rh1tech/frank-archive/minifrank_rm1p2/3D/raspberry pi pico with contacts.step

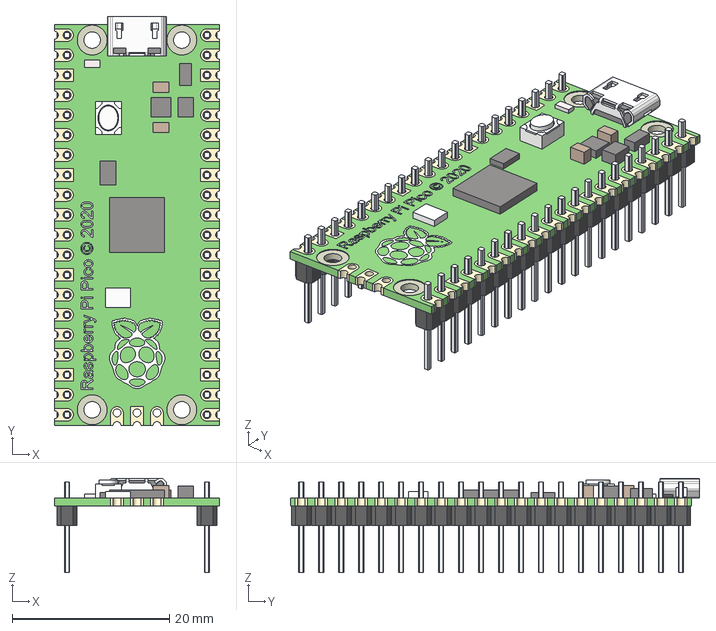
[picture p18: CAD file, 2026-05-06]
minifrank_rm1p2/3D/raspberry pi pico with contacts.step
21.0 x 52.0 x 12.0 mm
ножка x 20
ножка v3(Mirror) x 20
