rh1tech/frank-archive/turbofrank_m1p1/3d/MAX232CSE+.stp

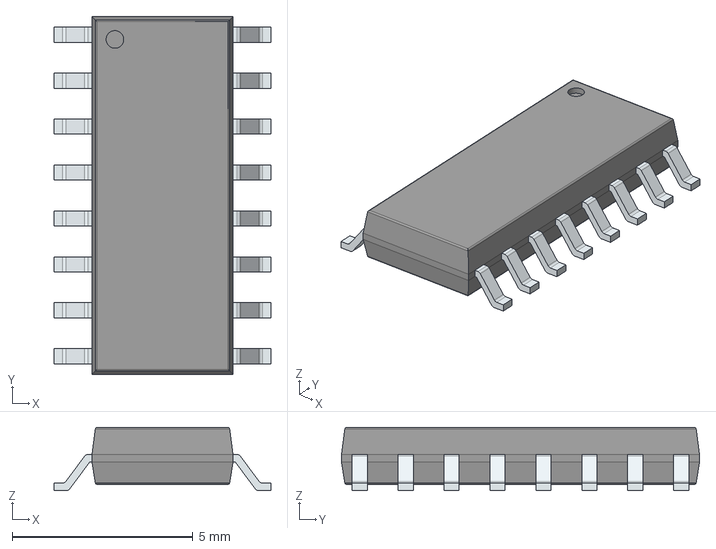
[picture p20: CAD file, 2026-05-06]
turbofrank_m1p1/3d/MAX232CSE+.stp
6.00 x 9.90 x 1.75 mm
PinsArrayLR
