rh1tech/frank-archive/turbofrank_m1p1/case/1_06/bottom.stl

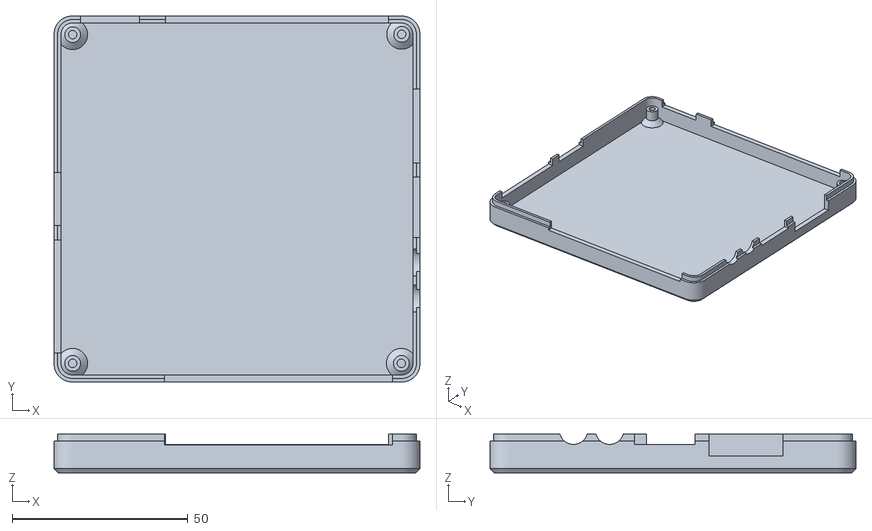
[picture p21: CAD file, 2026-05-07]
turbofrank_m1p1/case/1_06/bottom.stl
104.0 x 104.0 x 11.0
