rh1tech/frank-archive/turbofrank_m1p2/3d/USB1035-GF-P-0-B-B.stp

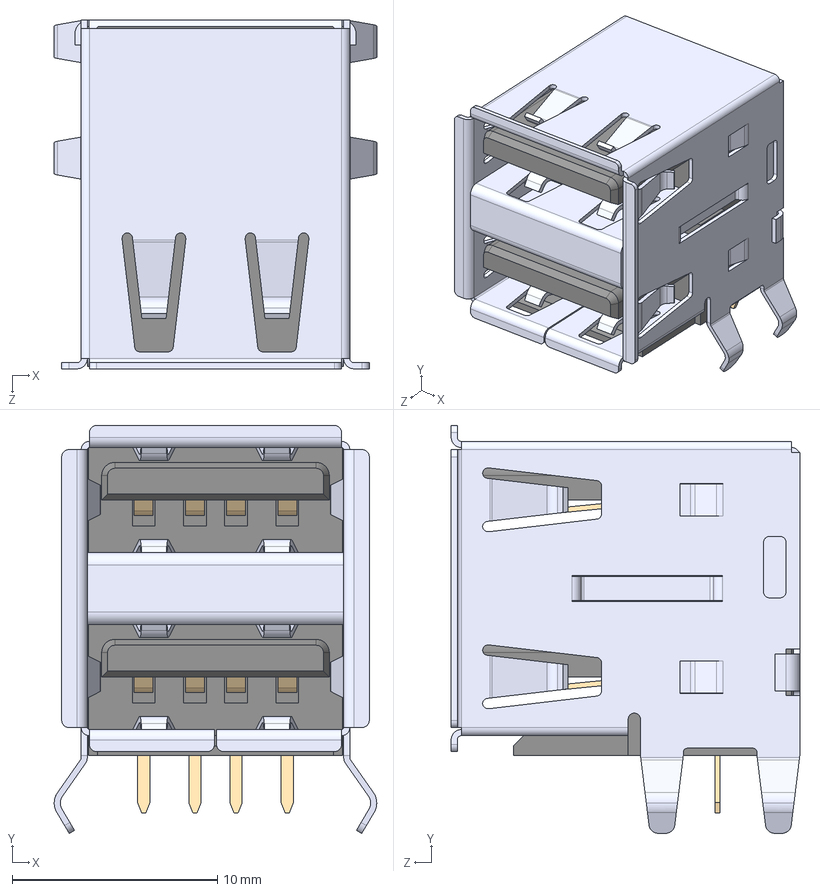
[picture p22: CAD file, 2026-05-06]
turbofrank_m1p2/3d/USB1035-GF-P-0-B-B.stp
15.7 x 19.9 x 17.0 mm
