rh1tech/frank-archive/turbofrank_m1p2/case/1_01/button.stl

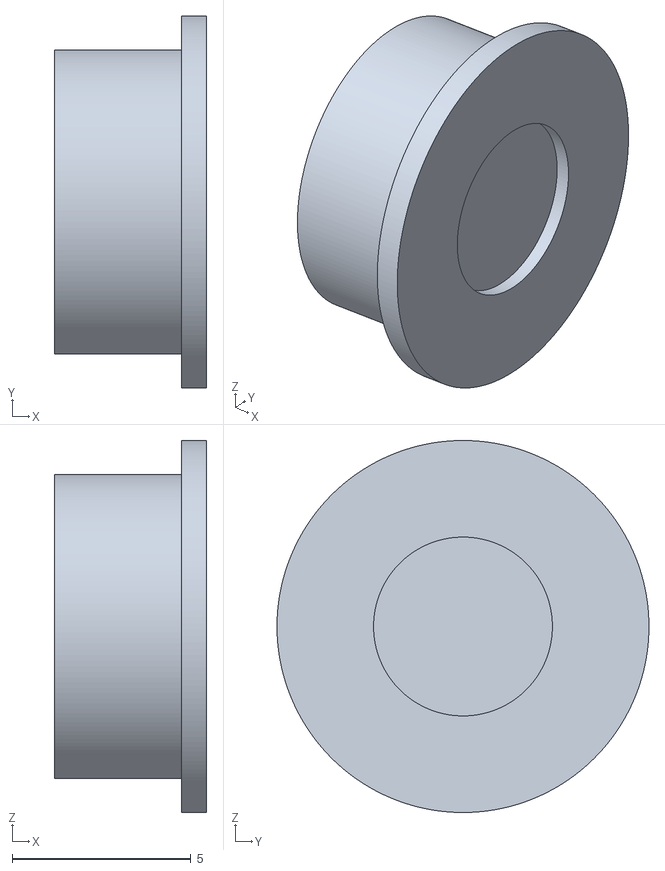
[picture p23: CAD file, 2026-05-07]
turbofrank_m1p2/case/1_01/button.stl
4.25 x 10.4 x 10.4
