rh1tech/frank-archive/usb2ps2/case/REV_1_0/top.stl

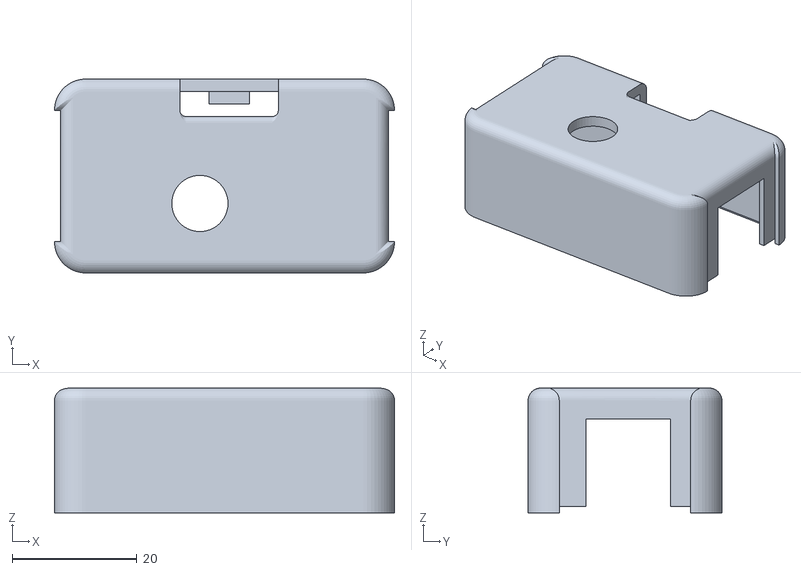
[picture p24: CAD file, 2026-05-07]
usb2ps2/case/REV_1_0/top.stl
54.4 x 31.1 x 20.0
