rh1tech/frank-archive/frank_fastbeta_m1/case/1_04/bottom_vga.stl

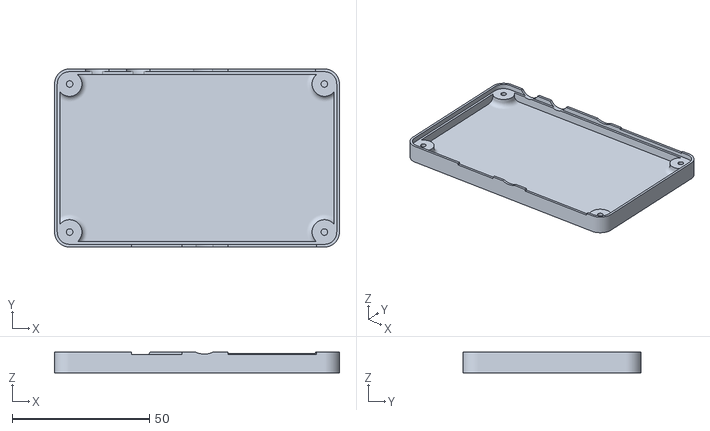
[picture p26: CAD file, 2026-05-07]
frank_fastbeta_m1/case/1_04/bottom_vga.stl
104.0 x 65.0 x 7.50
