rh1tech/frank-archive/frank_m1/3d/DS05-127-2-06BK-SMT-TR.stp

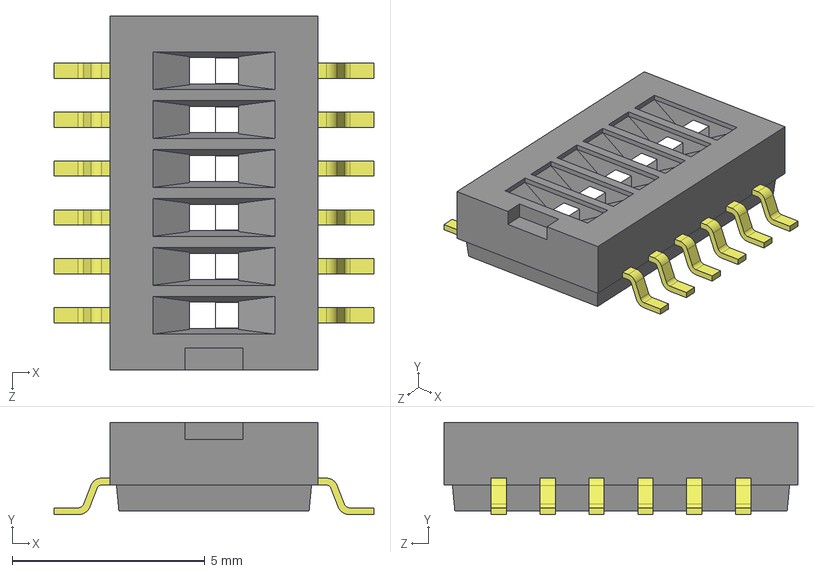
[picture p27: CAD file, 2026-05-06]
frank_m1/3d/DS05-127-2-06BK-SMT-TR.stp
8.30 x 2.40 x 9.19 mm
