rh1tech/frank-archive/hdmi2vga/3d/CUI_DEVICES_RCJ-013.step

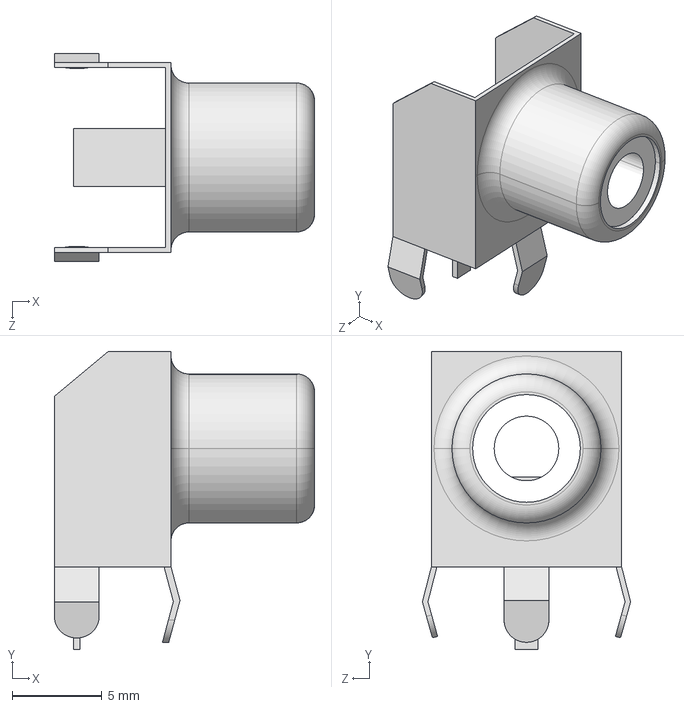
[picture p28: CAD file, 2026-05-06]
hdmi2vga/3d/CUI_DEVICES_RCJ-013.step
14.5 x 16.6 x 11.6 mm
