rh1tech/frank-archive/hdmi2vga/case/2_02/top.stl

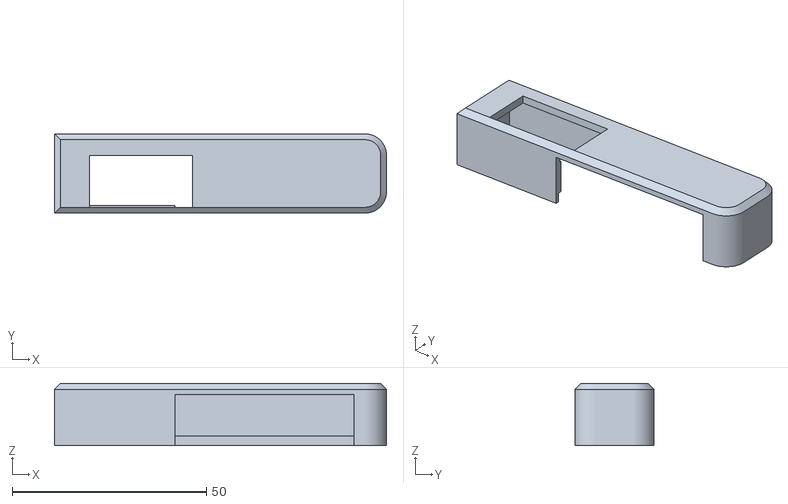
[picture p29: CAD file, 2026-05-07]
hdmi2vga/case/2_02/top.stl
85.5 x 20.4 x 16.0
