rh1tech/frank-archive/hdmi2vga/case/2_03/top.stl

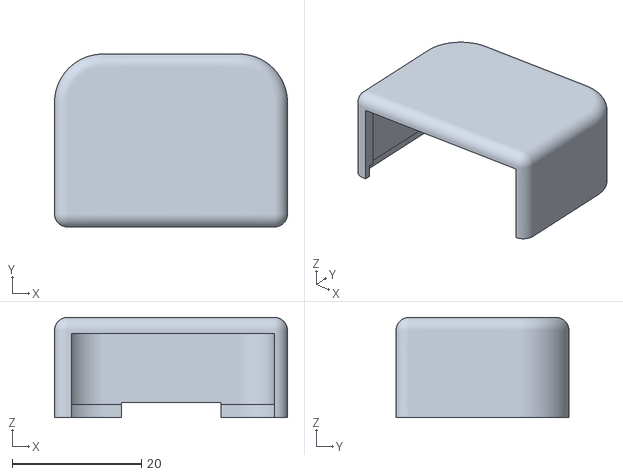
[picture p30: CAD file, 2026-05-07]
hdmi2vga/case/2_03/top.stl
36.0 x 26.8 x 15.5
