rh1tech/frank-archive/microfrank_rm1p2/3D/PICO Clone-Black .step

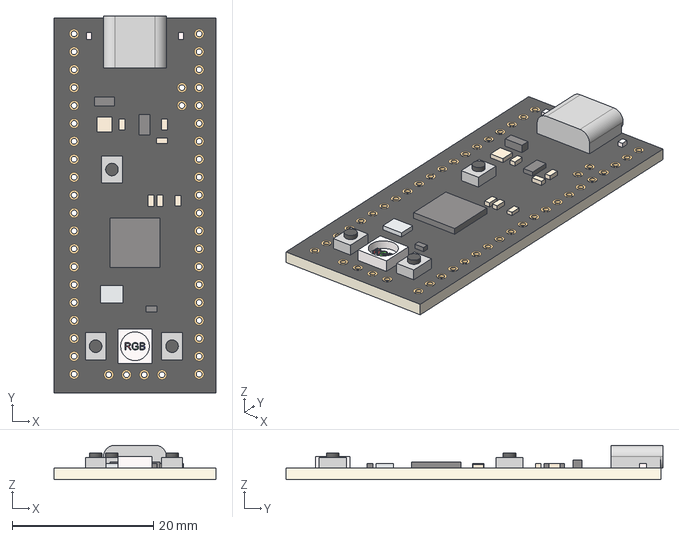
[picture p31: CAD file, 2026-05-06]
microfrank_rm1p2/3D/PICO Clone-Black .step
22.9 x 53.3 x 4.88 mm
