rh1tech/frank-archive/microfrank_rm1p2/CASE/1_01/logo.stl

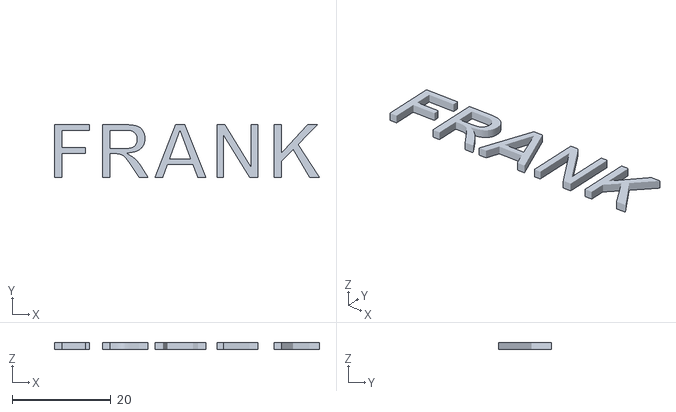
[picture p32: CAD file, 2026-05-06]
microfrank_rm1p2/CASE/1_01/logo.stl
53.6 x 10.7 x 1.50
