rh1tech/frank-archive/microfrank_rm1p2u/3D/DS04-254-2-01BK-SMT.step

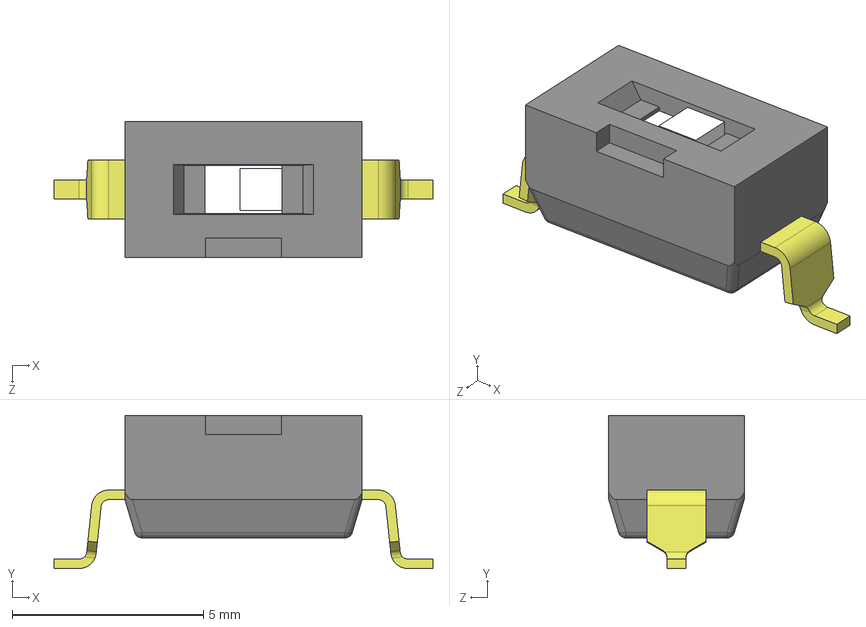
[picture p33: CAD file, 2026-05-06]
microfrank_rm1p2u/3D/DS04-254-2-01BK-SMT.step
9.90 x 4.00 x 3.54 mm
