rh1tech/frank-archive/minifrank_m1/CASE/1_01/cover.stl

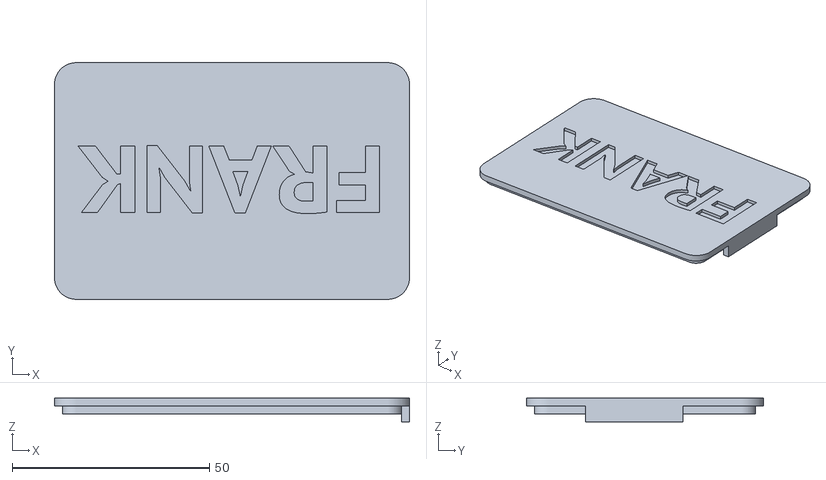
[picture p34: CAD file, 2026-05-06]
minifrank_m1/CASE/1_01/cover.stl
90.0 x 60.0 x 6.00
