rh1tech/frank-archive/minifrank_rm1p2/CASE/1_01/middle.stl

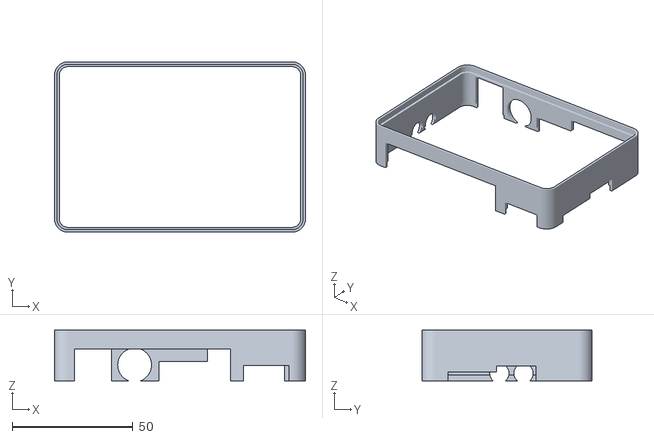
[picture p35: CAD file, 2026-05-06]
minifrank_rm1p2/CASE/1_01/middle.stl
104.0 x 70.5 x 21.0
