rh1tech/frank-archive/minifrank_rm1p2h/3D/Ts-1233_1.5.stp

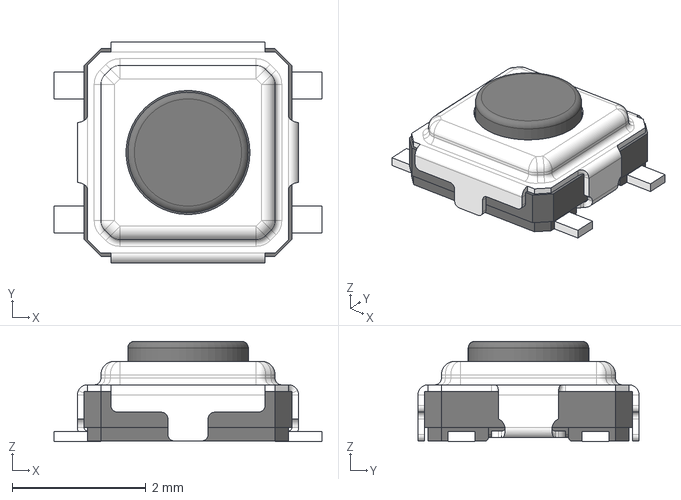
[picture p36: CAD file, 2026-05-06]
minifrank_rm1p2h/3D/Ts-1233_1.5.stp
4.00 x 3.30 x 1.50 mm
