rh1tech/frank-archive/turbofrank_m1p1/3d/FHU-1x9.step

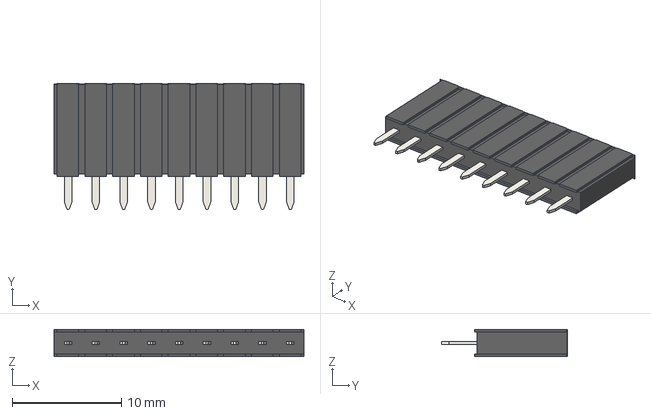
[picture p37: CAD file, 2026-05-06]
turbofrank_m1p1/3d/FHU-1x9.step
22.9 x 11.5 x 2.50 mm
