rh1tech/frank-archive/turbofrank_m1p2/case/1_01/middle.stl

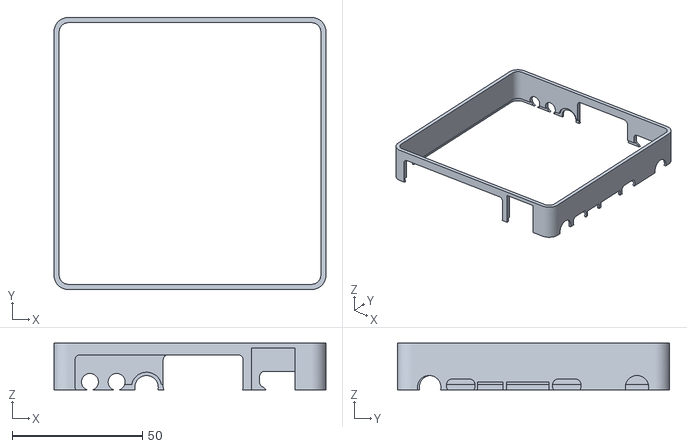
[picture p39: CAD file, 2026-05-07]
turbofrank_m1p2/case/1_01/middle.stl
104.5 x 104.5 x 18.0
