rh1tech/frank-archive/usb2ps2/3d/Mini-DIN-6P.step

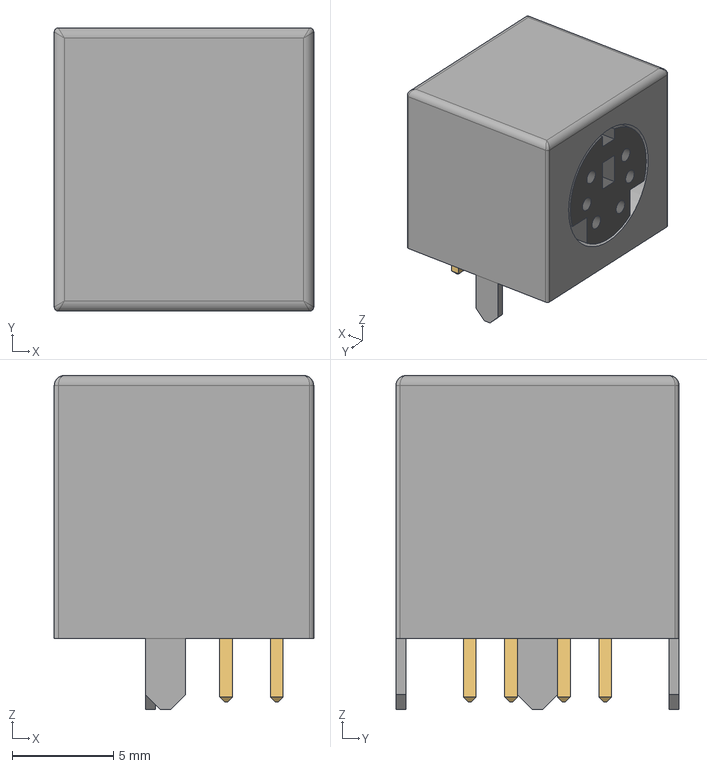
[picture p40: CAD file, 2026-05-06]
usb2ps2/3d/Mini-DIN-6P.step
12.8 x 14.0 x 16.5 mm
