rh1tech/frank-archive/usb2ps2/case/REV_1_0/bottom.stl

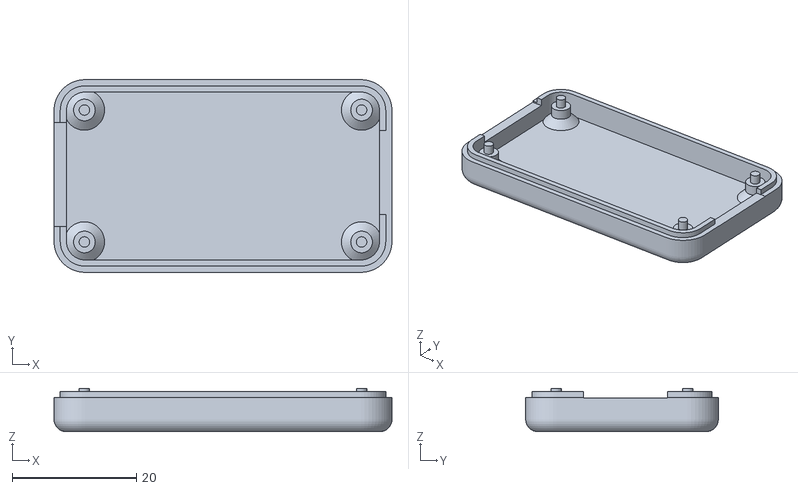
[picture p41: CAD file, 2026-05-07]
usb2ps2/case/REV_1_0/bottom.stl
54.4 x 31.1 x 7.00
