rh1tech/frank-archive/frank_m1/3d/CD4069UBM.stp

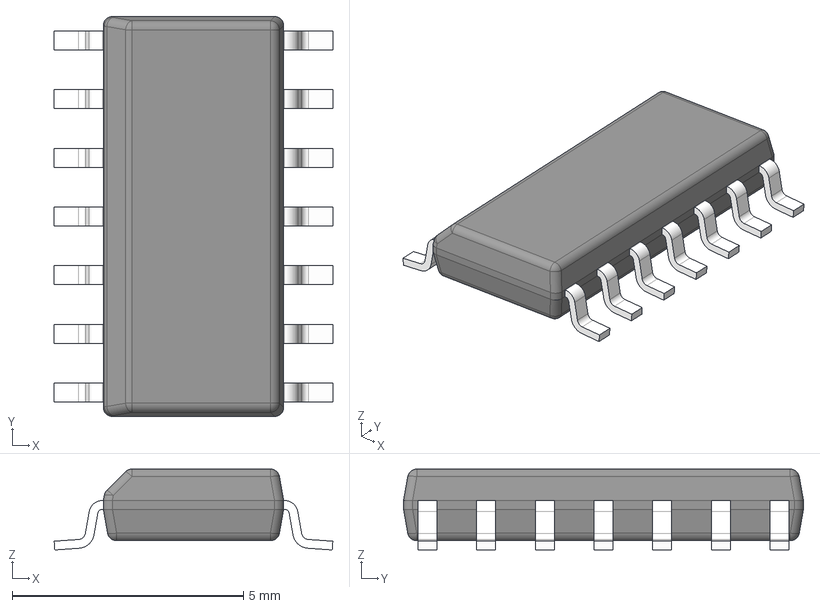
[picture p42: CAD file, 2026-05-06]
frank_m1/3d/CD4069UBM.stp
6.03 x 8.65 x 1.75 mm
BODY-SO
LEAD-SO x 14
PIN1-ID
