rh1tech/frank-archive/frank_rm1p2/3D/W25Q128JVSIQ.stp

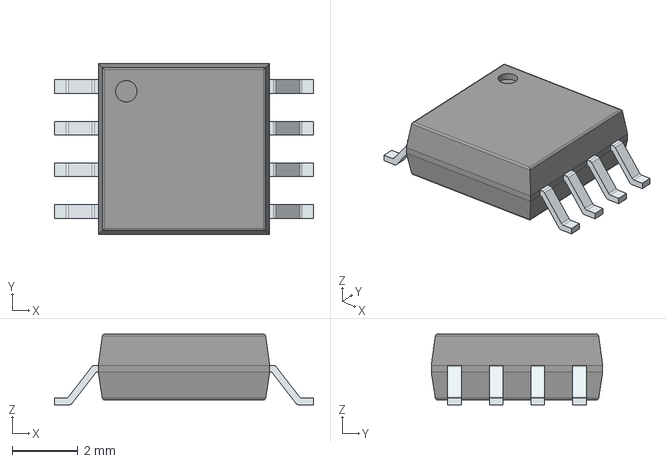
[picture p43: CAD file, 2026-05-06]
frank_rm1p2/3D/W25Q128JVSIQ.stp
7.90 x 5.23 x 2.16 mm
PinsArrayLR
