rh1tech/frank-archive/frank_rm1p2/CASE/1_01/top.stl

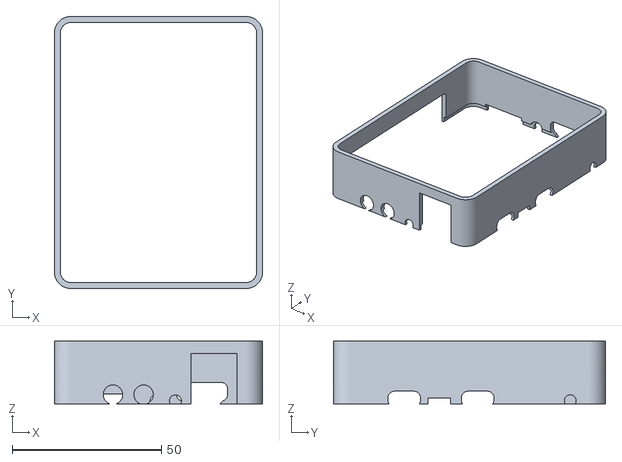
[picture p44: CAD file, 2026-05-06]
frank_rm1p2/CASE/1_01/top.stl
69.7 x 91.0 x 21.0
