rh1tech/frank-archive/microfrank_rm1p2/CASE/1_01/bottom.stl

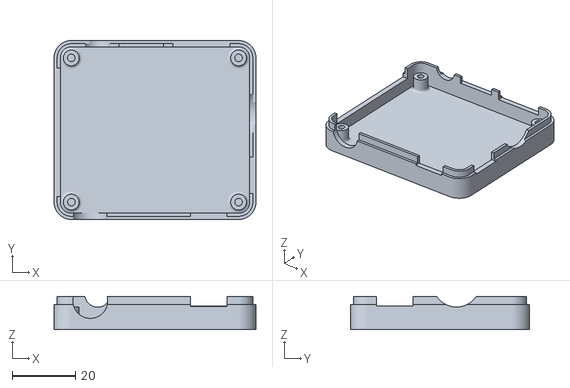
[picture p45: CAD file, 2026-05-06]
microfrank_rm1p2/CASE/1_01/bottom.stl
63.8 x 56.5 x 10.5
