rh1tech/frank-archive/minifrank_m1/CASE/1_01/text.stl

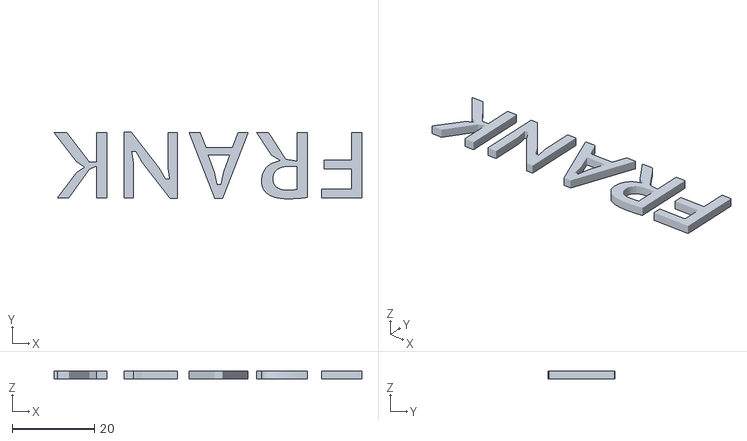
[picture p46: CAD file, 2026-05-06]
minifrank_m1/CASE/1_01/text.stl
74.9 x 16.2 x 2.00
