rh1tech/frank-archive/minifrank_rm1p2h/3D/QFN-48_7x7.step

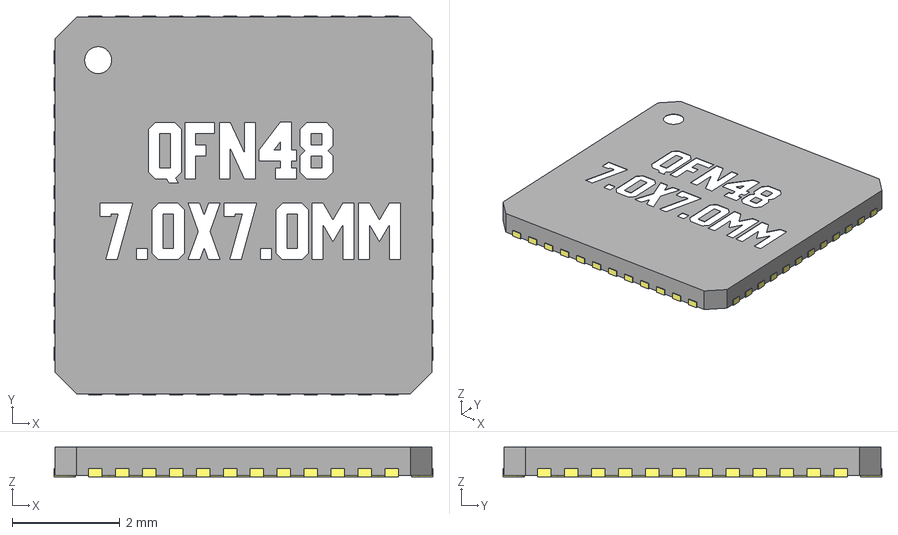
[picture p48: CAD file, 2026-05-06]
minifrank_rm1p2h/3D/QFN-48_7x7.step
7.04 x 7.04 x 0.55 mm
TxT
