rh1tech/frank-archive/tinyfrank_rm1p1/3D/SJ1-3535NG.stp

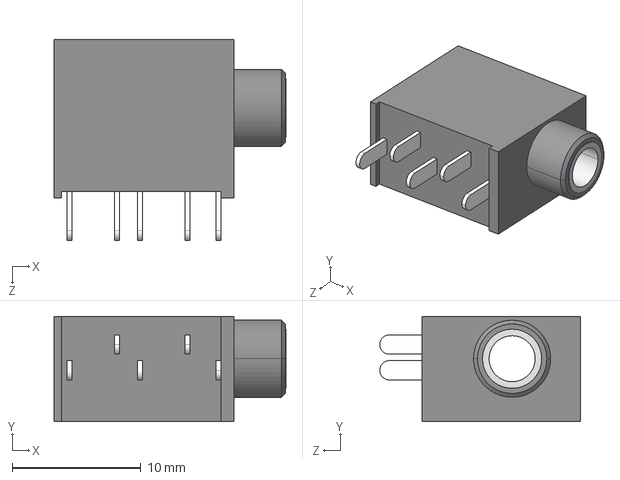
[picture p49: CAD file, 2026-05-06]
tinyfrank_rm1p1/3D/SJ1-3535NG.stp
18.1 x 8.20 x 15.6 mm
