rh1tech/frank-archive/turbofrank_m1p1/3d/PJ320D.STEP

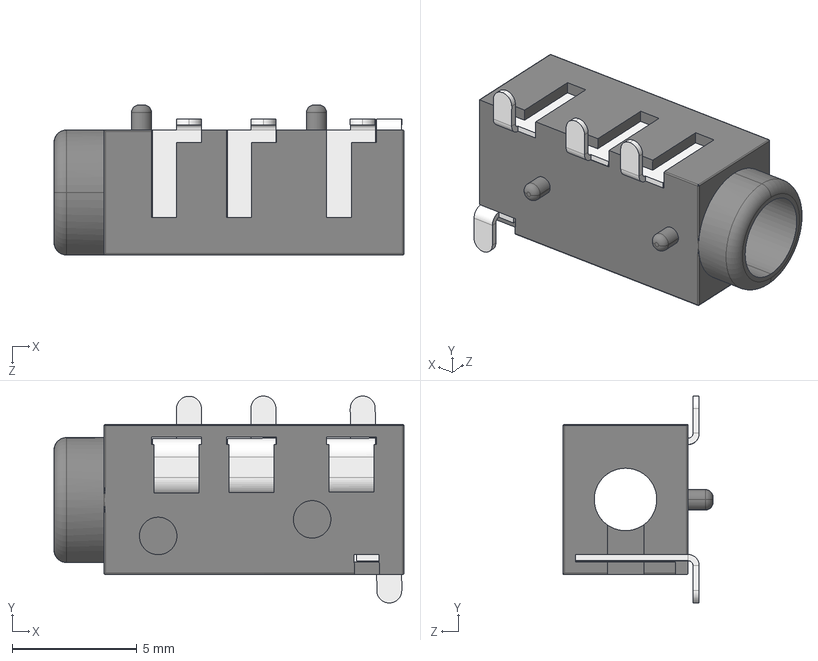
[picture p50: CAD file, 2026-05-06]
turbofrank_m1p1/3d/PJ320D.STEP
14.0 x 8.28 x 6.00 mm
PJ320A
PJ320D-Pin x 3
PJ320D-Pin-B
