rh1tech/frank-archive/turbofrank_m1p2/3d/LQH2MCN100K02L.step

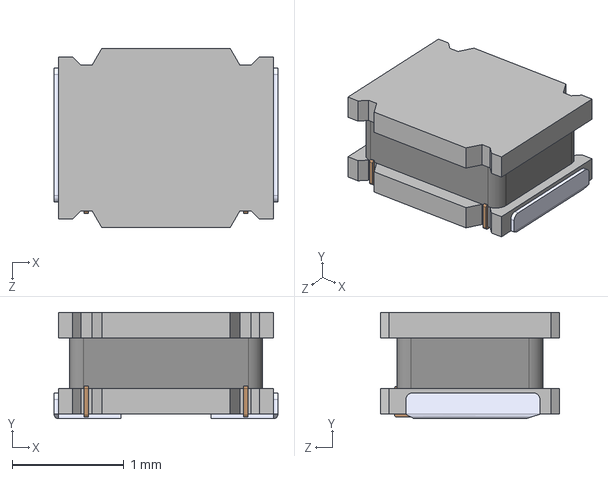
[picture p51: CAD file, 2026-05-06]
turbofrank_m1p2/3d/LQH2MCN100K02L.step
2.00 x 0.95 x 1.60 mm
