rh1tech/frank-archive/turbofrank_m1p2/case/1_01/bottom.stl

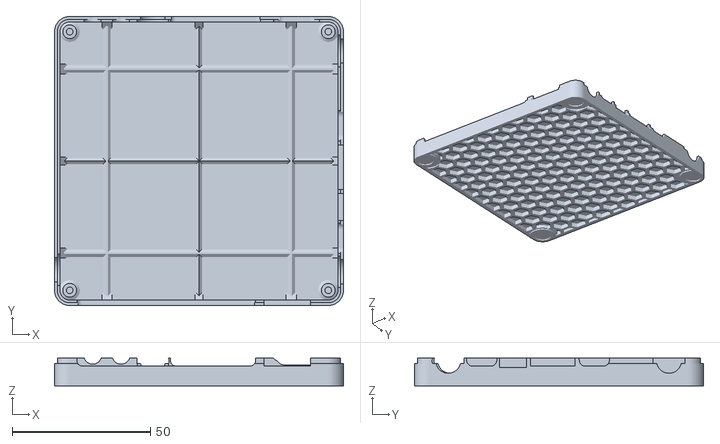
[picture p52: CAD file, 2026-05-07]
turbofrank_m1p2/case/1_01/bottom.stl
104.5 x 104.5 x 10.0
