rh1tech/frank-archive/frank_fastbeta_m1/case/1_04/body_hdmi.stl

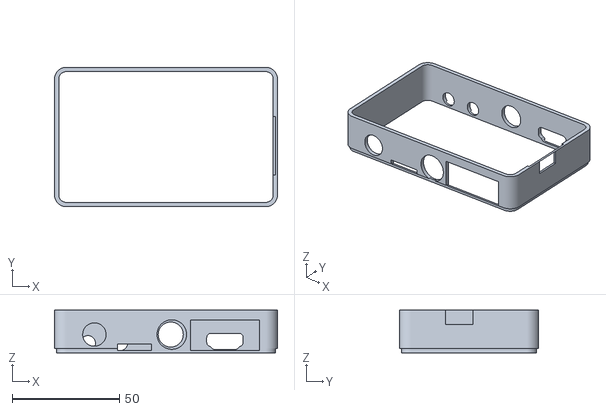
[picture p53: CAD file, 2026-05-07]
frank_fastbeta_m1/case/1_04/body_hdmi.stl
104.0 x 65.0 x 20.0
