rh1tech/frank-archive/frank_m1/3d/CDRH104RNP-150NC.stp

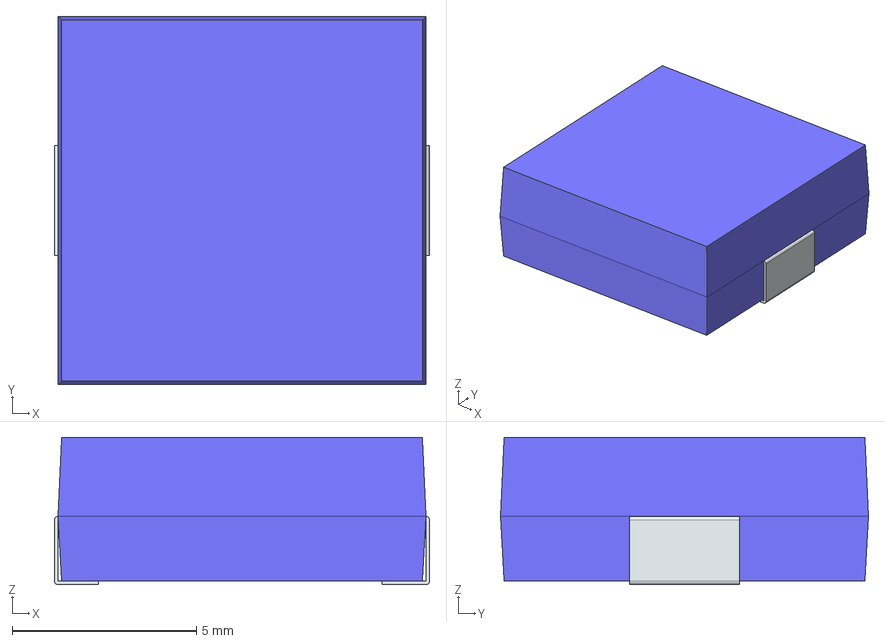
[picture p54: CAD file, 2026-05-06]
frank_m1/3d/CDRH104RNP-150NC.stp
10.2 x 10.0 x 4.00 mm
FilletPin1
FilletPin2
