rh1tech/frank-archive/microfrank_rm1p2/CASE/1_01/top.stl

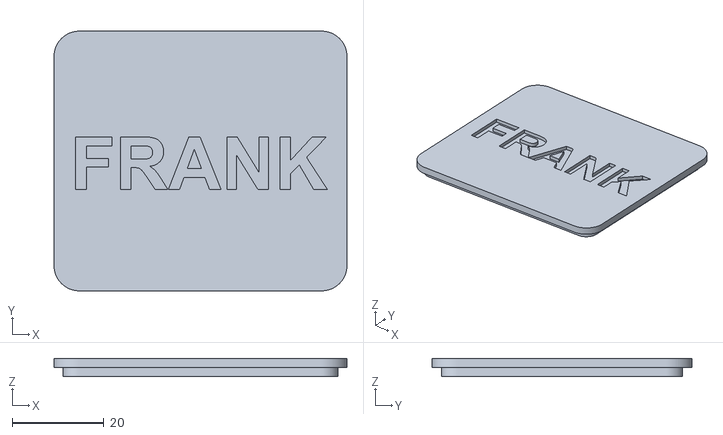
[picture p55: CAD file, 2026-05-06]
microfrank_rm1p2/CASE/1_01/top.stl
63.8 x 56.5 x 4.00
