rh1tech/frank-archive/minifrank_m1/3D/DSUB-15-HD_Male_Horizontal_P2.29x1.98mm_EdgePinOffset3.03mm_Housed_MountingHolesOffset4.94mm.step

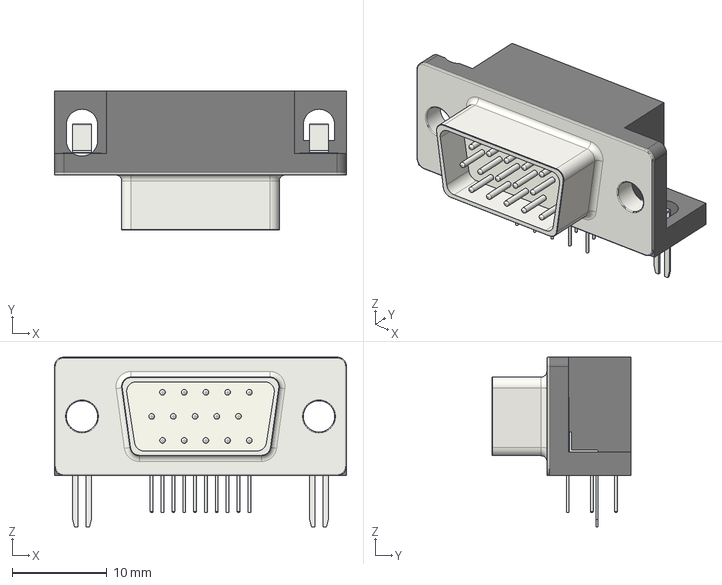
[picture p56: CAD file, 2026-05-06]
minifrank_m1/3D/DSUB-15-HD_Male_Horizontal_P2.29x1.98mm_EdgePinOffset3.03mm_Housed_MountingHolesOffset4.94mm.step
30.8 x 14.7 x 17.9 mm
