rh1tech/frank-archive/minifrank_m1/CASE/1_01/bottom.stl

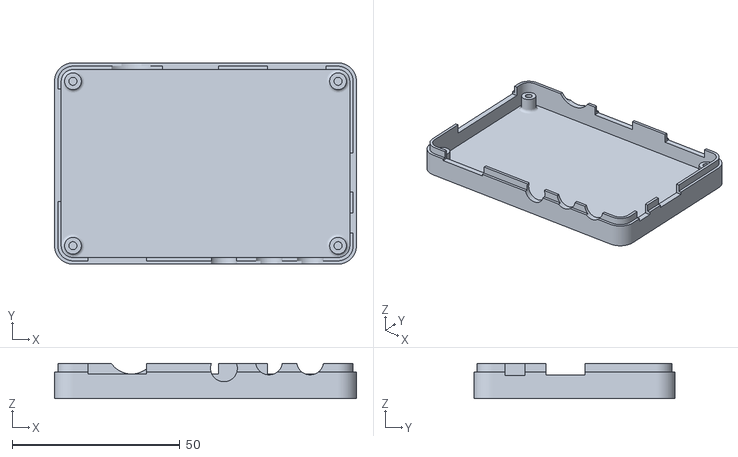
[picture p57: CAD file, 2026-05-06]
minifrank_m1/CASE/1_01/bottom.stl
90.0 x 60.0 x 10.5
