rh1tech/frank-archive/frank_fastbeta_m1/3d/MP1584EN-LF-Z.stp

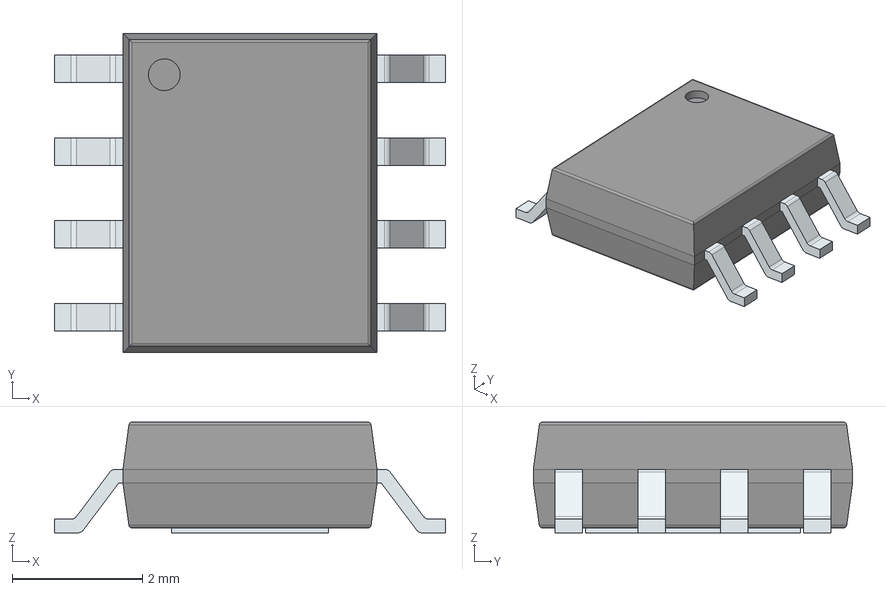
[picture p60: CAD file, 2026-05-06]
frank_fastbeta_m1/3d/MP1584EN-LF-Z.stp
6.00 x 4.90 x 1.70 mm
PinsArrayLR
ThermalPad
