rh1tech/frank-archive/frank_fastbeta_m1/case/1_04/cover.stl

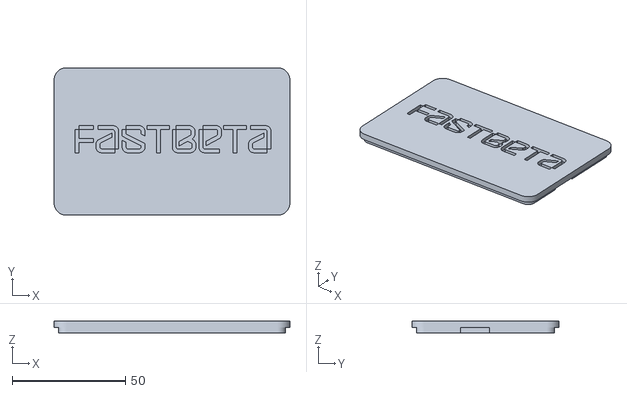
[picture p61: CAD file, 2026-05-07]
frank_fastbeta_m1/case/1_04/cover.stl
104.0 x 65.0 x 5.50
