rh1tech/frank-archive/turbofrank_m1p2/3d/TS3USB221RSER.stp

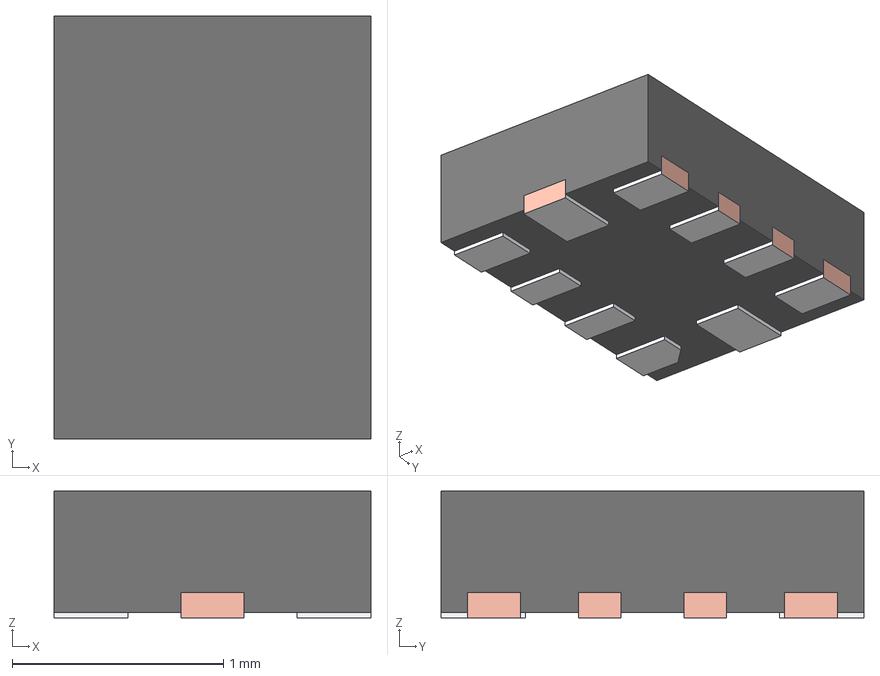
[picture p62: CAD file, 2026-05-06]
turbofrank_m1p2/3d/TS3USB221RSER.stp
1.50 x 2.00 x 0.6 mm
FRAME-RSE0010A
BODY-QFN
PIN1-ID
