rh1tech/frank-archive/frank_fastbeta_m1/3d/DC-005-5A-2.0.step

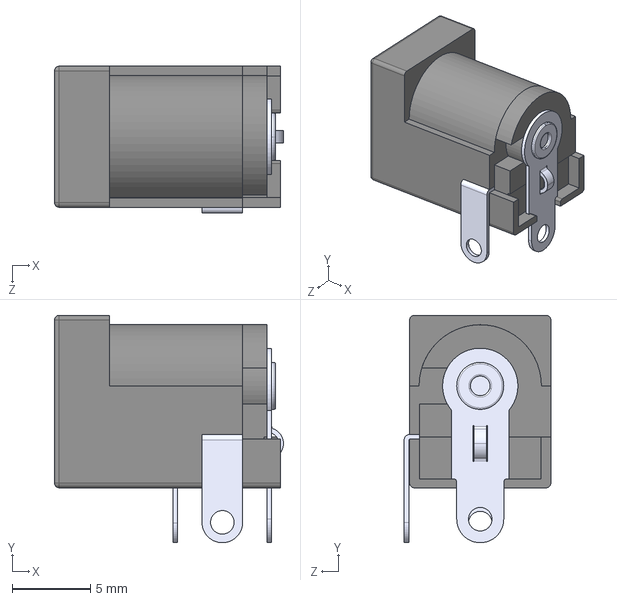
[picture p63: CAD file, 2026-05-06]
frank_fastbeta_m1/3d/DC-005-5A-2.0.step
14.6 x 14.5 x 9.35 mm
