rh1tech/frank-archive/minifrank_rm1p2h/3D/SN74CBT3257CDR.step

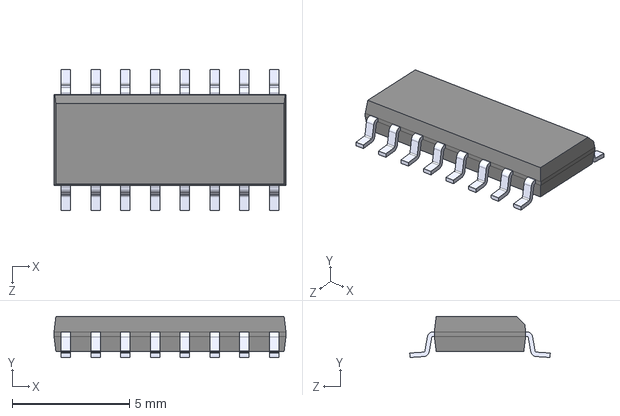
[picture p64: CAD file, 2026-05-06]
minifrank_rm1p2h/3D/SN74CBT3257CDR.step
9.90 x 1.75 x 6.00 mm
