rh1tech/frank-archive/tinyfrank_rm1p1/3D/W25Q32RVZPJQ.stp

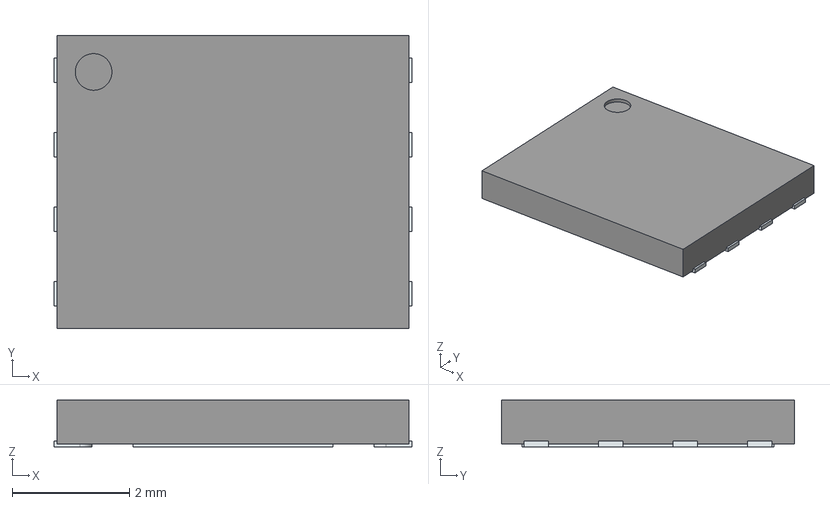
[picture p65: CAD file, 2026-05-06]
tinyfrank_rm1p1/3D/W25Q32RVZPJQ.stp
6.10 x 5.00 x 0.8 mm
ThermalPin
PinsArrayLR
