rh1tech/frank-archive/frank_fastbeta_m1/3d/FHU-1x20.step

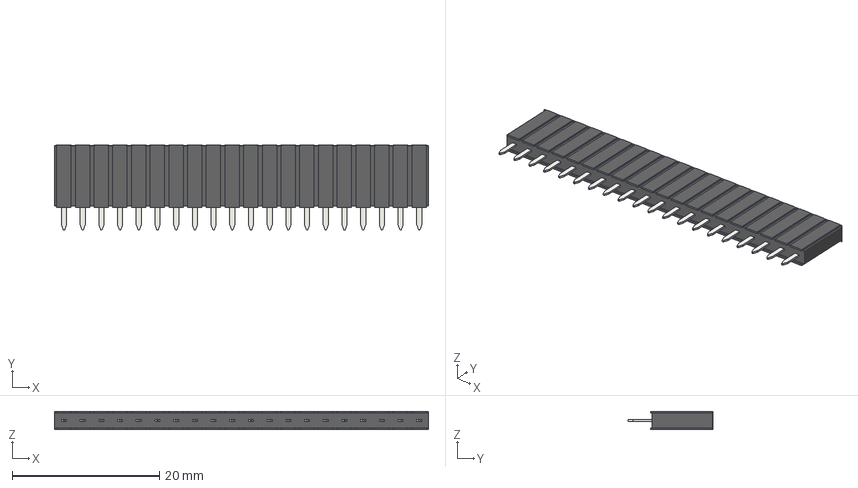
[picture p66: CAD file, 2026-05-06]
frank_fastbeta_m1/3d/FHU-1x20.step
50.8 x 11.5 x 2.50 mm
