rh1tech/frank-archive/turbofrank_m1p1/3d/1x5 Male Pin Header.STEP

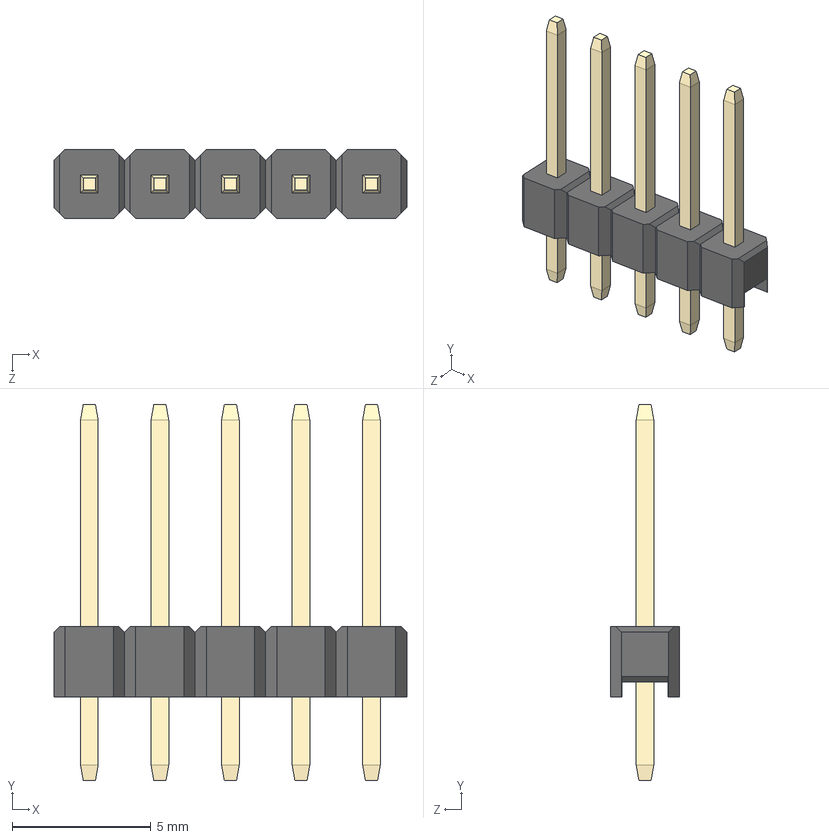
[picture p67: CAD file, 2026-05-06]
turbofrank_m1p1/3d/1x5 Male Pin Header.STEP
12.7 x 13.5 x 2.50 mm
