rh1tech/frank-archive/turbofrank_m1p2/3d/soic-14.stp

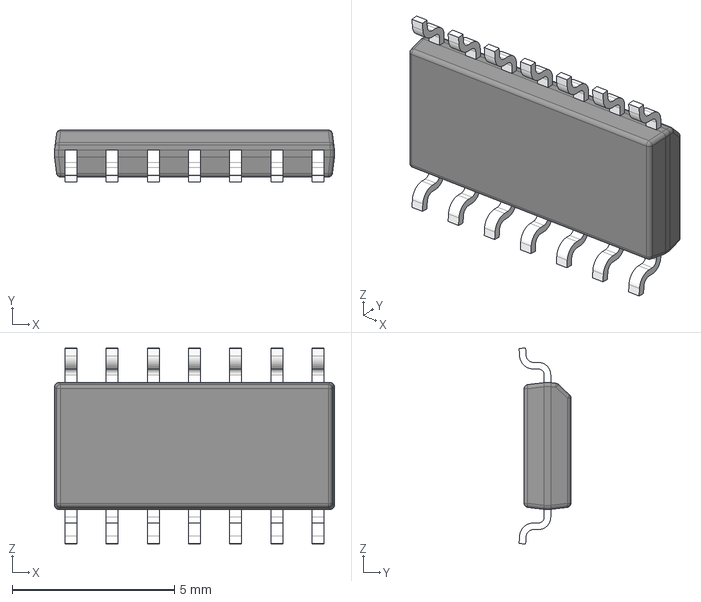
[picture p68: CAD file, 2026-05-06]
turbofrank_m1p2/3d/soic-14.stp
8.64 x 1.60 x 6.05 mm
BODY_M14A_20
LEAD_M14A_46 x 14
