rh1tech/frank-archive/frank_fastbeta_m1/3d/1x20 Male Pin Header.STEP

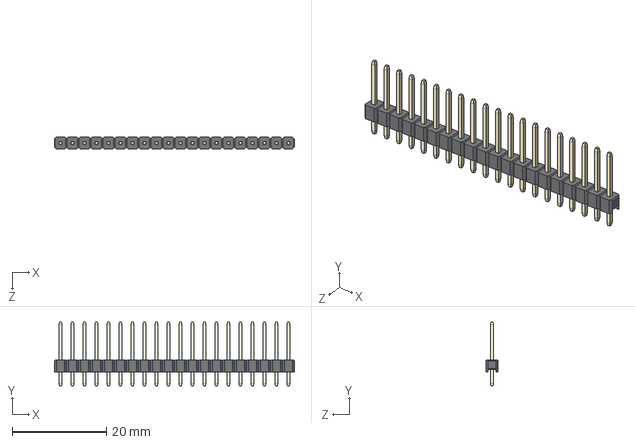
[picture p69: CAD file, 2026-05-06]
frank_fastbeta_m1/3d/1x20 Male Pin Header.STEP
50.8 x 13.5 x 2.50 mm
