rh1tech/frank-archive/frank_fastbeta_m1/3d/CD4069UBE.stp

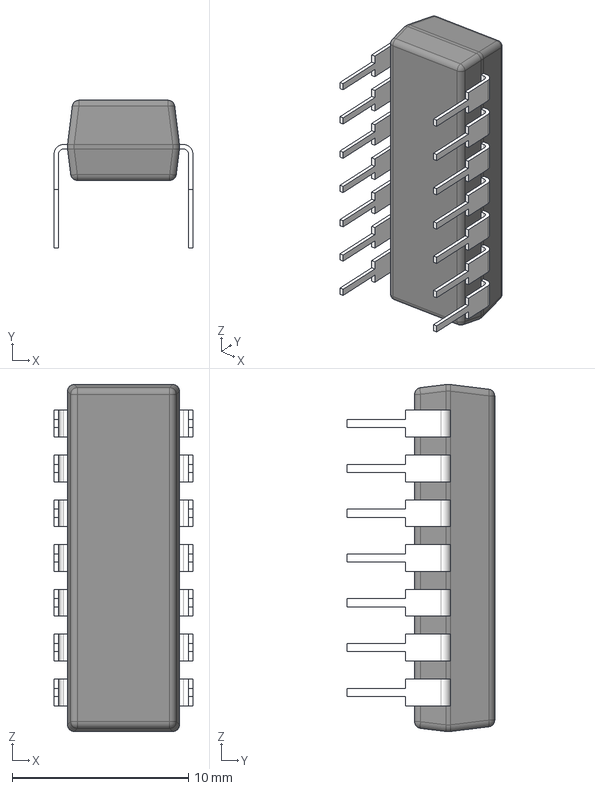
[picture p70: CAD file, 2026-05-06]
frank_fastbeta_m1/3d/CD4069UBE.stp
7.87 x 8.37 x 19.7 mm
BODY_N0014A_AF0
LEAD_N0014A_AF1
LEAD_N0014A x 10
LEAD_N0014A_AF3
LEAD_N0014A_AF0
LEAD_N0014A_AF2
