rh1tech/frank-archive/minifrank_rm1p2h/3D/User Library-QFN48_0_4.STEP

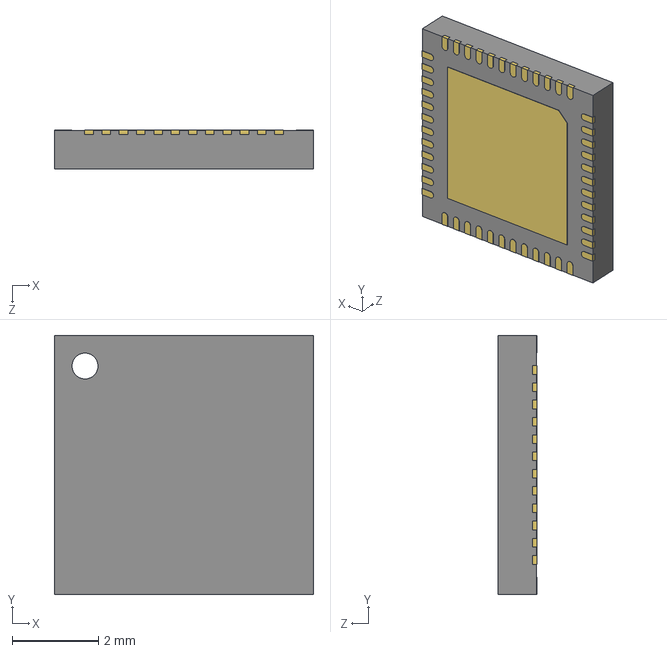
[picture p71: CAD file, 2026-05-06]
minifrank_rm1p2h/3D/User Library-QFN48_0_4.STEP
6.00 x 6.00 x 0.91 mm
