rh1tech/frank-archive/frank_m1/docs/2_05/assembly.pdf

LEFT 5V | TFT
RESET | IO⁰

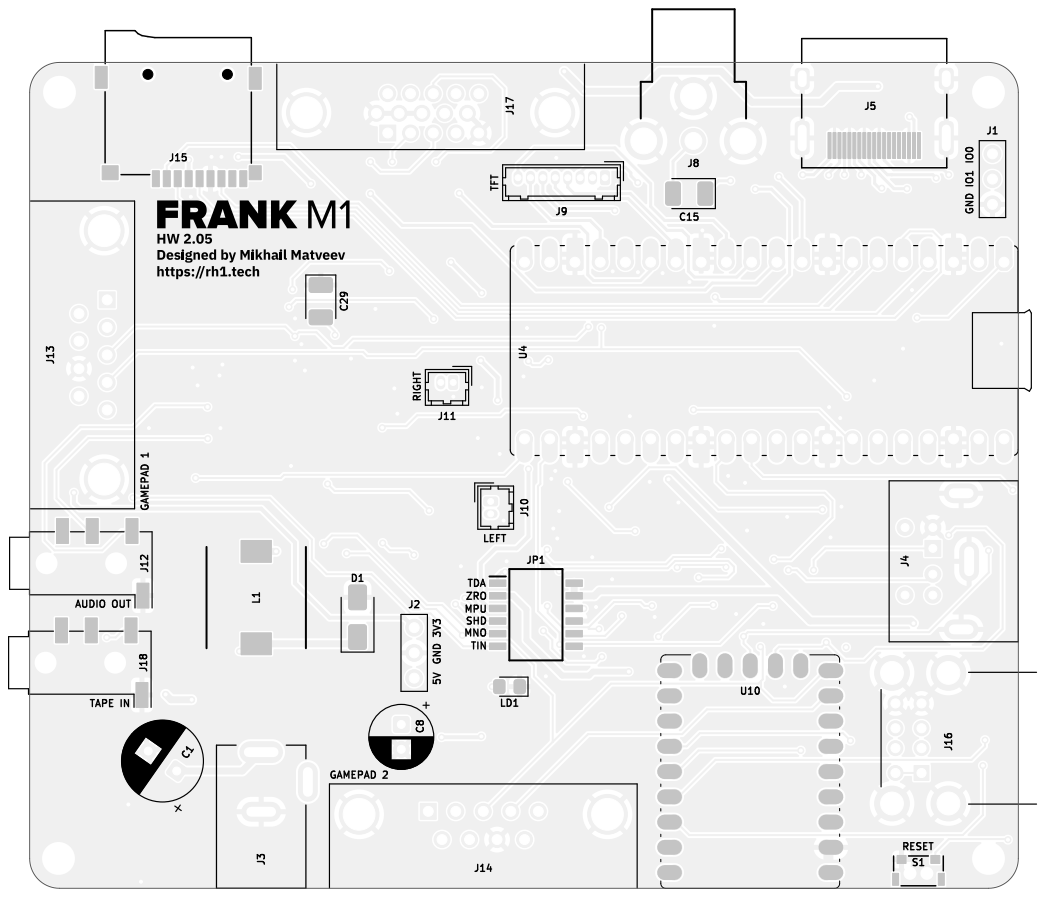
[picture p108: page 1]

1 | 2 | 3 | 4 | 5 | 6

A

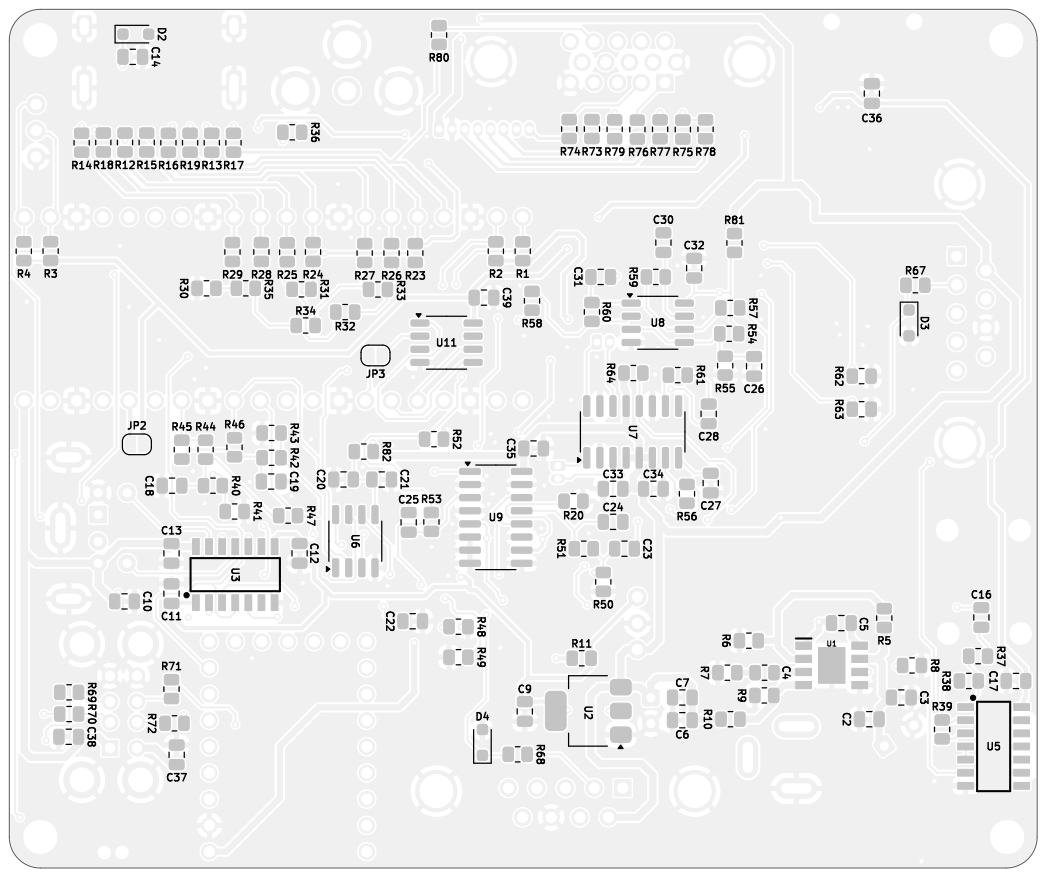
[picture p109: page 2]

https://github.com/xtremespb/frank Black And White BOT - Page 2/4

File: frank_m1.kicad_pcb Sheet: Black And White BOT Mikhail Matveev

1 | 2 | 3 | 4 | 5 | 6 1 | 2 | 3 | 4 | 5 | 6 ABCD | ABCD Date: 2026-01-03 KiCad | E.D.A. 9.0.6 Size: A4 | Rev: 2.05
LEFT 5V | TFT

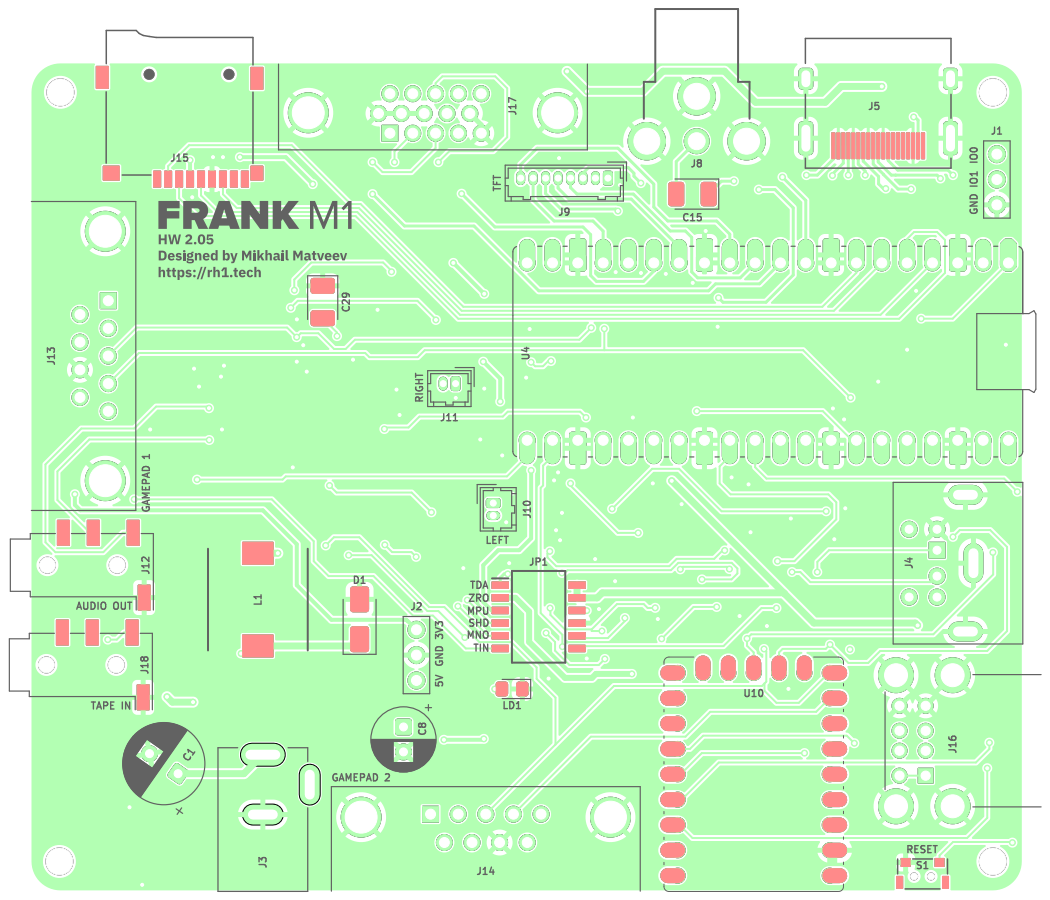
[picture p110: page 3]

1 | 2 | 3 | 4 | 5 | 6

A

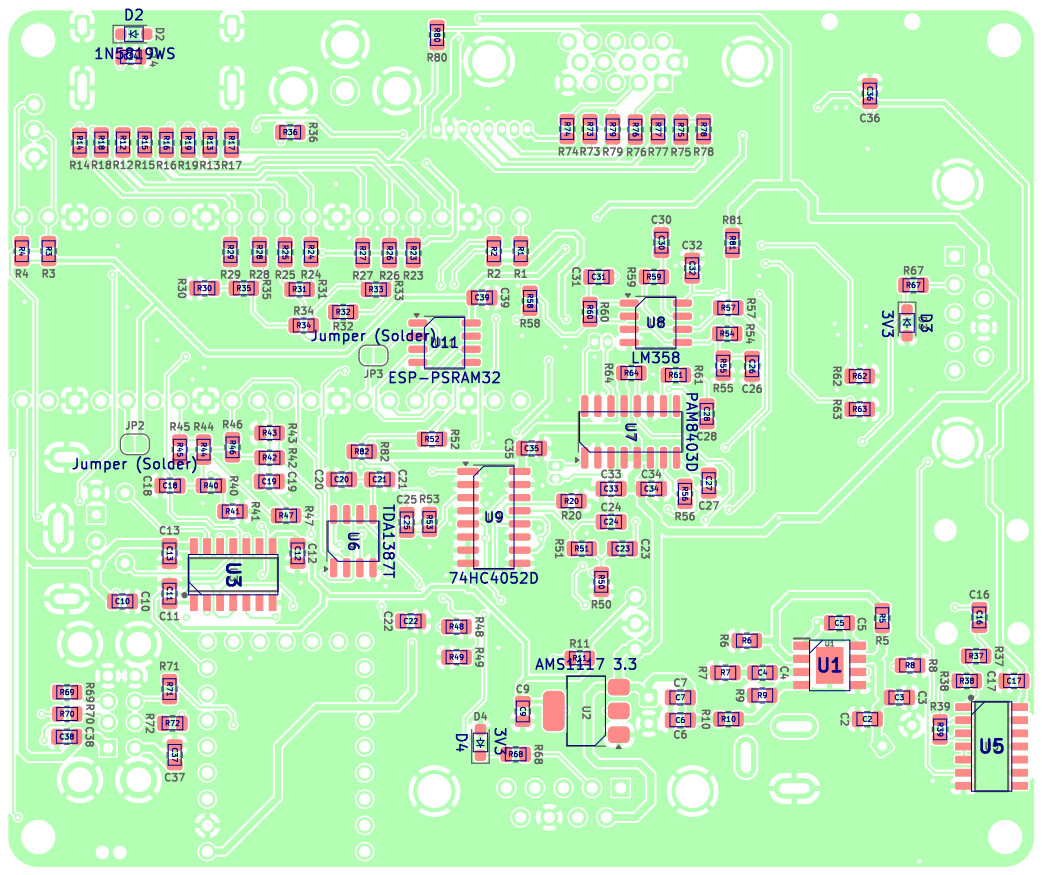
[picture p111: page 4]

https://github.com/xtremespb/frank Colored BOT - Page 4/4

File: frank_m1.kicad_pcb Sheet: Colored BOT Mikhail Matveev
