rh1tech/frank-archive/frank_m1/docs/2_06/assembly.pdf

LEFT 5V | TFT
RESET | IO⁰

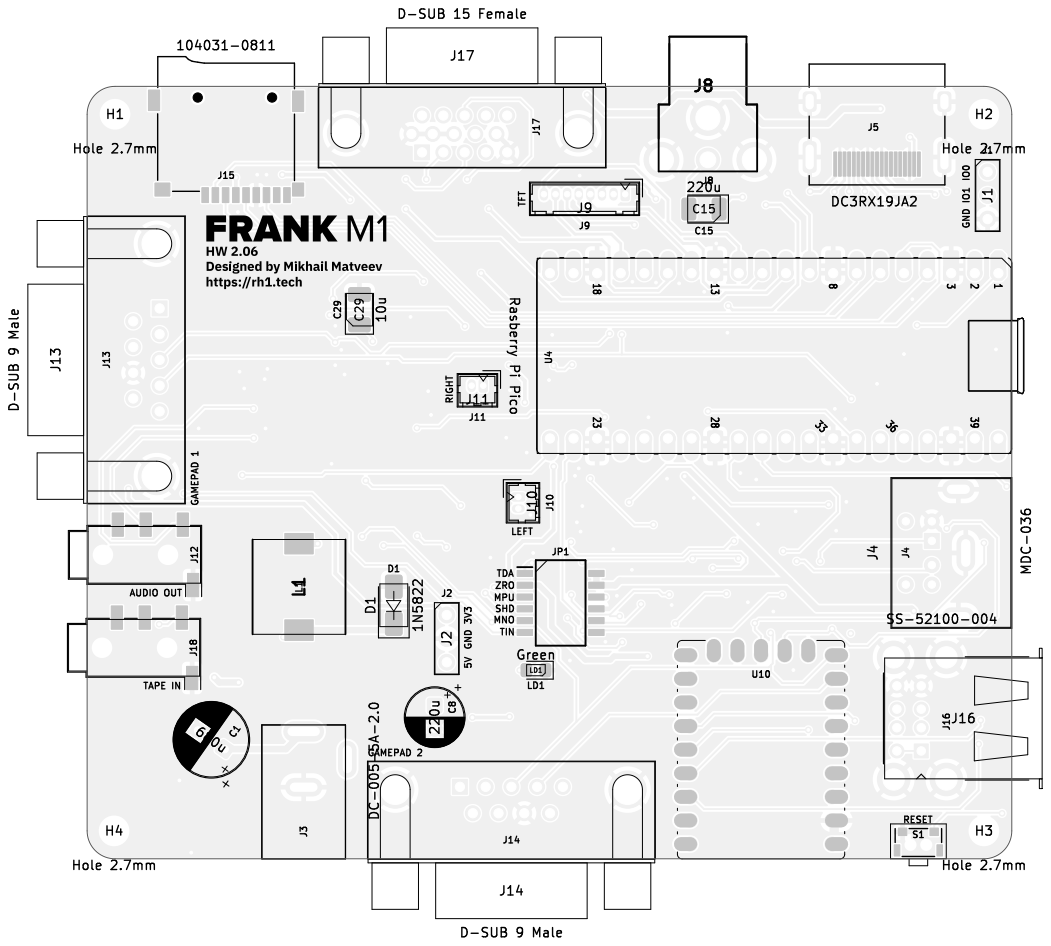
[picture p112: page 1]

1 | 2 | 3 | 4 | 5 | 6

A

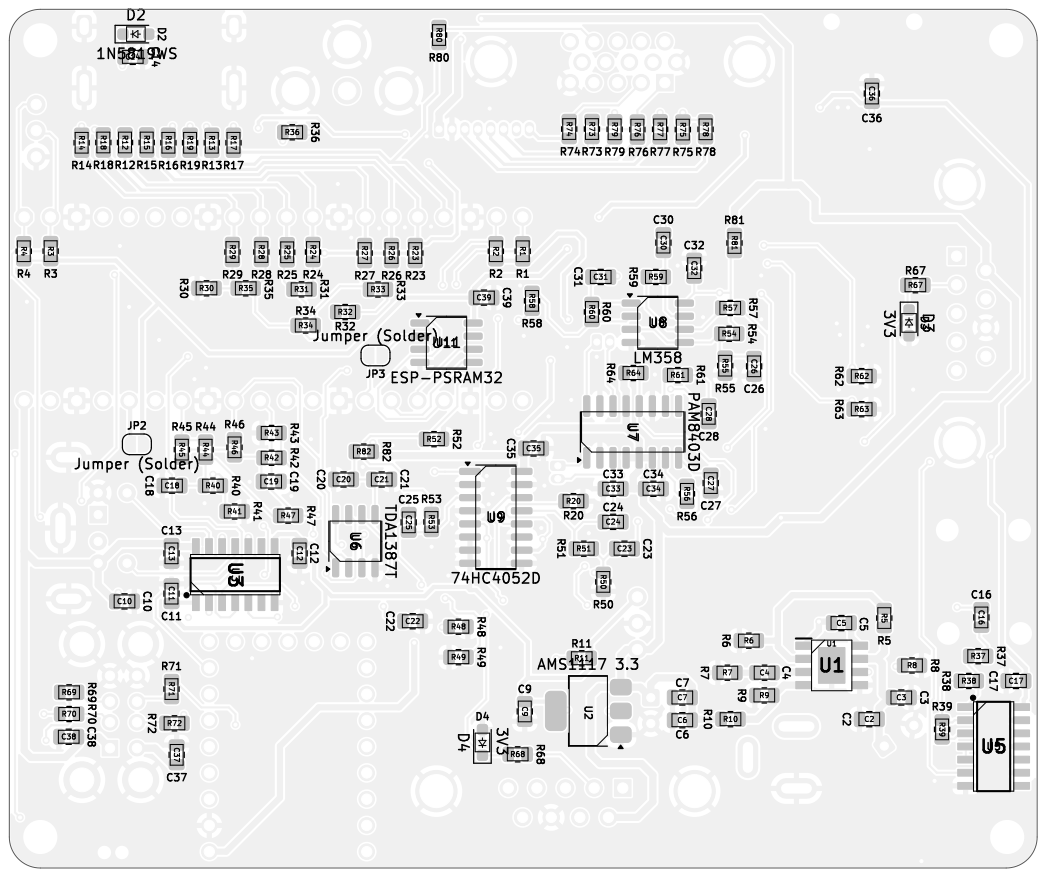
[picture p113: page 2]

https://github.com/xtremespb/frank Black And White BOT - Page 2/2

File: frank_m1.kicad_pcb Sheet: Black And White BOT Mikhail Matveev
