rh1tech/frank-archive/frank_rm1p2/DOCS/1_00/assembly.pdf

J8 | R¹⁸ RN² | C¹ R37 R9 J14 C⁵⁸ | R11 JP¹ 1 | 2 | 3 | 4 | 5 | 6 1 | 2 | 3 | 4 | 5 | 6 ABCD | ABCD Date: 2025-08-12 KiCad E.D.A. 9.0.0 Size: A4 | Rev: 1.00

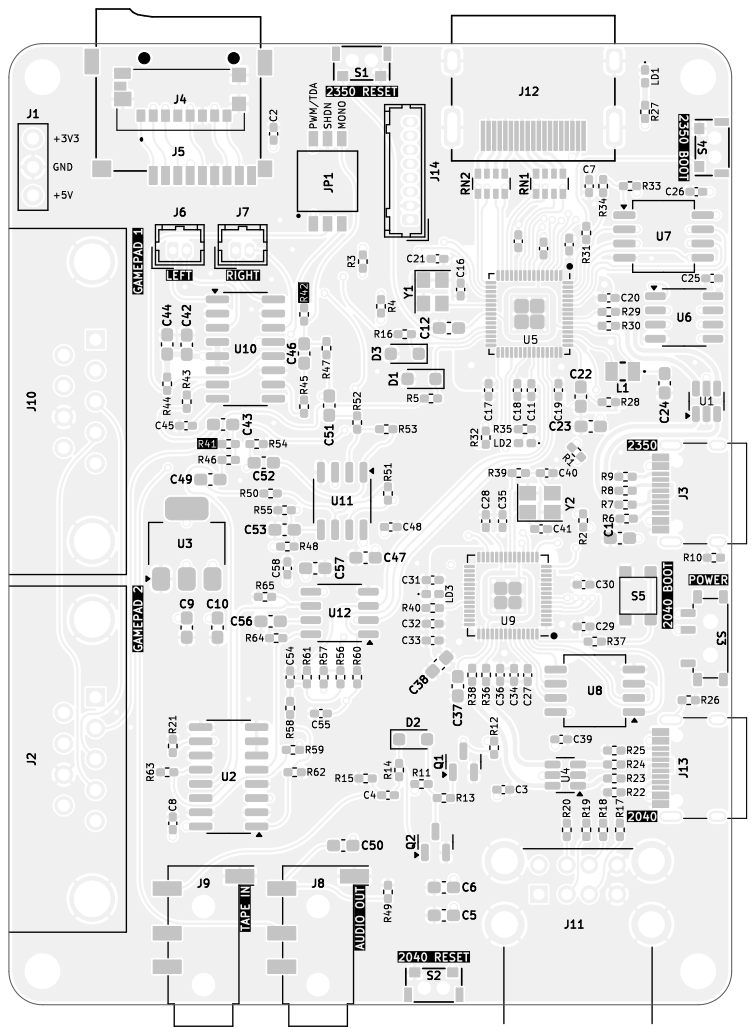
[picture p114: page 1]

PWM/TDA SHDN MONO

https://github.com/xtremespb/frank Black And White TOP - Page 1/4

File: frank_rm1p2.kicad_pcb Sheet: Black And White TOP Mikhail Matveev

JP3 1 | 2 | 3 | 4 | 5 | 6

A

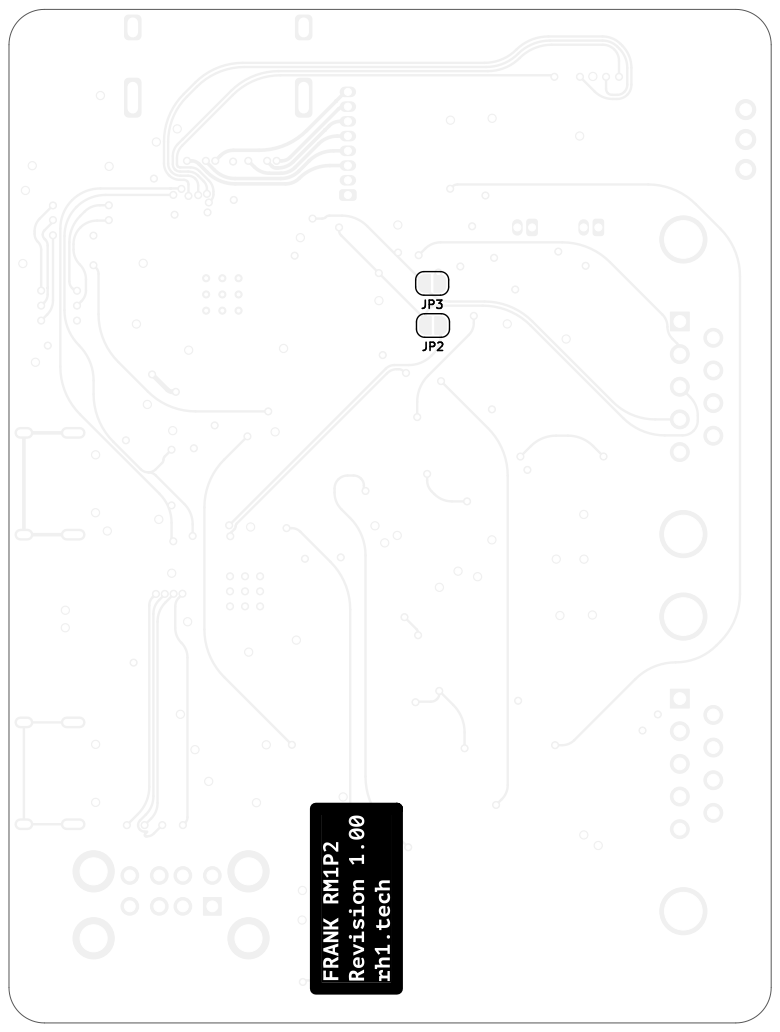
[picture p115: page 2]
D Date: 2025-08-12 KiCad; E.D.A. 9.0.0 Size: A4; Rev: 1.00; File: frank_rm1p2.kicad_pcb Sheet: Black; And; White; BOT Mikhail; Matveev; https://github.com/xtremespb/frank Black; BOT -; Page 2/4

Id: /1 Title: FRANK RM1P2

1 | 2 | 3 | 4 | 5 | 6 1 | 2 | 3 | 4 | 5 | 6 ABCD | ABCD Date: 2025-08-12 KiCad | E.D.A. 9.0.0 Size: A4 | Rev: 1.00
https://github.com/xtremespb/frank Colored | TOP - | Page 3/4 PWM/TDA SHDN MONO

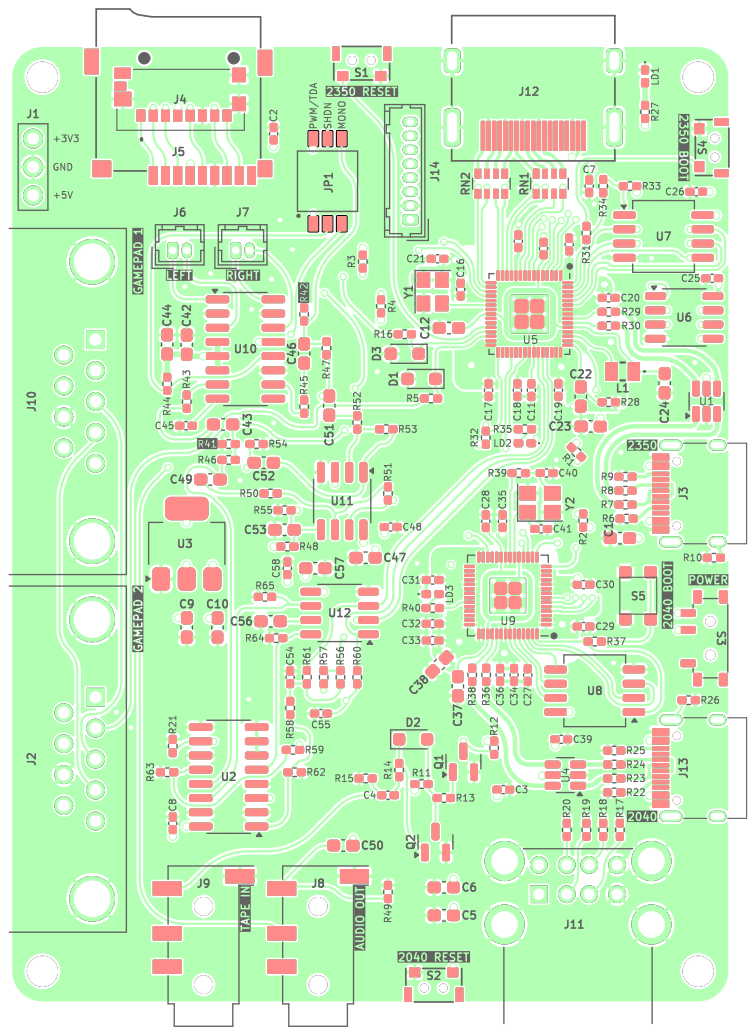
[picture p116: page 3]

JP3 1 | 2 | 3 | 4 | 5 | 6

A

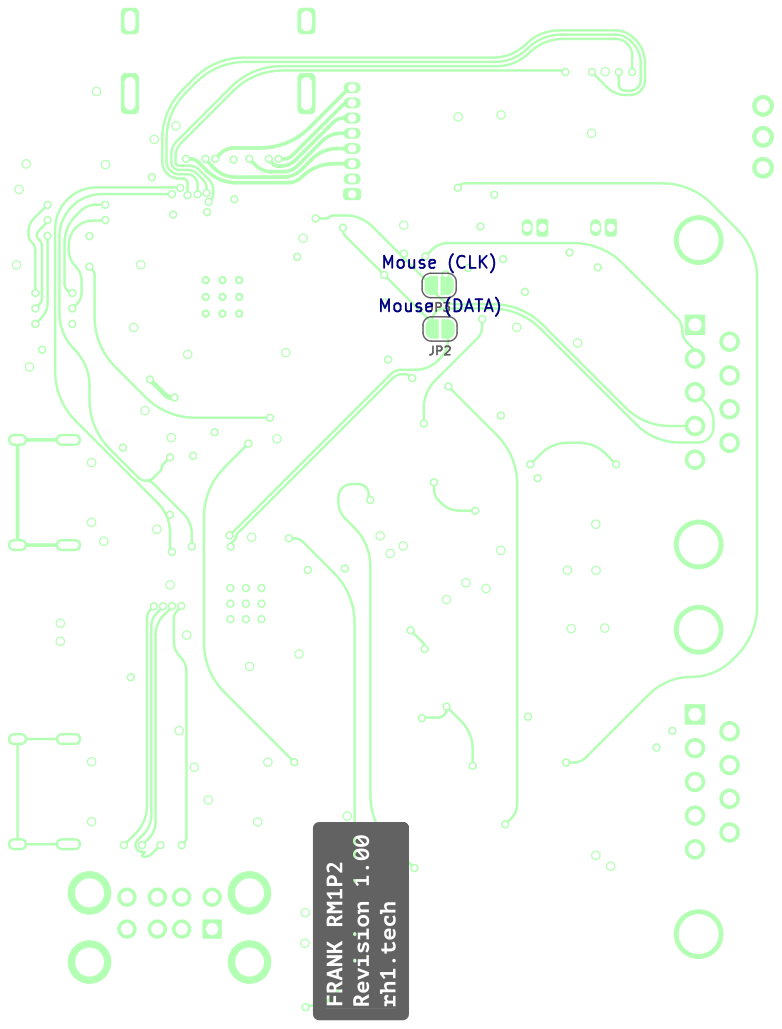
[picture p117: page 4]
D Date: 2025-08-12 KiCad; E.D.A. 9.0.0 Size: A4; Rev: 1.00; File: frank_rm1p2.kicad_pcb Sheet: Colored; BOT Mikhail; Matveev; https://github.com/xtremespb/frank Colored; BOT -; Page 4/4

Mouse (DATA) Mouse (CLK)

Id: /1 Title: FRANK RM1P2
