rh1tech/frank-archive/frank_rm1p2/DOCS/1_01/assembly.pdf

J8 | R¹⁸ RN² | C¹ R37 R9 J14 C⁵⁸ | R11 1 | 2 | 3 | 4 | 5 | 6 1 | 2 | 3 | 4 | 5 | 6 ABCD | ABCD Date: 2025-09-02 KiCad E.D.A. 9.0.4 Size: A4 | Rev: 1.01

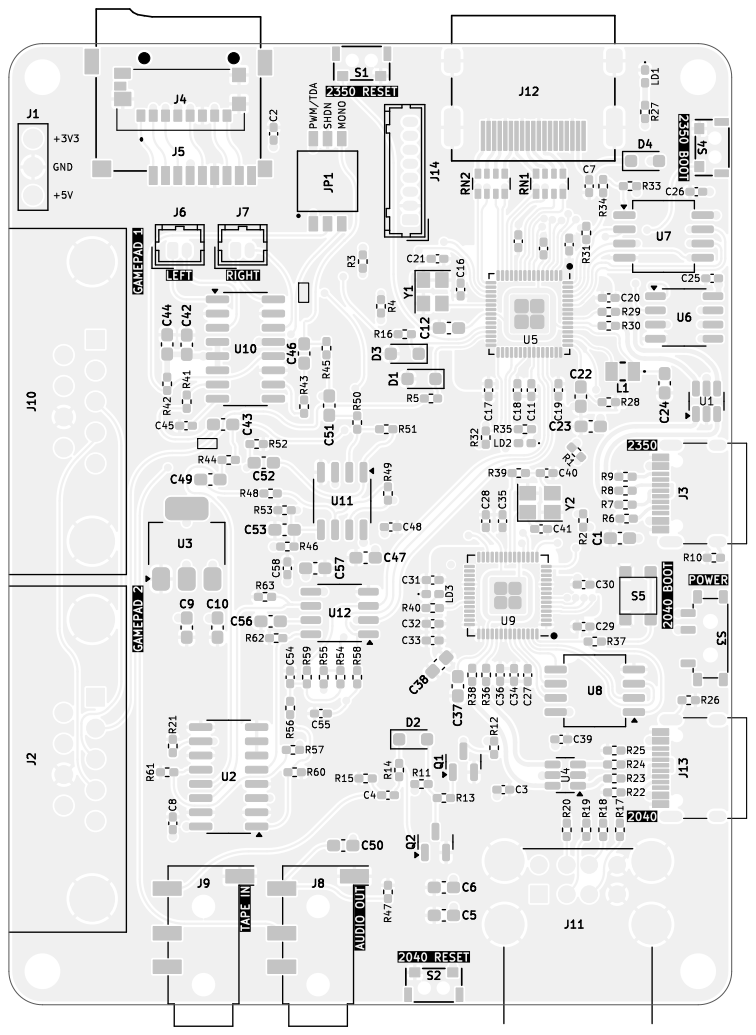
[picture p118: page 1]

https://github.com/xtremespb/frank Black And White TOP - Page 1/4

File: frank_rm1p2.kicad_pcb Sheet: Black And White TOP Mikhail Matveev

JP3 1 | 2 | 3 | 4 | 5 | 6

A

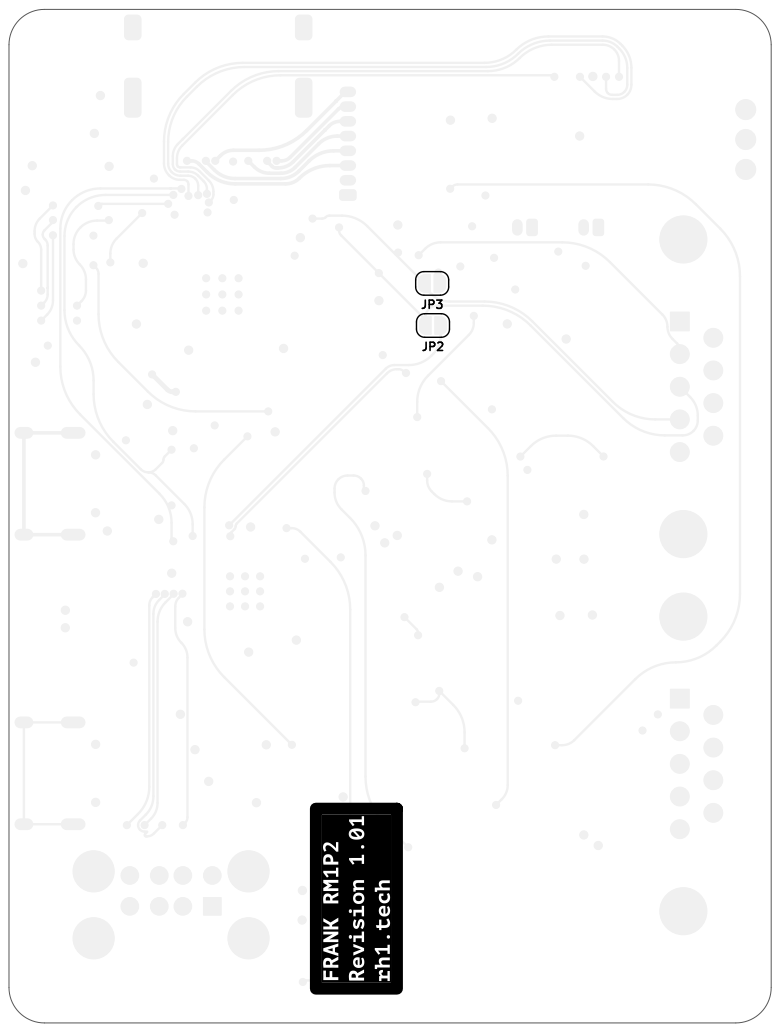
[picture p119: page 2]
D Date: 2025-09-02 KiCad; E.D.A. 9.0.4 Size: A4; Rev: 1.01; File: frank_rm1p2.kicad_pcb Sheet: Black; And; White; BOT Mikhail; Matveev; https://github.com/xtremespb/frank Black; BOT -; Page 2/4

Id: /1 Title: FRANK RM1P2

1 | 2 | 3 | 4 | 5 | 6 1 | 2 | 3 | 4 | 5 | 6 ABCD | ABCD Date: 2025-09-02 KiCad | E.D.A. 9.0.4 Size: A4 | Rev: 1.01
https://github.com/xtremespb/frank Colored | TOP - | Page 3/4 SHDN GND

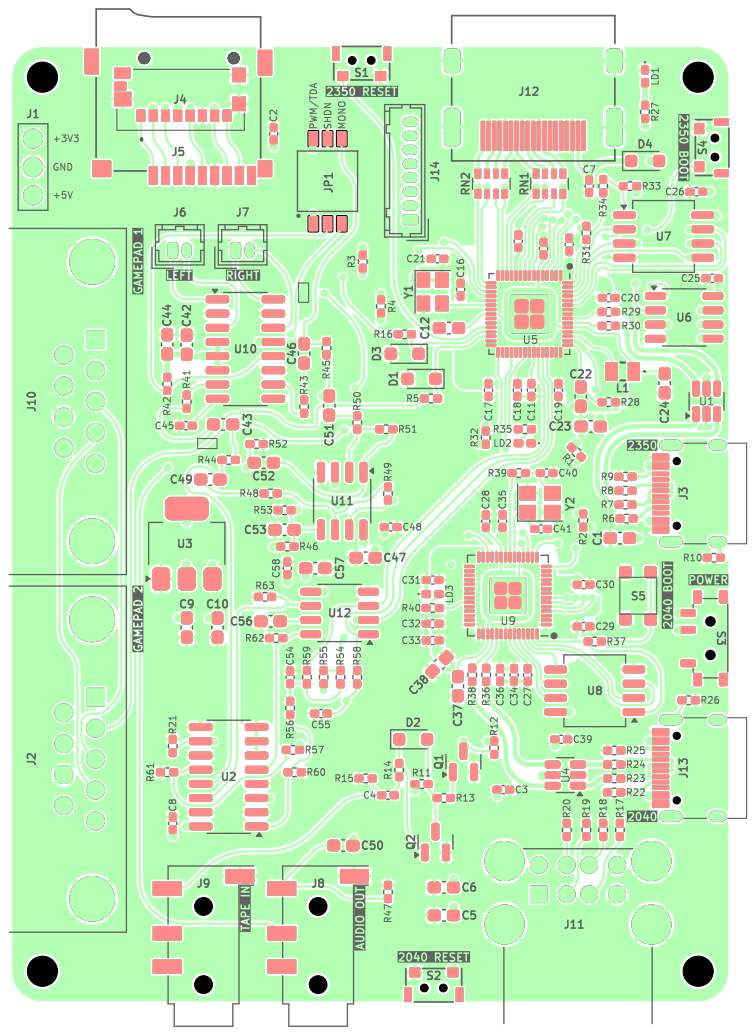
[picture p120: page 3]

JP3 1 | 2 | 3 | 4 | 5 | 6

A

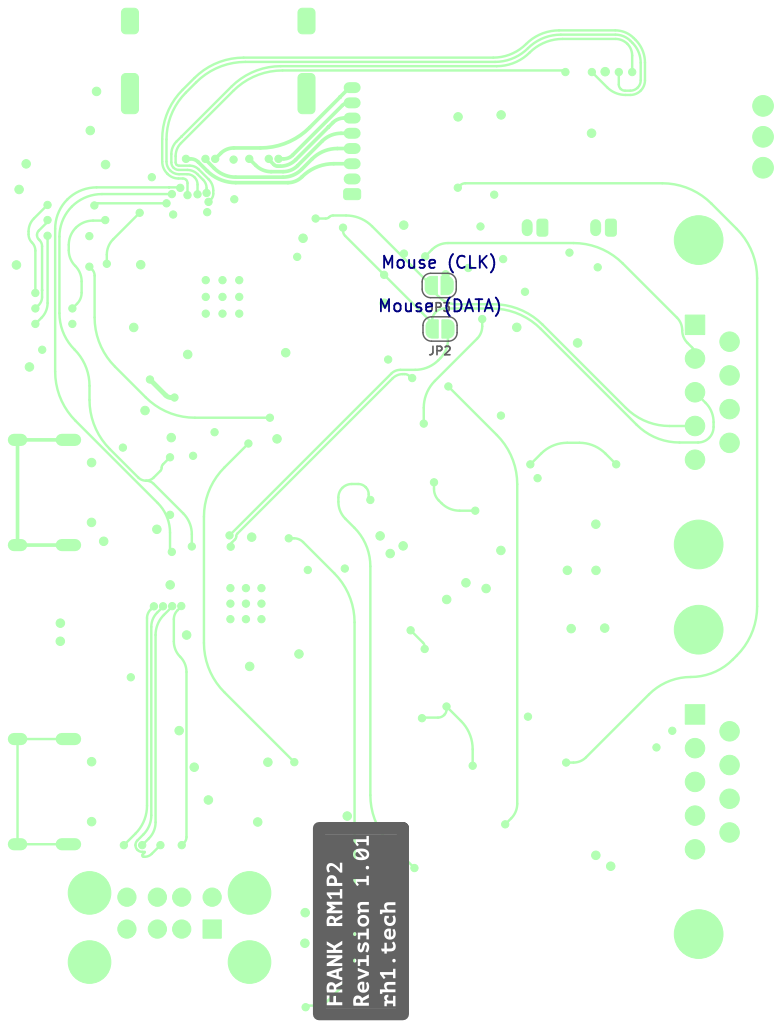
[picture p121: page 4]
D Date: 2025-09-02 KiCad; E.D.A. 9.0.4 Size: A4; Rev: 1.01; File: frank_rm1p2.kicad_pcb Sheet: Colored; BOT Mikhail; Matveev; https://github.com/xtremespb/frank Colored; BOT -; Page 4/4

Mouse (DATA) Mouse (CLK)

Id: /1 Title: FRANK RM1P2
