rh1tech/frank-archive/microfrank_rm1p2/DOCS/1_00/assembly.pdf

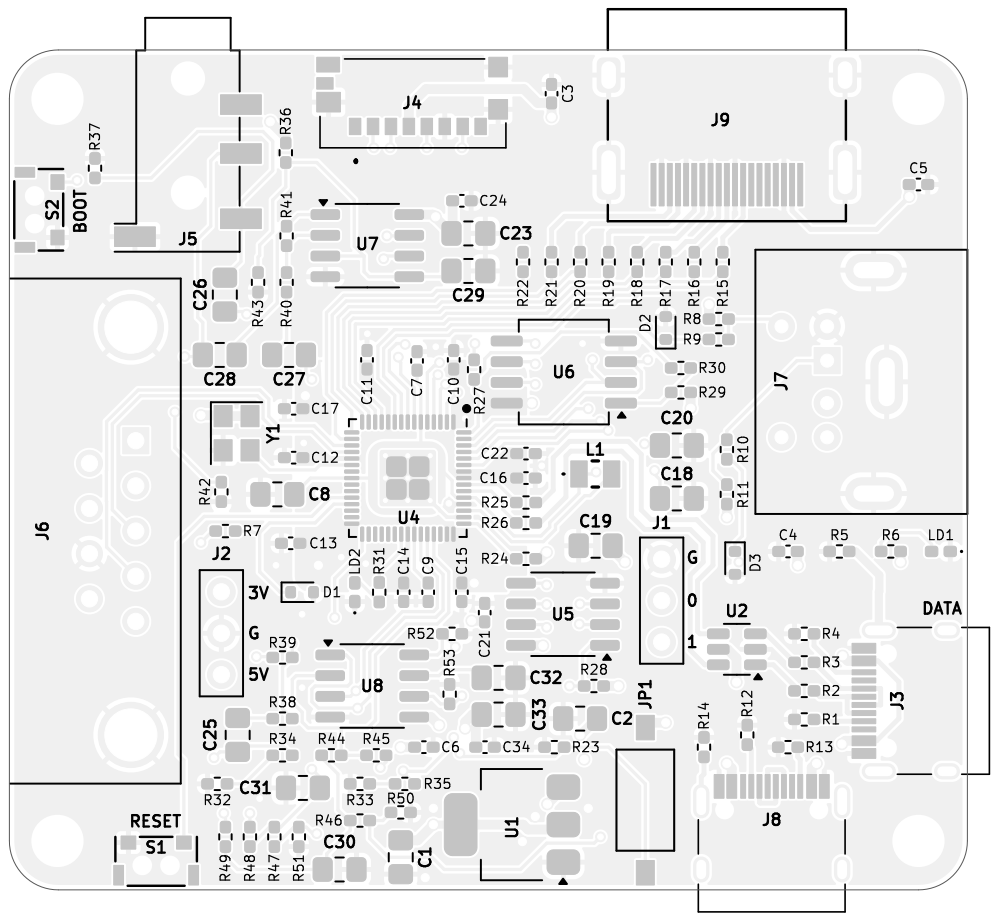
[picture p122: page 1]

https://github.com/xtremespb/frank Black And White TOP - Page 1/4

File: microfrank_rm1p2.kicad_pcb Sheet: Black And White TOP Mikhail Matveev

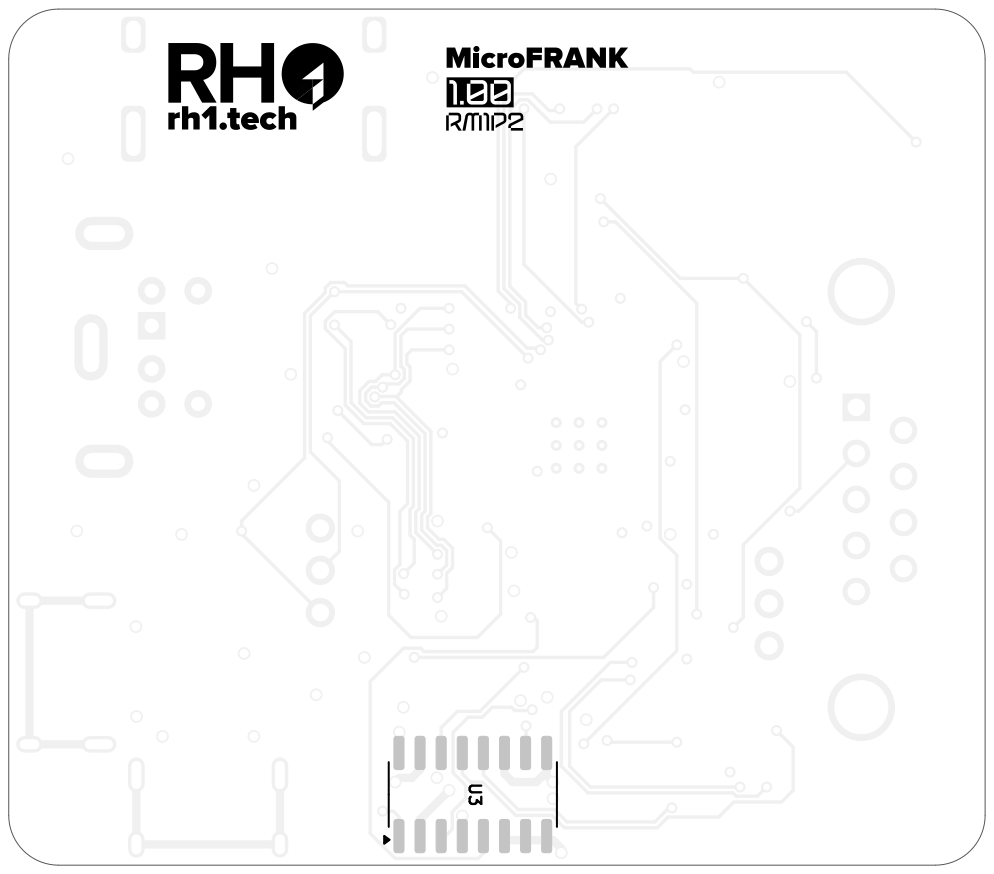
[picture p123: page 2]
D Date: 2025-06-25 KiCad; E.D.A. 9.0.0 Size: A4; Rev: 1.00; File: microfrank_rm1p2.kicad_pcb Sheet: Black; And; White; BOT Mikhail; Matveev; https://github.com/xtremespb/frank Black; BOT -; Page 2/4

Id: /1 Title: MicroFRANK RM1P2

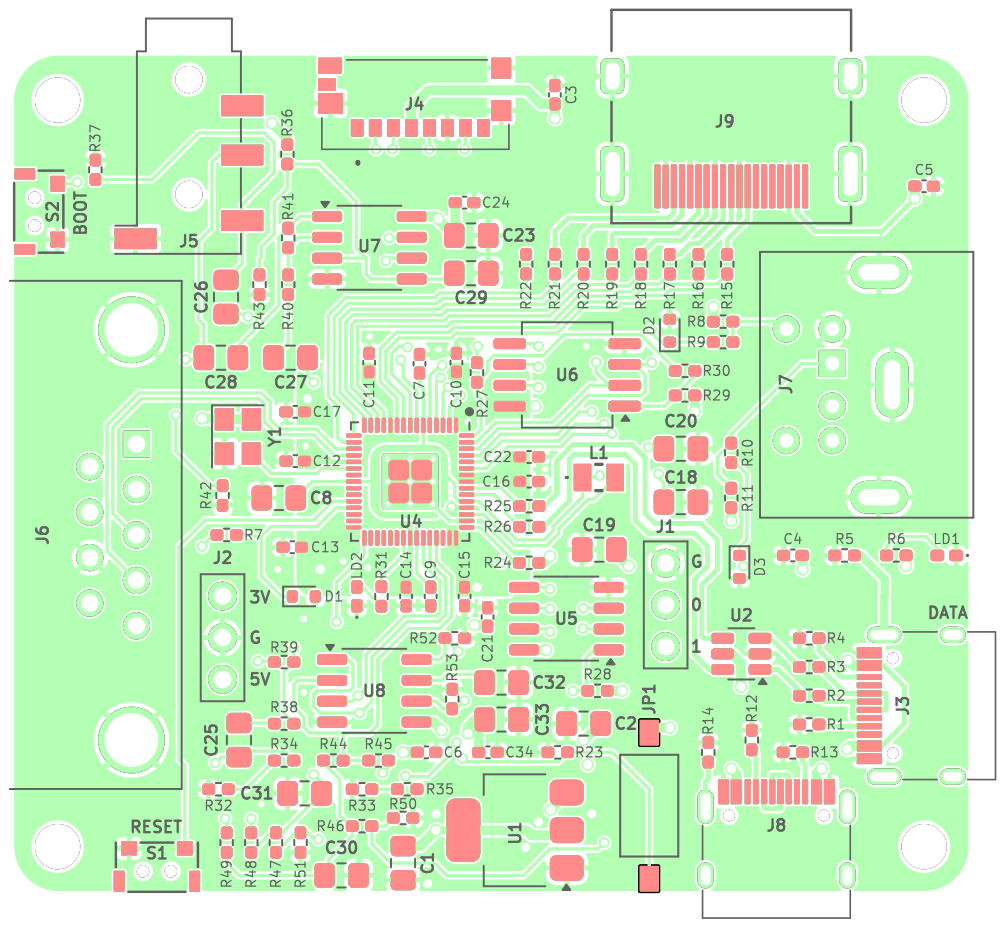
[picture p124: page 3]

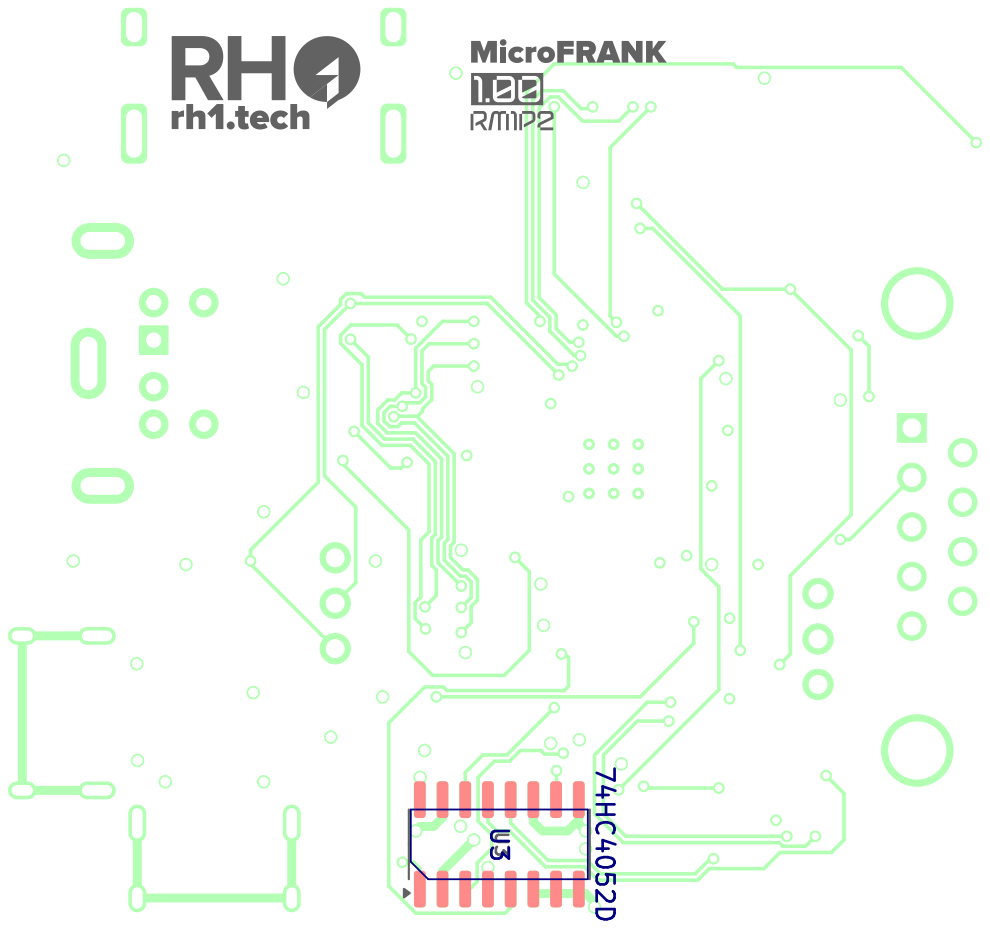
[picture p125: page 4]
D Date: 2025-06-25 KiCad; E.D.A. 9.0.0 Size: A4; Rev: 1.00; File: microfrank_rm1p2.kicad_pcb Sheet: Colored; BOT Mikhail; Matveev; https://github.com/xtremespb/frank Colored; BOT -; Page 4/4 ⁷⁴HC4052D U3

Id: /1 Title: MicroFRANK RM1P2
