rh1tech/frank-archive/microfrank_rm1p2u/DOCS/1_00/assembly.pdf

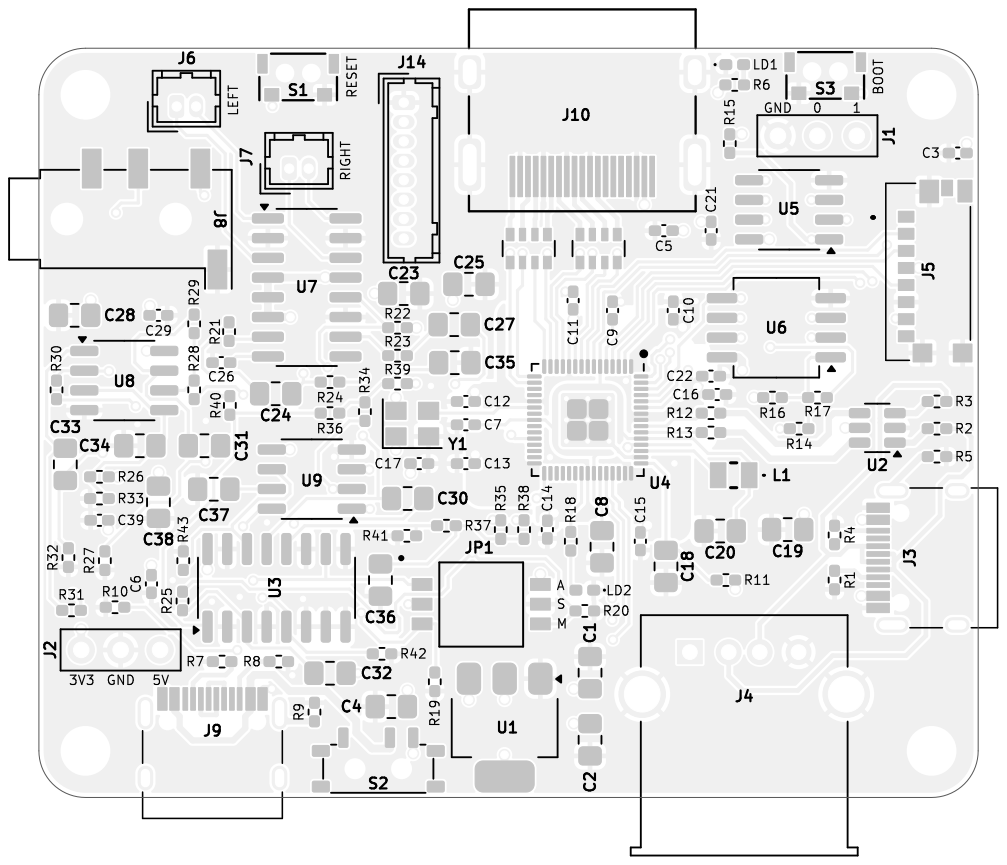
[picture p126: page 1]

https://github.com/xtremespb/frank Black And White TOP - Page 1/4

File: microfrank_rm1p2u.kicad_pcb Sheet: Black And White TOP Mikhail Matveev

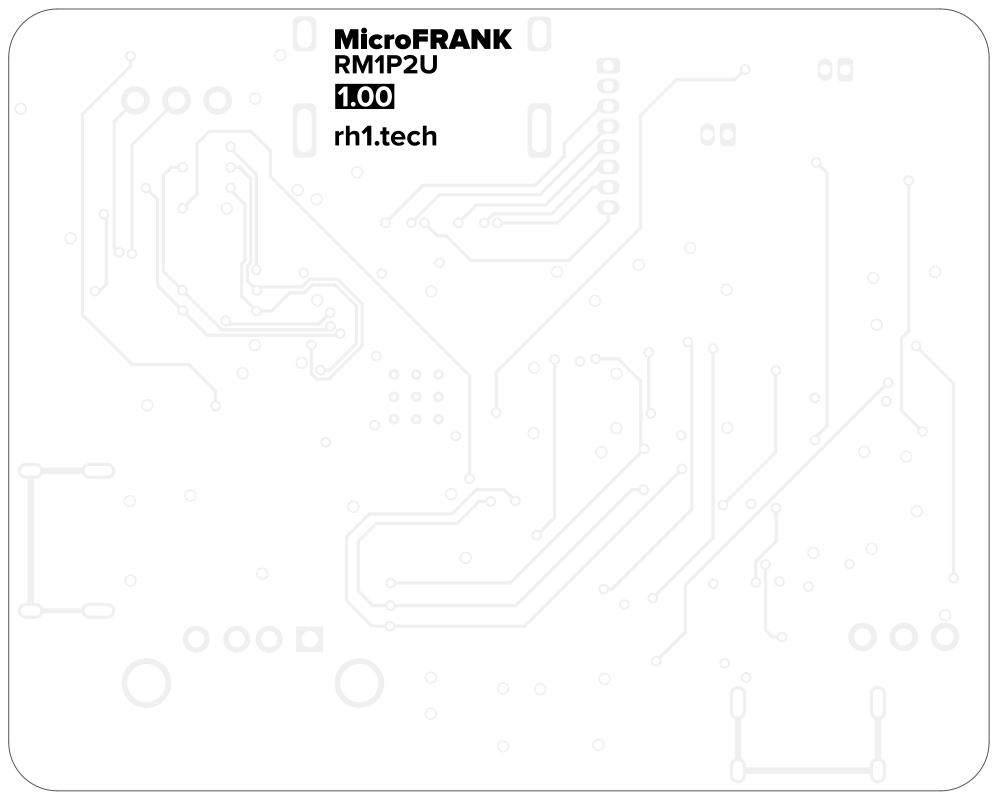
[picture p127: page 2]
D Date: 2025-07-21 KiCad; E.D.A. 9.0.0 Size: A4; Rev: 1.00; File: microfrank_rm1p2u.kicad_pcb Sheet: Black; And; White; BOT Mikhail; Matveev; https://github.com/xtremespb/frank Black; BOT -; Page 2/4

Id: /1 Title: MicroFRANK RM1P2U

https://github.com/xtremespb/frank Colored | TOP - | Page 3/4 BOOT

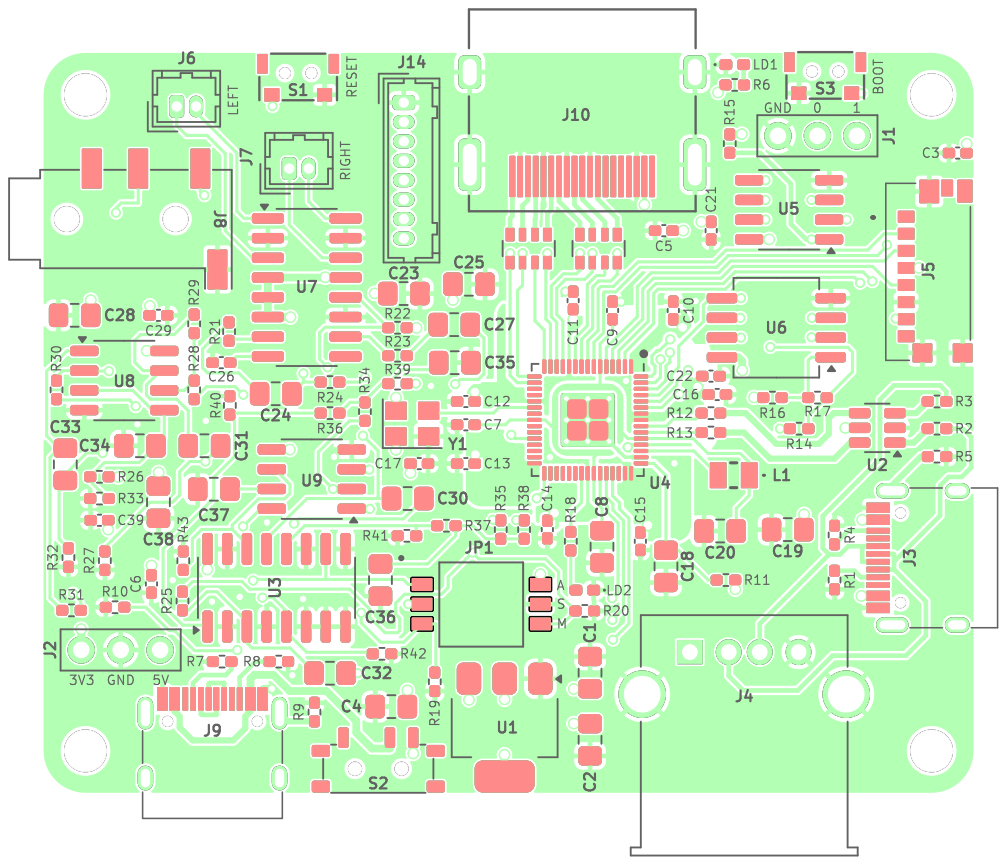
[picture p128: page 3]

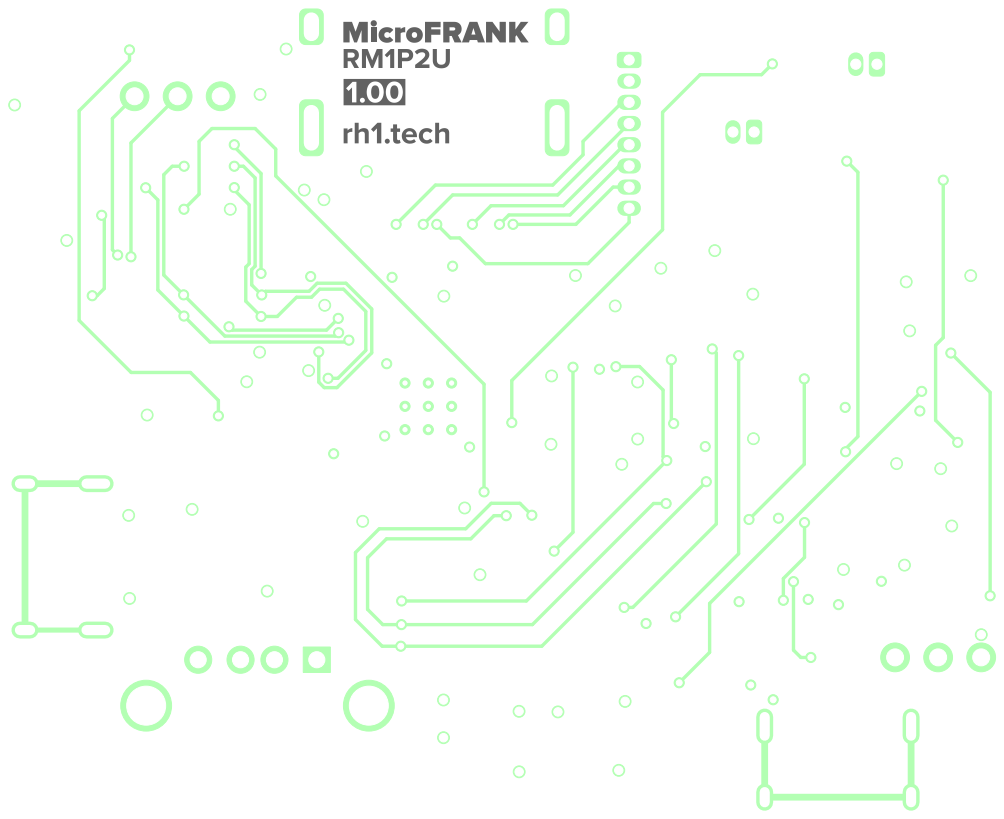
[picture p129: page 4]
D Date: 2025-07-21 KiCad; E.D.A. 9.0.0 Size: A4; Rev: 1.00; File: microfrank_rm1p2u.kicad_pcb Sheet: Colored; BOT Mikhail; Matveev; https://github.com/xtremespb/frank Colored; BOT -; Page 4/4

Id: /1 Title: MicroFRANK RM1P2U
