rh1tech/frank-archive/minifrank_rm1/DOCS/2_07/assembly.pdf

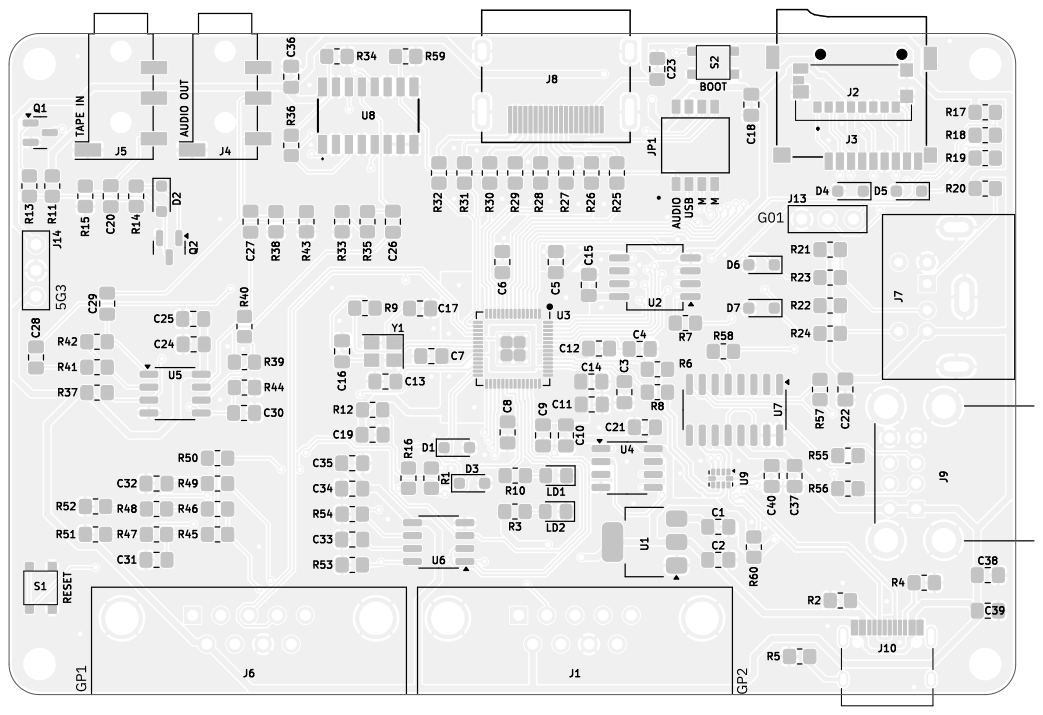
[picture p134: page 1]

MM USB AUDIO RESET BOOT AUDIO OUT TAPE IN R1 U1 C8 R49 R46 R8 R11 R57 U2 C33 C11 C39 C34 D3 R50 R27D4 C20 C31

https://github.com/xtremespb/frank Black And White TOP - Page 1/4

File: minifrank_rm1.kicad_pcb Sheet: Black And White TOP Mikhail Matveev

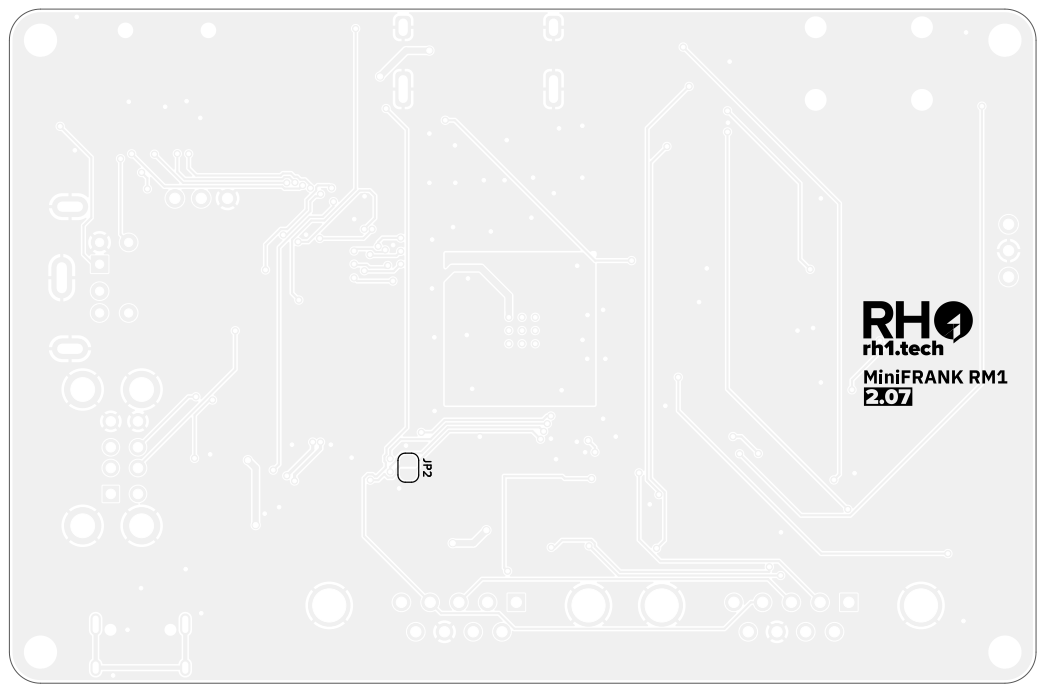
[picture p135: page 2]
D Date: 2025-04-24 KiCad; E.D.A. 9.0.0 Size: A4; Rev: 2.07; File: minifrank_rm1.kicad_pcb Sheet: Black; And; White; BOT Mikhail; Matveev; https://github.com/xtremespb/frank Black; BOT -; Page 2/4

Id: /1 Title: MiniFRANK RM1

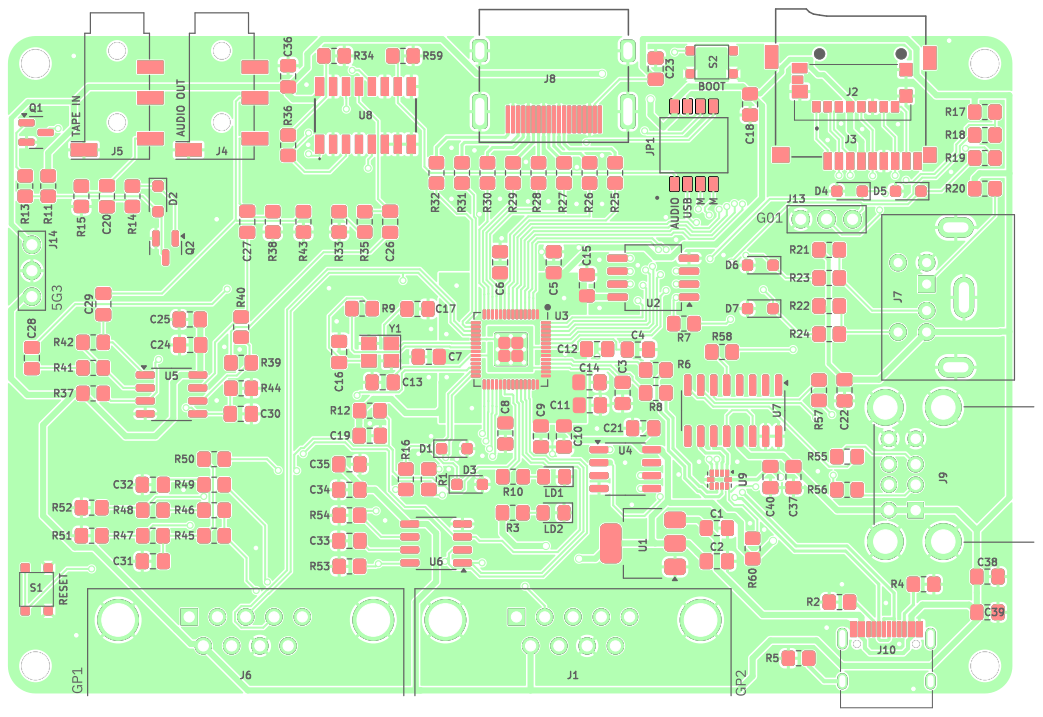
[picture p136: page 3]

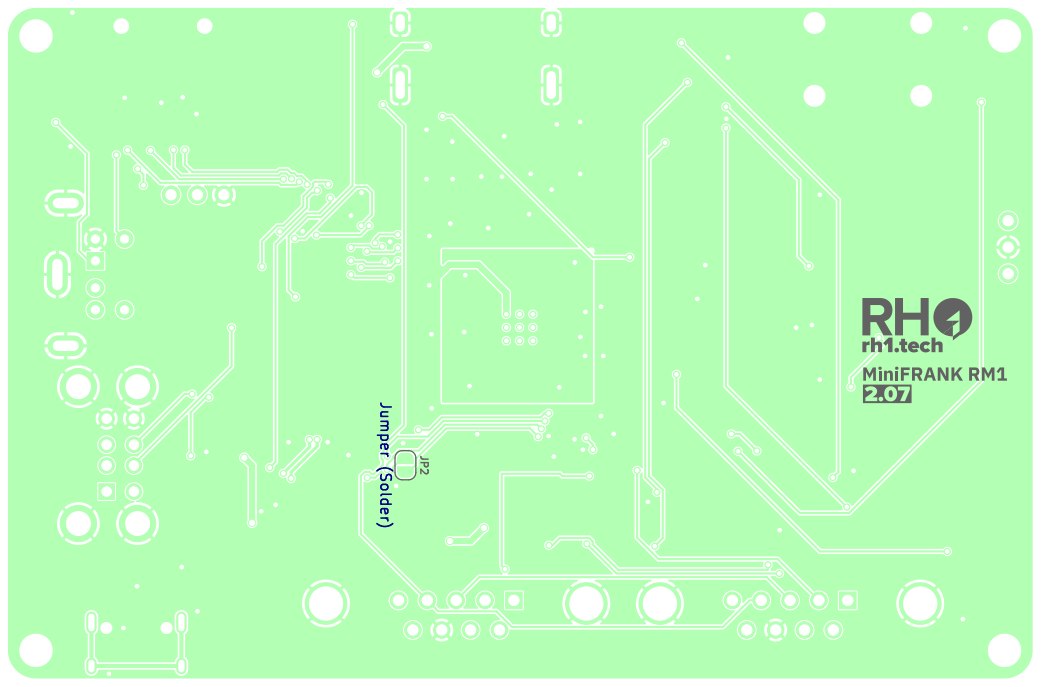
[picture p137: page 4]
D Date: 2025-04-24 KiCad; E.D.A. 9.0.0 Size: A4; Rev: 2.07; File: minifrank_rm1.kicad_pcb Sheet: Colored; BOT Mikhail; Matveev; https://github.com/xtremespb/frank Colored; BOT -; Page 4/4 Jumper (Solder)

Id: /1 Title: MiniFRANK RM1
