rh1tech/frank-archive/minifrank_rm1p2/DOCS/1_00/assembly.pdf

1 | 2 | 3 | 4 | 5 | 6

A

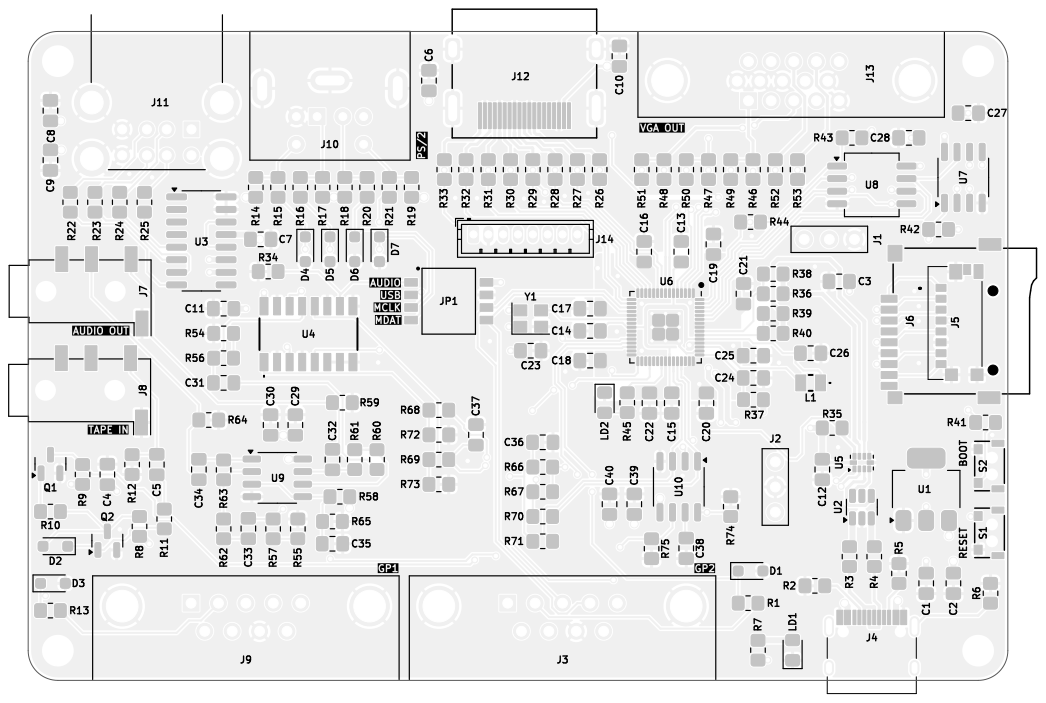
[picture p138: page 1]

https://github.com/xtremespb/frank Black And White TOP - Page 1/4

File: minifrank_rm1p2.kicad_pcb Sheet: Black And White TOP Mikhail Matveev

A

A

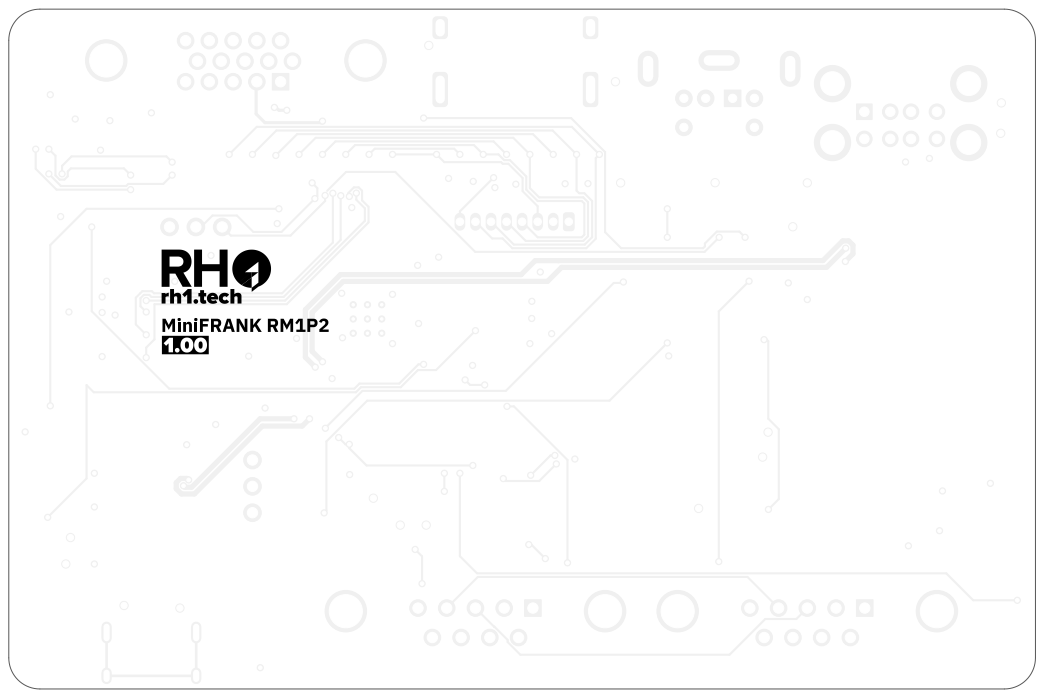
[picture p139: page 2]
D Date: 2025-05-19 KiCad; E.D.A. 9.0.0 Size: A4; Rev: 1.00; File: minifrank_rm1p2.kicad_pcb Sheet: Black; And; White; BOT Mikhail; Matveev; https://github.com/xtremespb/frank Black; BOT -; Page 2/4

Id: /1 Title: MiniFRANK RM1P2

A

A

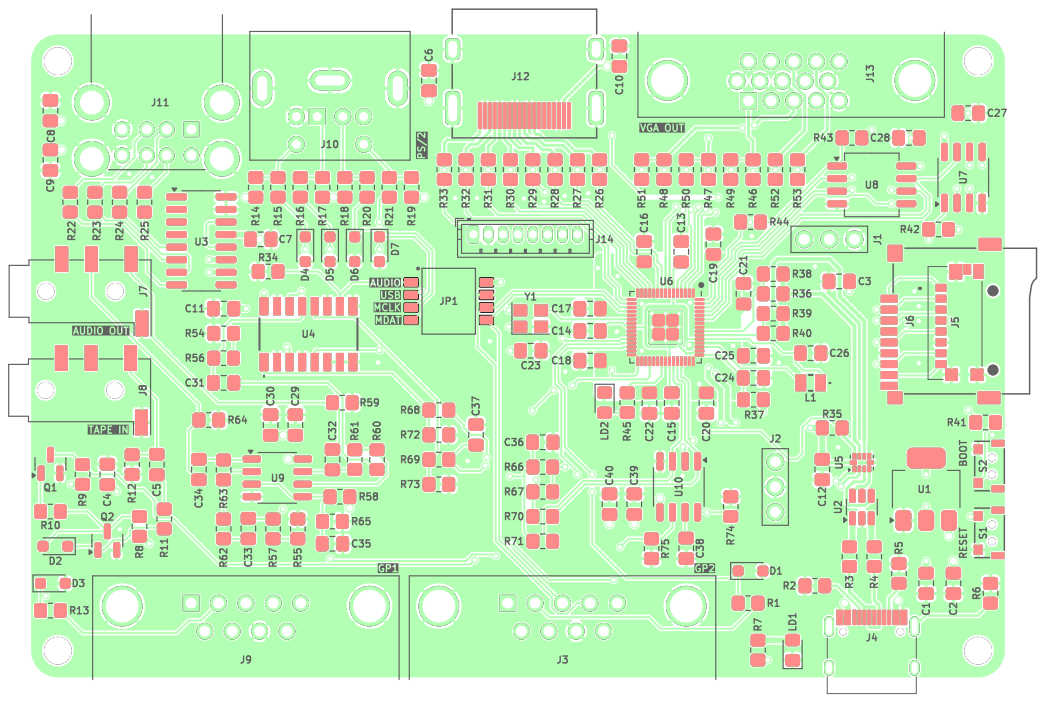
[picture p140: page 3]

A

A

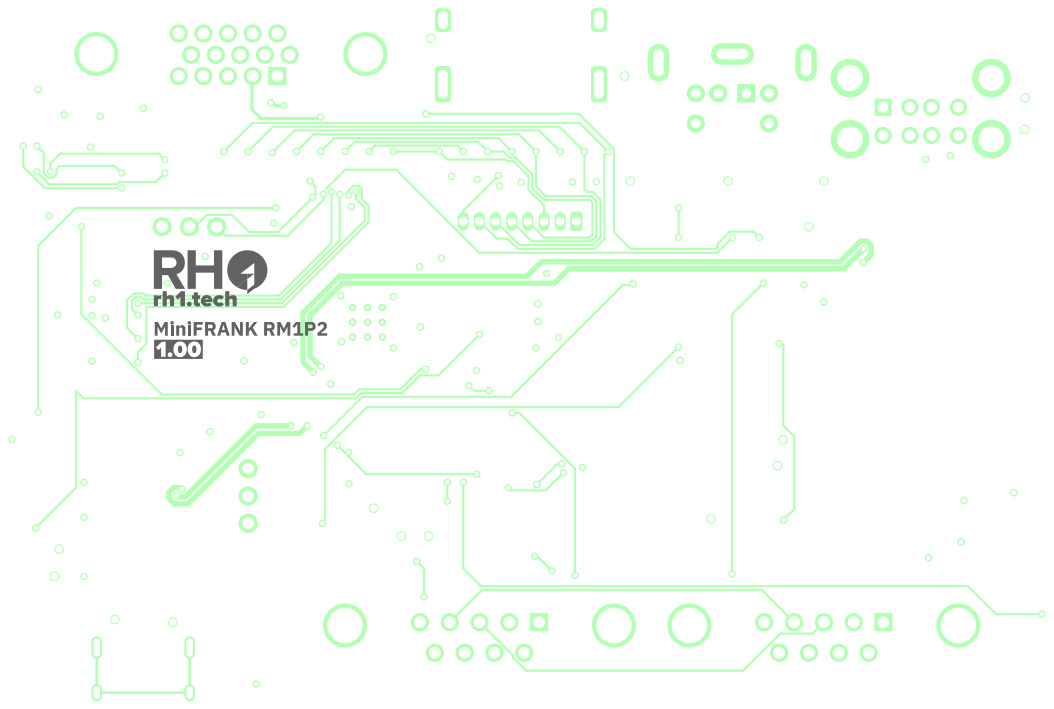
[picture p141: page 4]
D Date: 2025-05-19 KiCad; E.D.A. 9.0.0 Size: A4; Rev: 1.00; File: minifrank_rm1p2.kicad_pcb Sheet: Colored; BOT Mikhail; Matveev; https://github.com/xtremespb/frank Colored; BOT -; Page 4/4

Id: /1 Title: MiniFRANK RM1P2
