rh1tech/frank-archive/minifrank_rm1p2h/DOCS/1_00/assembly.pdf

J10 | R56 | C⁴ U¹ R19 R59 | U¹⁴ | C⁴⁷ C9
U13 | C³⁶ C17 L1 R¹⁰ | C15 | R³⁷ R⁶⁷ | R⁴⁵ | C⁴⁴ R18 | R21 R¹ | S2 1 | 2 | 3 | 4 | 5 | 6 1 | 2 | 3 | 4 | 5 | 6 ABCD | ABCD Date: 2025-08-01 KiCad E.D.A. 9.0.0 Size: A4 | Rev: 1.00

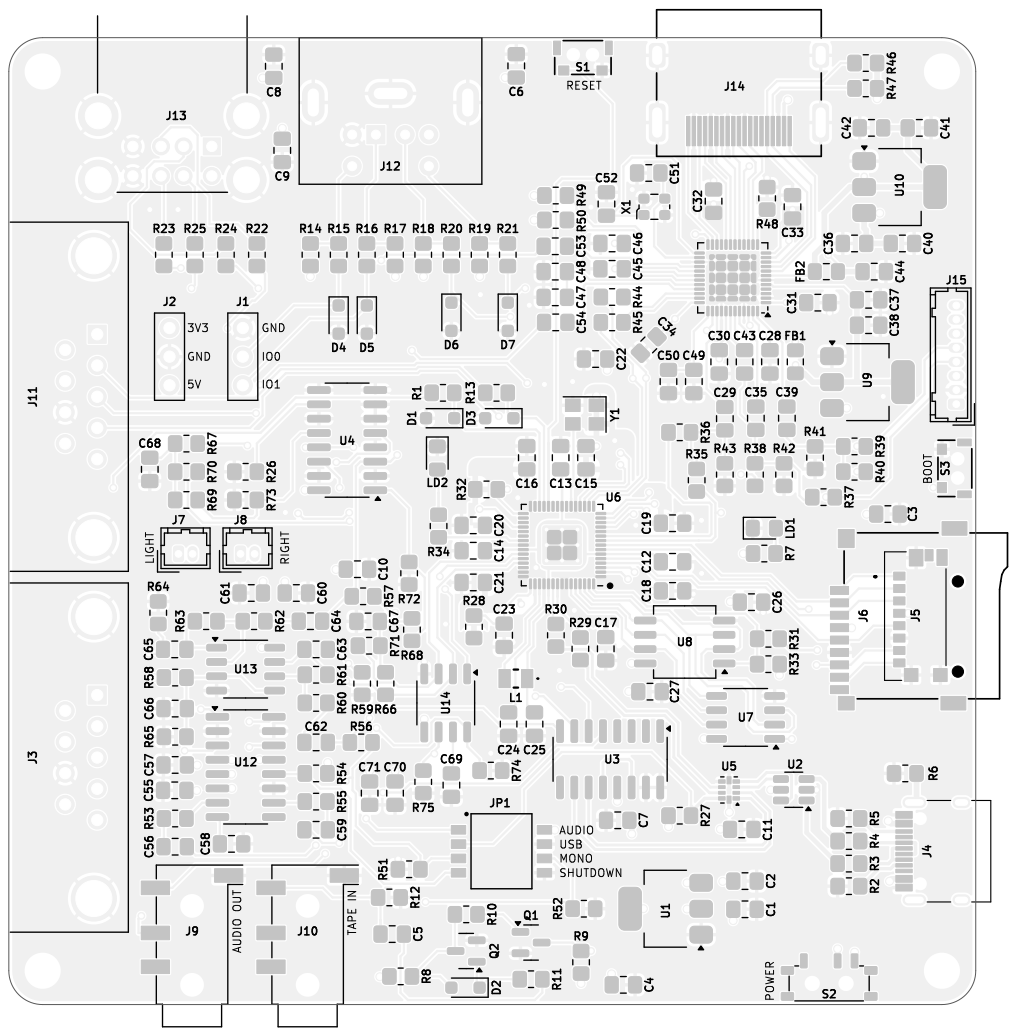
[picture p146: page 1]

https://github.com/xtremespb/frank Black And White TOP - Page 1/4

File: minifrank_rm1p2h.kicad_pcb Sheet: Black And White TOP Mikhail Matveev

A

A

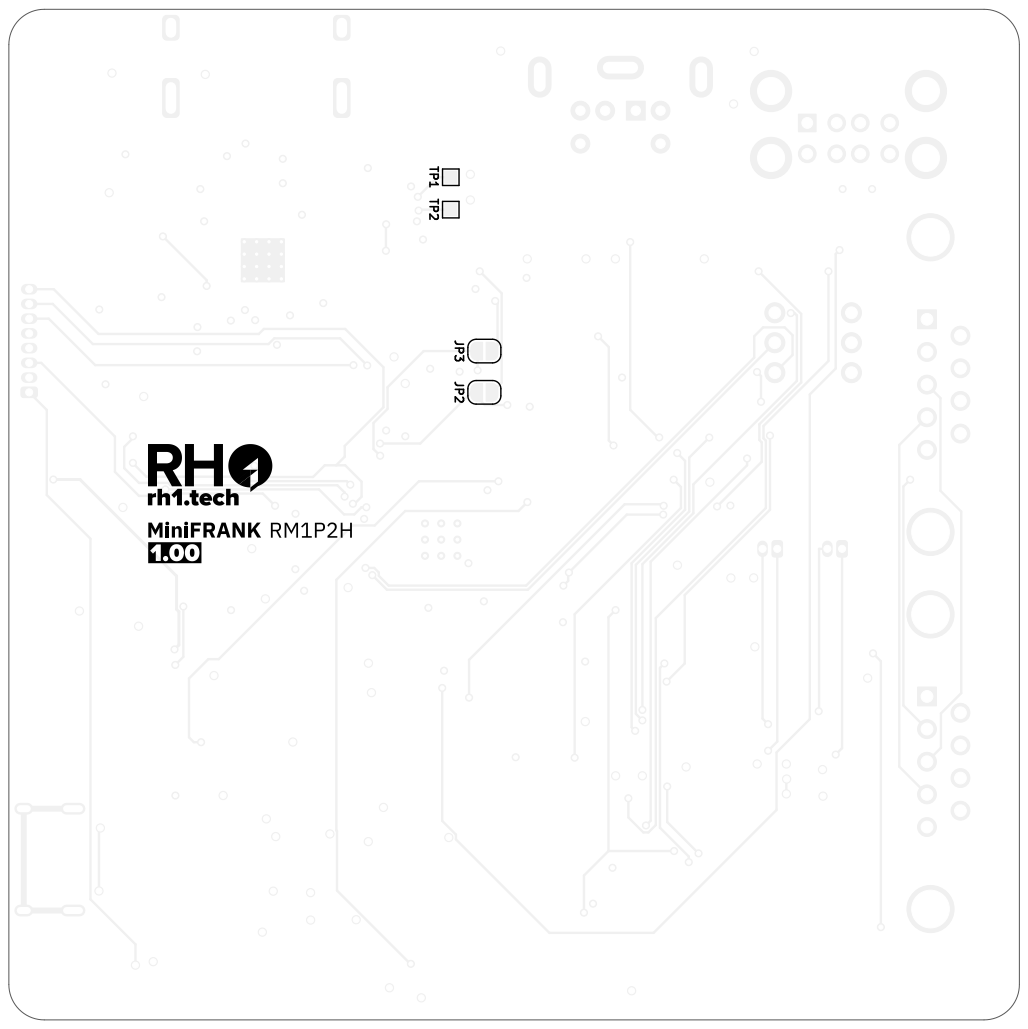
[picture p147: page 2]
D Date: 2025-08-01 KiCad; E.D.A. 9.0.0 Size: A4; Rev: 1.00; File: minifrank_rm1p2h.kicad_pcb Sheet: Black; And; White; BOT Mikhail; Matveev; https://github.com/xtremespb/frank Black; BOT -; Page 2/4

Id: /1 Title: MiniFRANK RM1P2H

1 | 2 | 3 | 4 | 5 | 6 1 | 2 | 3 | 4 | 5 | 6 ABCD | ABCD Date: 2025-08-01 KiCad | E.D.A. 9.0.0 Size: A4 | Rev: 1.00
J10 | R56 | C⁴ U¹ R19 R59 | U¹⁴ | C⁴⁷ C9

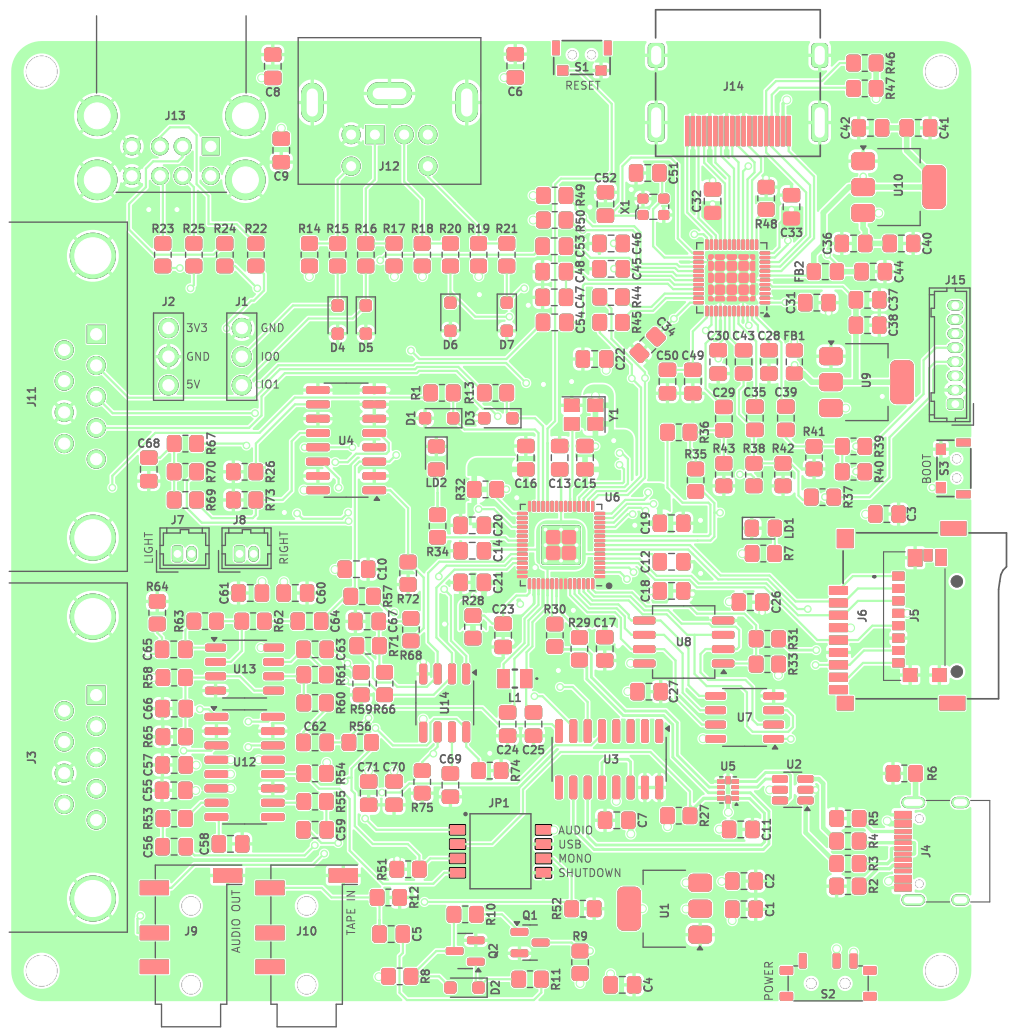
[picture p148: page 3]

A

A

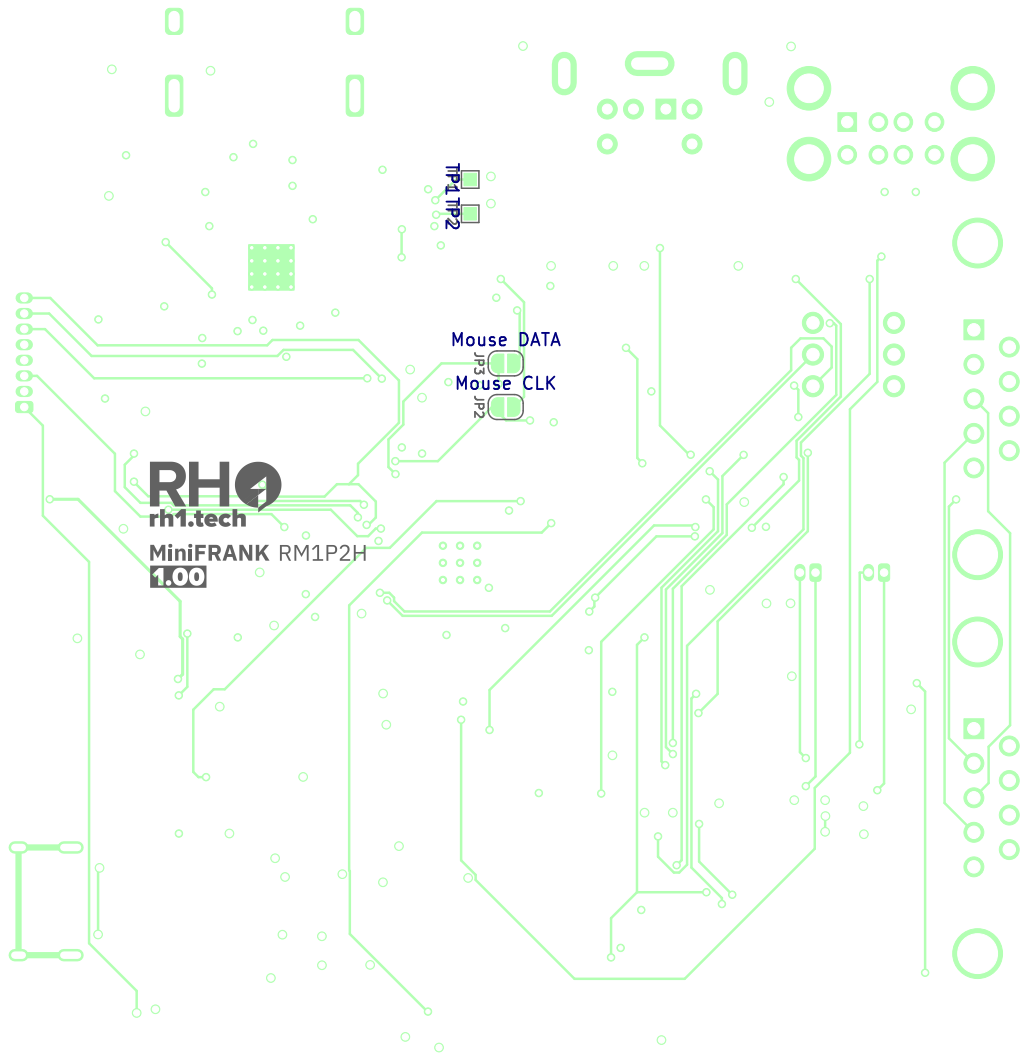
[picture p149: page 4]
D Date: 2025-08-01 KiCad; E.D.A. 9.0.0 Size: A4; Rev: 1.00; File: minifrank_rm1p2h.kicad_pcb Sheet: Colored; BOT Mikhail; Matveev; https://github.com/xtremespb/frank Colored; BOT -; Page 4/4; Mouse; CLK TP1 Mouse; DATA TP2

Id: /1 Title: MiniFRANK RM1P2H
