rh1tech/frank-archive/tinyfrank_rm1p1/DOCS/1_00/assembly.pdf

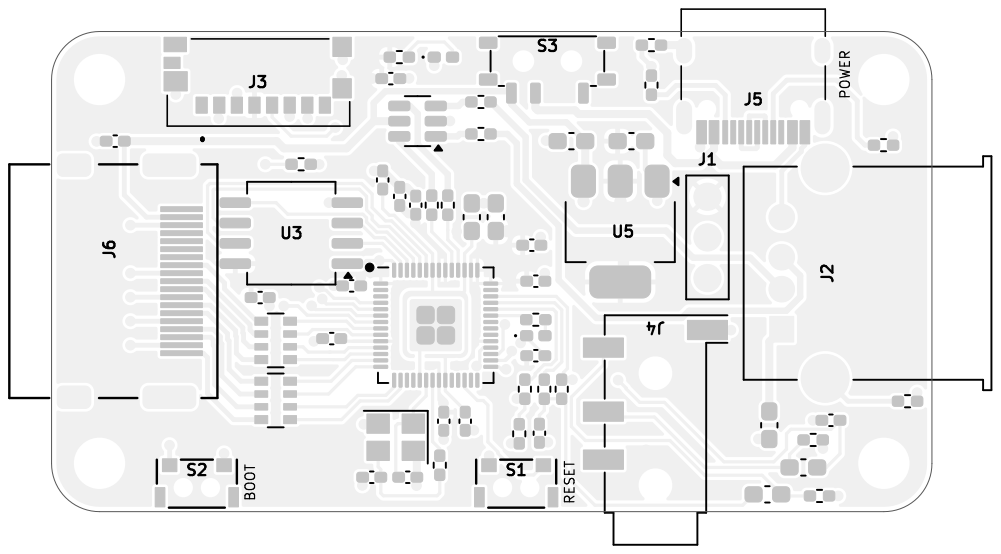
[picture p154: page 1]
POWER BOOT RESETS2 U3; D Date: 2025-09-02 KiCad; E.D.A. 9.0.4 Size: A4; Rev: 1.00; File: tinyfrank_rm1p1.kicad_pcb Sheet: Black; And; White; TOP Mikhail; Matveev; https://github.com/xtremespb/frank Black; TOP -; Page

Id: /1 Title: TinyFRANK RM1P1

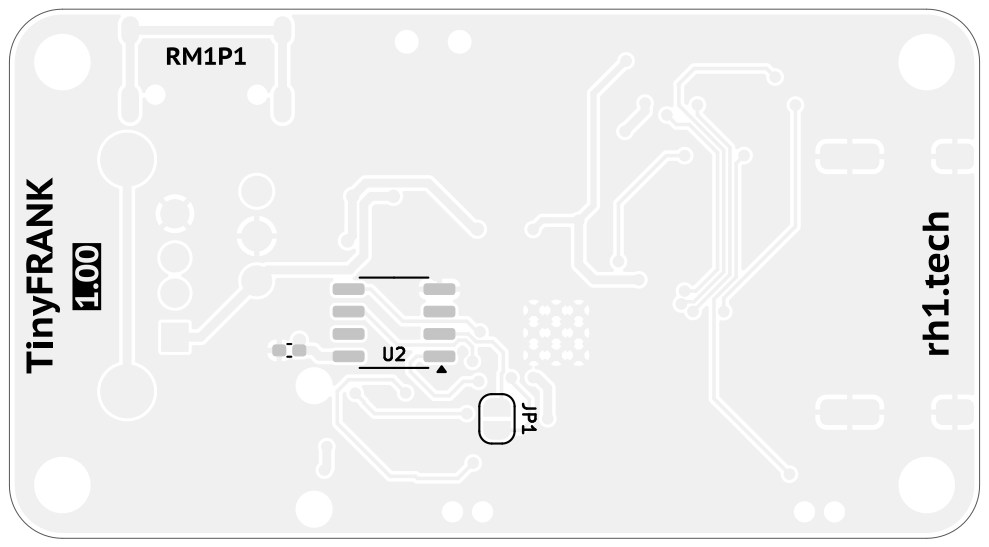
[picture p155: page 2]
D Date: 2025-09-02 KiCad; E.D.A. 9.0.4 Size: A4; Rev: 1.00; File: tinyfrank_rm1p1.kicad_pcb Sheet: Black; And; White; BOT Mikhail; Matveev; https://github.com/xtremespb/frank Black; BOT -; Page 2/4

Id: /1 Title: TinyFRANK RM1P1

https://github.com/xtremespb/frank Colored | TOP - | Page 3/4 | POWER BOOT | RESETS2 | U3

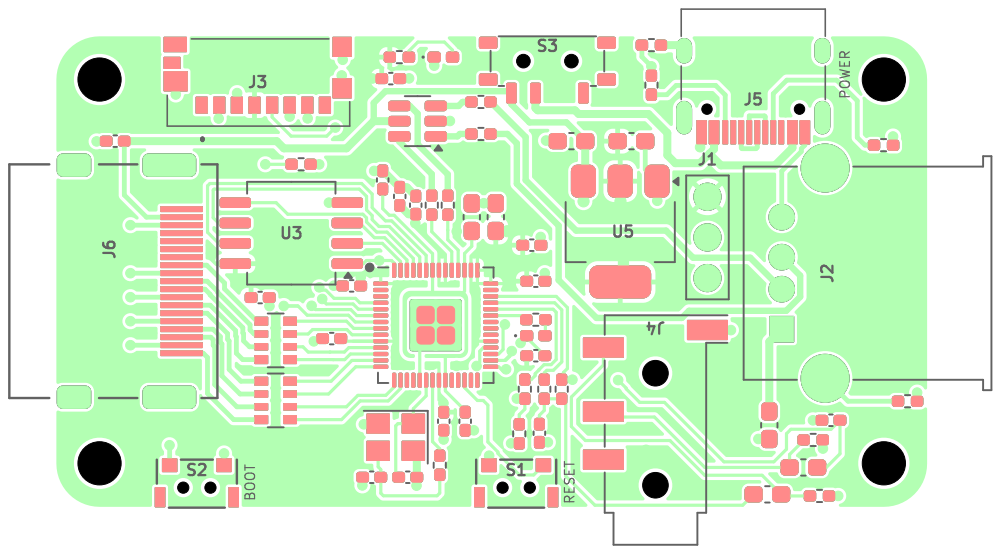
[picture p156: page 3]
D Date: 2025-09-02 KiCad; E.D.A. 9.0.4 Size: A4; Rev: 1.00; File: tinyfrank_rm1p1.kicad_pcb Sheet: Colored; TOP Mikhail; Matveev

Id: /1 Title: TinyFRANK RM1P1

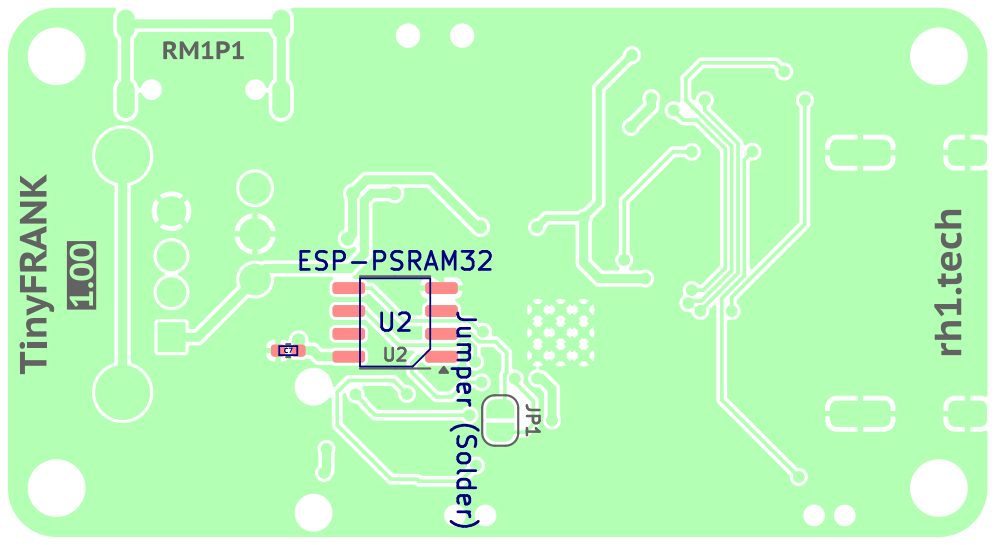
[picture p157: page 4]
D Date: 2025-09-02 KiCad; E.D.A. 9.0.4 Size: A4; Rev: 1.00; File: tinyfrank_rm1p1.kicad_pcb Sheet: Colored; BOT Mikhail; Matveev; https://github.com/xtremespb/frank Colored; BOT -; Page 4/4 Jumper (Solder); C7ESP-PSRAM32 U2

Id: /1 Title: TinyFRANK RM1P1
