rh1tech/frank-archive/frank_m2/docs/1/03/assembly.pdf

# D3 R46 J15

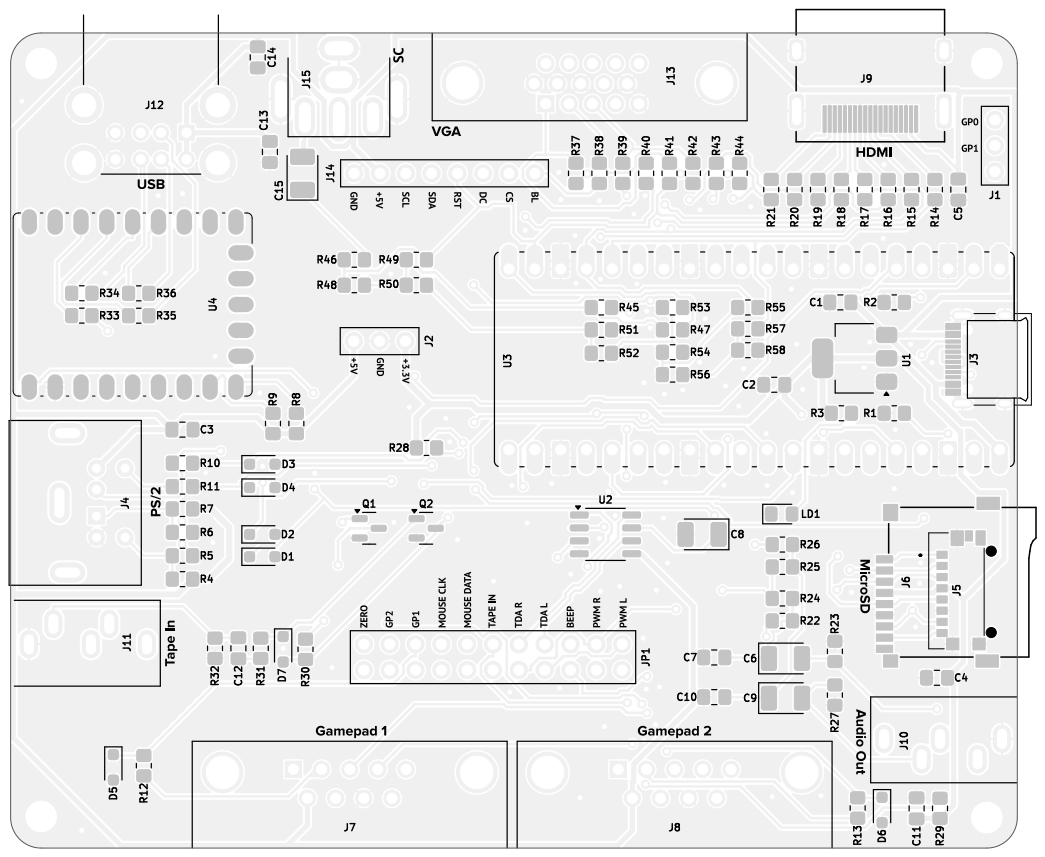
[picture p158: page 1]

https://github.com/xtremespb/frank Black And White TOP - Page 1/4

File: HR3FQ.kicad_pcb Sheet: Black And White TOP Mikhail Matveev

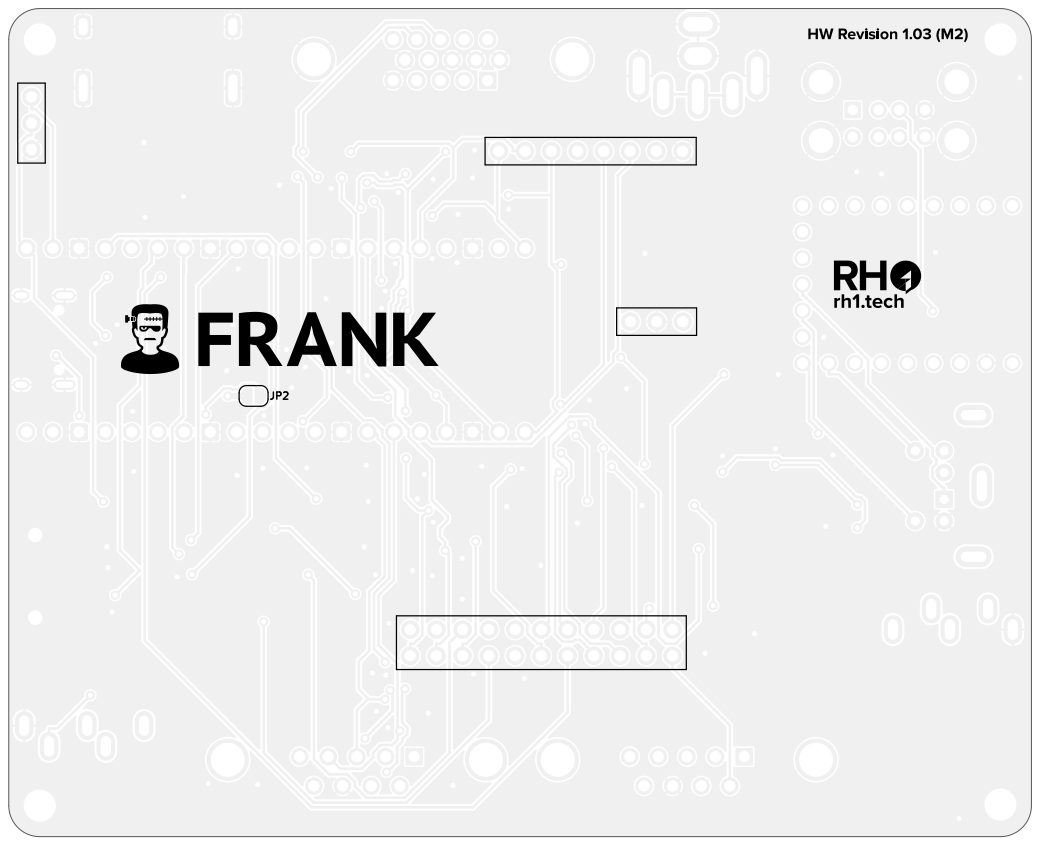
[picture p159: page 2]
D Date: 2025-03-16 KiCad; E.D.A. 9.0.0 Size: A4; Rev: 1.03; File: HR3FQ.kicad_pcb Sheet: Black; And; White; BOT Mikhail; Matveev; https://github.com/xtremespb/frank Black; BOT -; Page 2/4

Id: /1 Title: FRANK M2

# D3 R46 J15

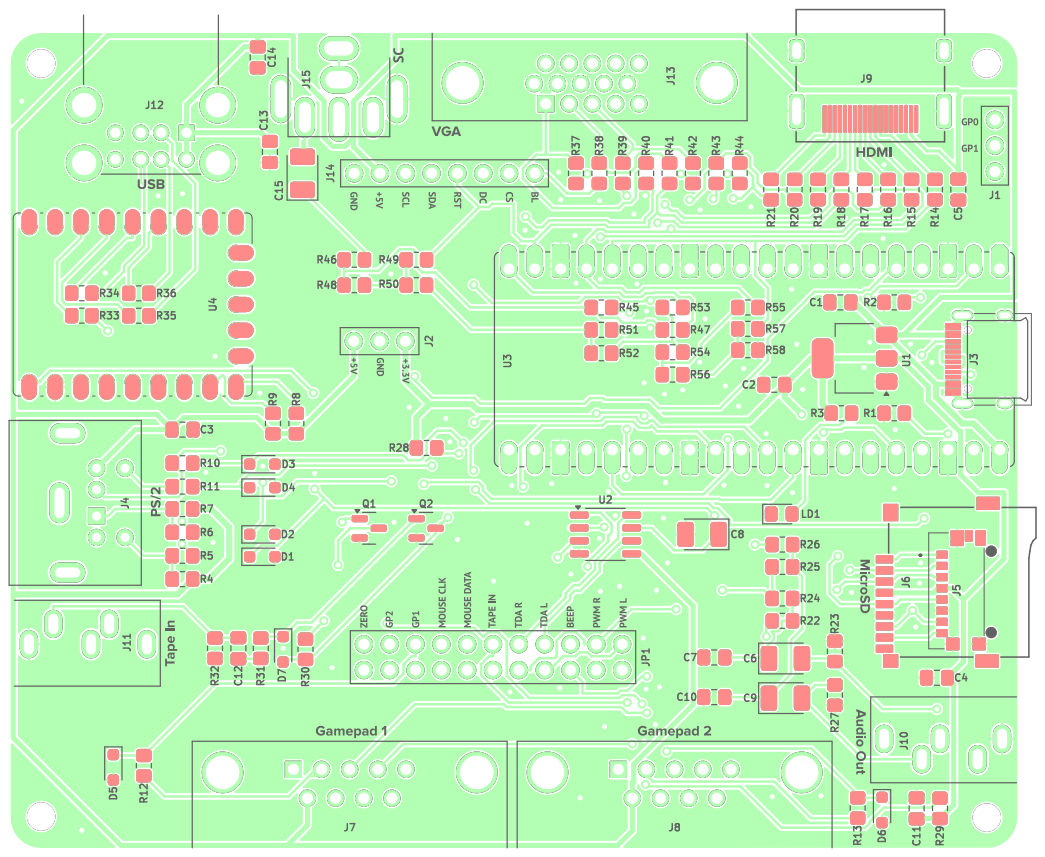
[picture p160: page 3]

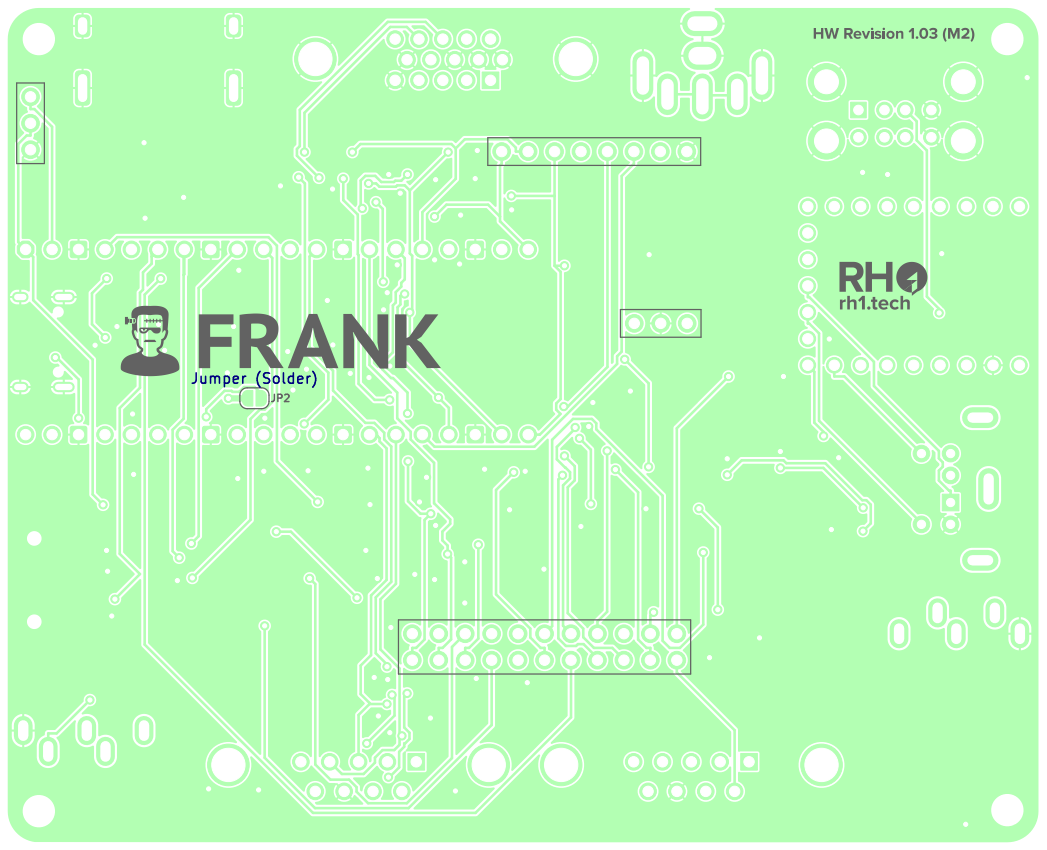
[picture p161: page 4]
D Date: 2025-03-16 KiCad; E.D.A. 9.0.0 Size: A4; Rev: 1.03; File: HR3FQ.kicad_pcb Sheet: Colored; BOT Mikhail; Matveev; https://github.com/xtremespb/frank Colored; BOT -; Page 4/4; Jumper (Solder)

Id: /1 Title: FRANK M2
