rh1tech/frank-archive/frank_fastbeta_m1/docs/1_00/fastbeta_m1.pdf

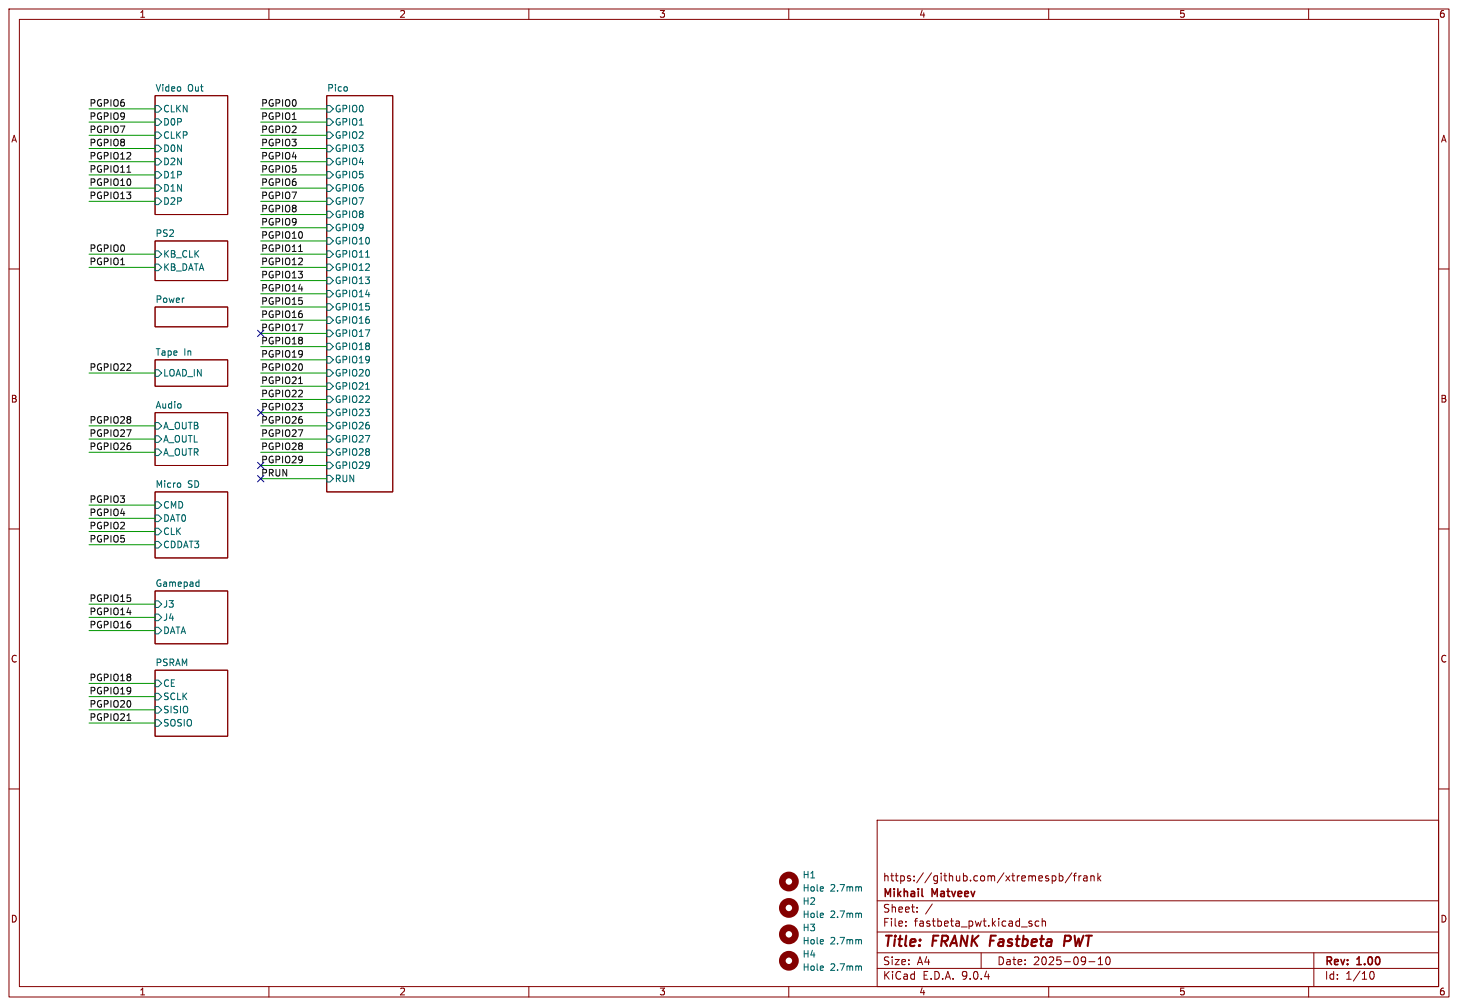
[picture p166: page 1]

https://github.com/xtremespb/frank CMD

Id: 1/10 Title: FRANK Fastbeta PWT

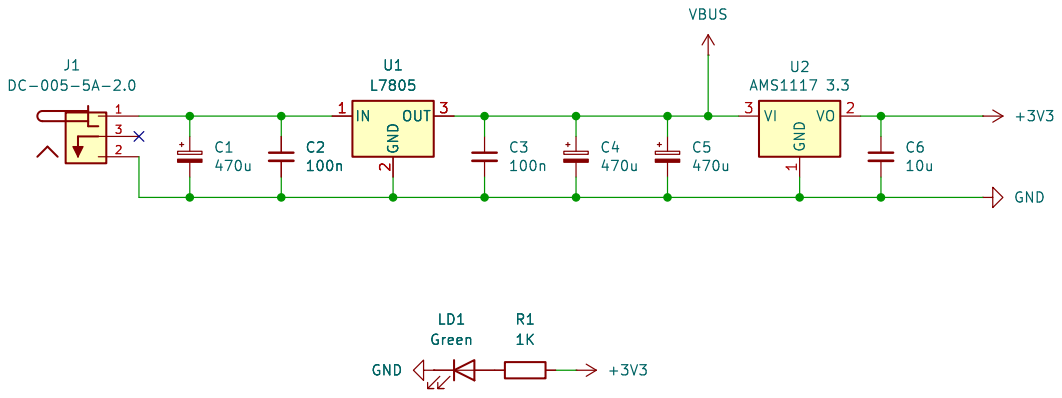
[picture p167: page 2]

https://github.com/xtremespb/frank

Id: 3/10 Title: FRANK Fastbeta

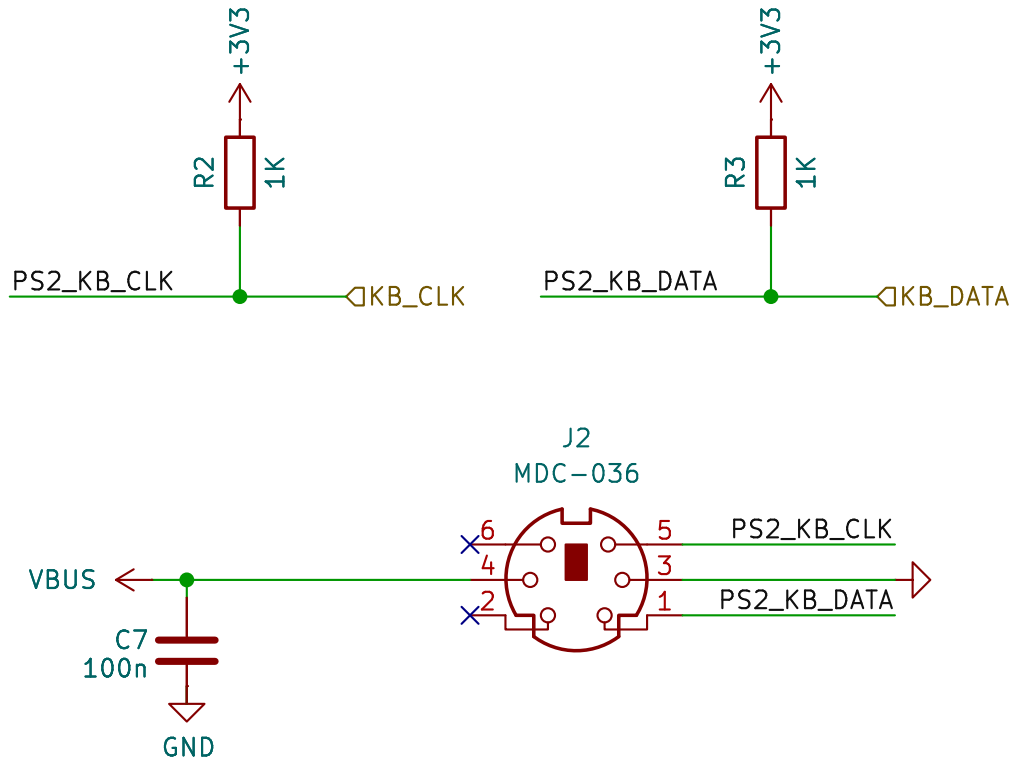
[picture p168: page 3]

https://github.com/xtremespb/frank GND

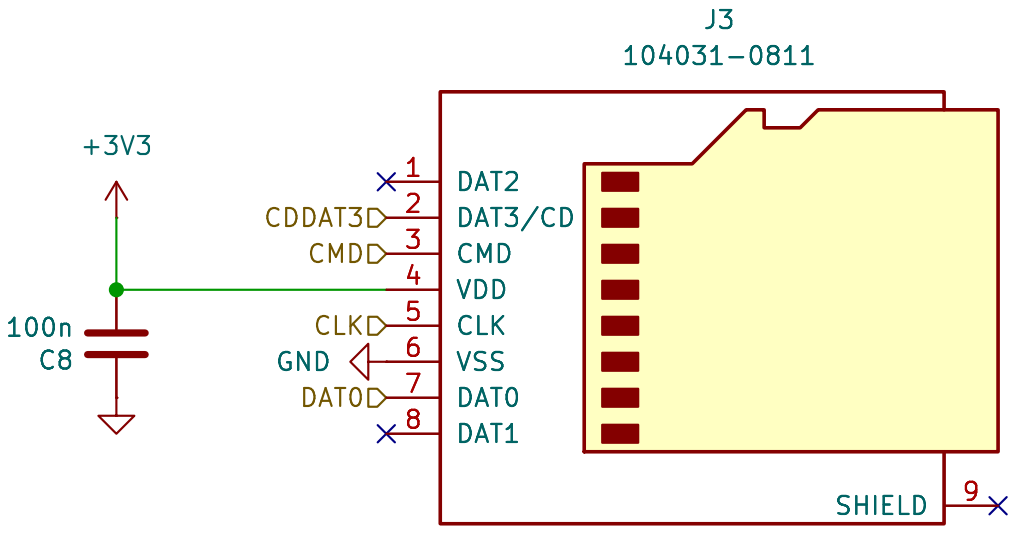
[picture p169: page 4]

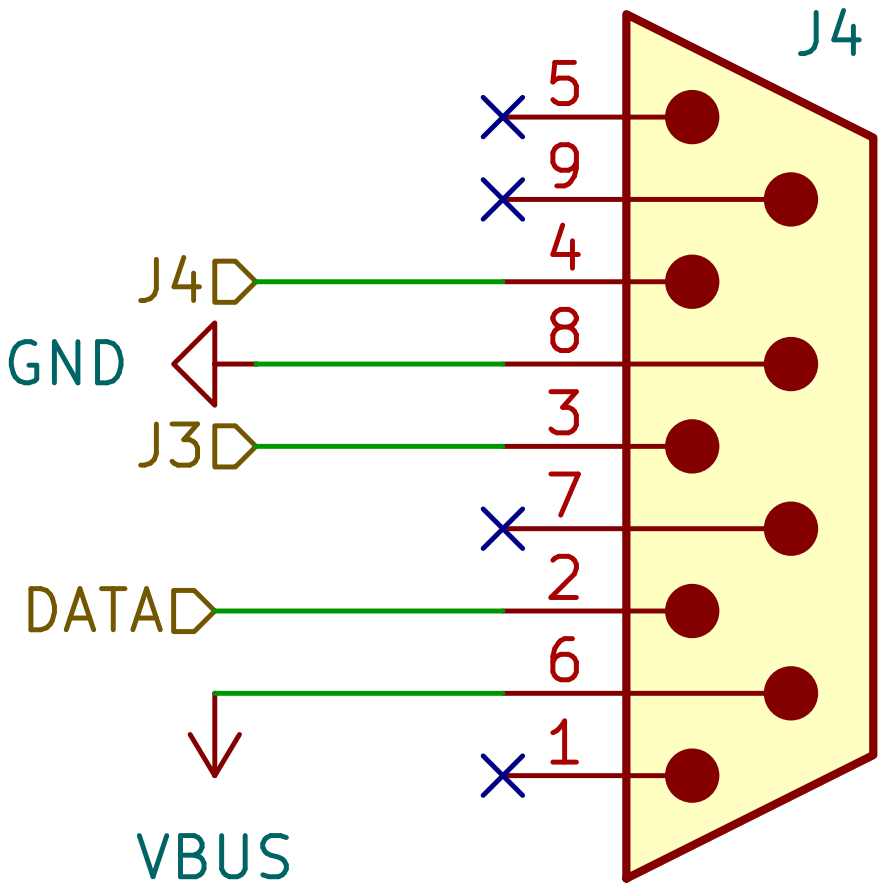
[picture p170: page 5]

https://github.com/xtremespb/frank GND
J3 DATA

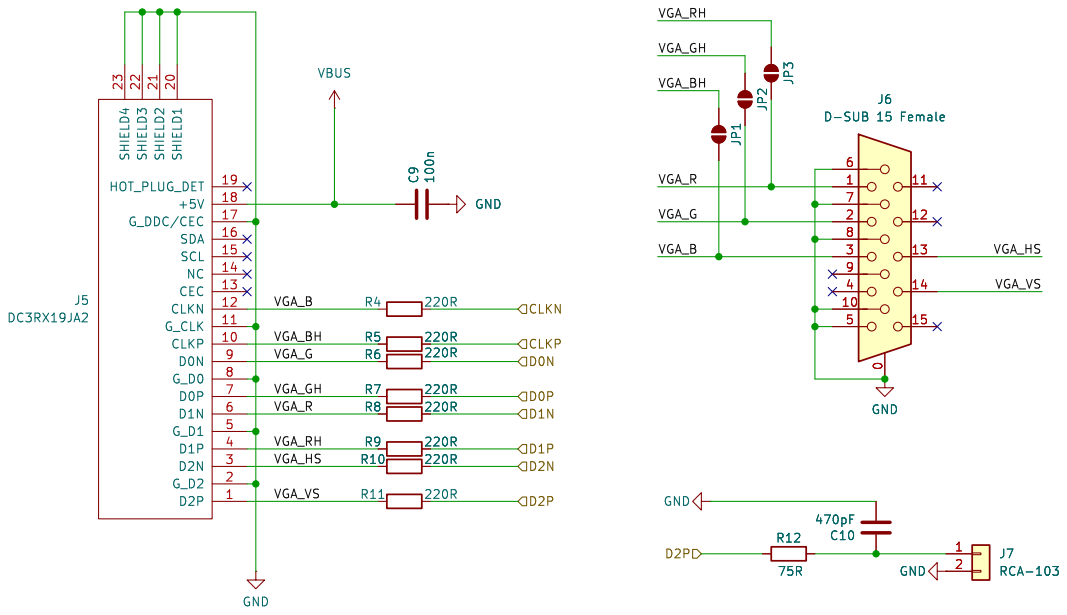
[picture p171: page 6]

https://github.com/xtremespb/frank

Id: 10/10 Title: FRANK Fastbeta

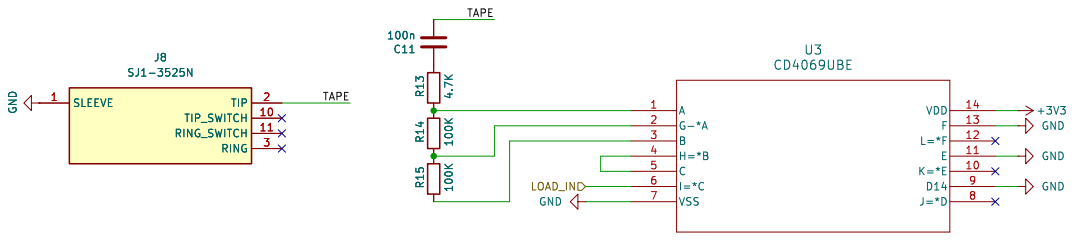
[picture p172: page 7]

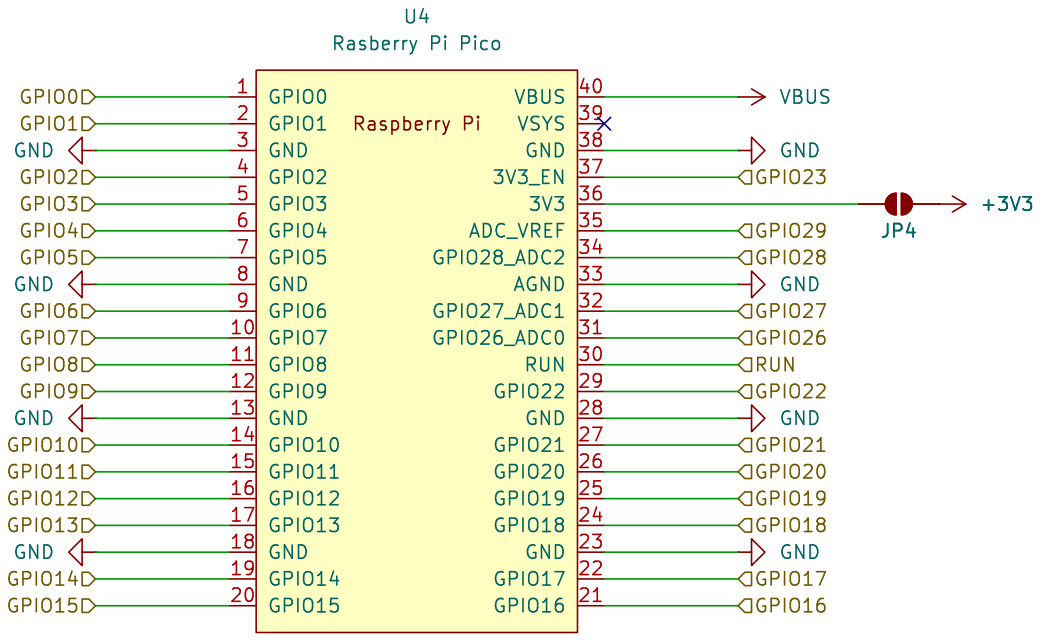
[picture p173: page 8]

https://github.com/xtremespb/frank

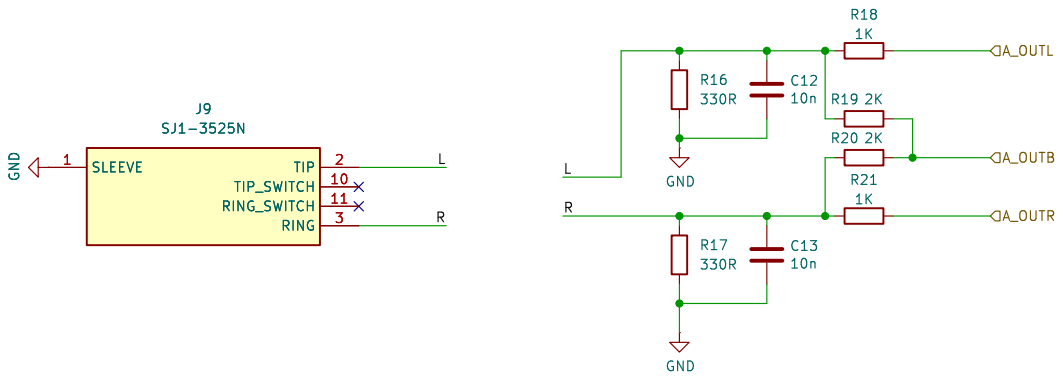
[picture p174: page 9]

https://github.com/xtremespb/frank R21

Id: 15/10 Title: FRANK Fastbeta

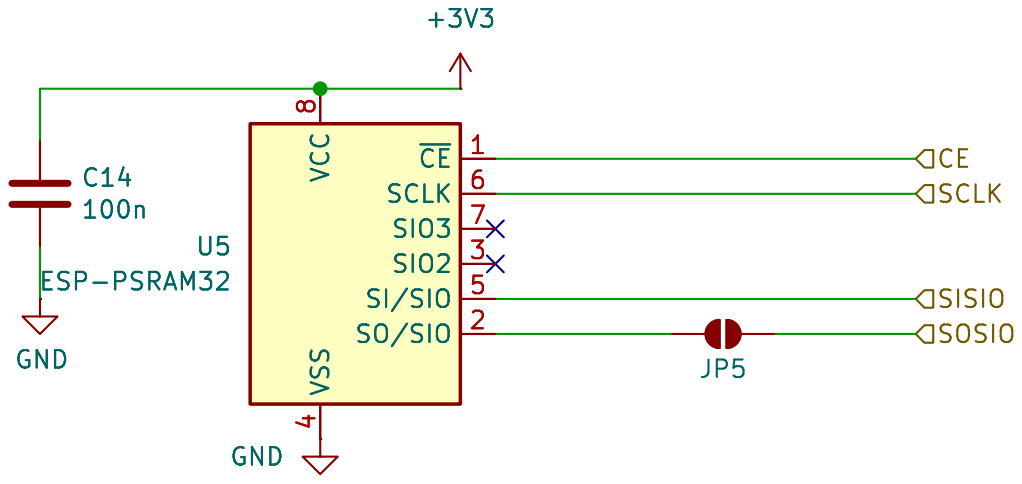
[picture p175: page 10]

4 ~{CE}1 SCLK 6 SIO3 7 SIO2 3 SI/SIO 5 SO/SIO 2 U5 ESP-PSRAM32 SISIO
100n GND

4 ~{CE}1 SCLK 6 SIO3 7 SIO2 3 SI/SIO 5 SO/SIO 2

https://github.com/xtremespb/frank
