rh1tech/frank-archive/frank_fastbeta_m1/docs/1_04/fastbeta_m1.pdf

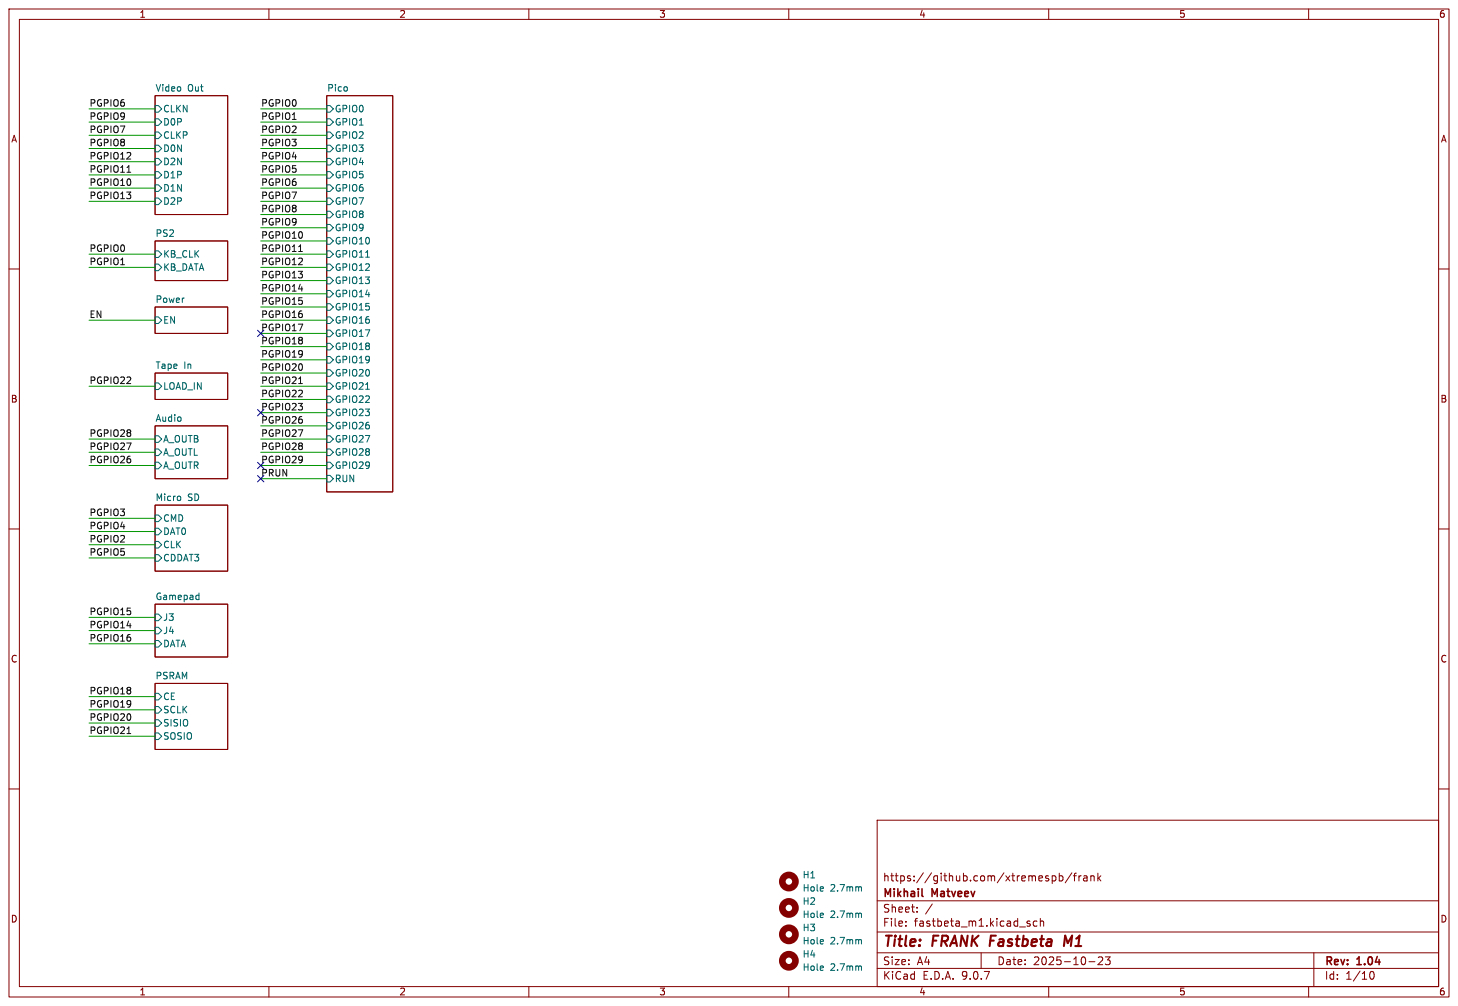
[picture p176: page 1]

https://github.com/xtremespb/frank

Id: 1/10 Title: FRANK Fastbeta M1

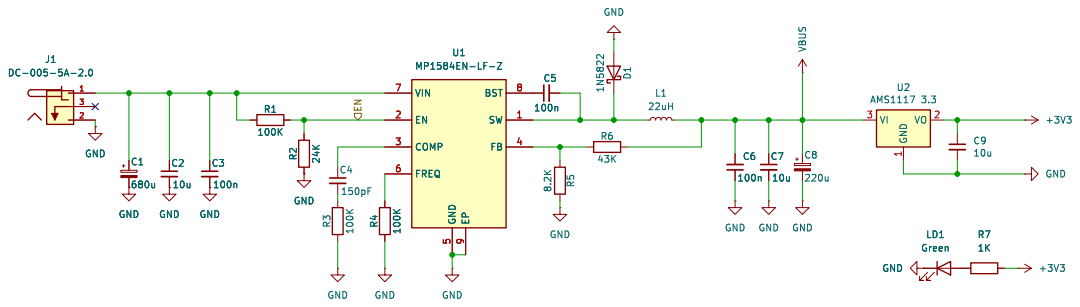
[picture p177: page 2]

9 BST 8 SW 1 FB 4 U1 MP1584EN-LF-Z R5 8.2K GND R3 100K GND

https://github.com/xtremespb/frank

Id: 3/10 Title: FRANK Fastbeta

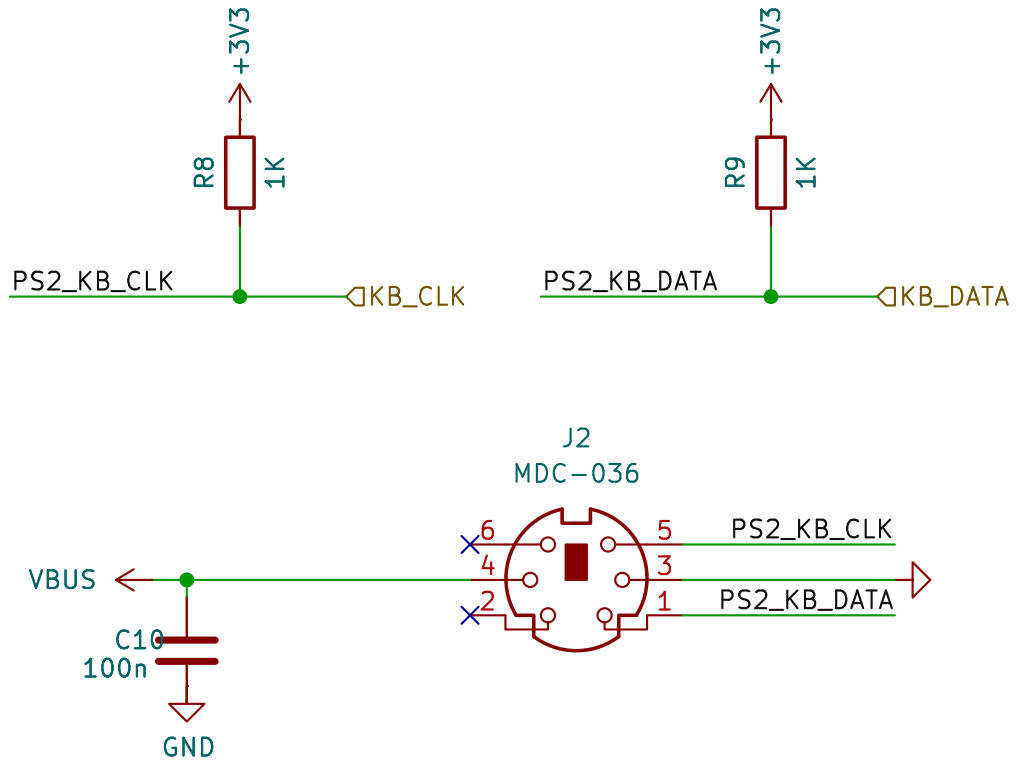
[picture p178: page 3]

https://github.com/xtremespb/frank GND

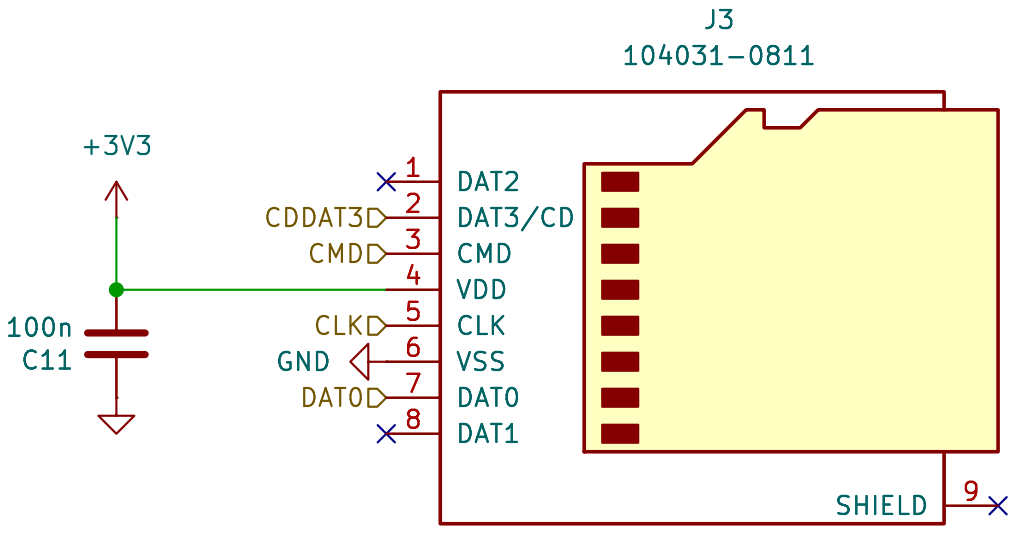
[picture p179: page 4]


https://github.com/xtremespb/frank GND
J3 DATA

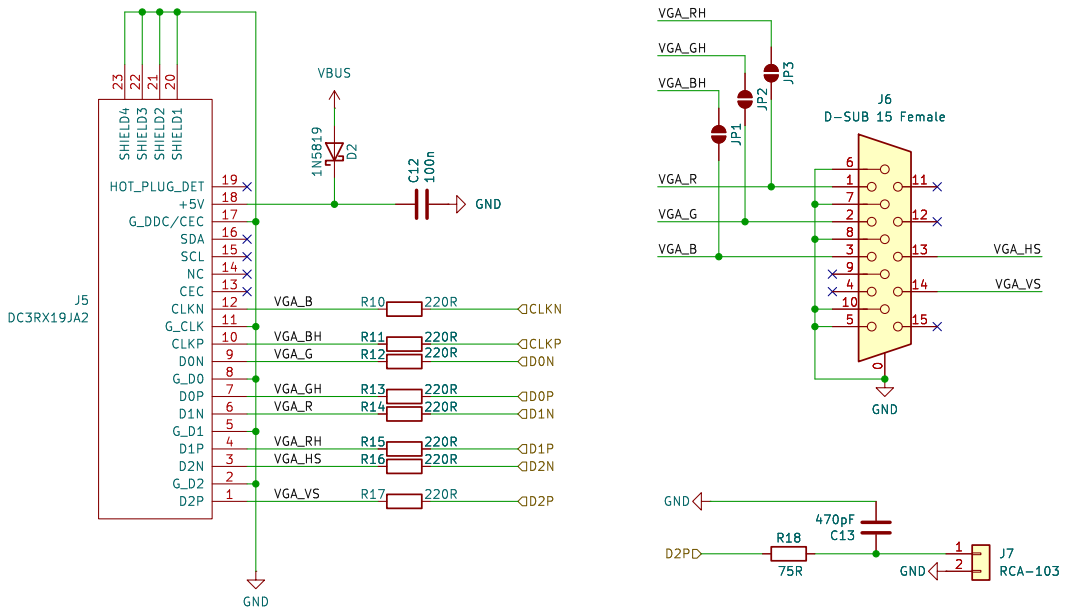
[picture p180: page 6]

Id: 10/10 Title: FRANK Fastbeta

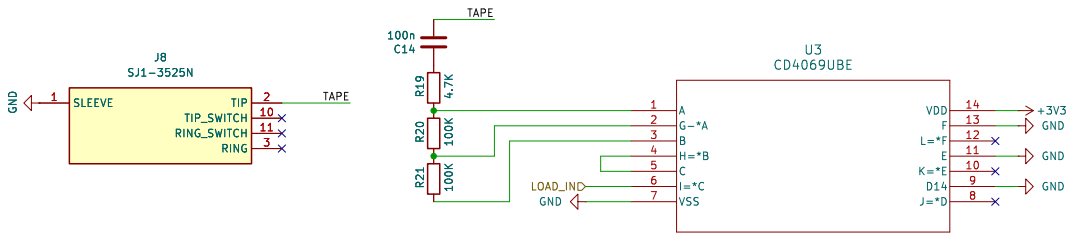
[picture p181: page 7]


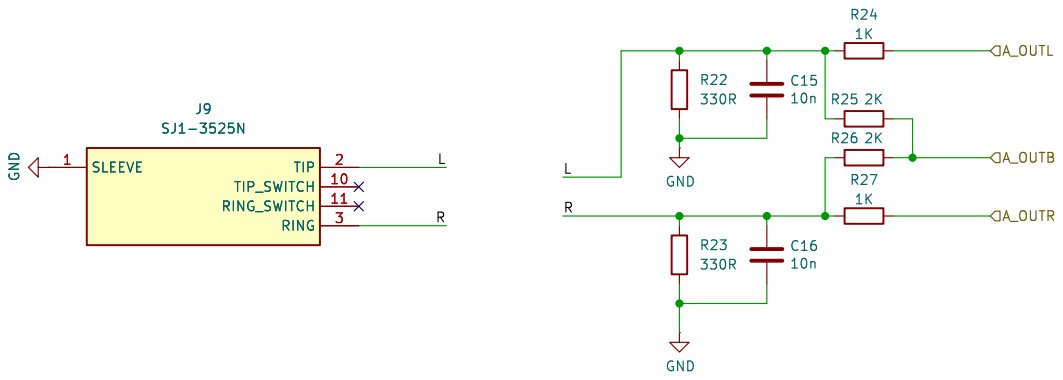
[picture p182: page 9]

https://github.com/xtremespb/frank R27

Id: 15/10 Title: FRANK Fastbeta

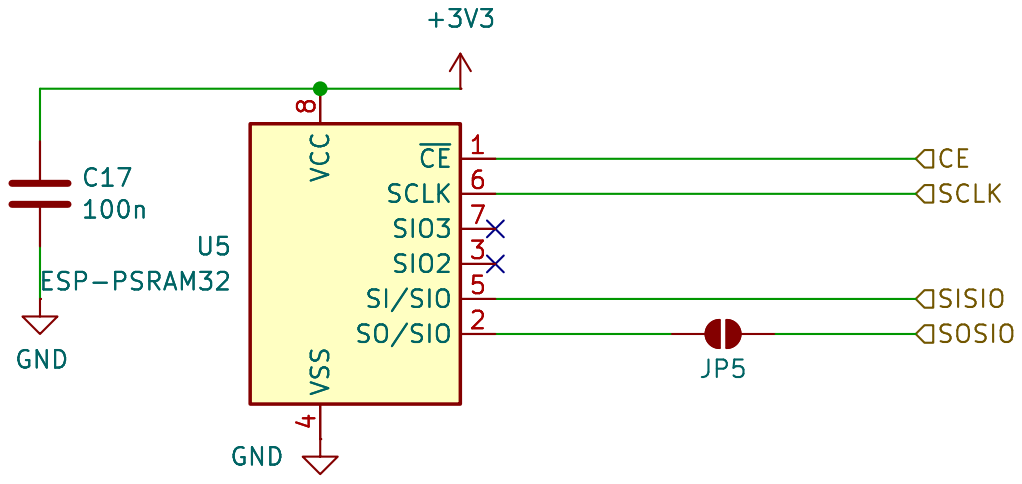
[picture p183: page 10]

4 ~{CE}1 SCLK 6 SIO3 7 SIO2 3 SI/SIO 5 SO/SIO 2 U5 ESP-PSRAM32 SISIO
100n GND

4 ~{CE}1 SCLK 6 SIO3 7 SIO2 3 SI/SIO 5 SO/SIO 2

https://github.com/xtremespb/frank
