rh1tech/frank-archive/hdmi2vga/docs/2_03/hdmi2vga.pdf

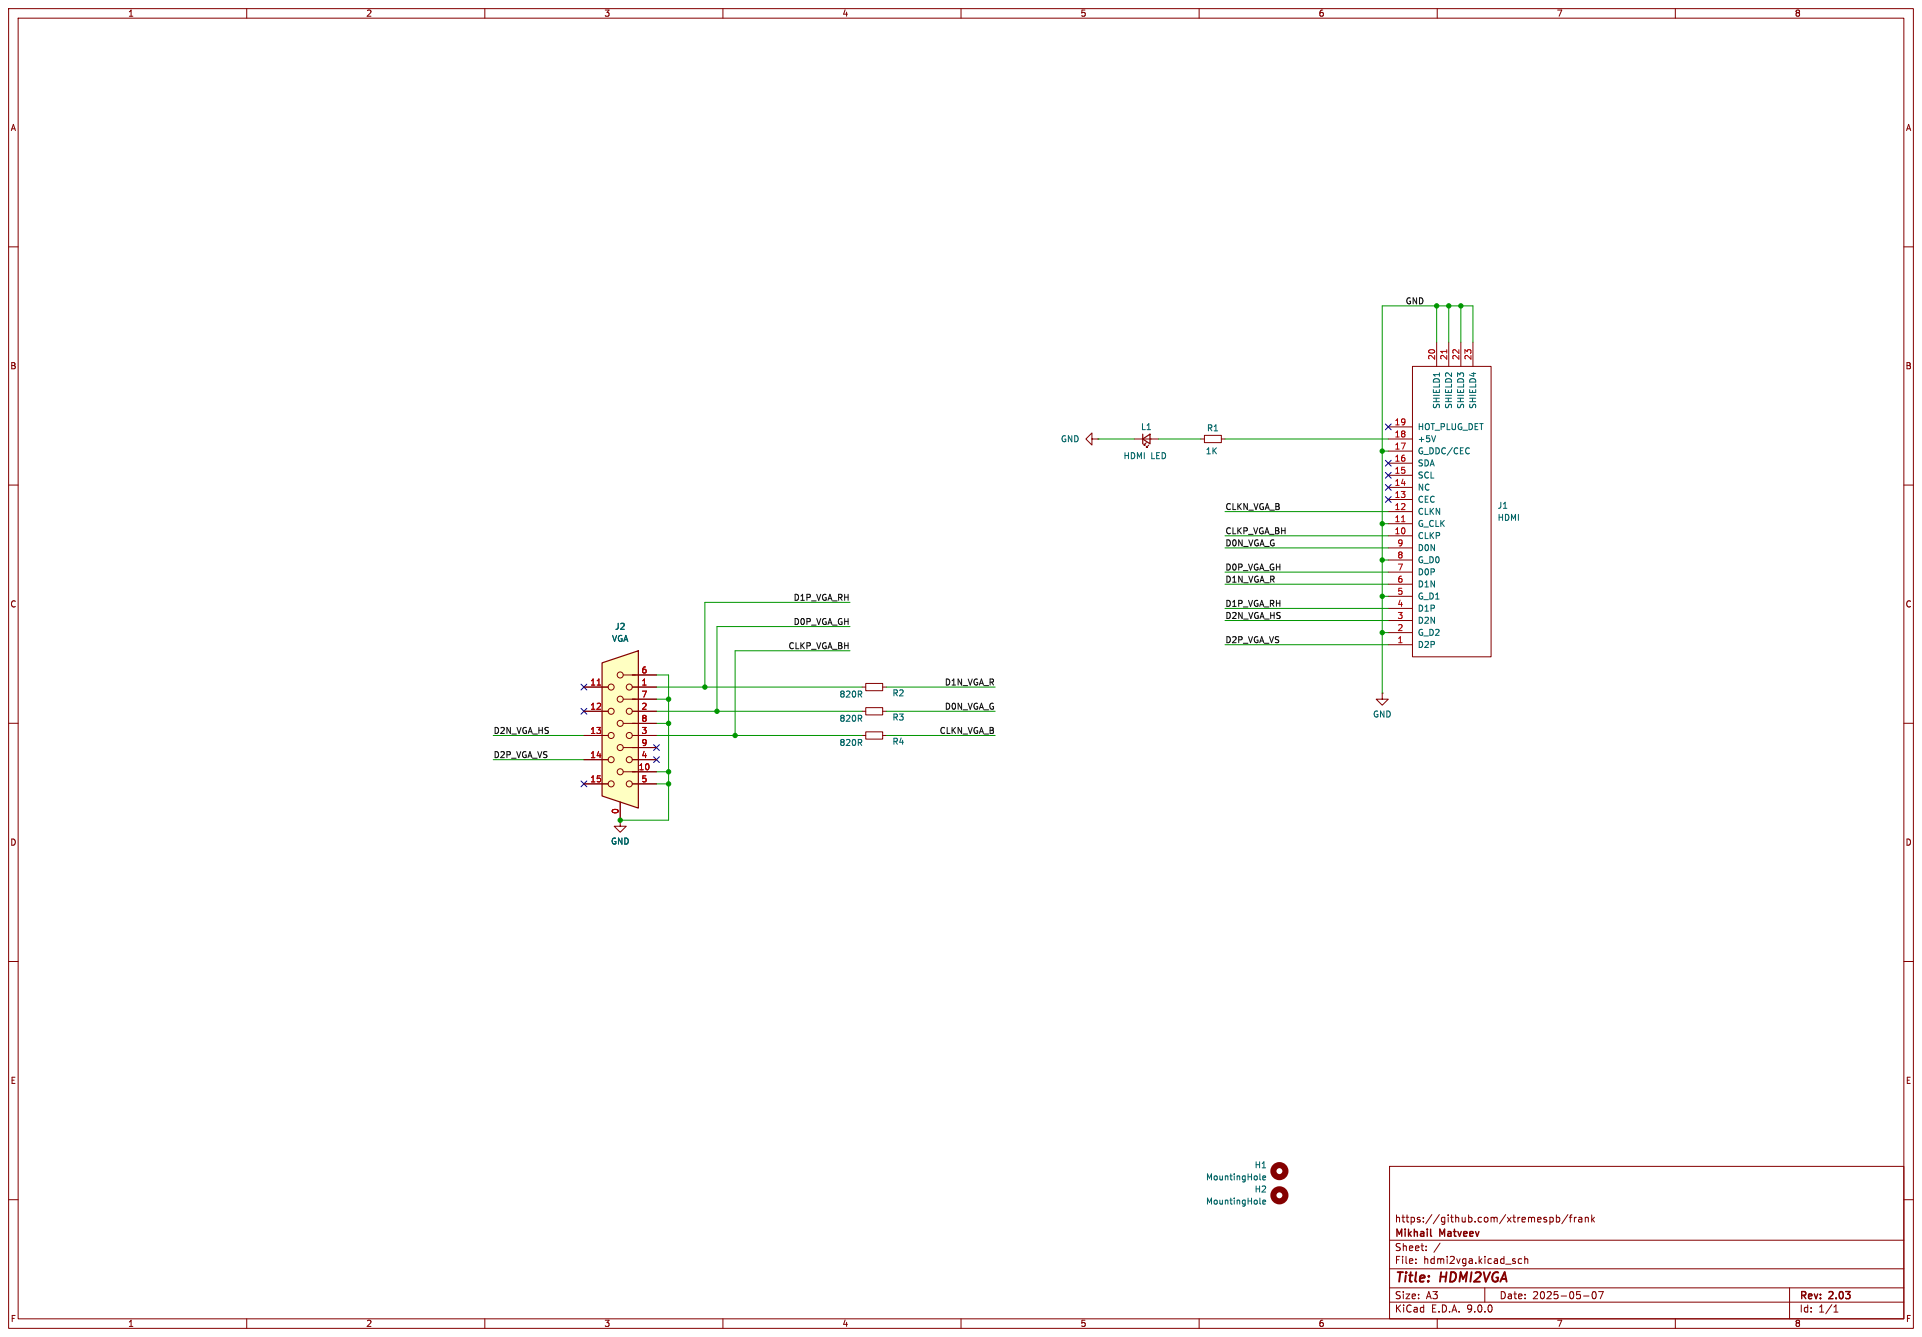
[picture p184: page 1]

https://github.com/xtremespb/frank GND
