rh1tech/frank-archive/turbofrank_m1p1/docs/1_03/turbofrank.pdf

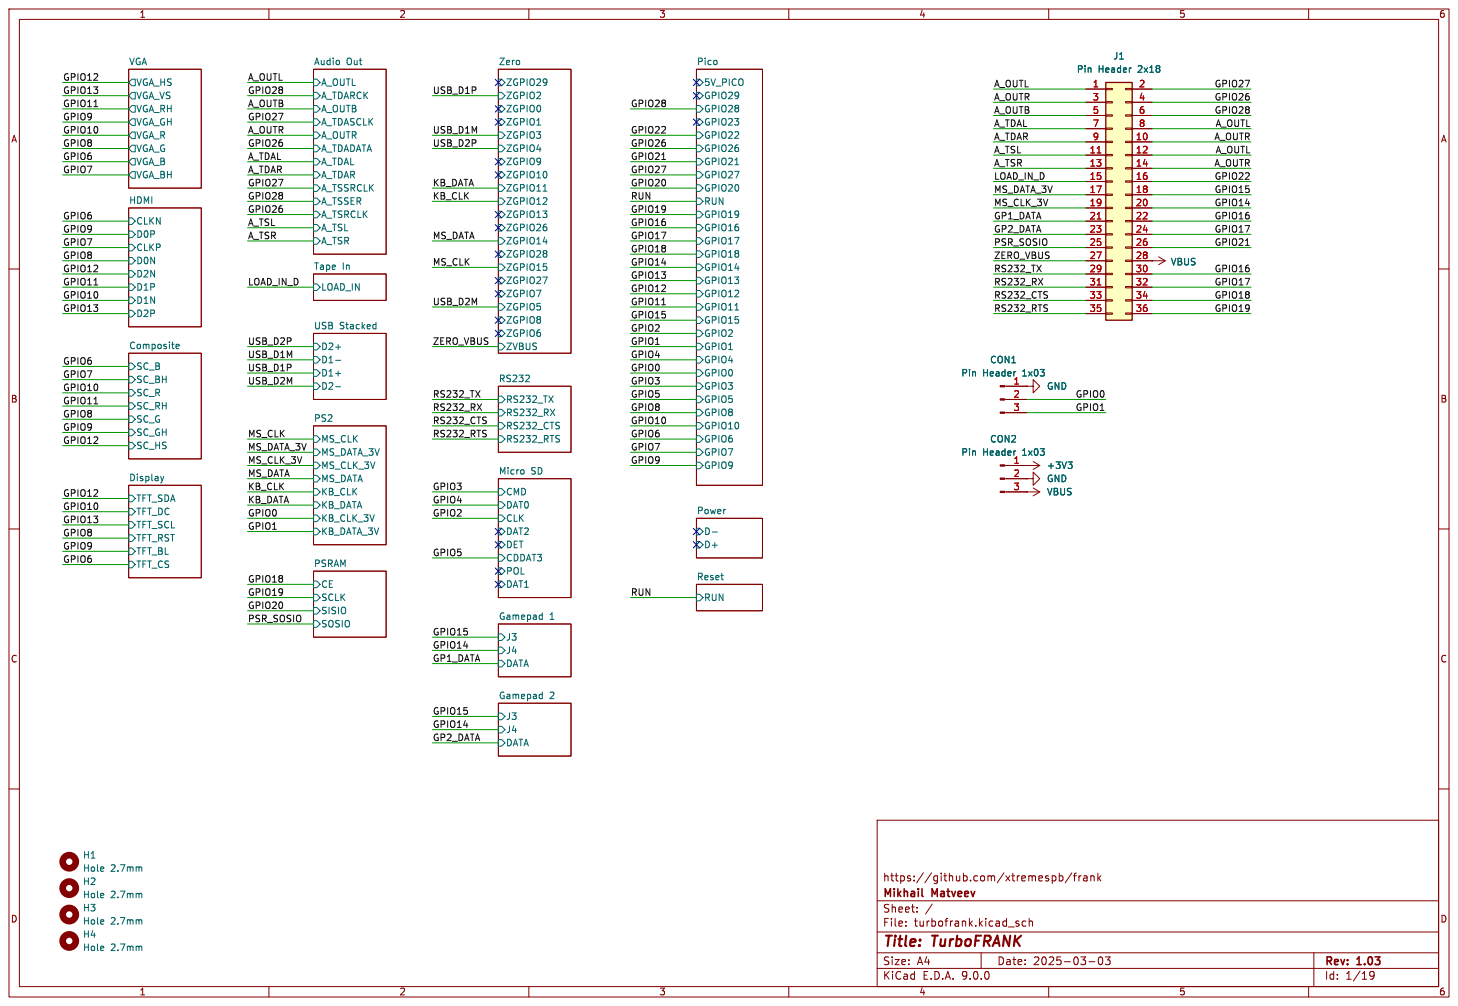
[picture p185: page 1]

J1 Pin Header 2x18 VBUS H4 Hole 2.7mm

DAT0 CLK DAT2 DET CDDAT3 POL DAT1 Micro SD

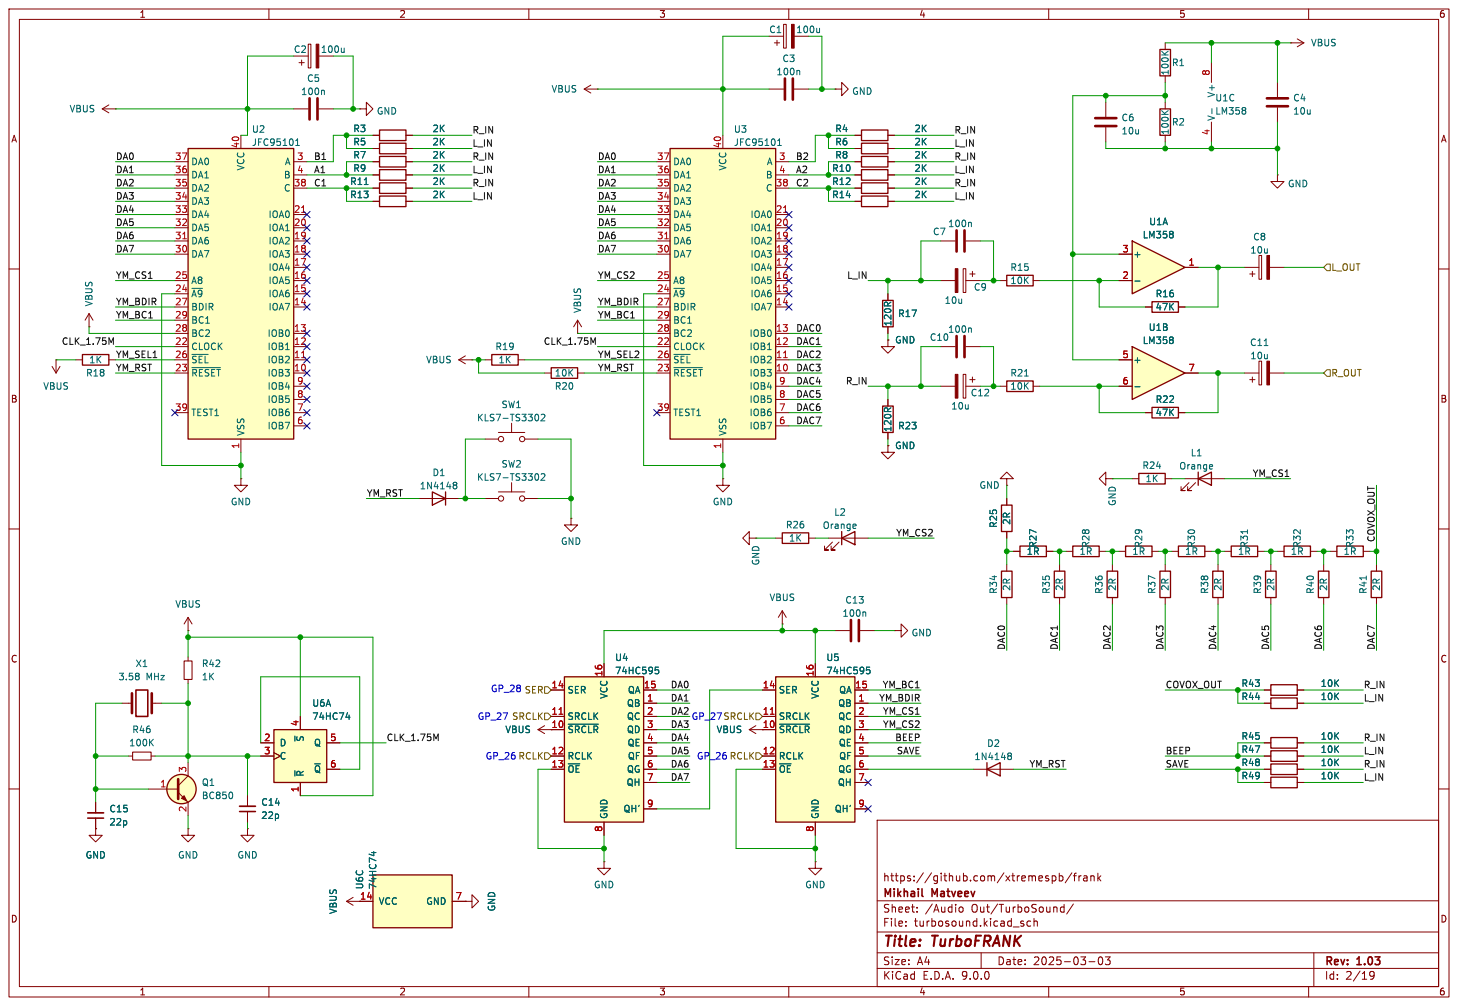
[picture p186: page 2]

SER

8 QA 15 QB 1 QC 2 QD 3 QE 4 QF 5 QG 6 QH 7 QH' 9 VBUS R48 10K R44 10K R45 10K R49 10K R47 10K R43 10K

https://github.com/xtremespb/frank

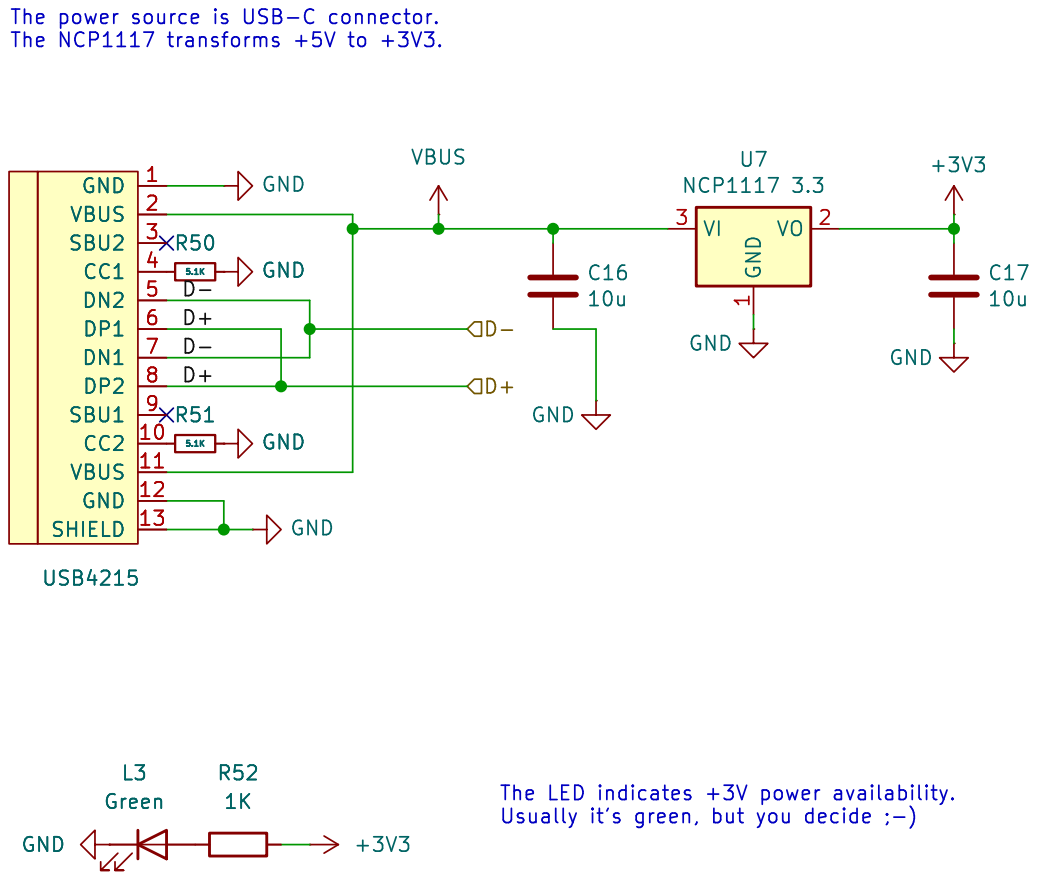
[picture p187: page 3]

1 VO 2 U7 GND NCP1117 3.3 1 VBUS 2 SBU2 3 CC1 4 DN2 5 DP1 6 DN1 7 DP2 8 SBU1 9 CC2 10 VBUS 11 GND 12 SHIELD 13 USB4215 R51

Usually it's green, but you decide ;-) GND GND

https://github.com/xtremespb/frank

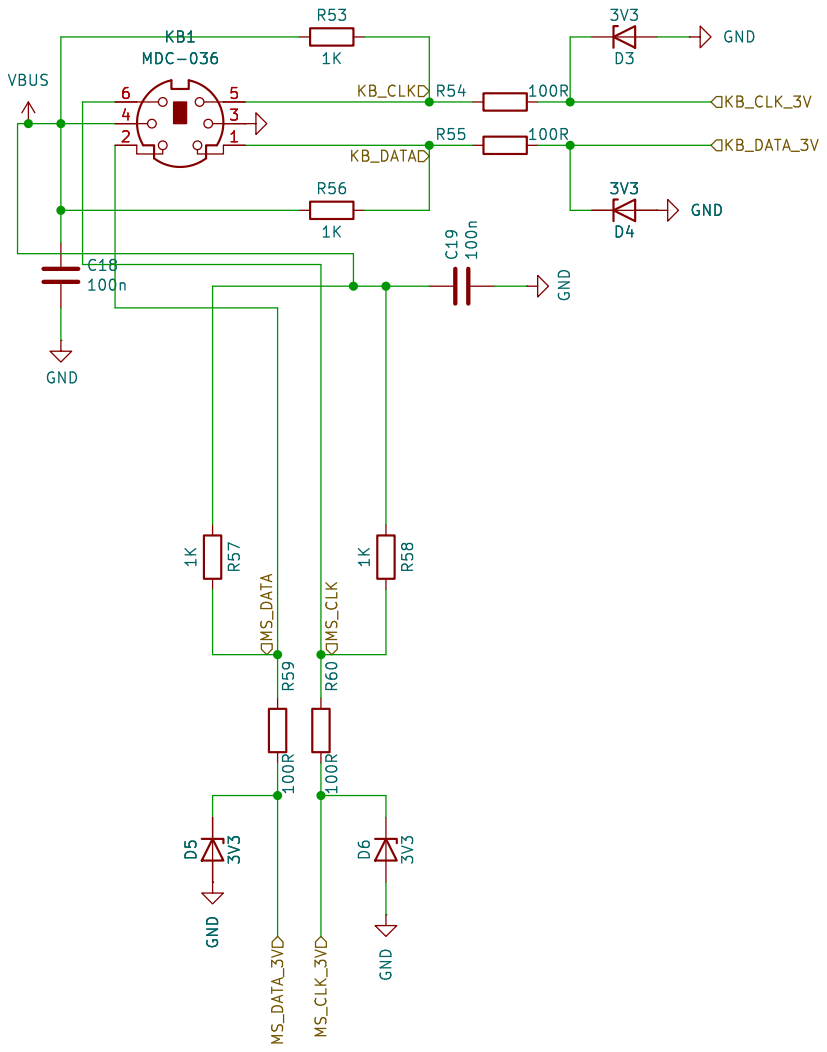
[picture p188: page 4]

https://github.com/xtremespb/frank

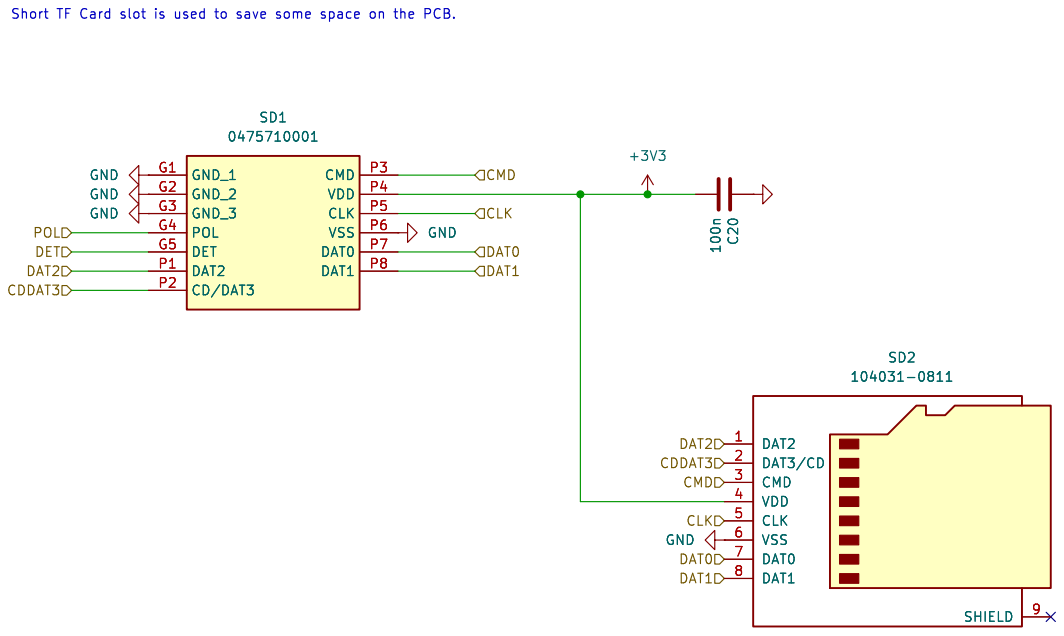
[picture p189: page 5]

https://github.com/xtremespb/frank

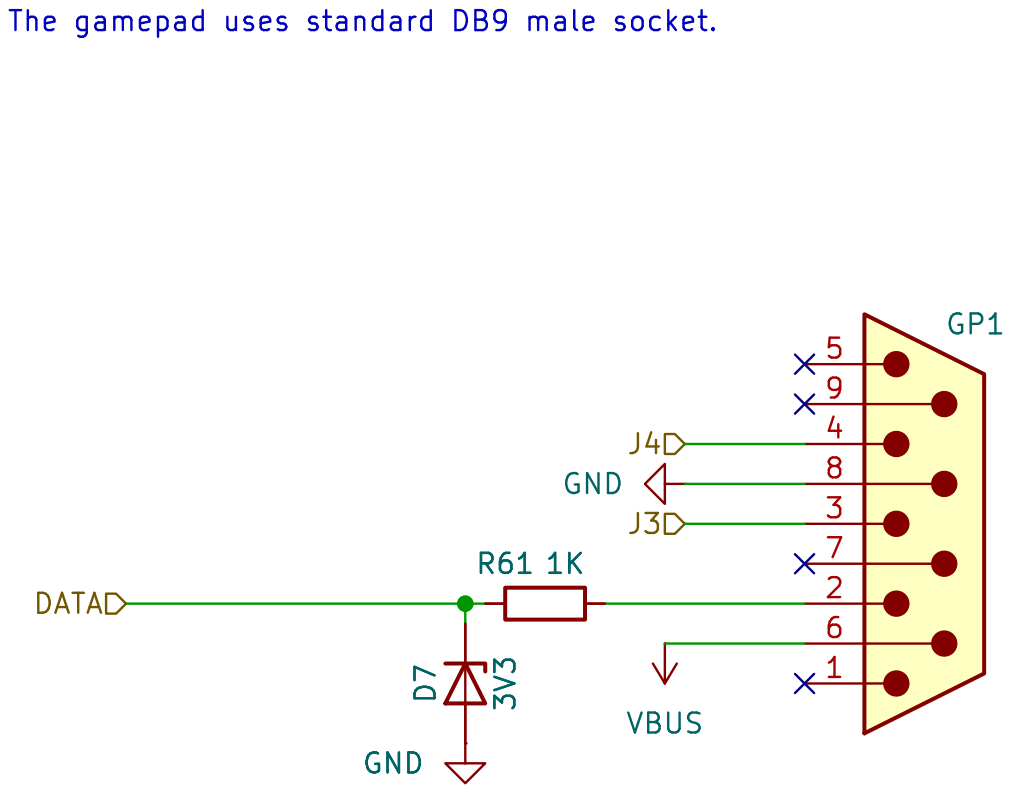
[picture p190: page 6]

https://github.com/xtremespb/frank

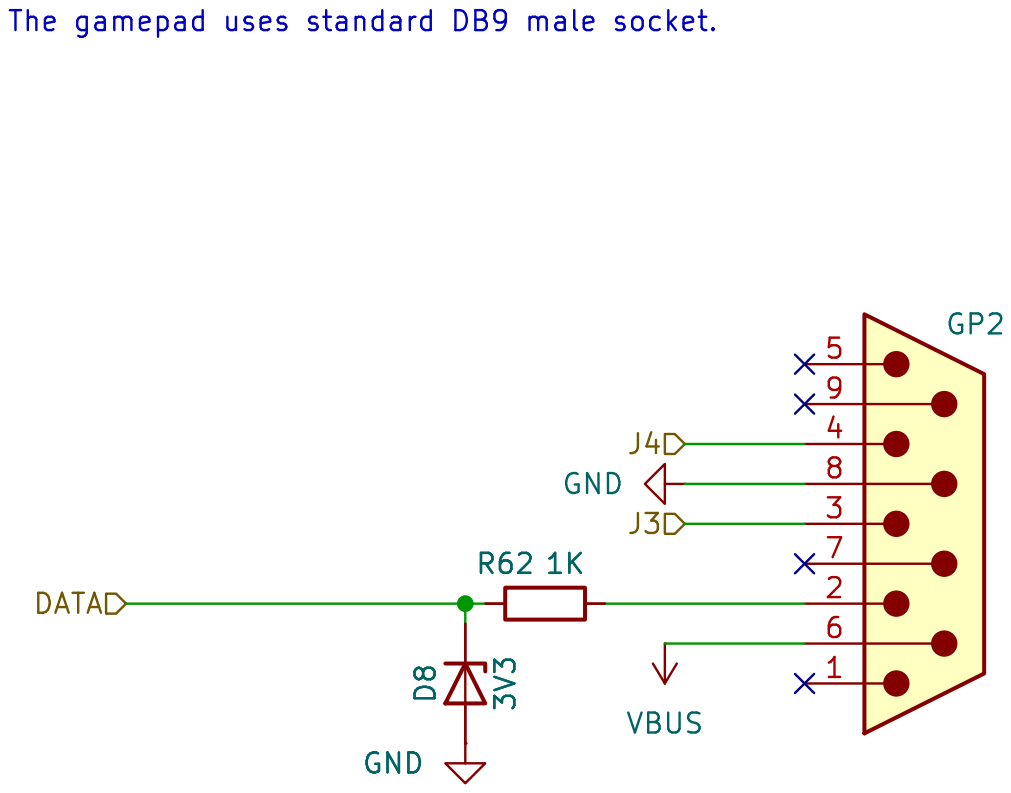
[picture p191: page 7]

https://github.com/xtremespb/frank

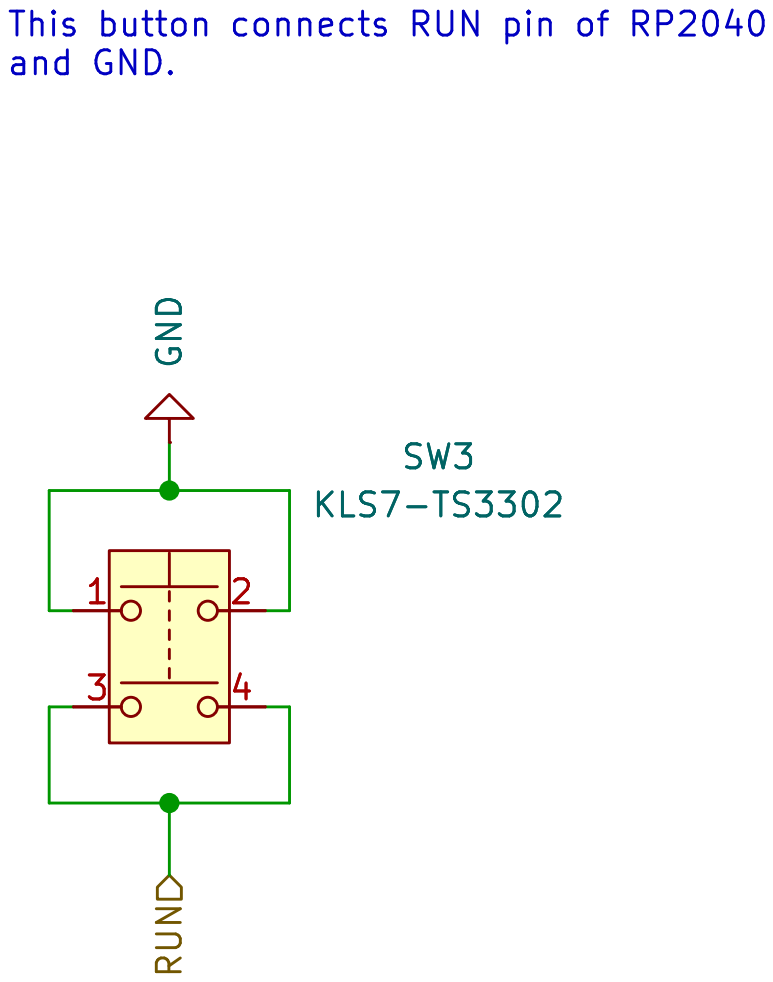
[picture p192: page 8]

https://github.com/xtremespb/frank GND

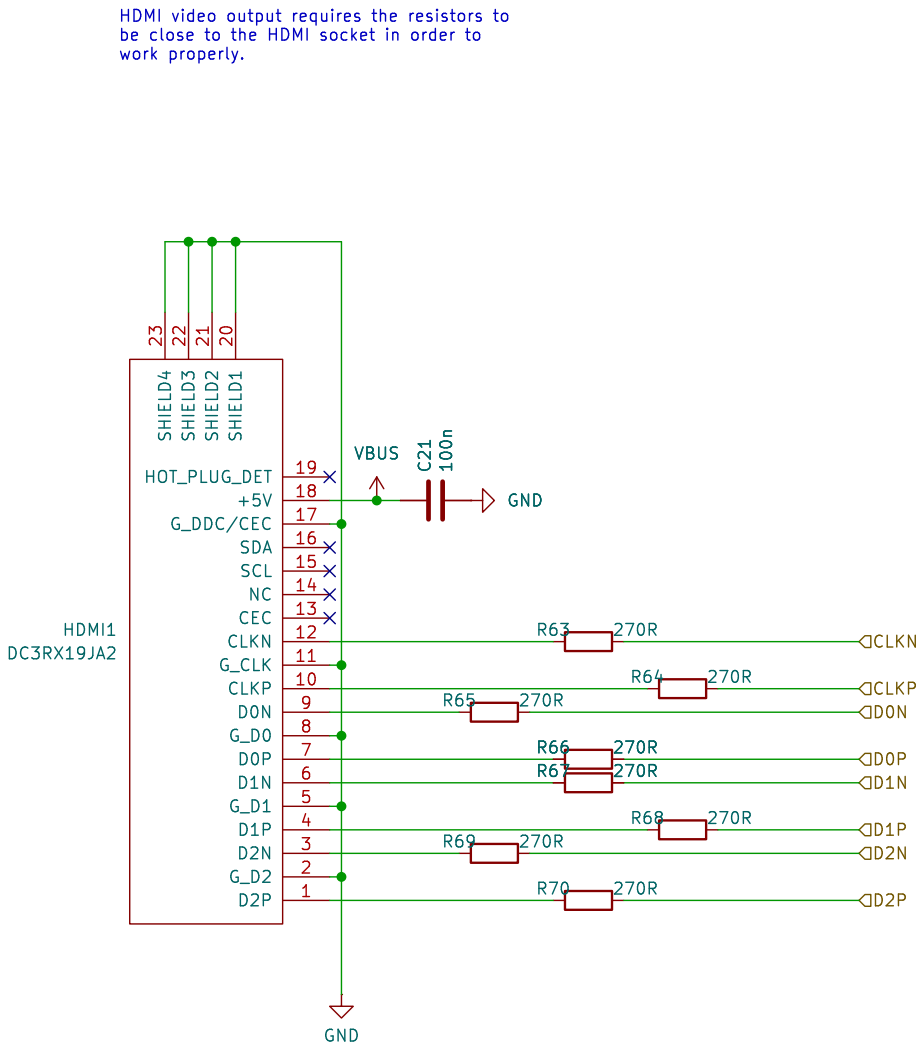
[picture p193: page 9]

https://github.com/xtremespb/frank

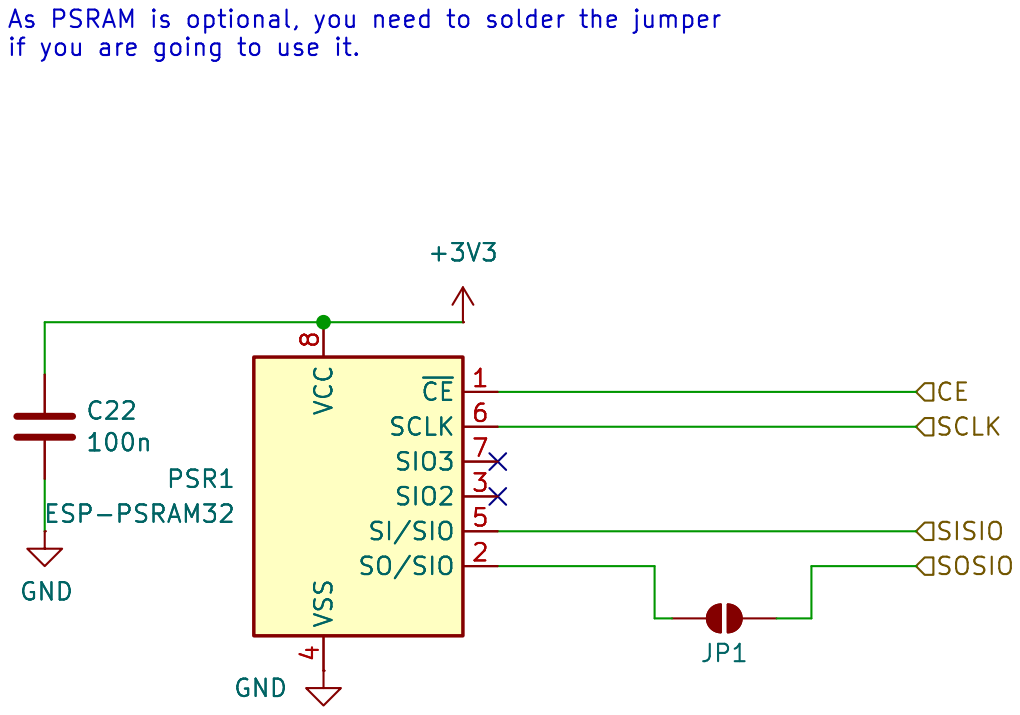
[picture p194: page 10]

if you are going to use it. C22

4 ~{CE}1 SCLK 6 SIO3 7 SIO2 3 SI/SIO 5 SO/SIO 2 +3V3

4 ~{CE}1 SCLK 6 SIO3 7 SIO2 3 SI/SIO 5 SO/SIO 2 PSR1 ESP-PSRAM32

https://github.com/xtremespb/frank

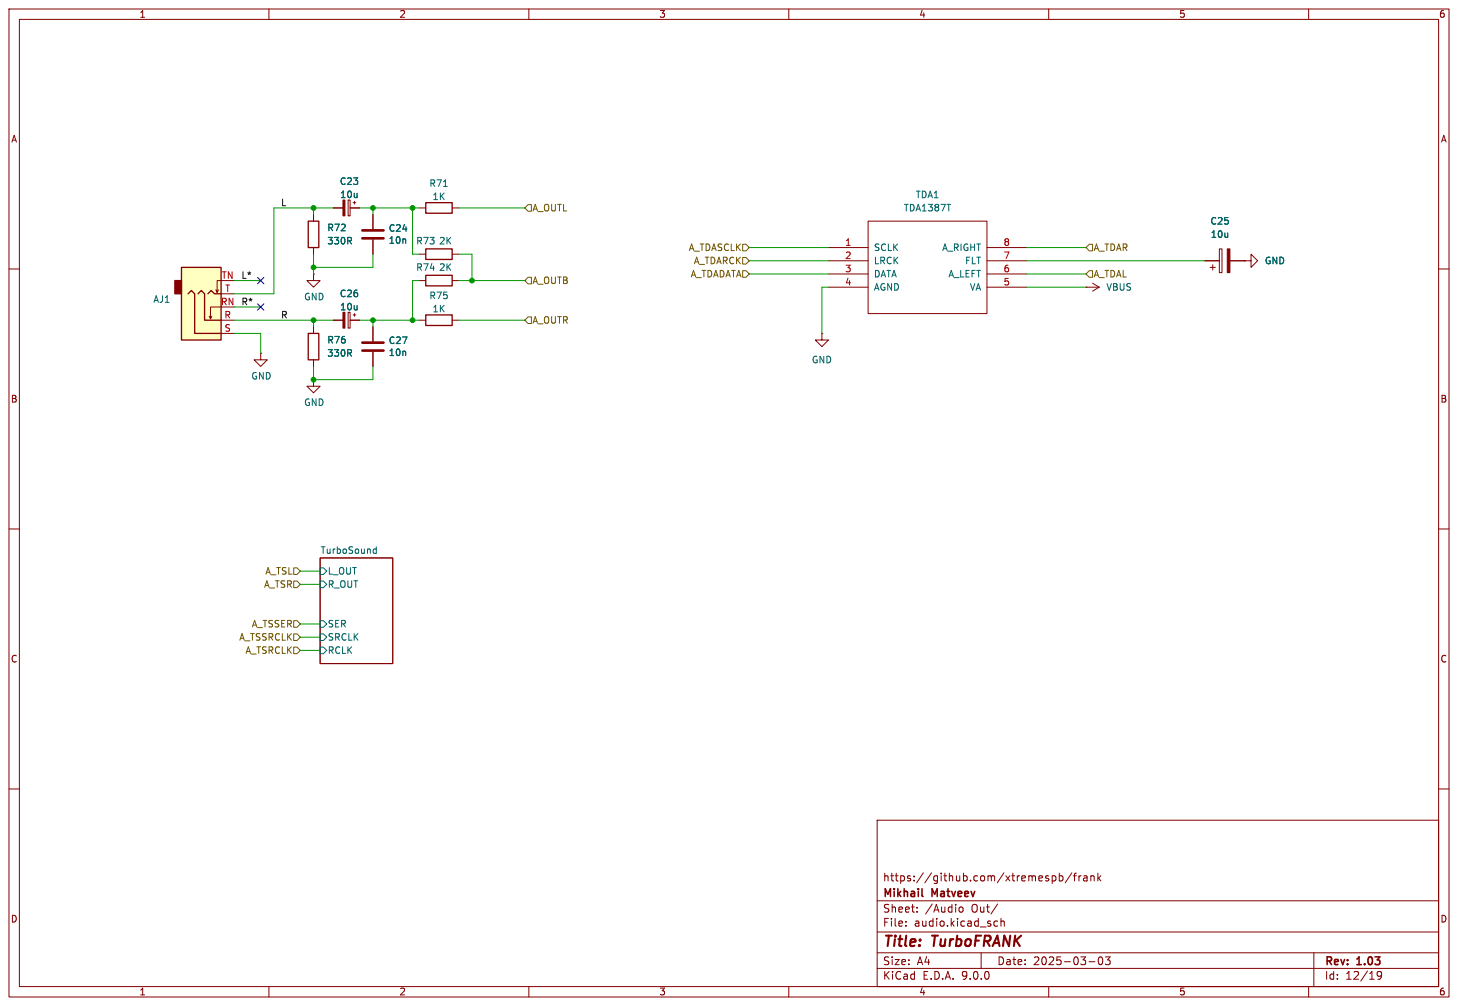
[picture p195: page 11]

https://github.com/xtremespb/frank

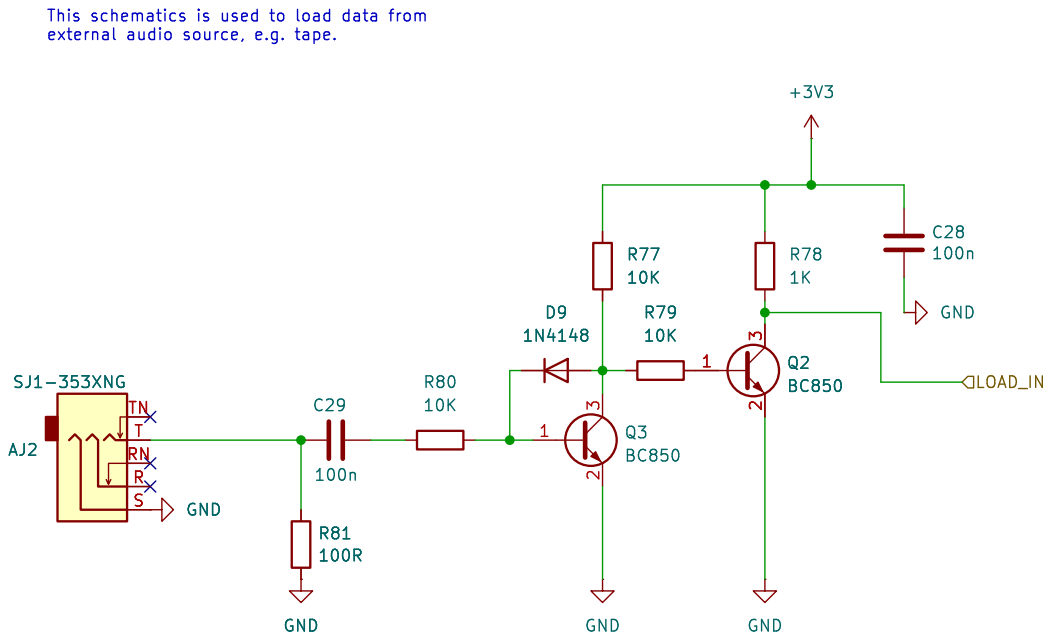
[picture p196: page 12]

https://github.com/xtremespb/frank

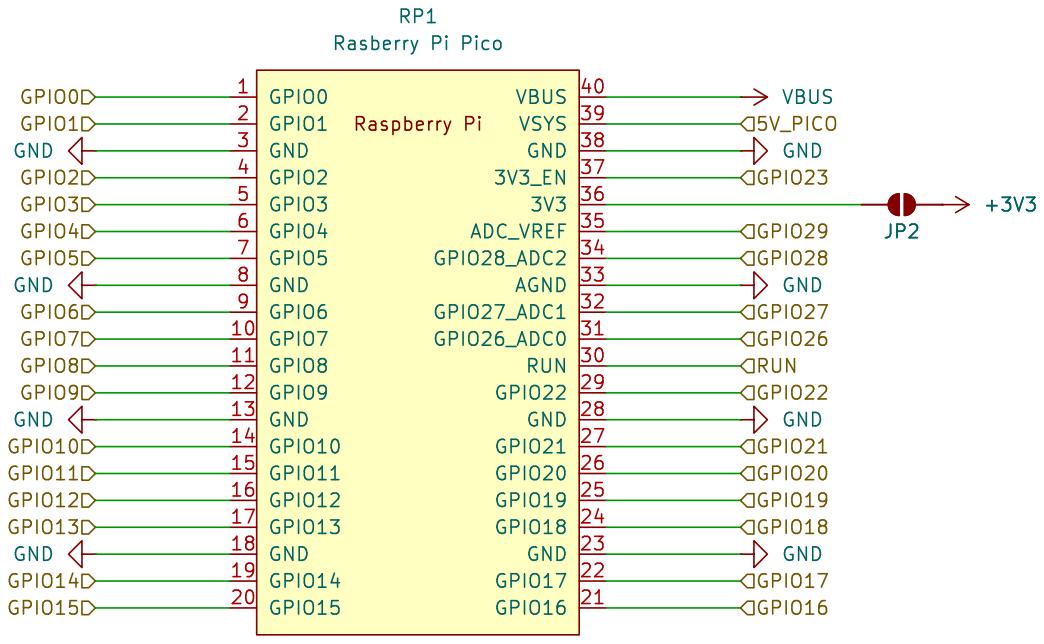
[picture p197: page 13]

https://github.com/xtremespb/frank

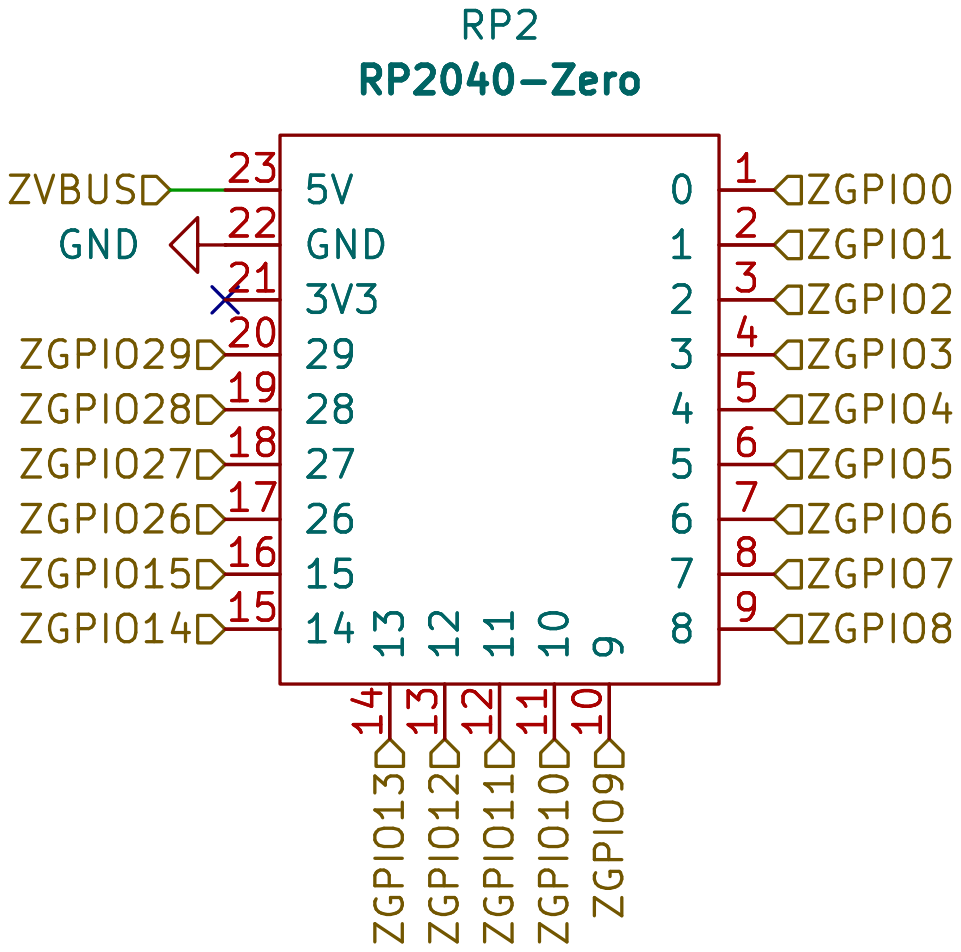
[picture p198: page 14]

https://github.com/xtremespb/frank

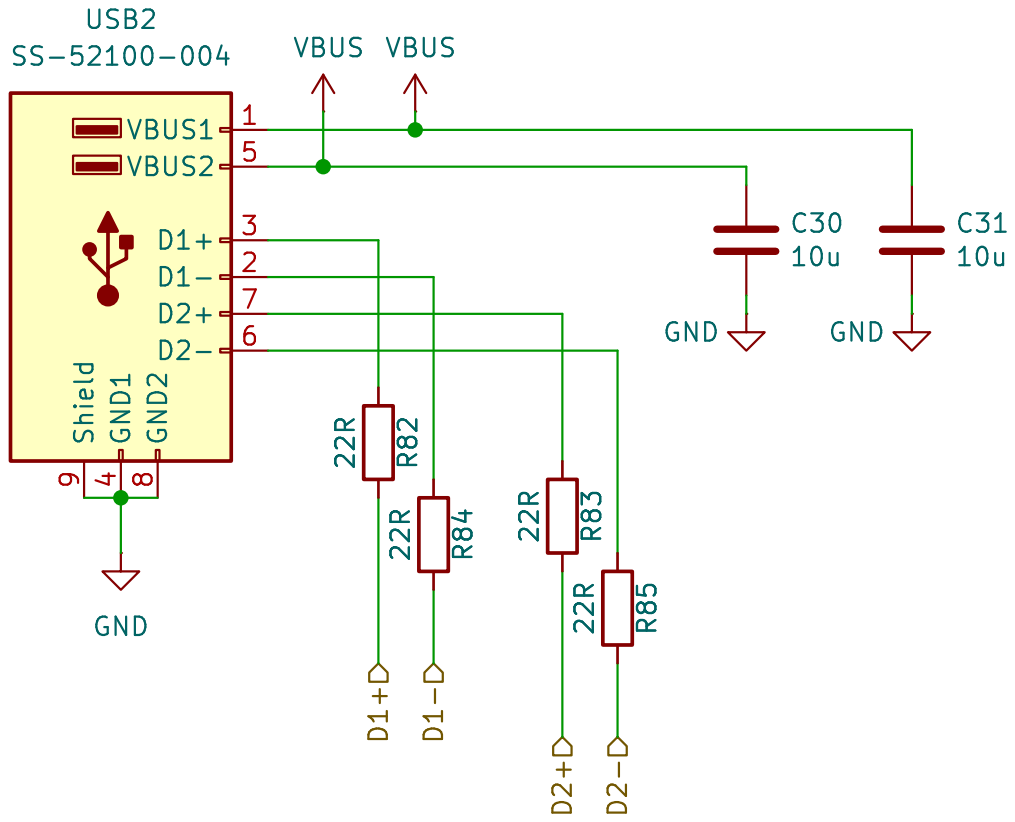
[picture p199: page 15]

https://github.com/xtremespb/frank

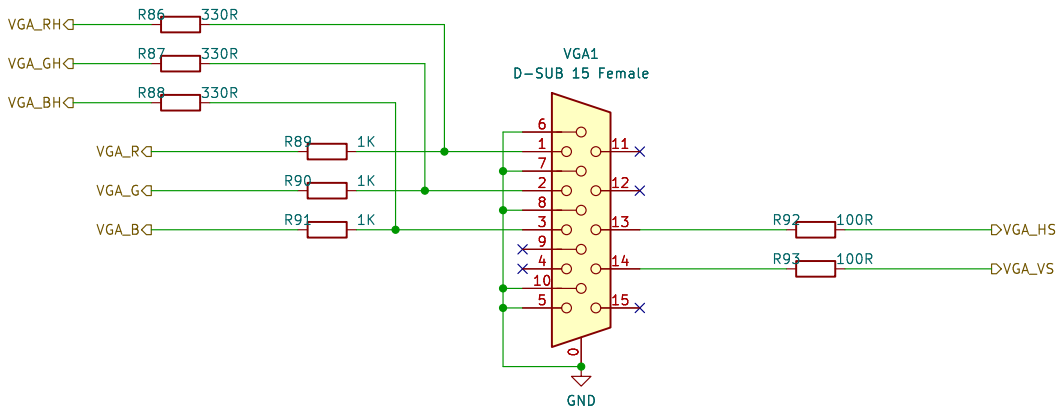
[picture p200: page 16]

https://github.com/xtremespb/frank

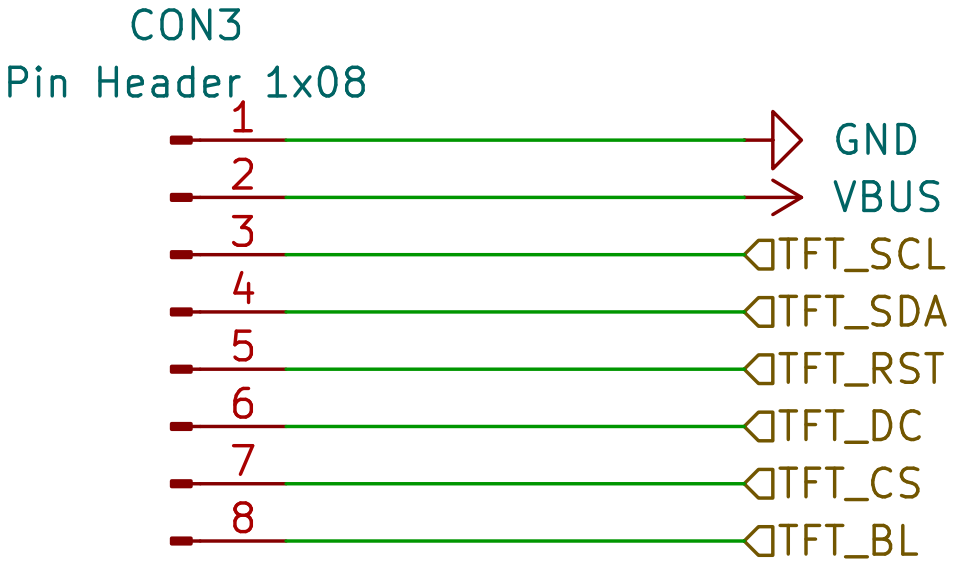
[picture p201: page 17]

https://github.com/xtremespb/frank

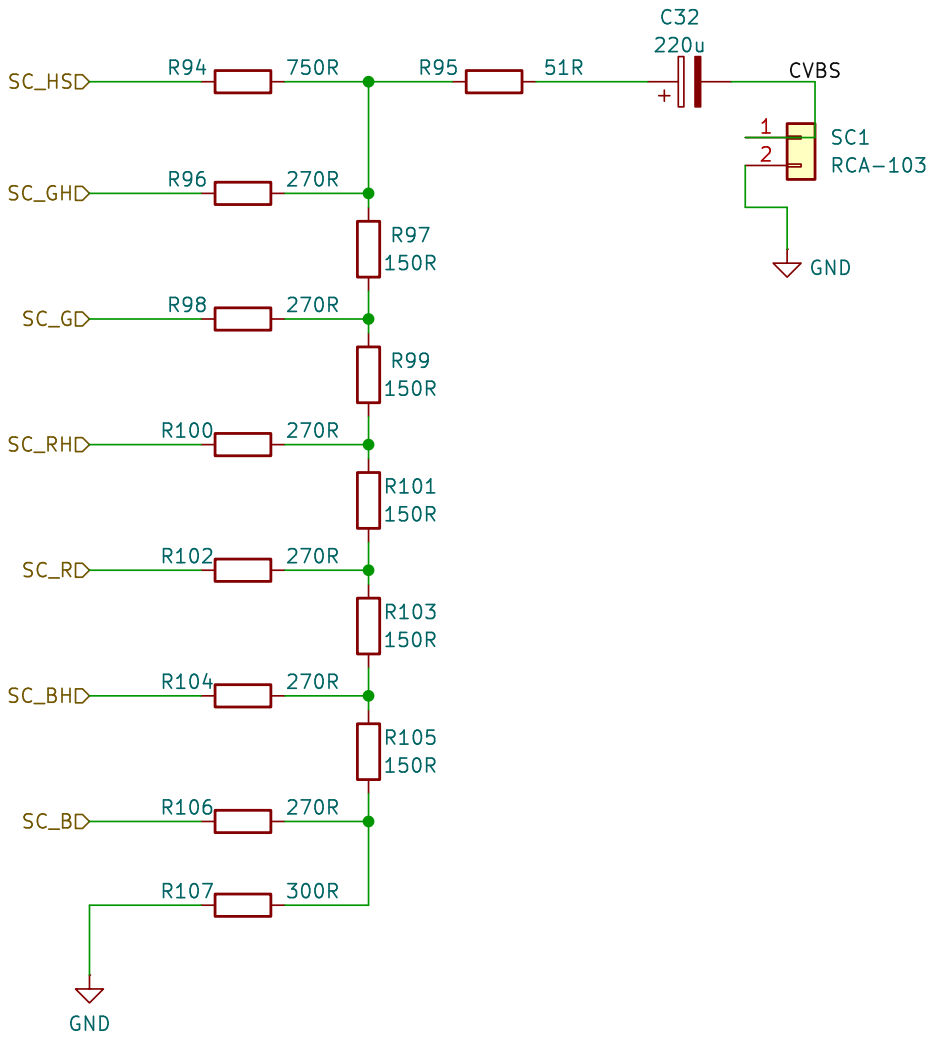
[picture p202: page 18]

https://github.com/xtremespb/frank

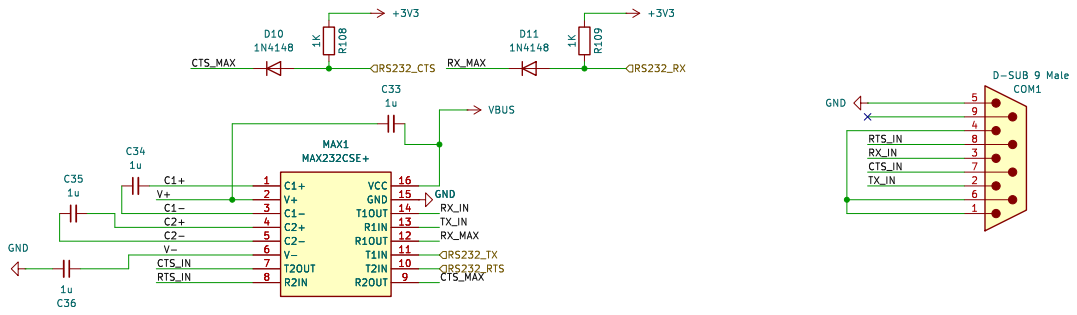
[picture p203: page 19]

https://github.com/xtremespb/frank
