rh1tech/frank-archive/turbofrank_m1p1/docs/1_05/turbofrank.pdf

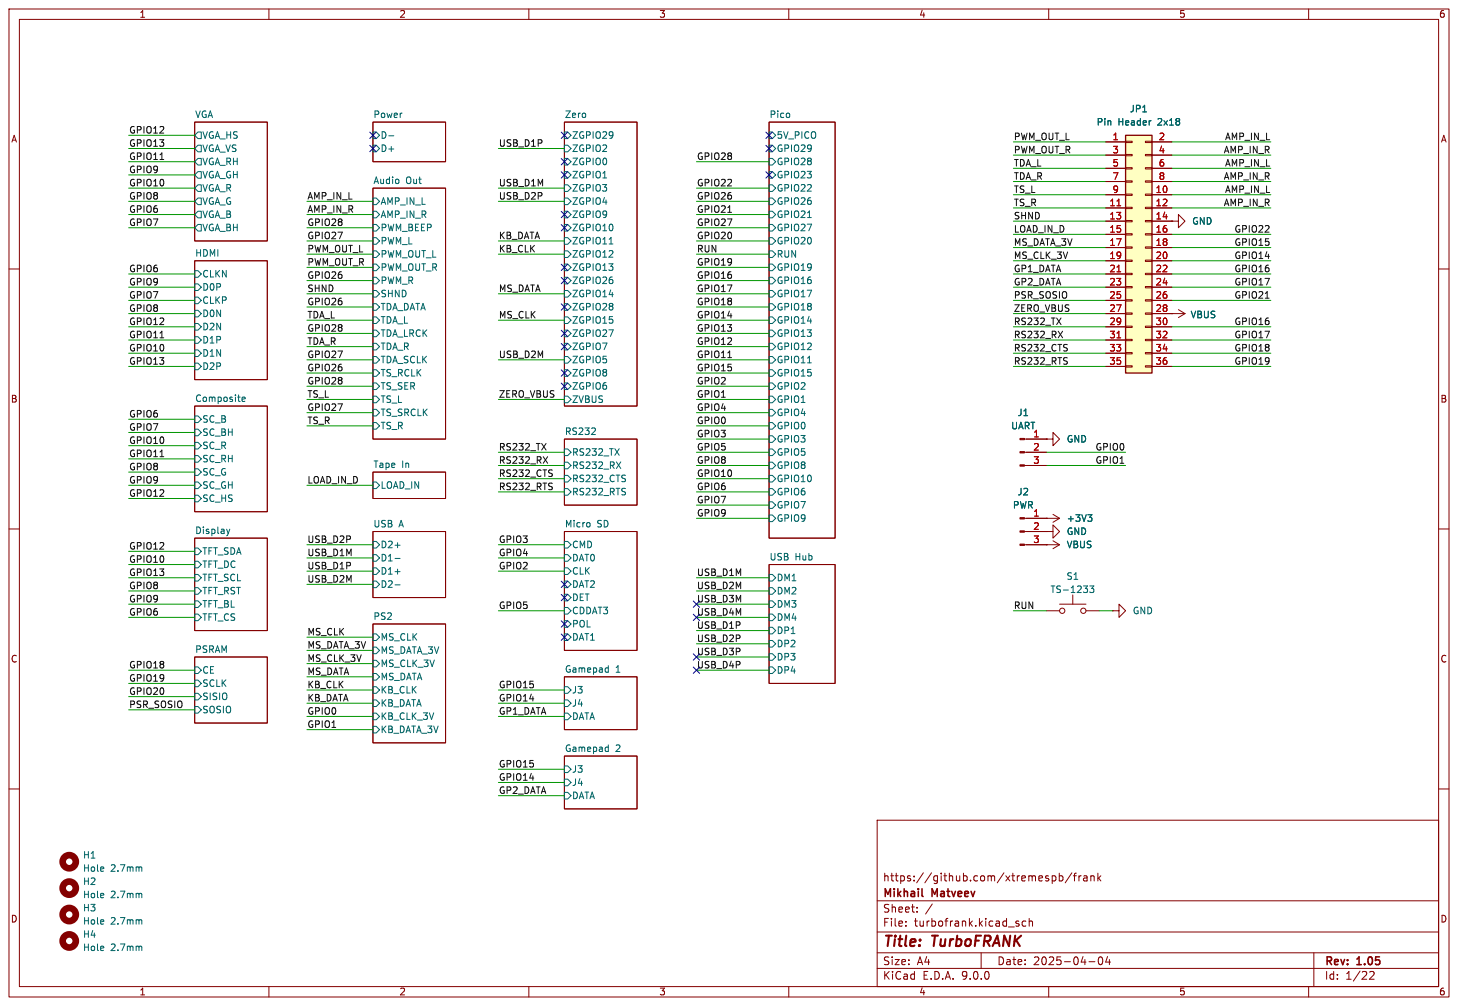
[picture p204: page 1]

Tape In D2+ D1- D1+ D2- USB A D- D+ Power
USB_D2P GP2_DATA GP1_DATA USB_D2M

DAT0 CLK DAT2 DET CDDAT3 POL DAT1 Micro SD

https://github.com/xtremespb/frank

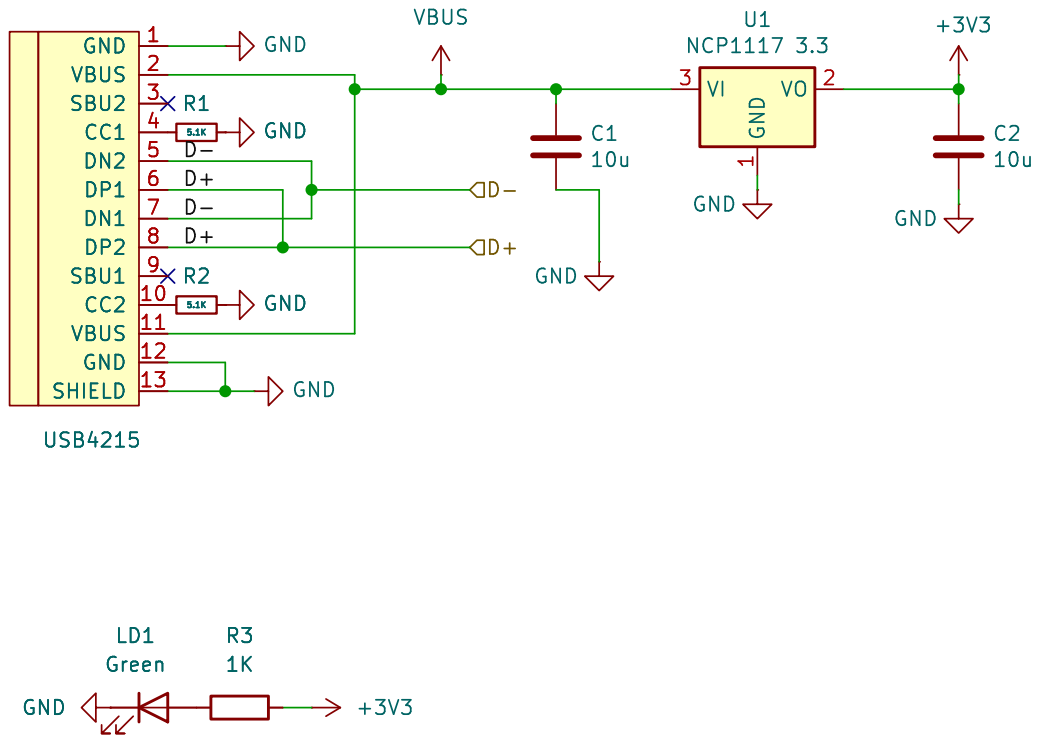
[picture p205: page 2]

https://github.com/xtremespb/frank

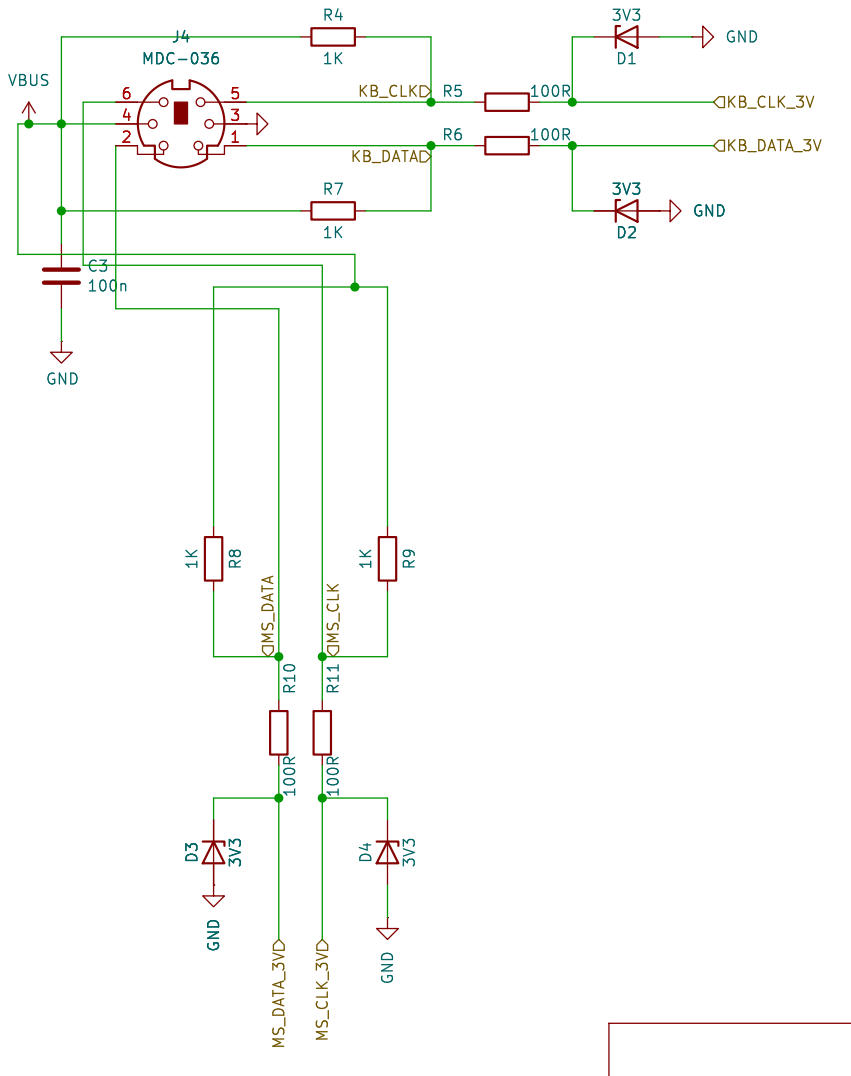
[picture p206: page 3]

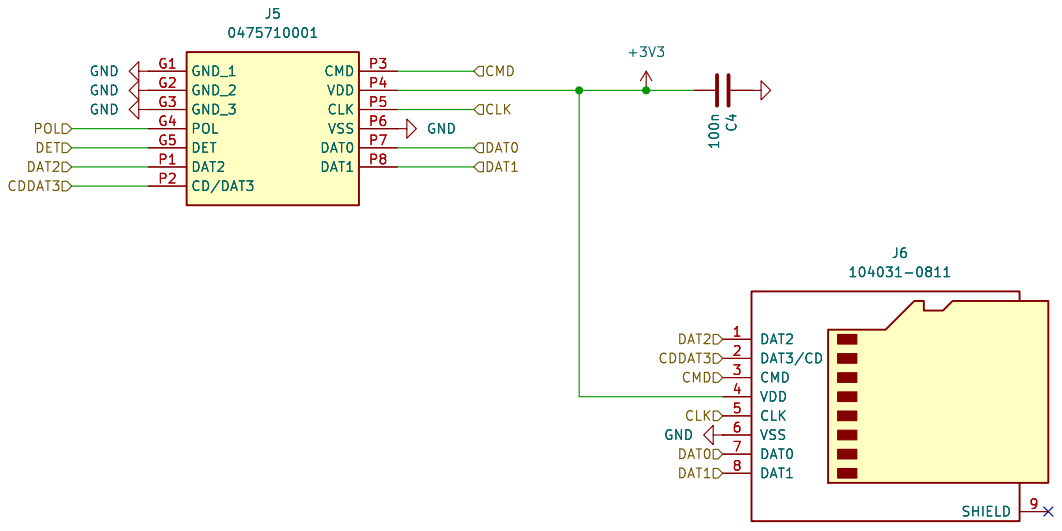
[picture p207: page 4]

https://github.com/xtremespb/frank

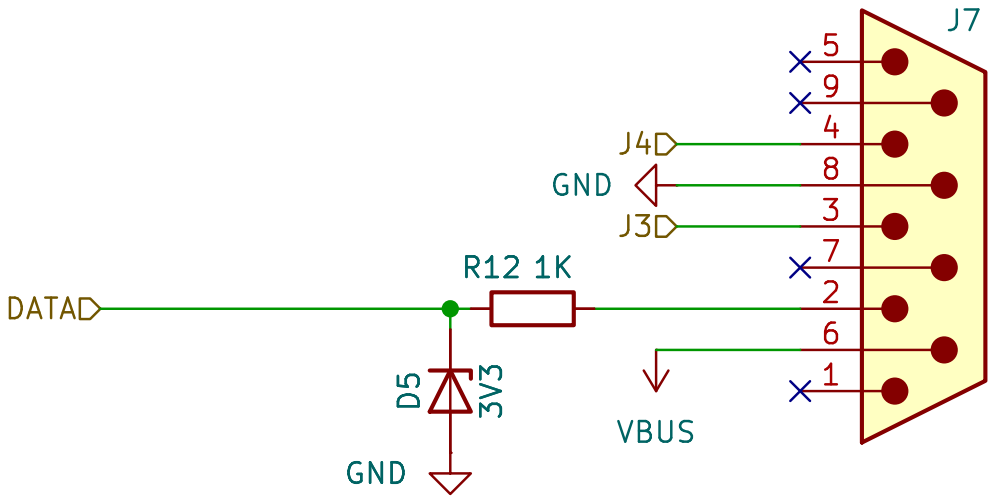
[picture p208: page 5]

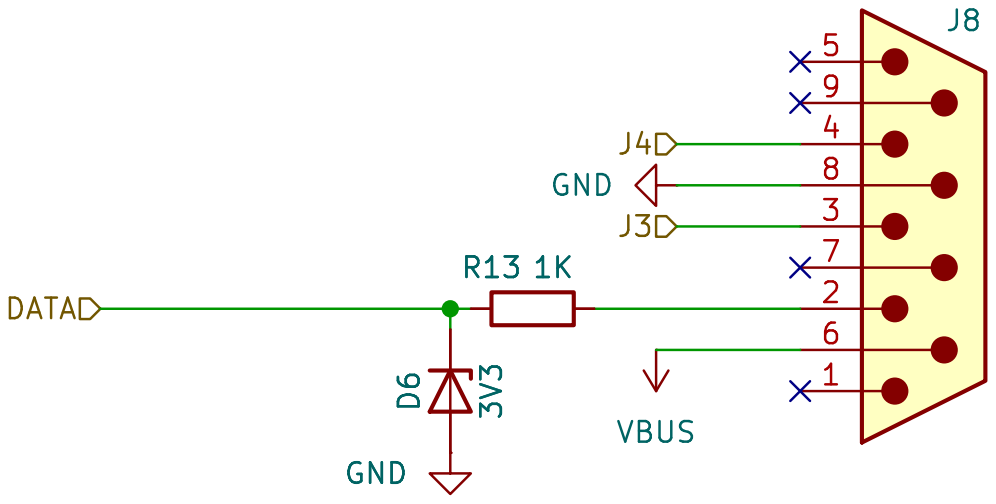
[picture p209: page 6]

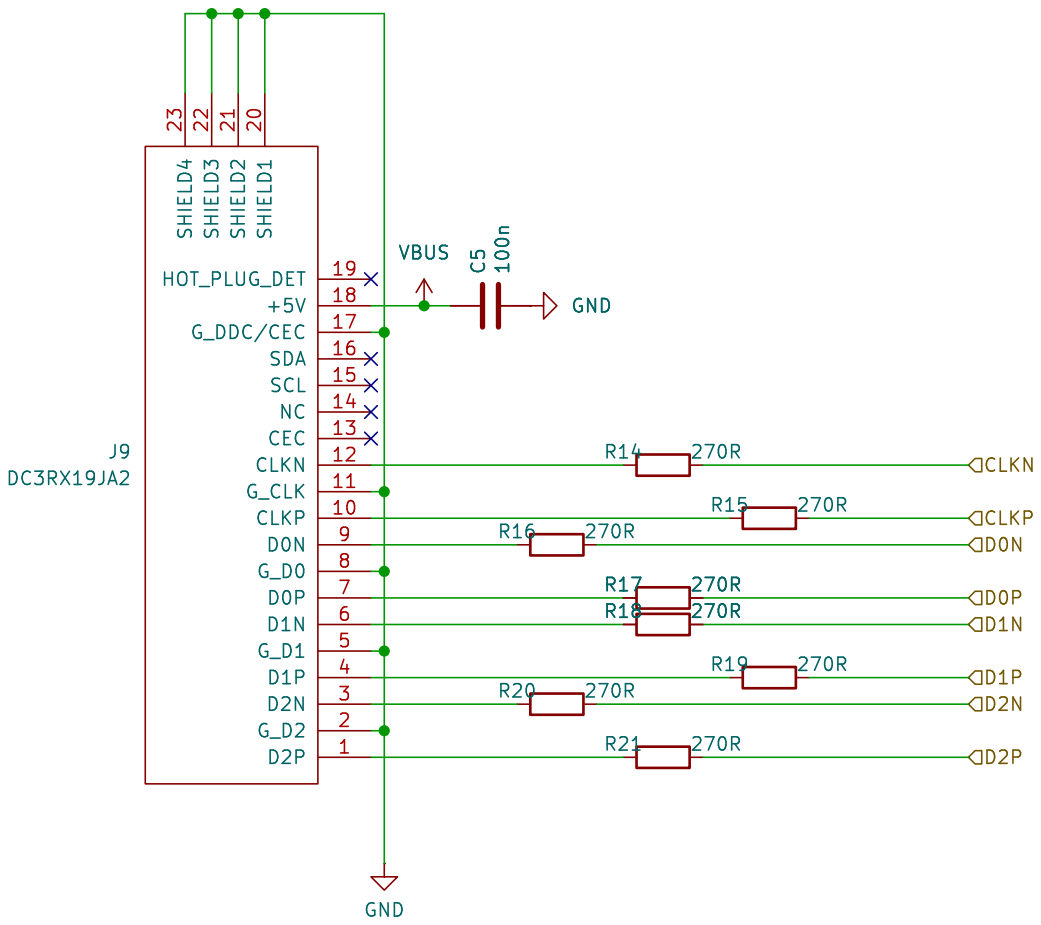
[picture p210: page 7]

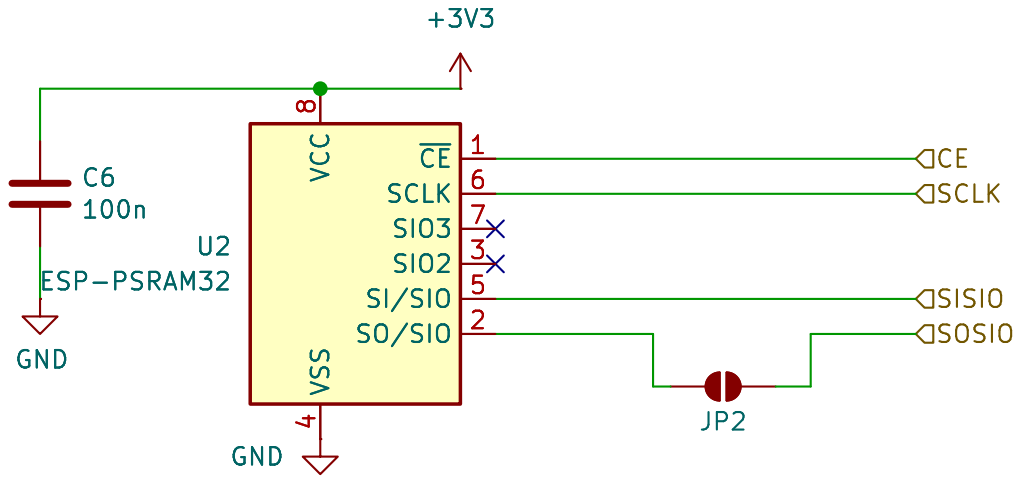
[picture p211: page 8]

4 ~{CE}1 SCLK 6 SIO3 7 SIO2 3 SI/SIO 5 SO/SIO 2 U2 ESP-PSRAM32 C6

4 ~{CE}1 SCLK 6 SIO3 7 SIO2 3 SI/SIO 5 SO/SIO 2 GND

https://github.com/xtremespb/frank

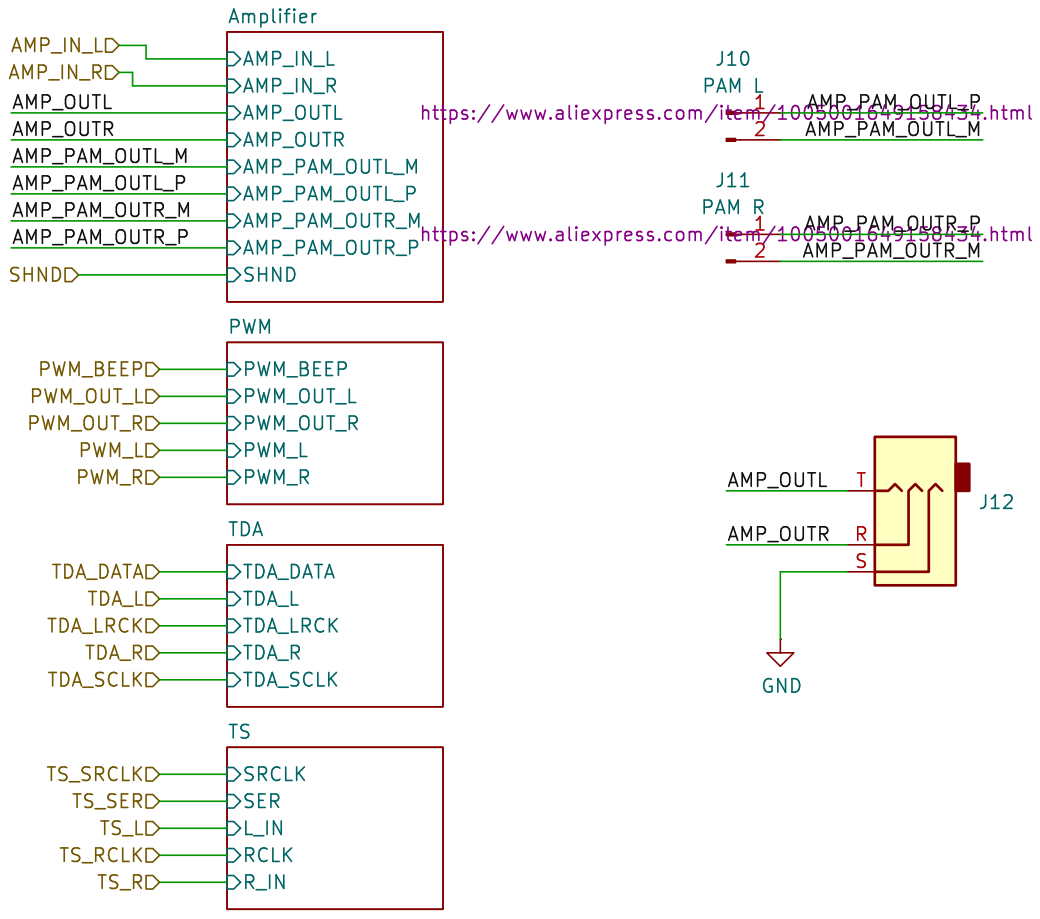
[picture p212: page 9]

https://www.aliexpress.com/item/1005001649158434.html 1

https://github.com/xtremespb/frank

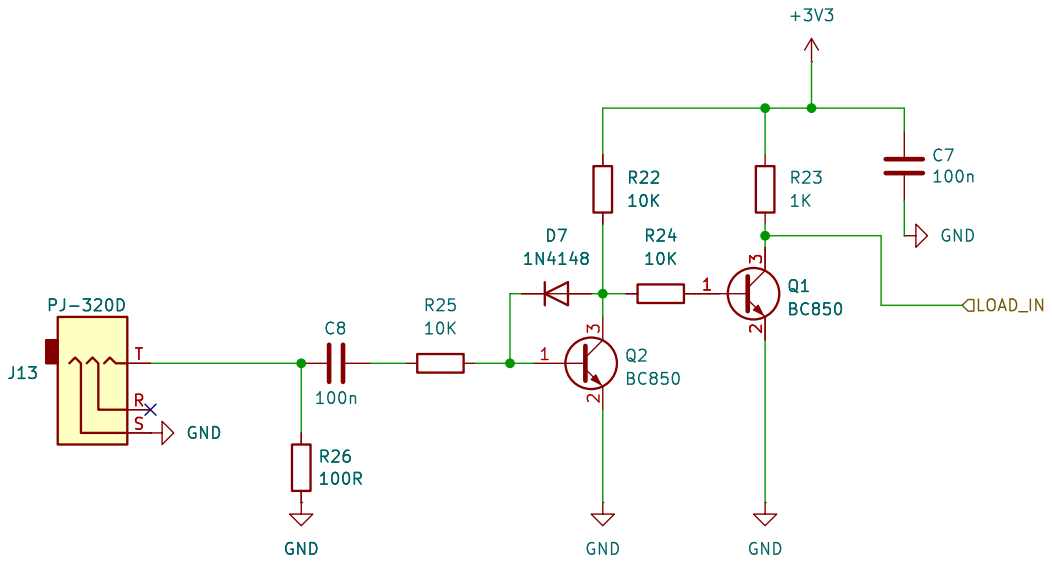
[picture p213: page 10]

https://github.com/xtremespb/frank GND

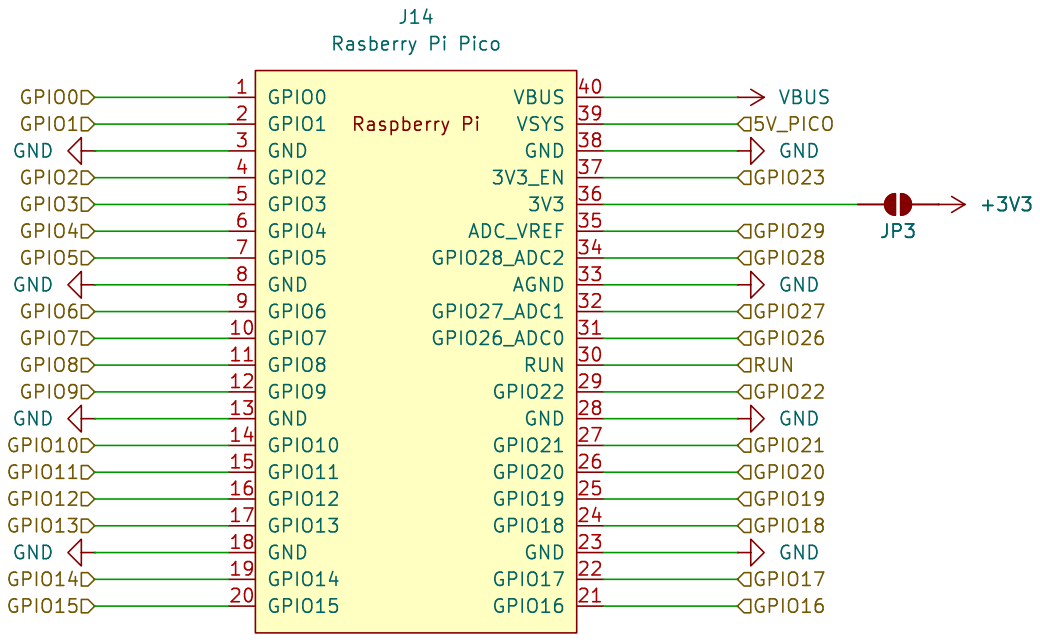
[picture p214: page 11]

VBUS GND GND GND GND

https://github.com/xtremespb/frank

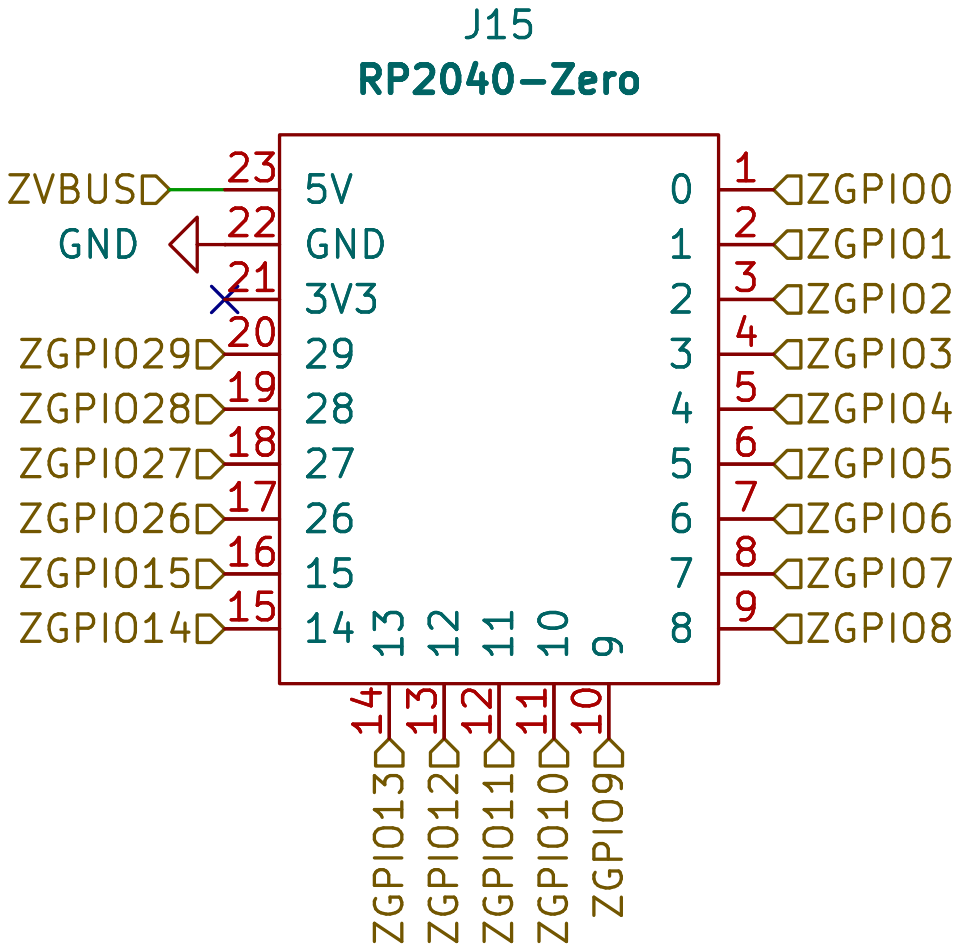
[picture p215: page 12]

https://github.com/xtremespb/frank

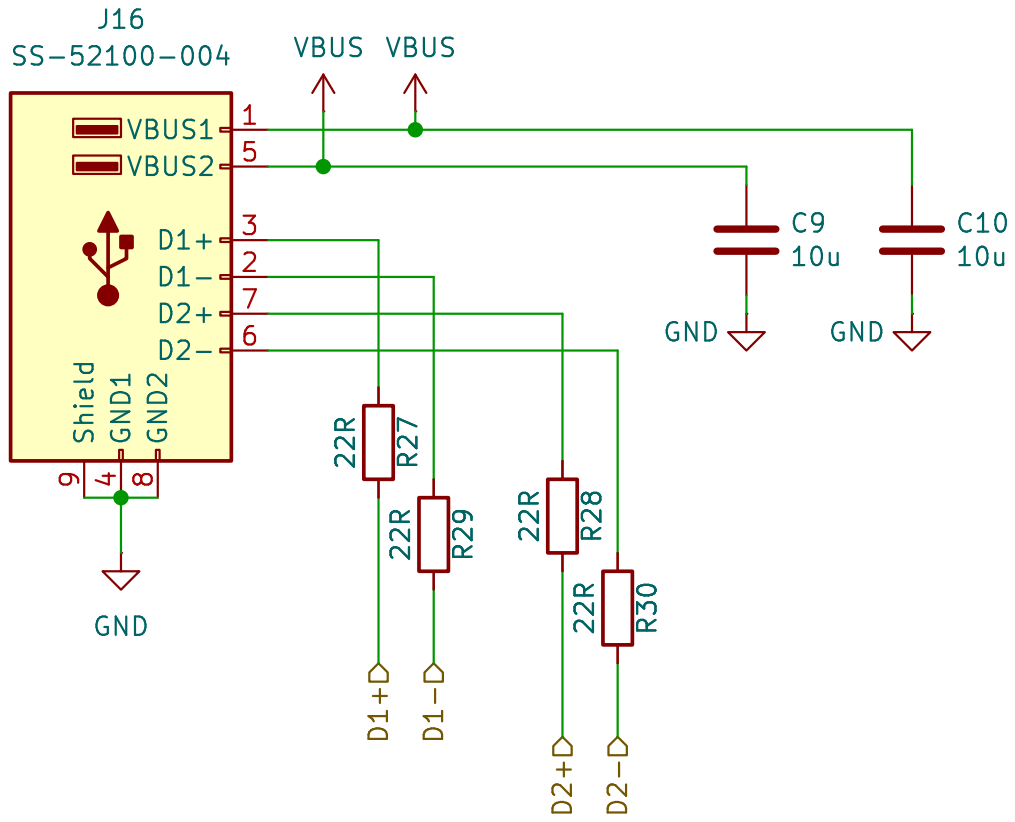
[picture p216: page 13]

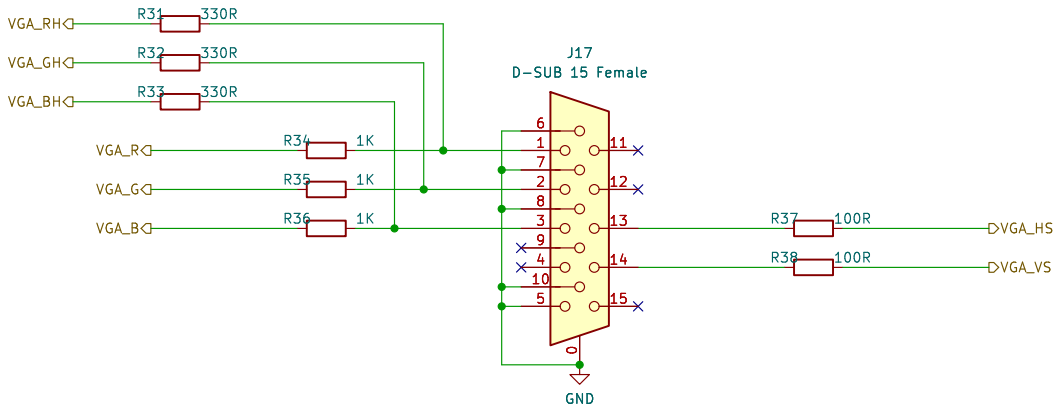
[picture p217: page 14]

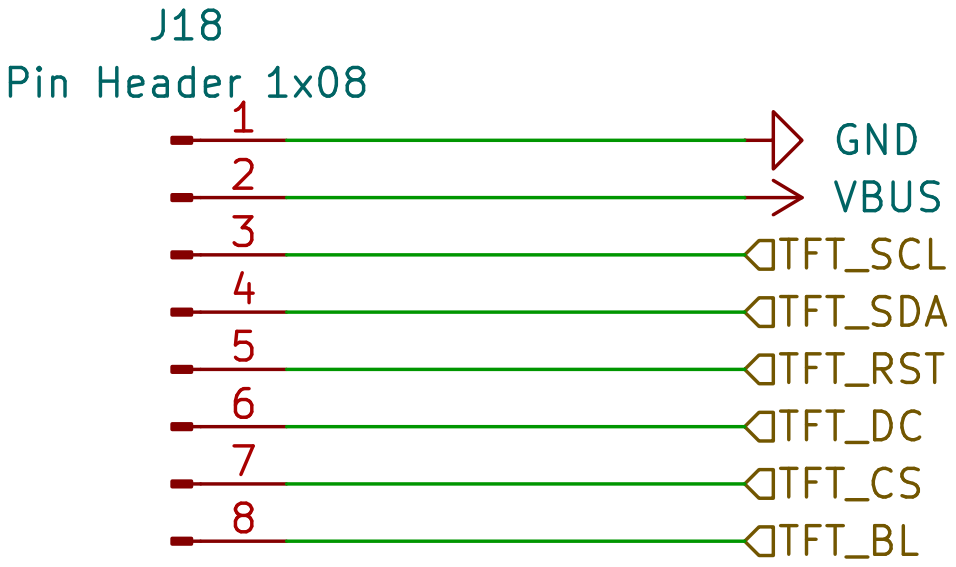
[picture p218: page 15]

https://github.com/xtremespb/frank GND
VBUS

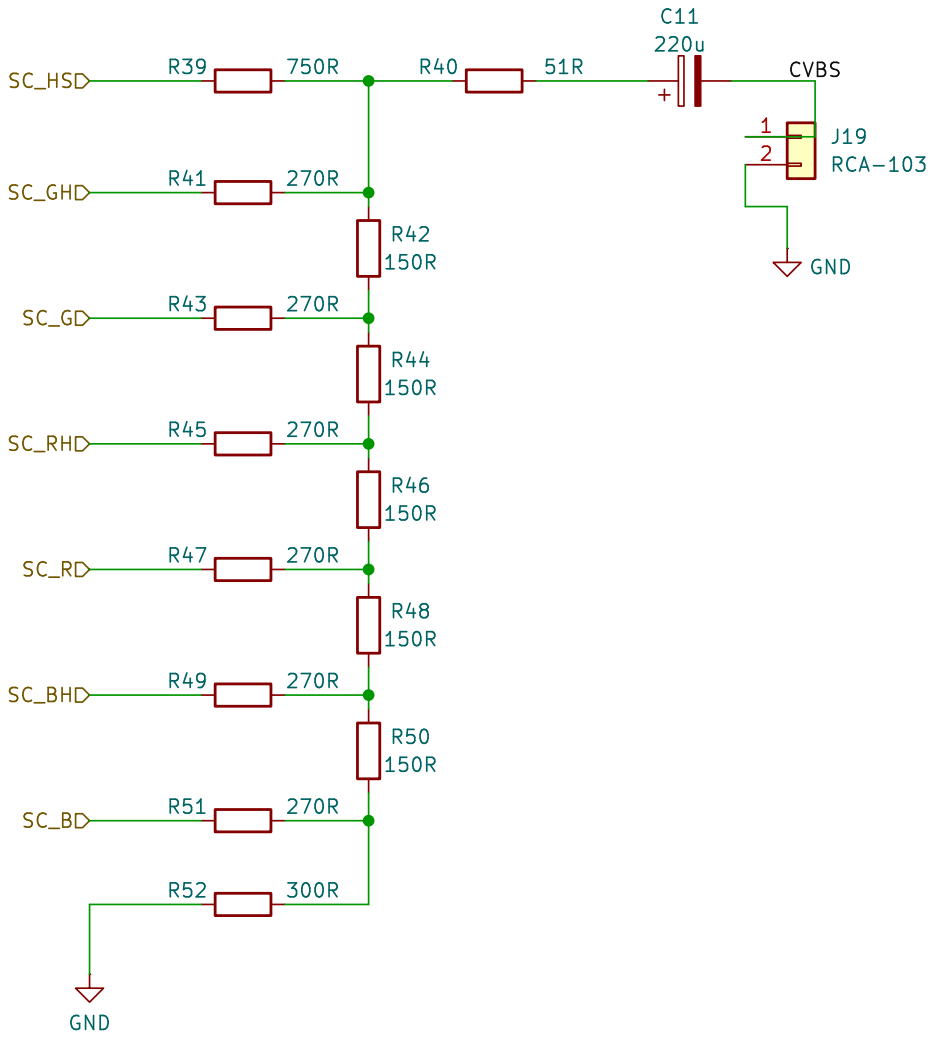
[picture p219: page 16]

https://github.com/xtremespb/frank

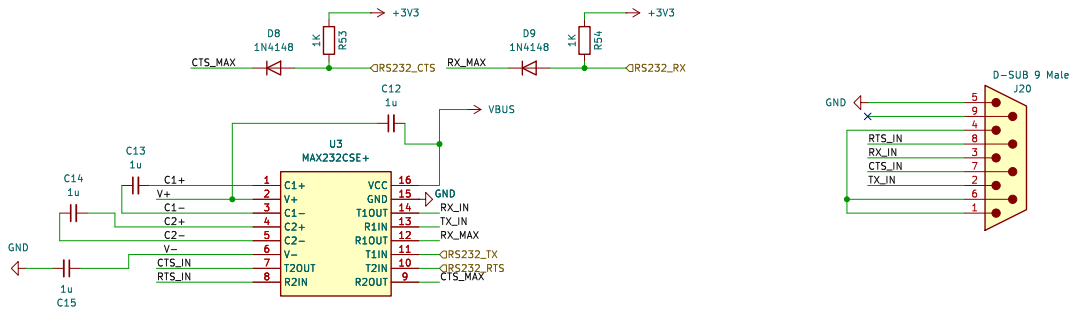
[picture p220: page 17]

https://github.com/xtremespb/frank R53 1K

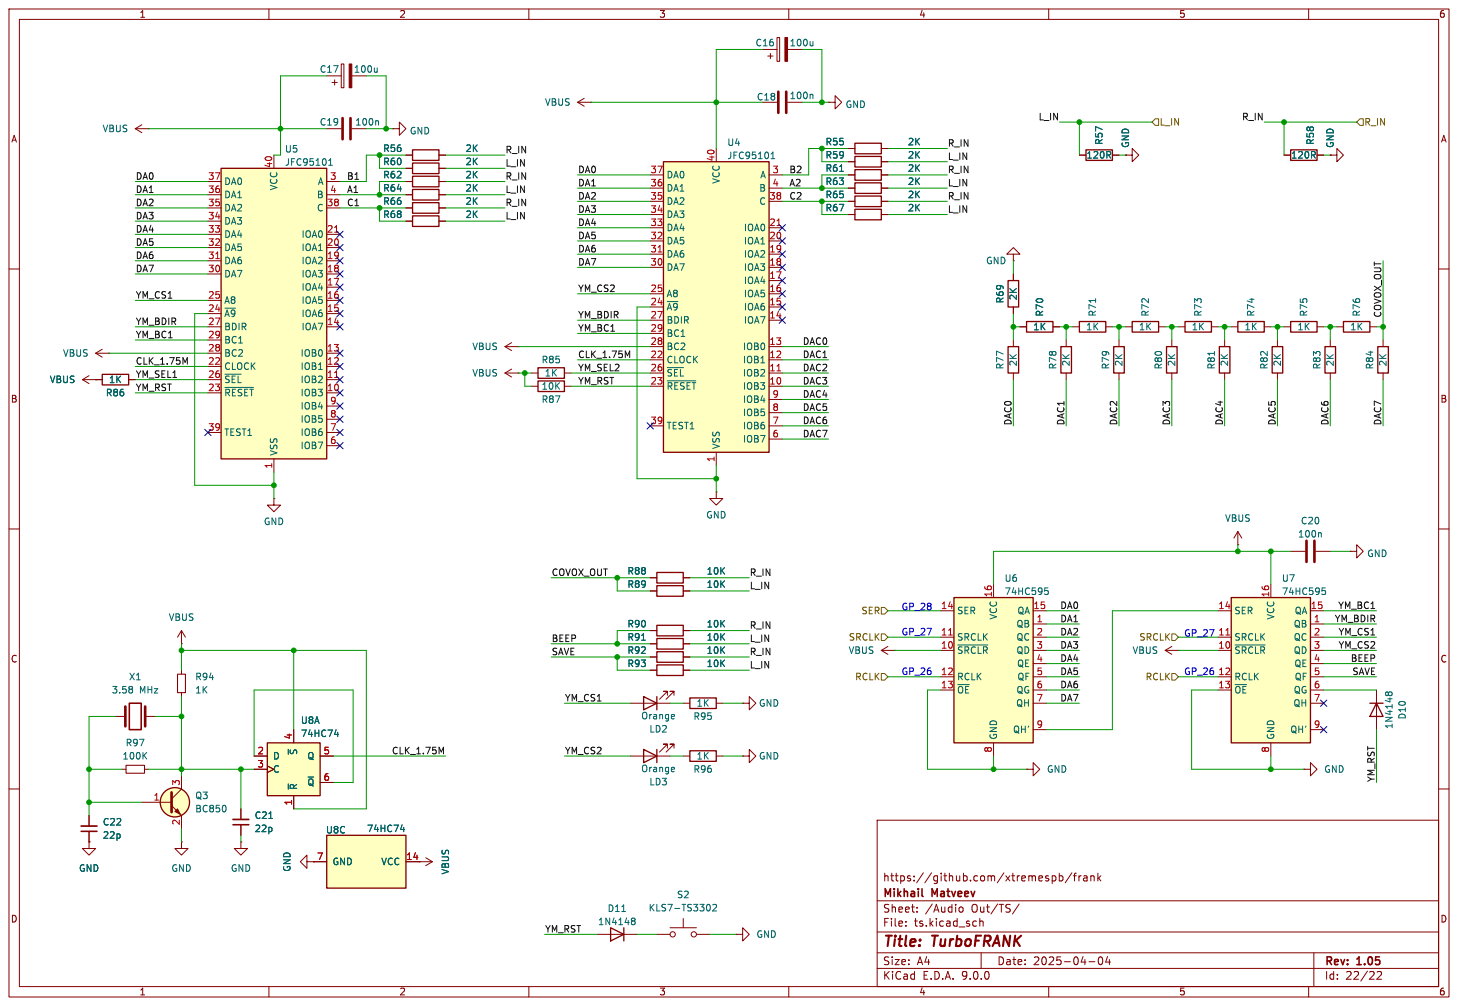
[picture p221: page 18]

https://github.com/xtremespb/frank

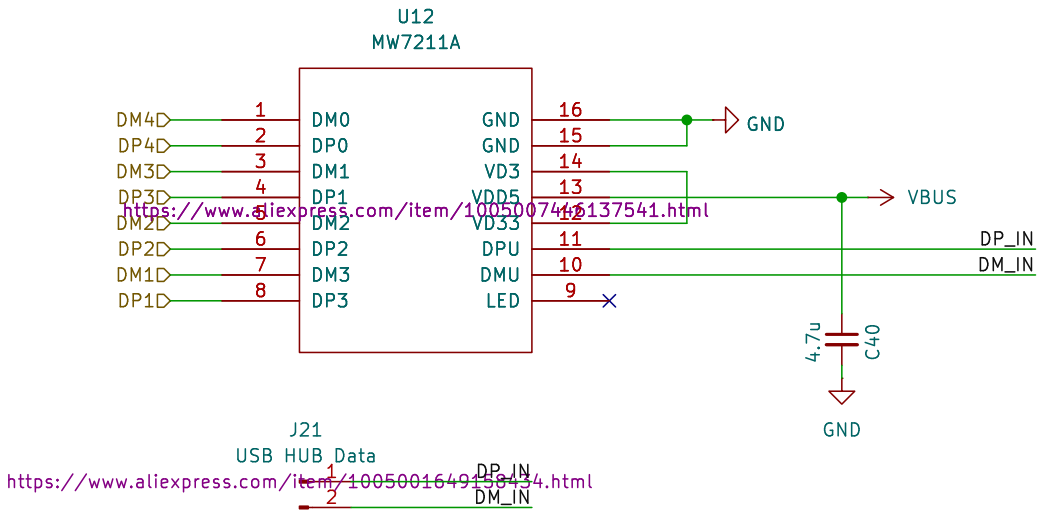
[picture p222: page 19]

https://github.com/xtremespb/frank

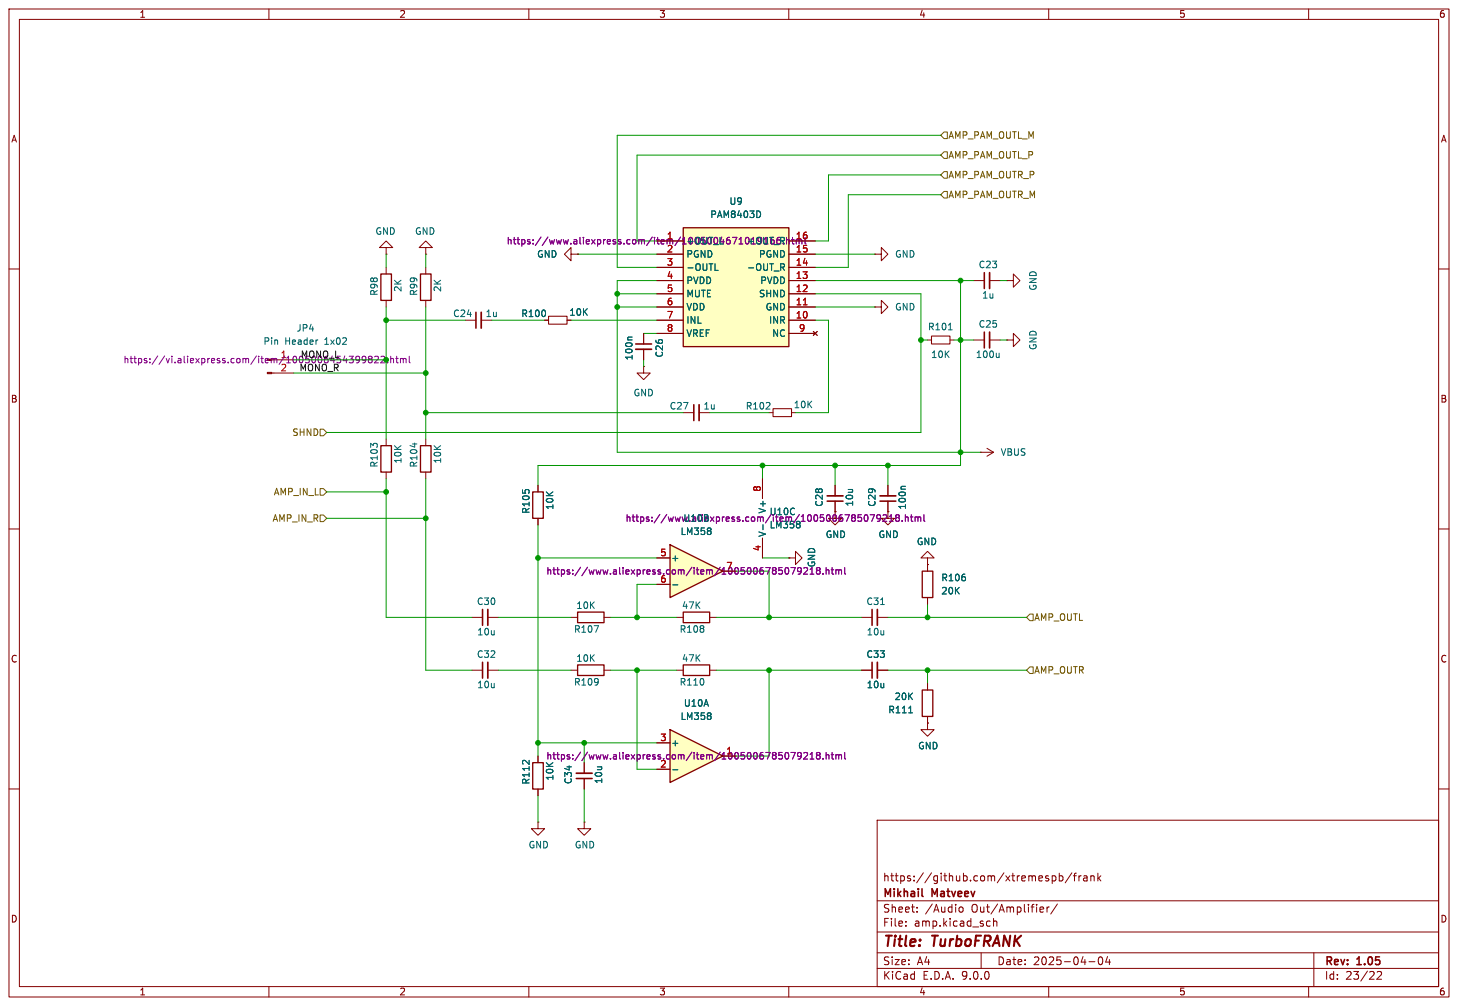
[picture p223: page 20]

LM358 https://www.aliexpress.com/item/1005006785079218.html V+
LM358 https://www.aliexpress.com/item/1005006785079218.html +

https://www.aliexpress.com/item/1005006785079218.html +
https://www.aliexpress.com/item/1005006785079218.html R108

https://www.aliexpress.com/item/1005006785079218.html R107

https://github.com/xtremespb/frank

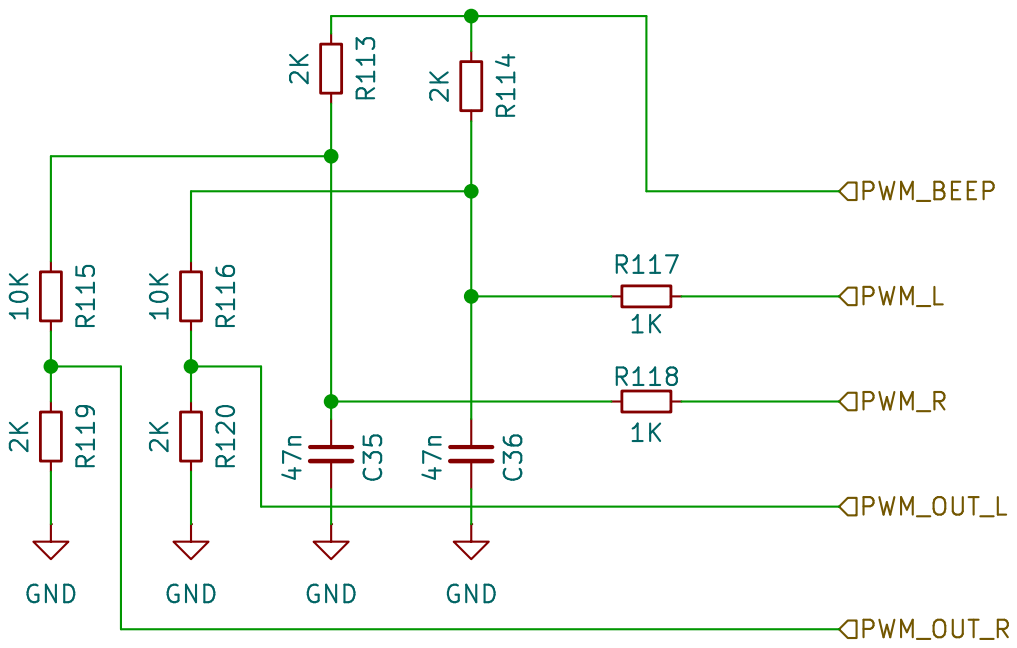
[picture p224: page 21]

https://github.com/xtremespb/frank R117

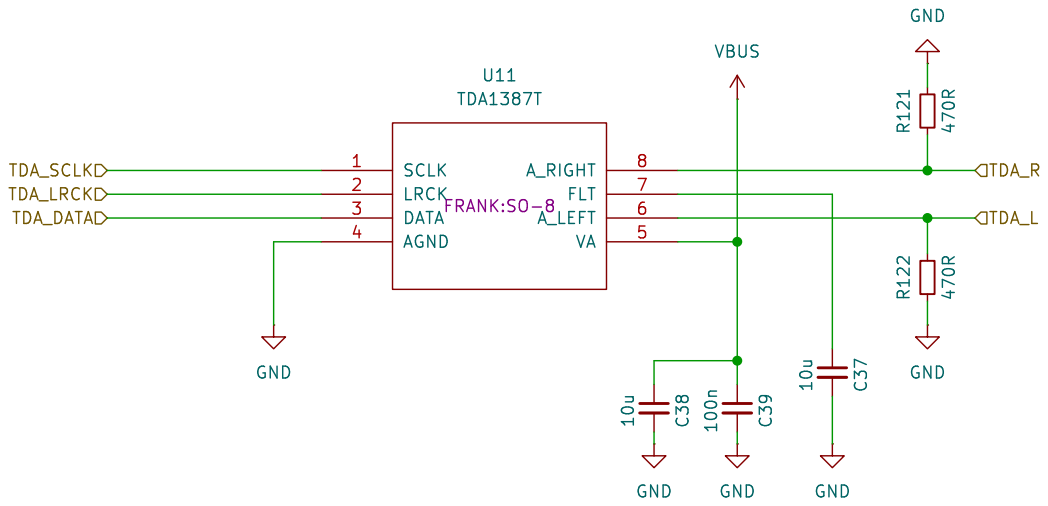
[picture p225: page 22]
