rh1tech/frank-archive/turbofrank_m1p1/docs/1_07/turbofrank_m1p1.pdf

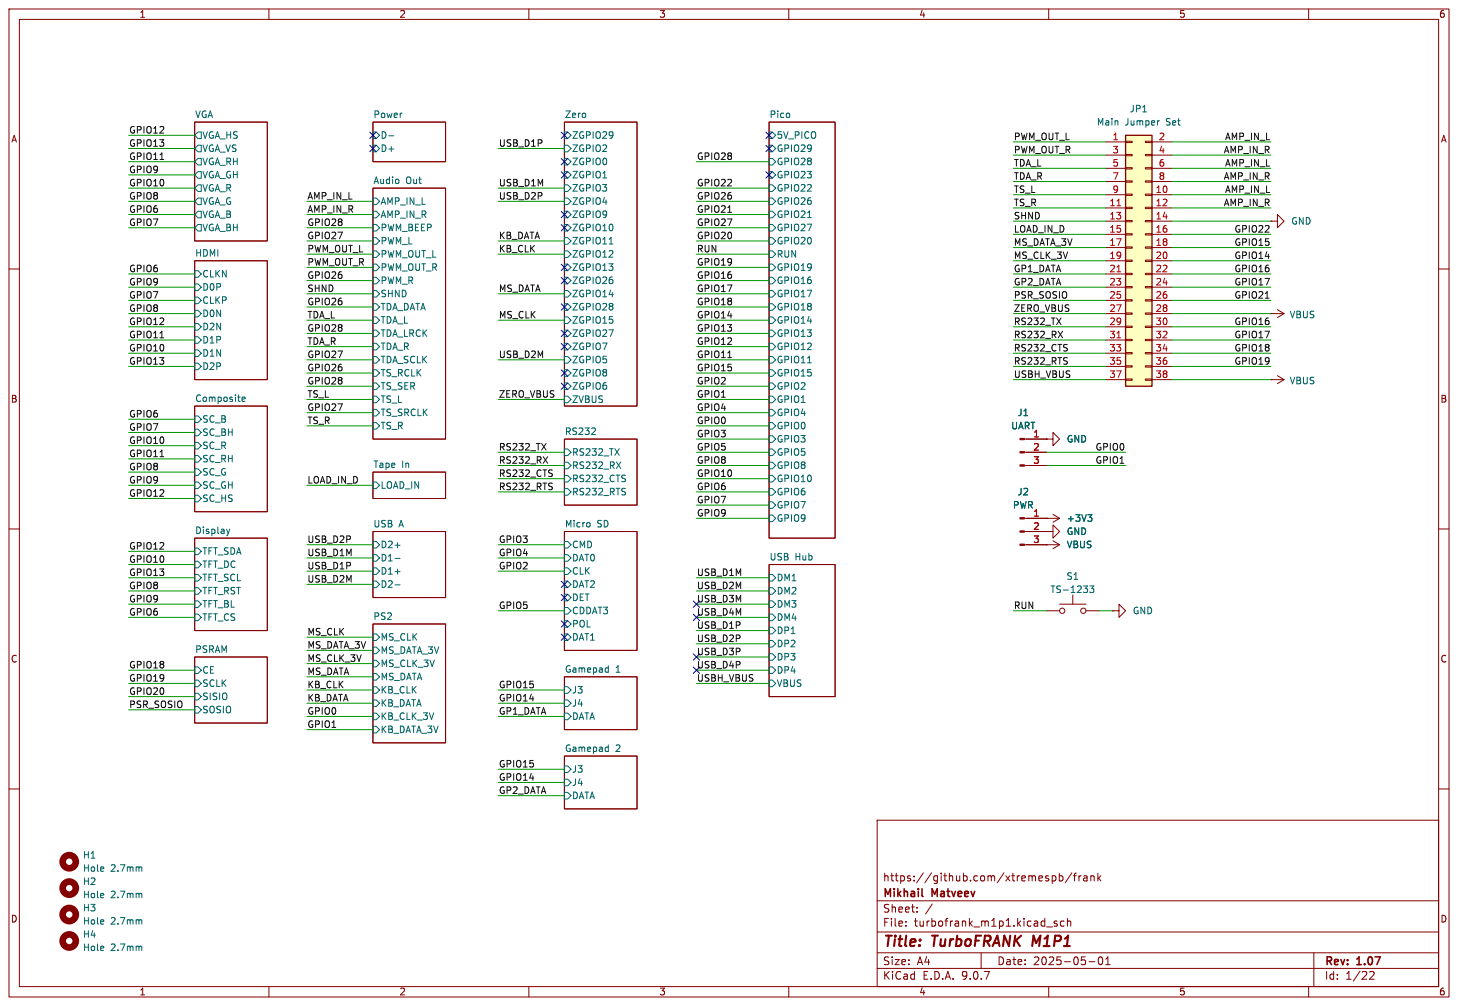
[picture p235: page 1]

DAT0 CLK DAT2 DET CDDAT3 POL DAT1 Micro SD


https://github.com/xtremespb/frank



https://github.com/xtremespb/frank GND


https://github.com/xtremespb/frank GND


https://github.com/xtremespb/frank GND


https://github.com/xtremespb/frank GND


4 ~{CE}1 SCLK 6 SIO3 7 SIO2 3 SI/SIO 5 SO/SIO 2 +3V3

4 ~{CE}1 SCLK 6 SIO3 7 SIO2 3 SI/SIO 5 SO/SIO 2 U2 ESP-PSRAM32 GND

https://github.com/xtremespb/frank


https://github.com/xtremespb/frank

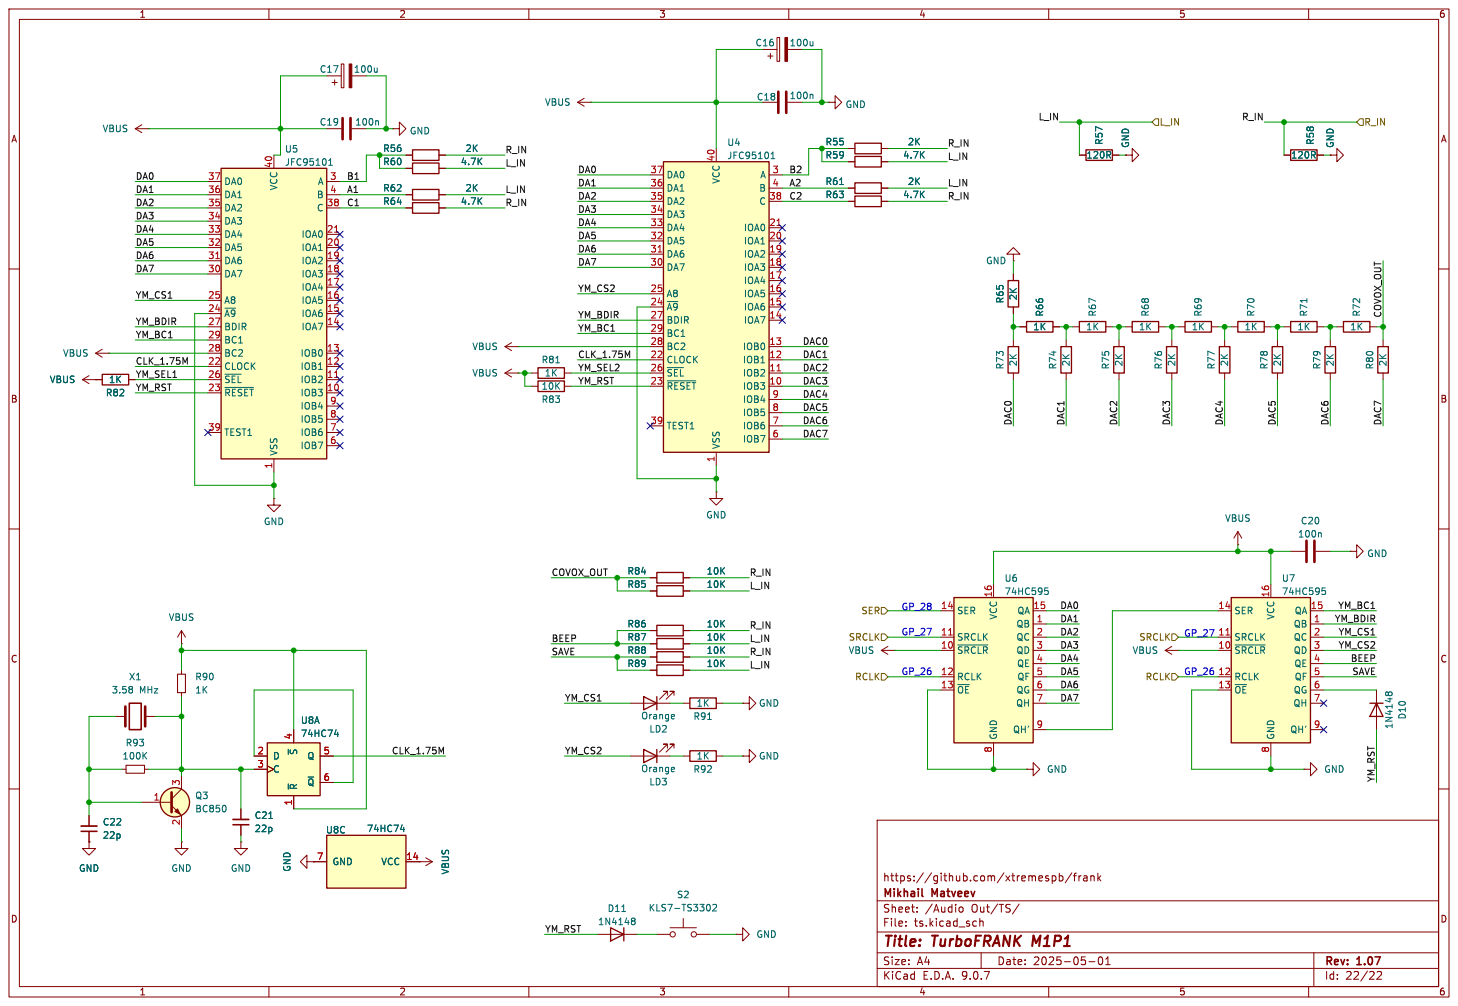
[picture p236: page 10]

https://github.com/xtremespb/frank

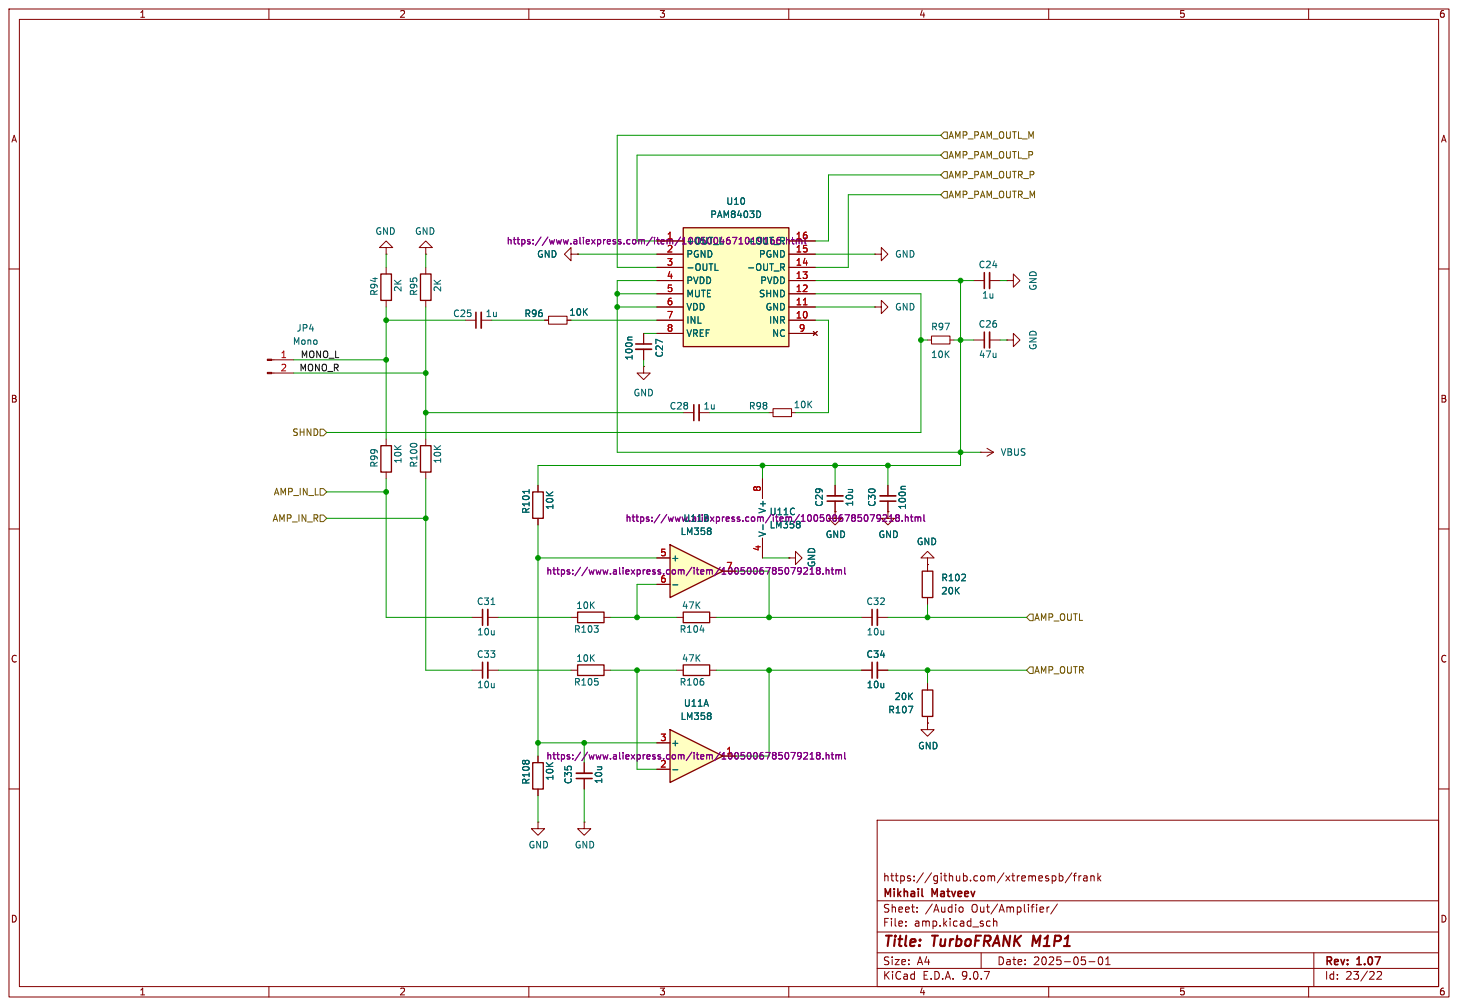
[picture p237: page 11]

LM358 https://www.aliexpress.com/item/1005006785079218.html V+
LM358 https://www.aliexpress.com/item/1005006785079218.html +

https://www.aliexpress.com/item/1005006785079218.html +

https://www.aliexpress.com/item/1005006785079218.html R103

https://github.com/xtremespb/frank

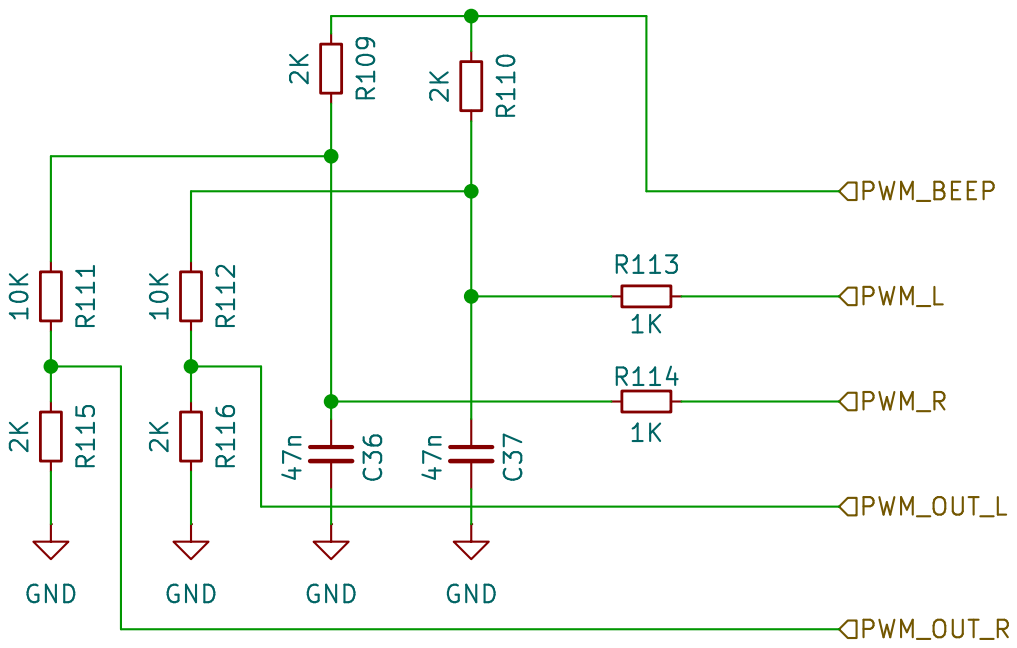
[picture p238: page 12]

https://github.com/xtremespb/frank R113

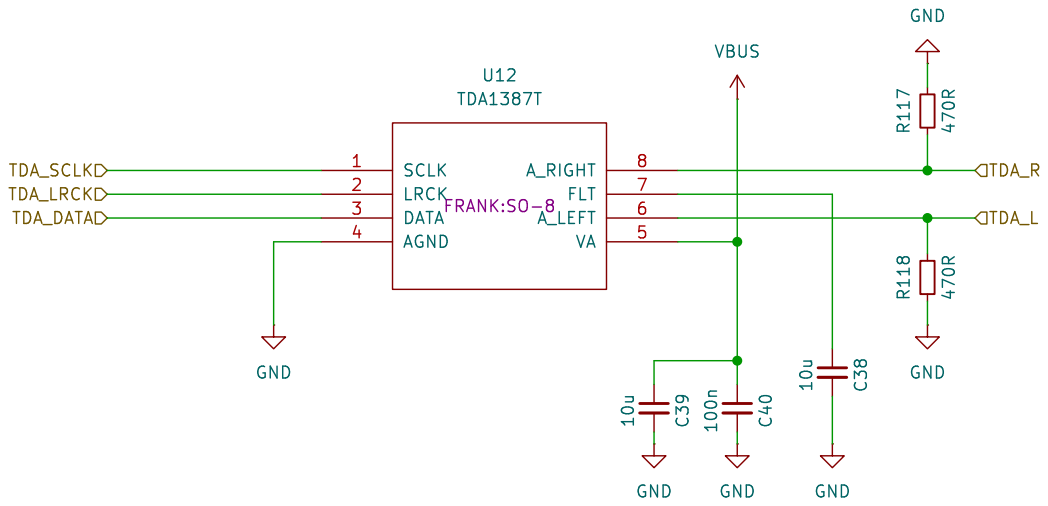
[picture p239: page 13]


https://github.com/xtremespb/frank GND



https://github.com/xtremespb/frank




https://github.com/xtremespb/frank


https://github.com/xtremespb/frank R46


https://github.com/xtremespb/frank C13

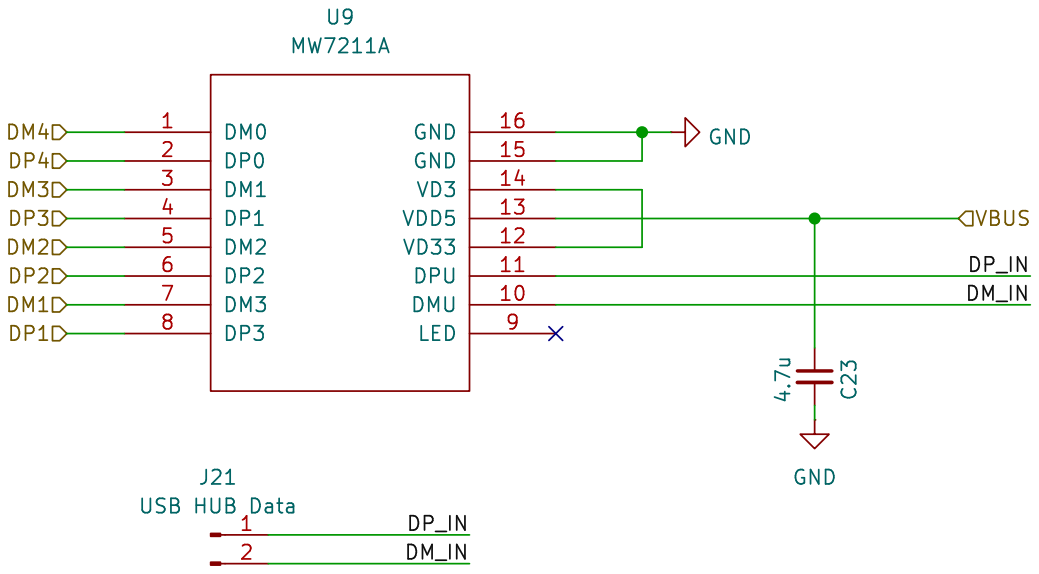
[picture p240: page 22]

https://github.com/xtremespb/frank
