rh1tech/frank-archive/turbofrank_m1p2/docs/1_00/turbofrank_m1p2.pdf

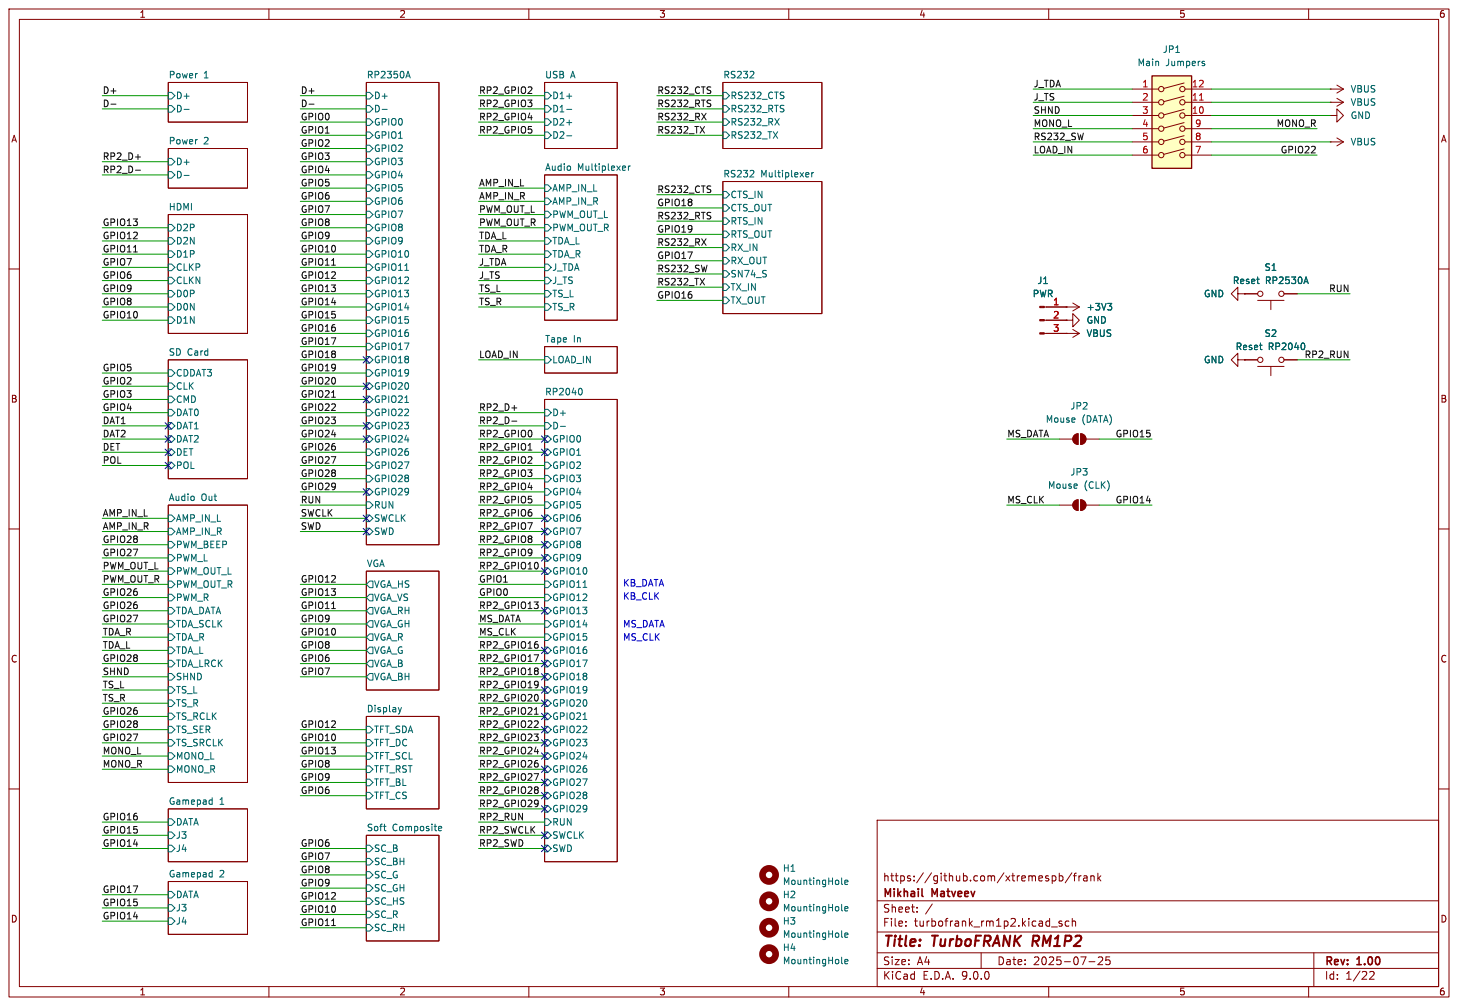
[picture p241: page 1]

Audio Multiplexer D+D- Power 1 CDDAT3 CLK CMD

J1 PWR
JP2 Mouse (DATA) VBUS GND 123

H1 MountingHole H4 MountingHole H2 MountingHole H3 MountingHole

https://github.com/xtremespb/frank

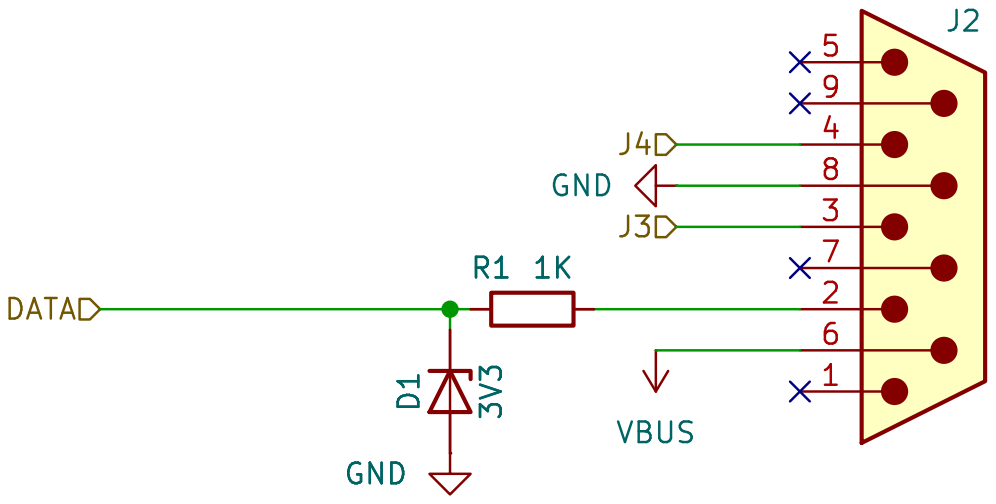
[picture p242: page 2]

https://github.com/xtremespb/frank GND

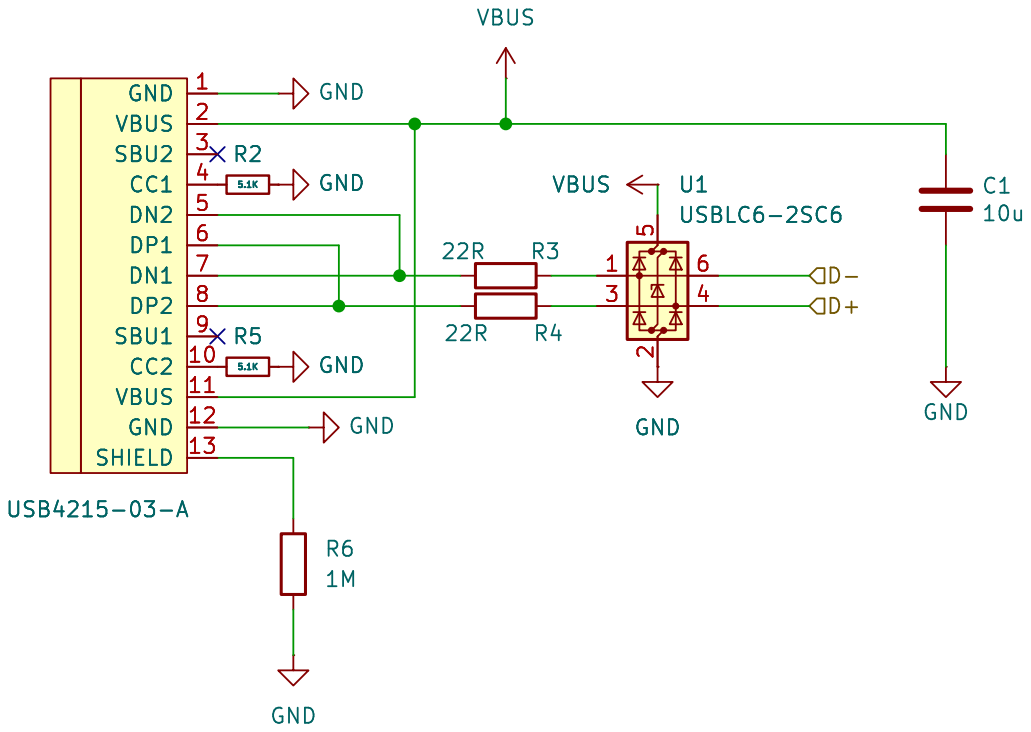
[picture p243: page 3]

https://github.com/xtremespb/frank GND

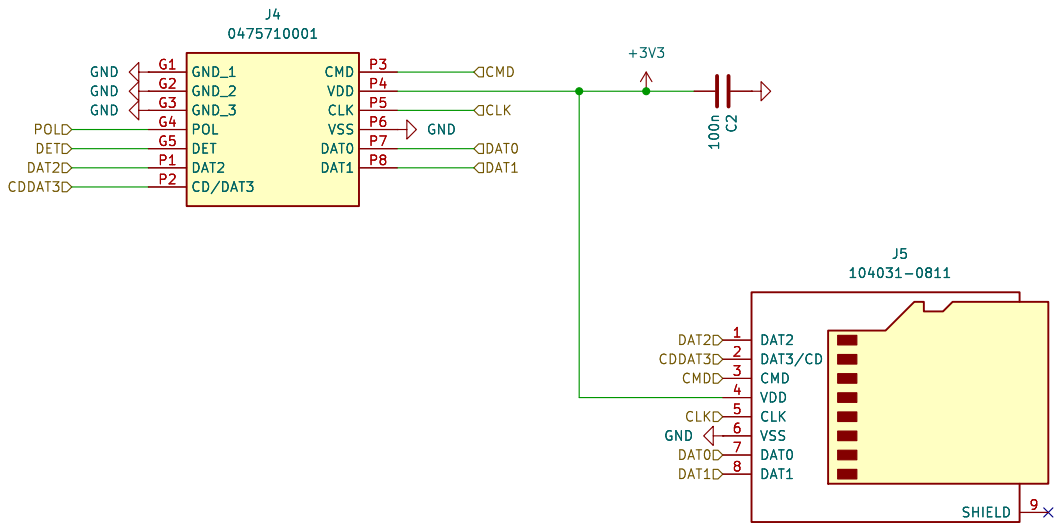
[picture p244: page 4]

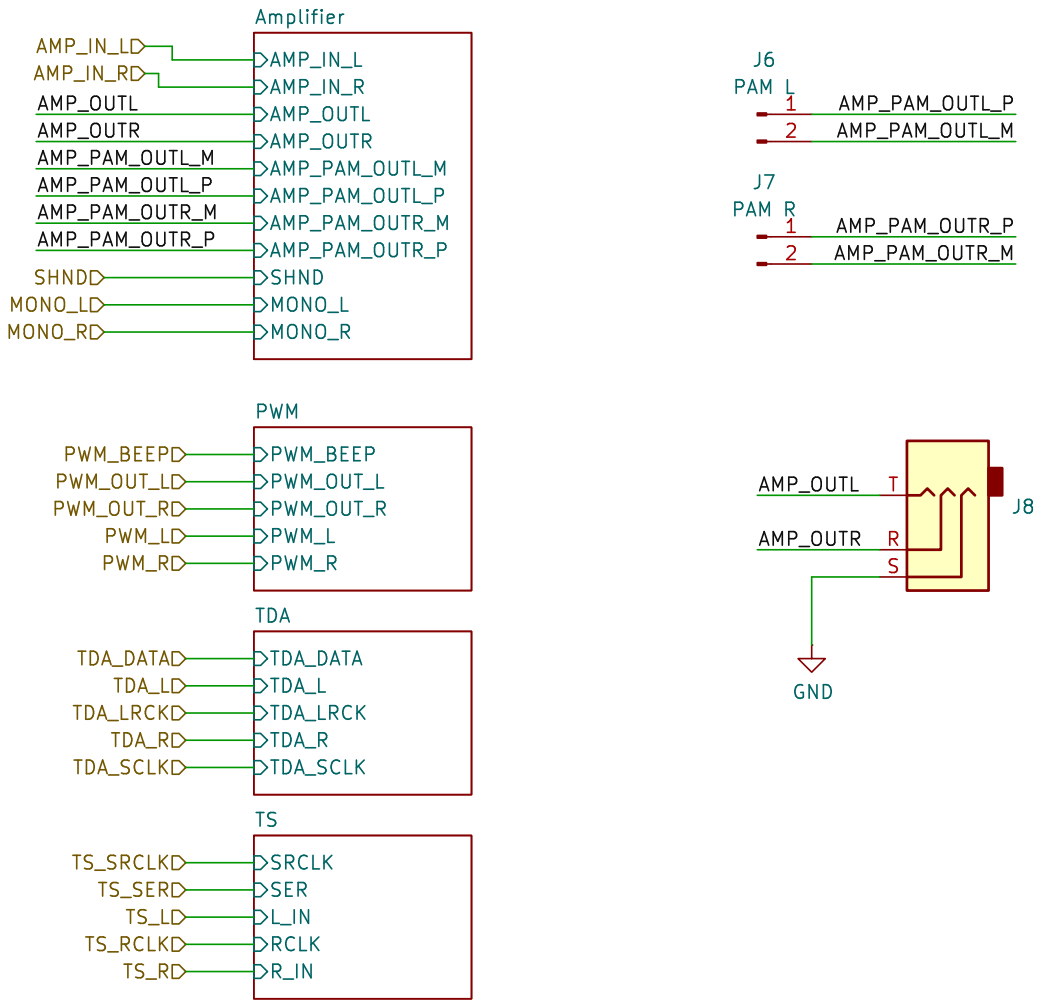
[picture p245: page 5]

TDARCLK
https://github.com/xtremespb/frank TDA_DATA
TDA_L TDA_LRCK

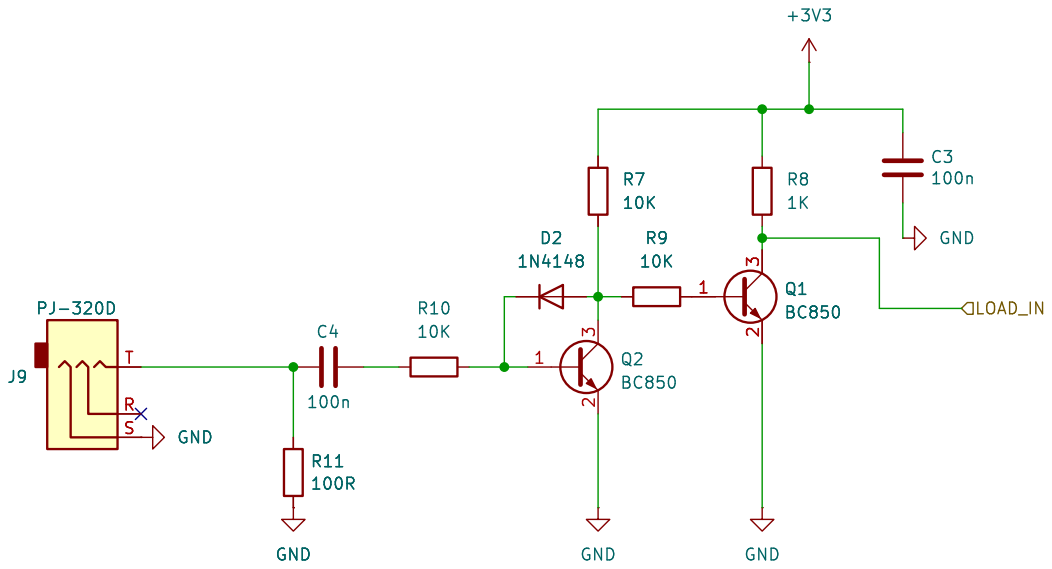
[picture p246: page 6]

https://github.com/xtremespb/frank GND

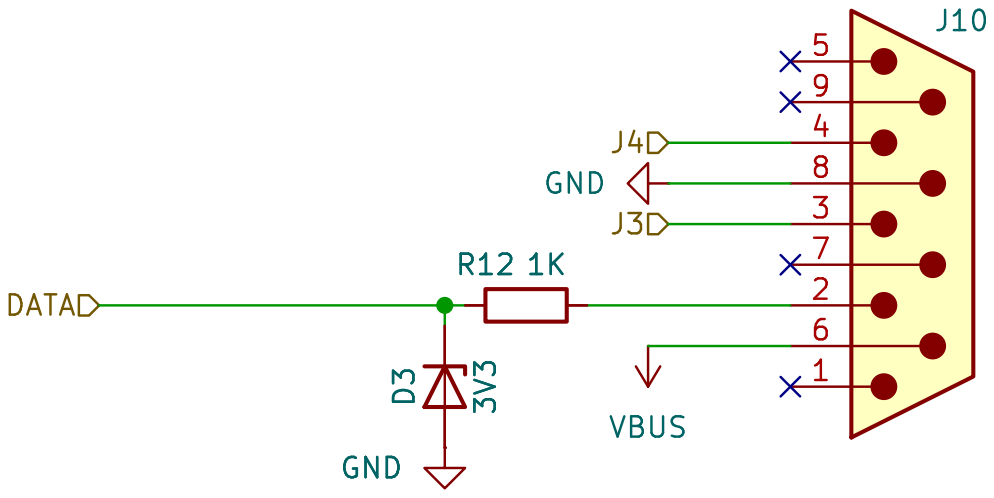
[picture p247: page 7]

https://github.com/xtremespb/frank GND

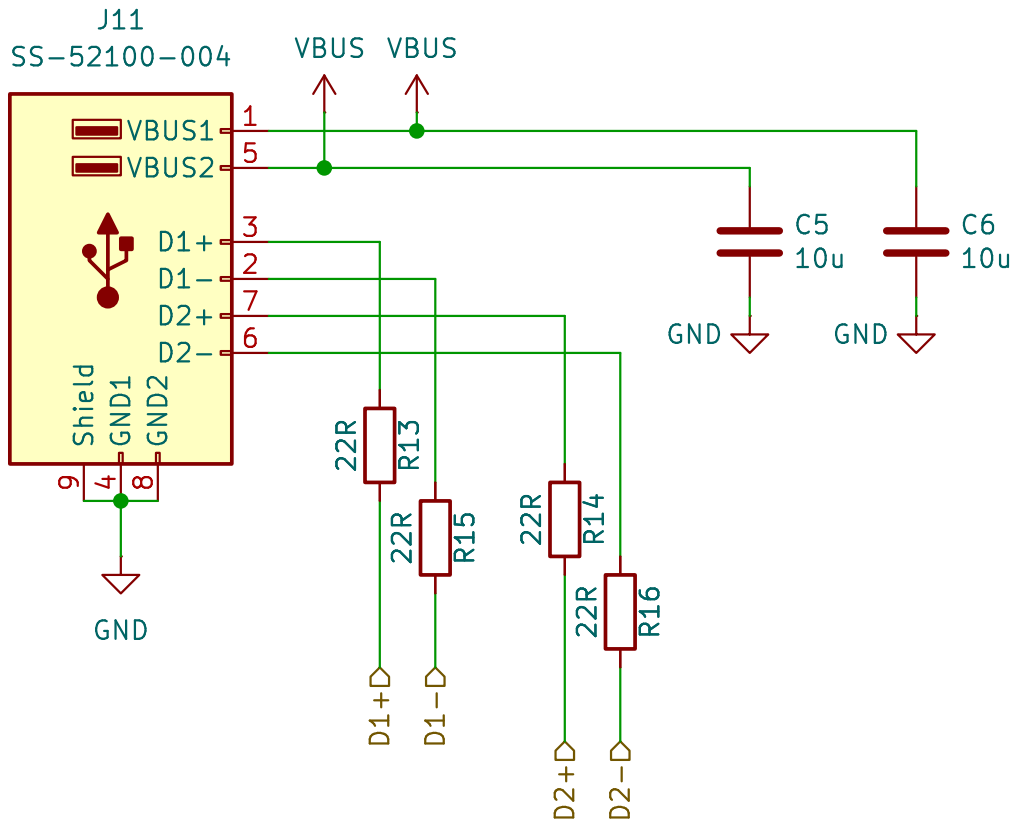
[picture p248: page 8]

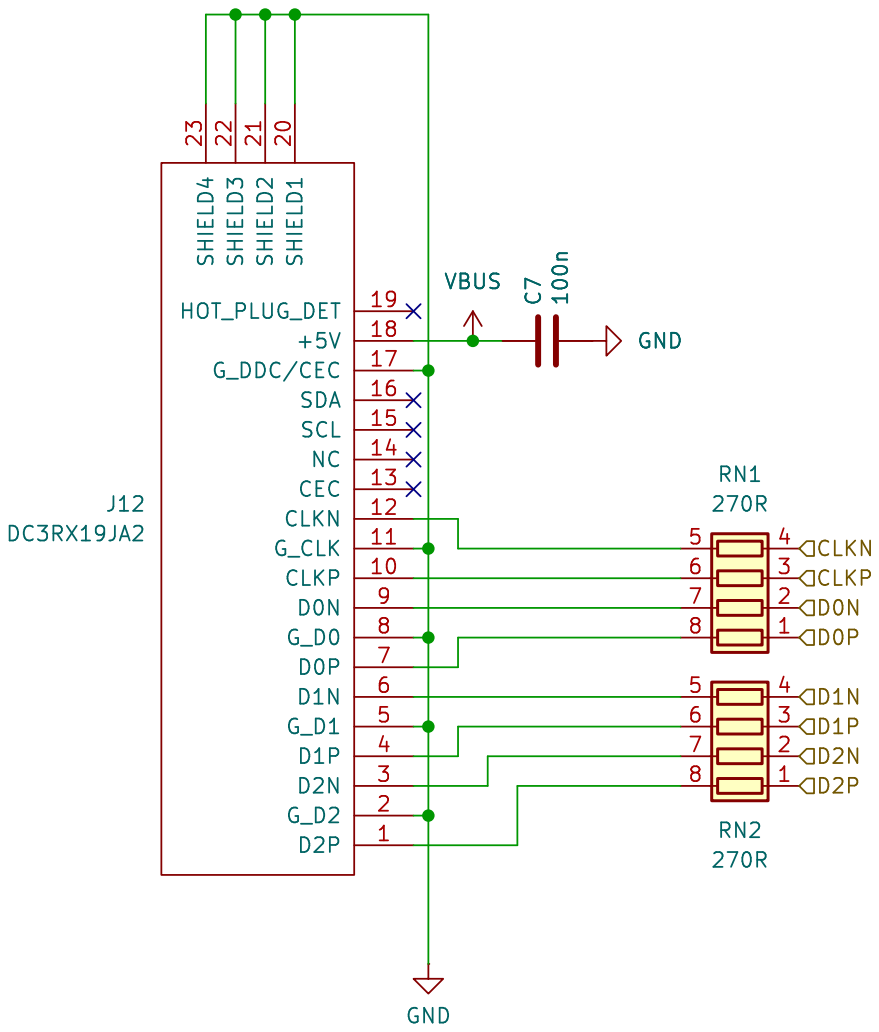
[picture p249: page 9]

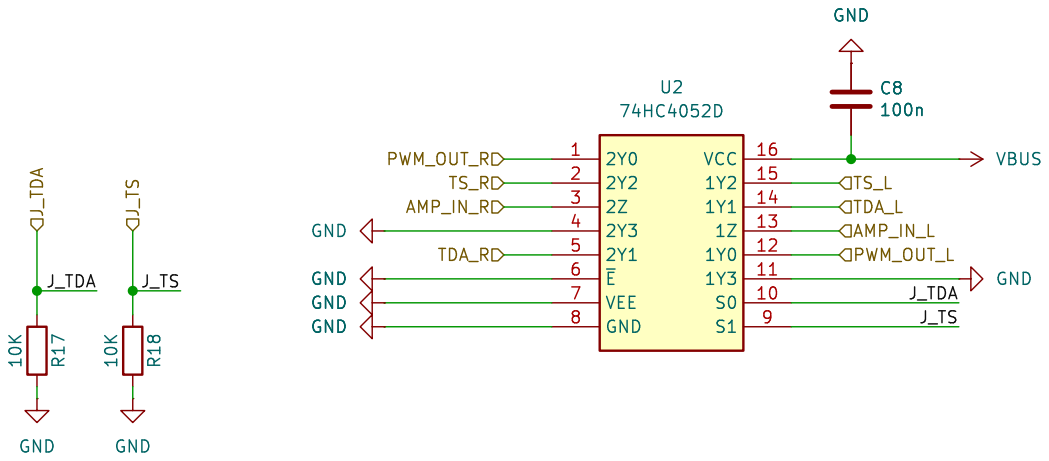
[picture p250: page 10]

https://github.com/xtremespb/frank

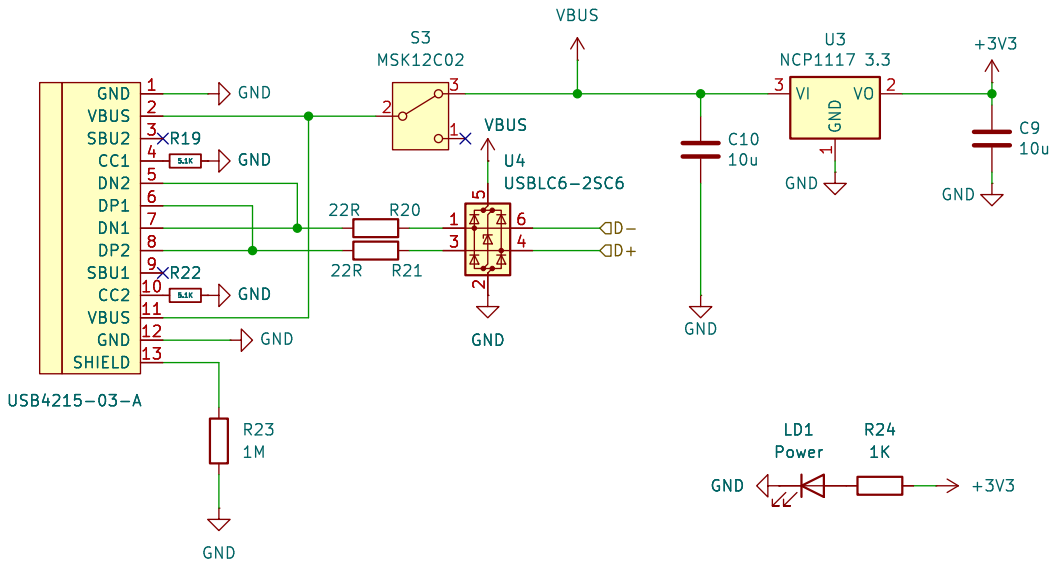
[picture p251: page 11]

https://github.com/xtremespb/frank

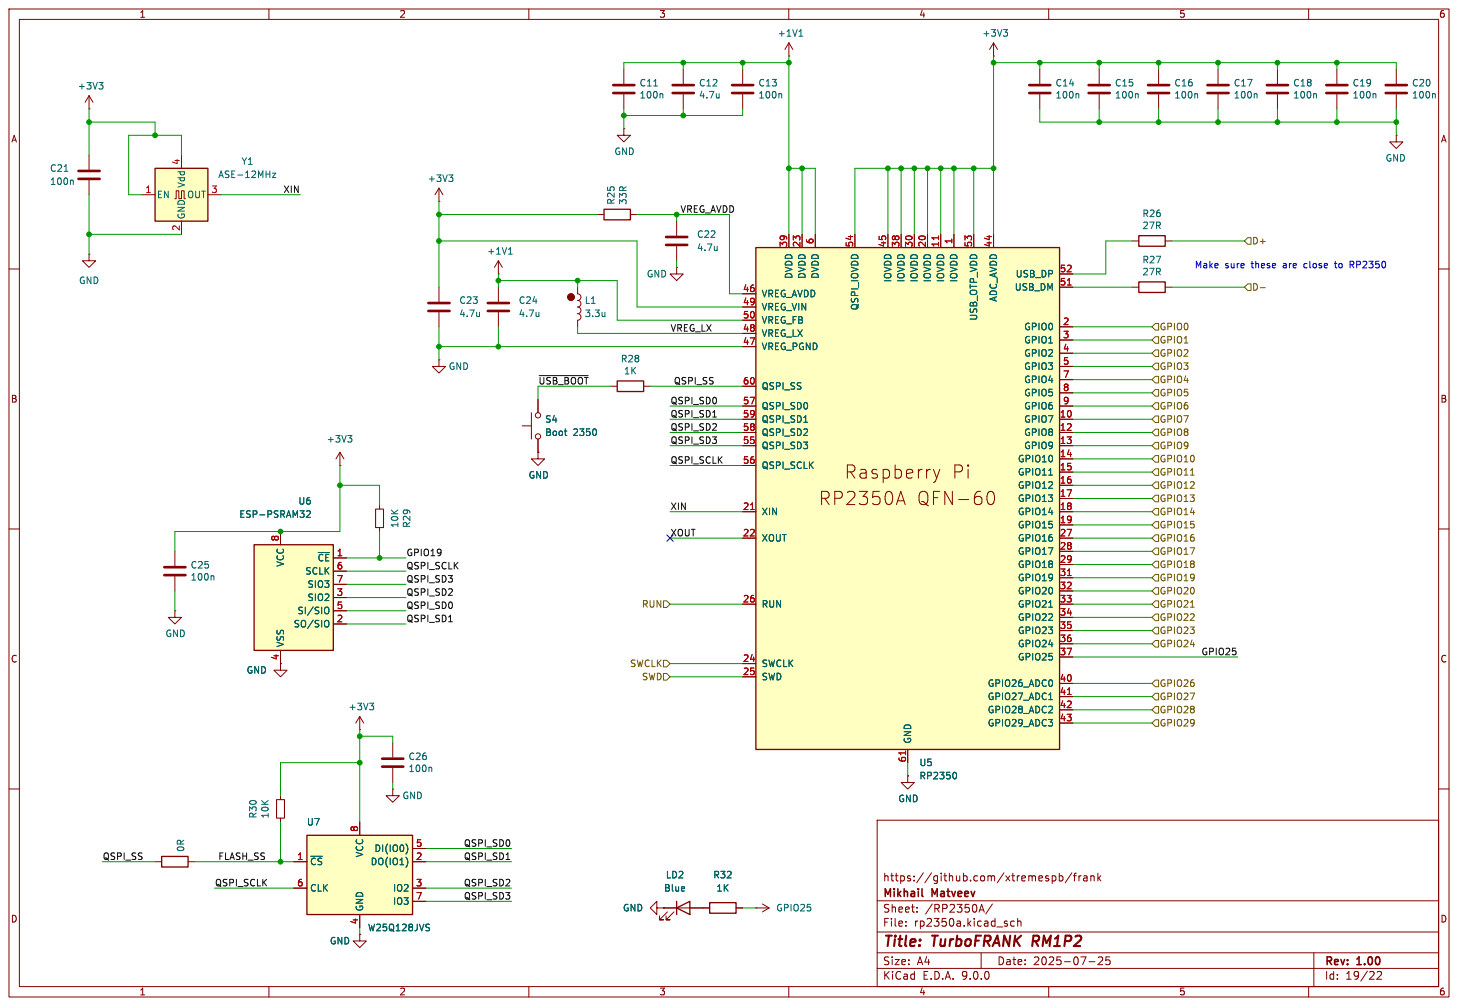
[picture p252: page 12]

6 QSPI_IOVDD 54 IOVDD 45 IOVDD 38 GND 61 IOVDD 30 IOVDD 20 IOVDD 11 IOVDD

4 ~{CE}1 SCLK 6 SIO3 7 SIO2 3 SI/SIO 5 SO/SIO 2 U6 ESP-PSRAM32 GND

4 ~{CE}1 SCLK 6 SIO3 7 SIO2 3 SI/SIO 5 SO/SIO 2 GND

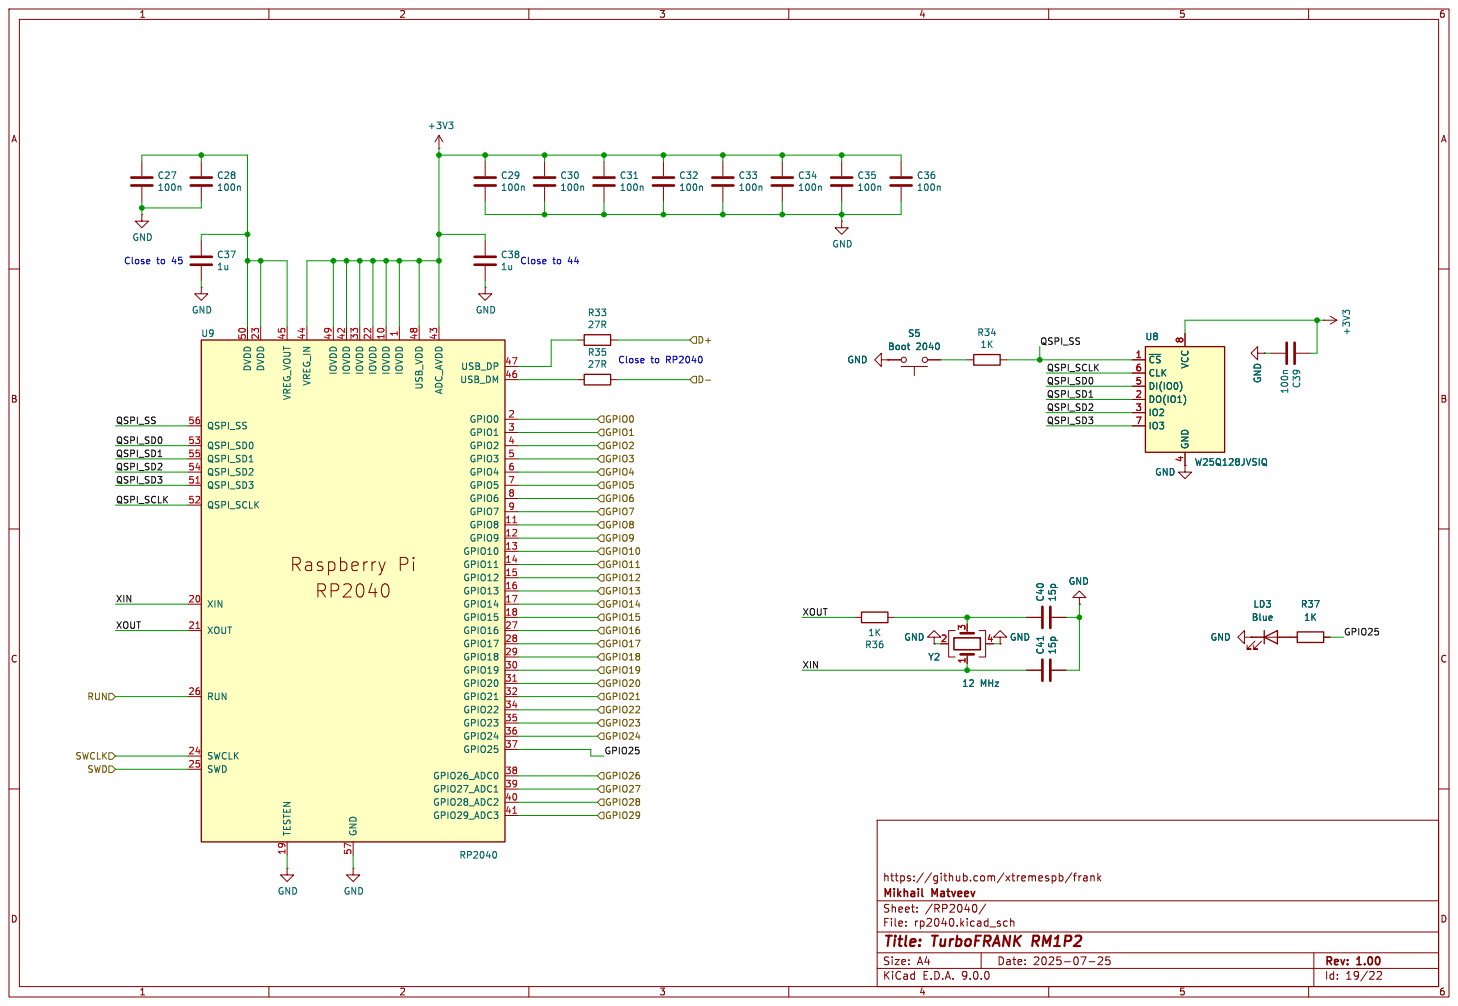
[picture p253: page 13]

https://github.com/xtremespb/frank GND

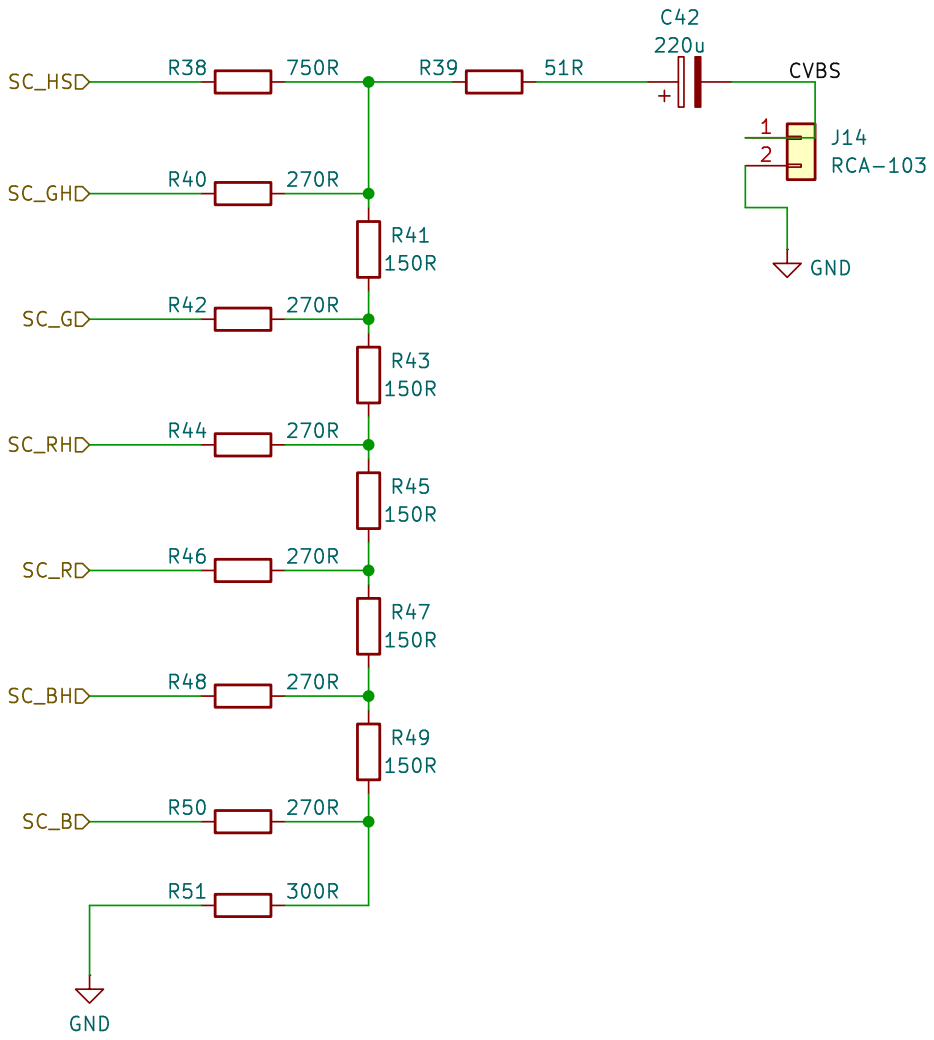
[picture p254: page 14]

https://github.com/xtremespb/frank R45

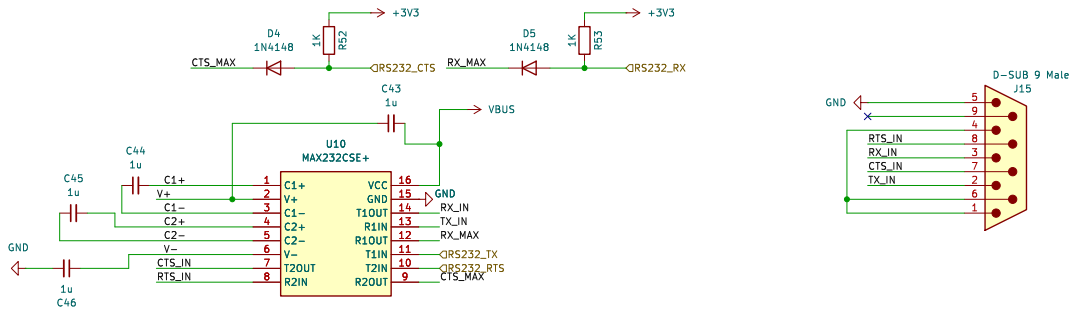
[picture p255: page 15]

https://github.com/xtremespb/frank C44

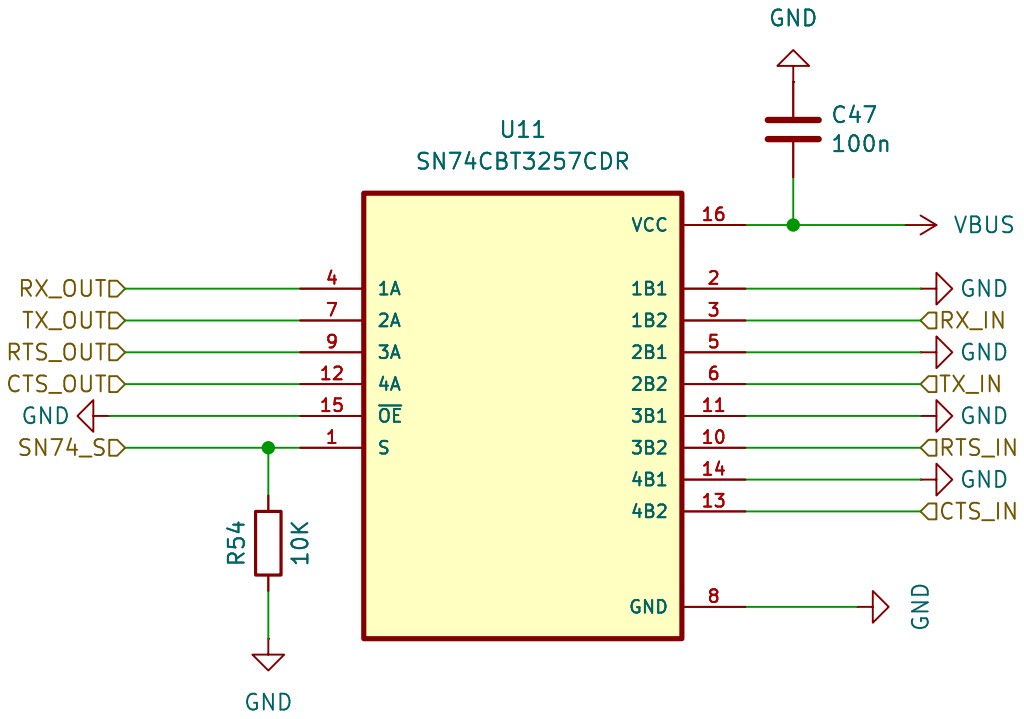
[picture p256: page 16]

https://github.com/xtremespb/frank

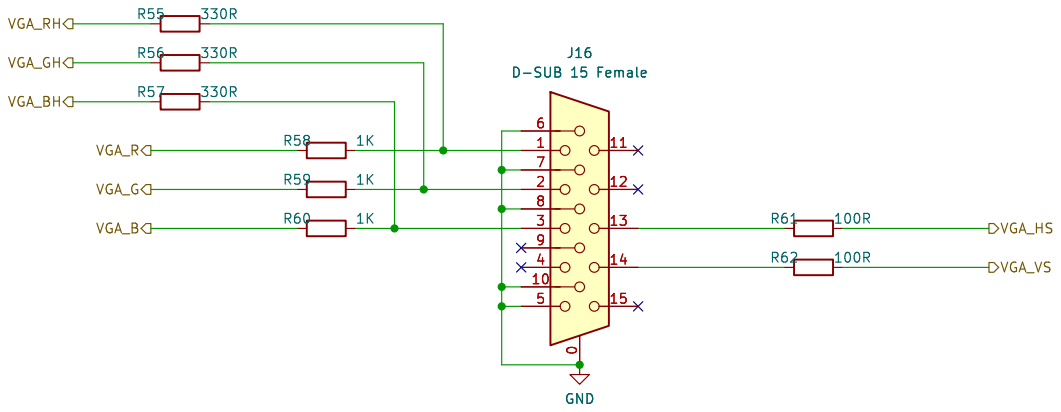
[picture p257: page 17]

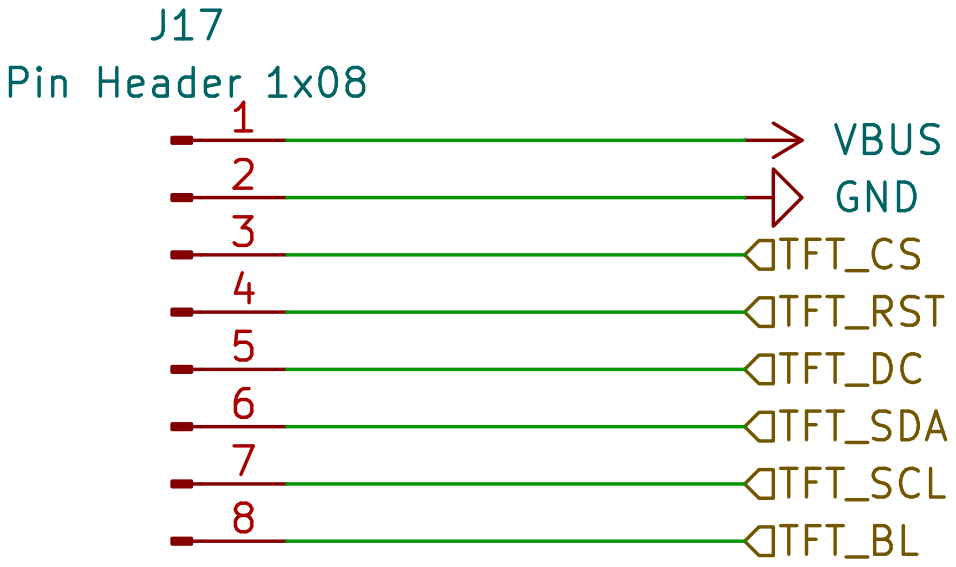
[picture p258: page 18]

https://github.com/xtremespb/frank

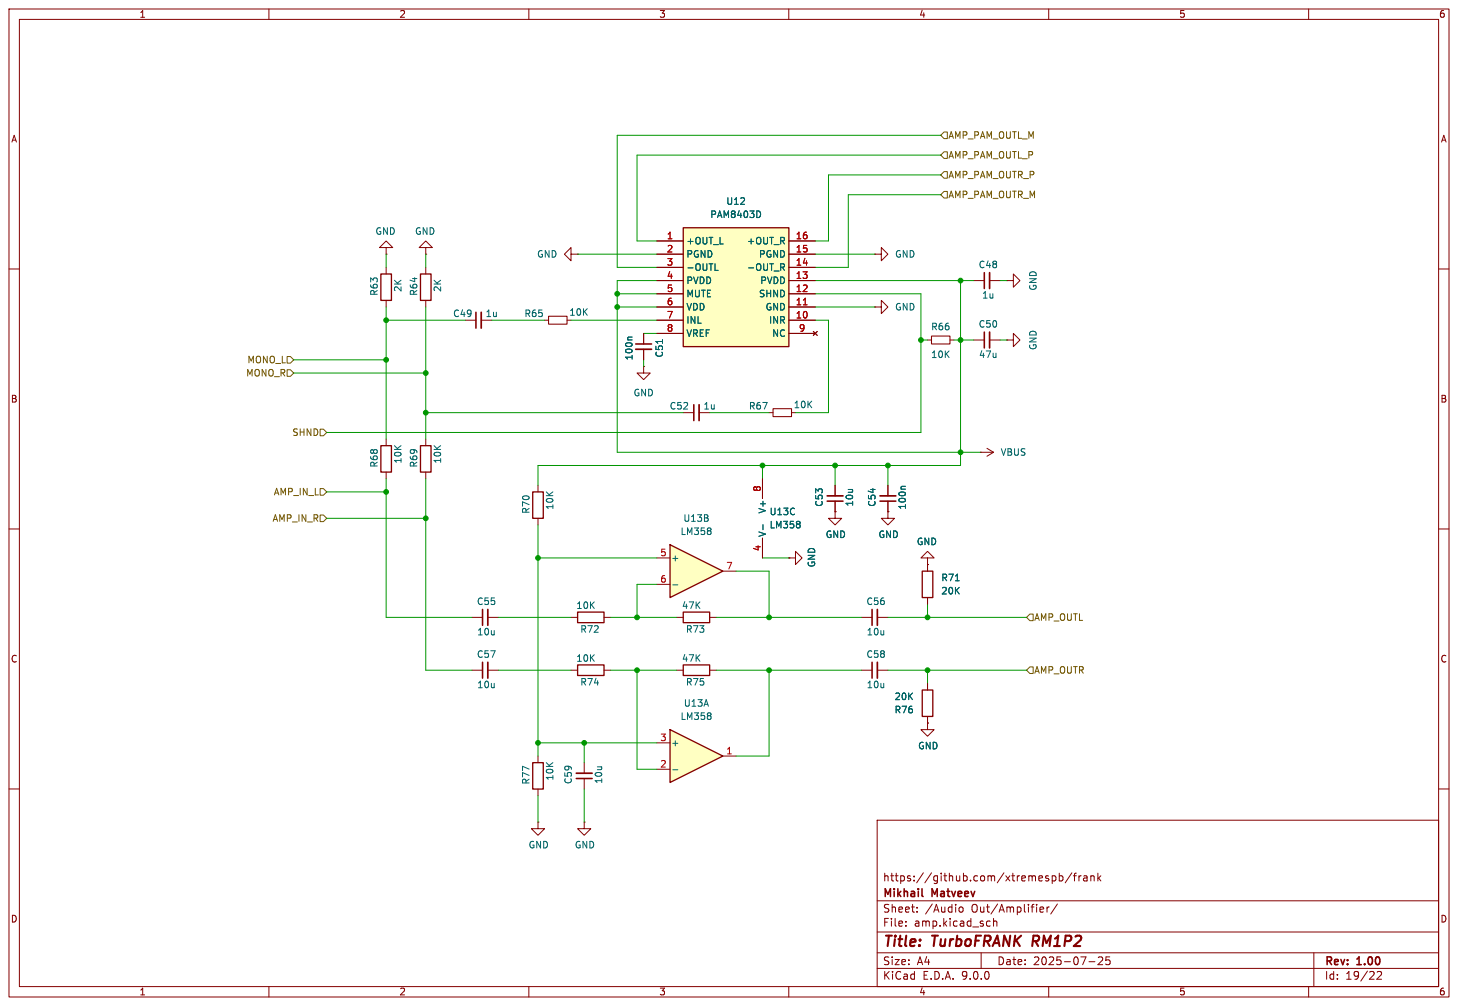
[picture p259: page 19]

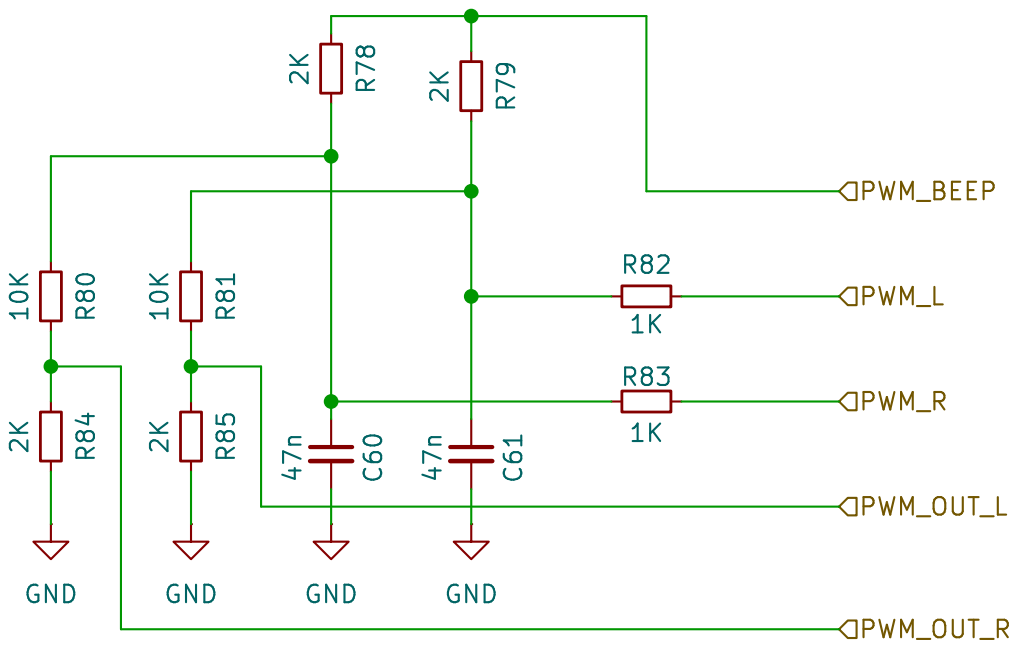
[picture p260: page 20]

https://github.com/xtremespb/frank R82

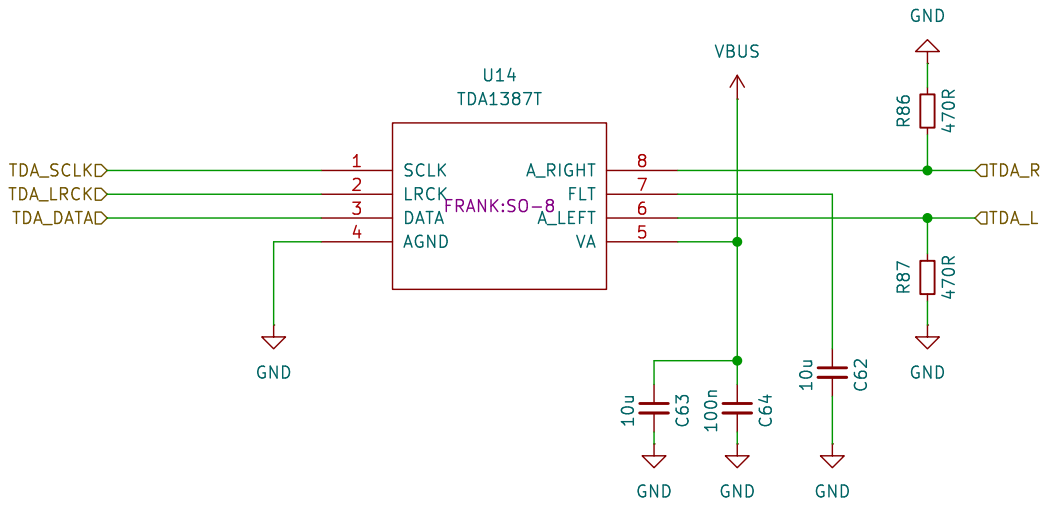
[picture p261: page 21]

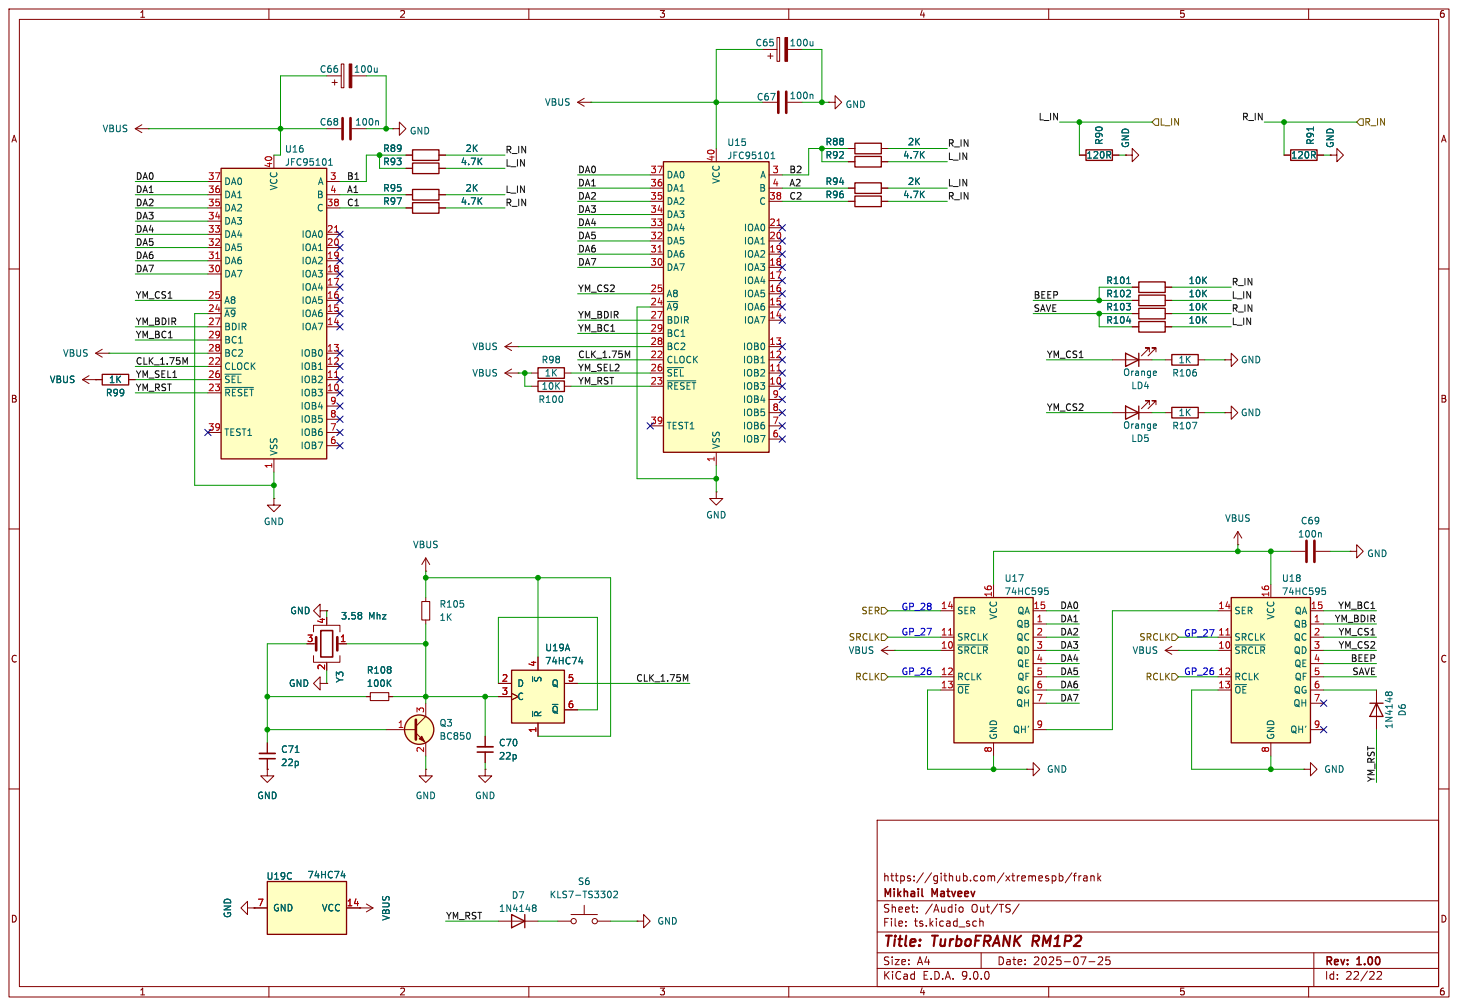
[picture p262: page 22]

https://github.com/xtremespb/frank
