rh1tech/frank-archive/turbofrank_m1p2/docs/1_01/turbofrank_m1p2.pdf

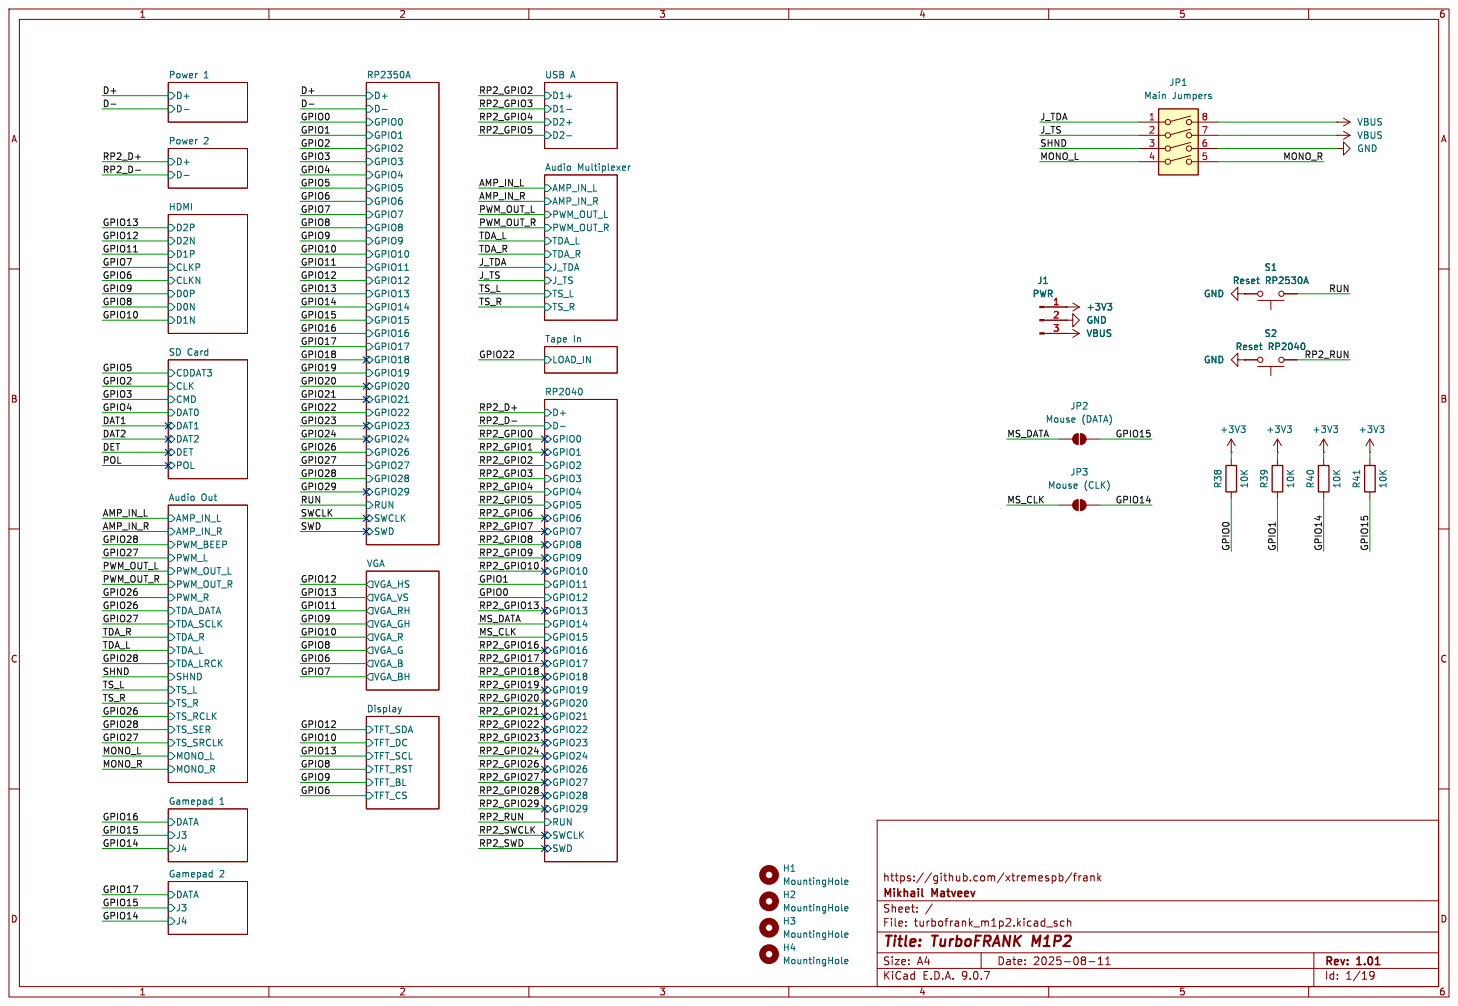
[picture p263: page 1]

DAT0 DAT1 DAT2 DET POL SD Card DATA

https://github.com/xtremespb/frank


https://github.com/xtremespb/frank GND

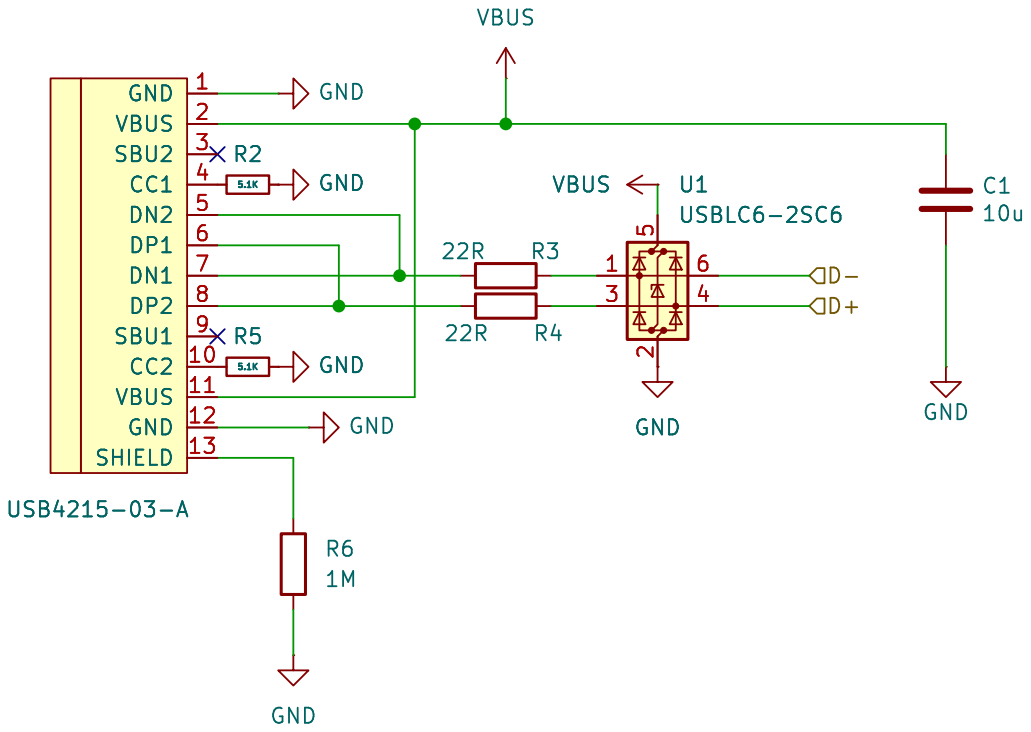
[picture p264: page 3]

https://github.com/xtremespb/frank


https://github.com/xtremespb/frank GND


TDARCLK
https://github.com/xtremespb/frank TDA_DATA
TDA_L TDA_LRCK

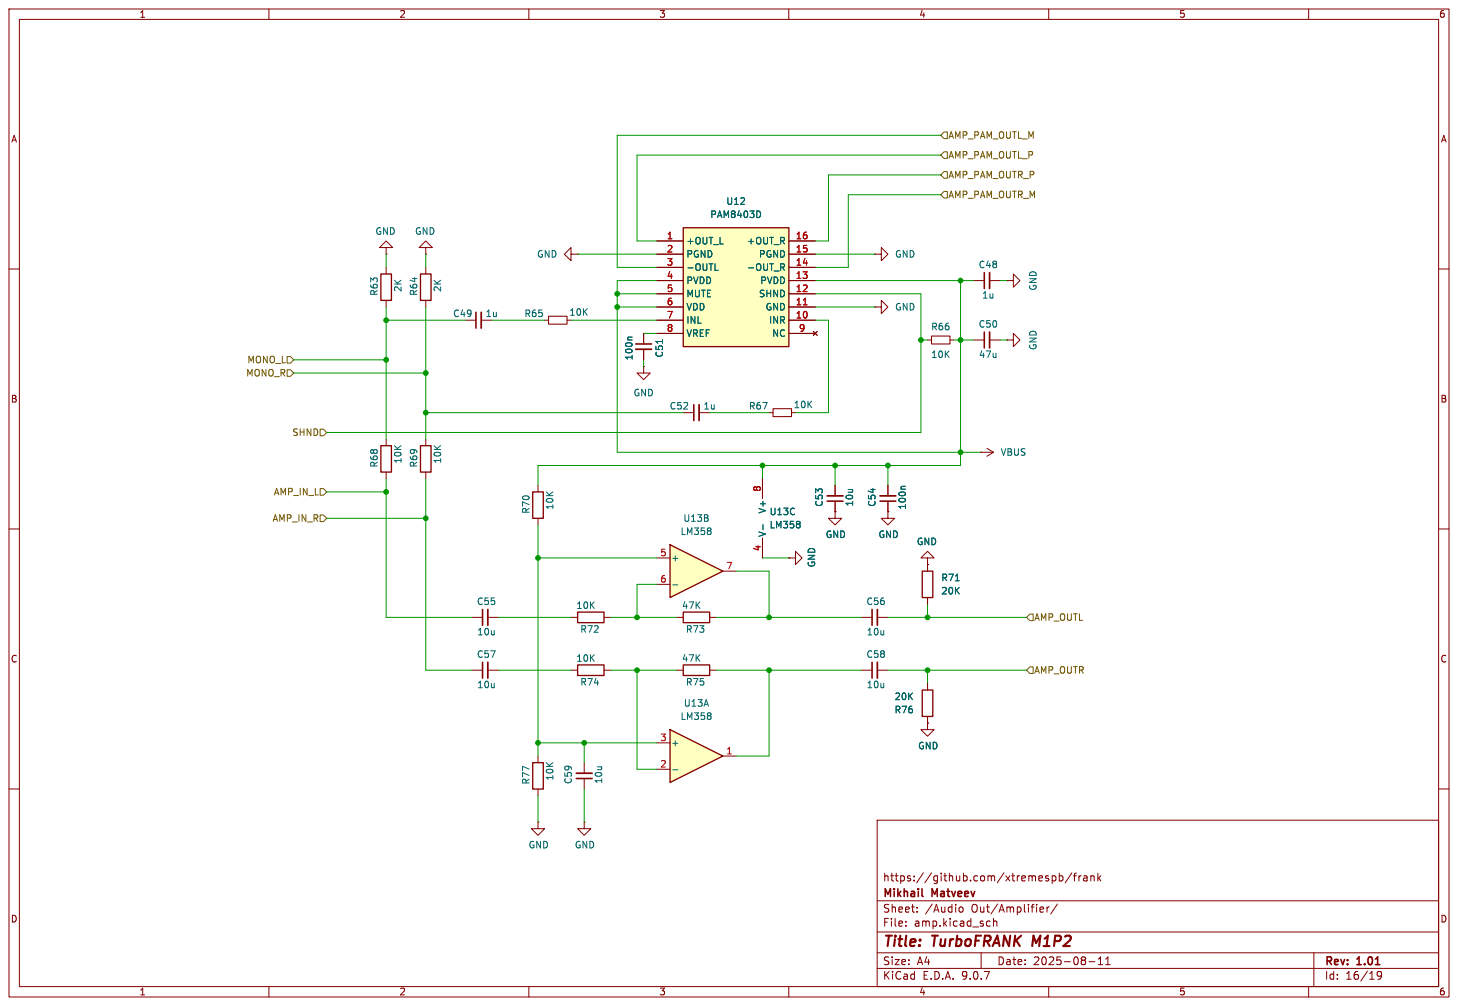
[picture p265: page 6]


https://github.com/xtremespb/frank R82


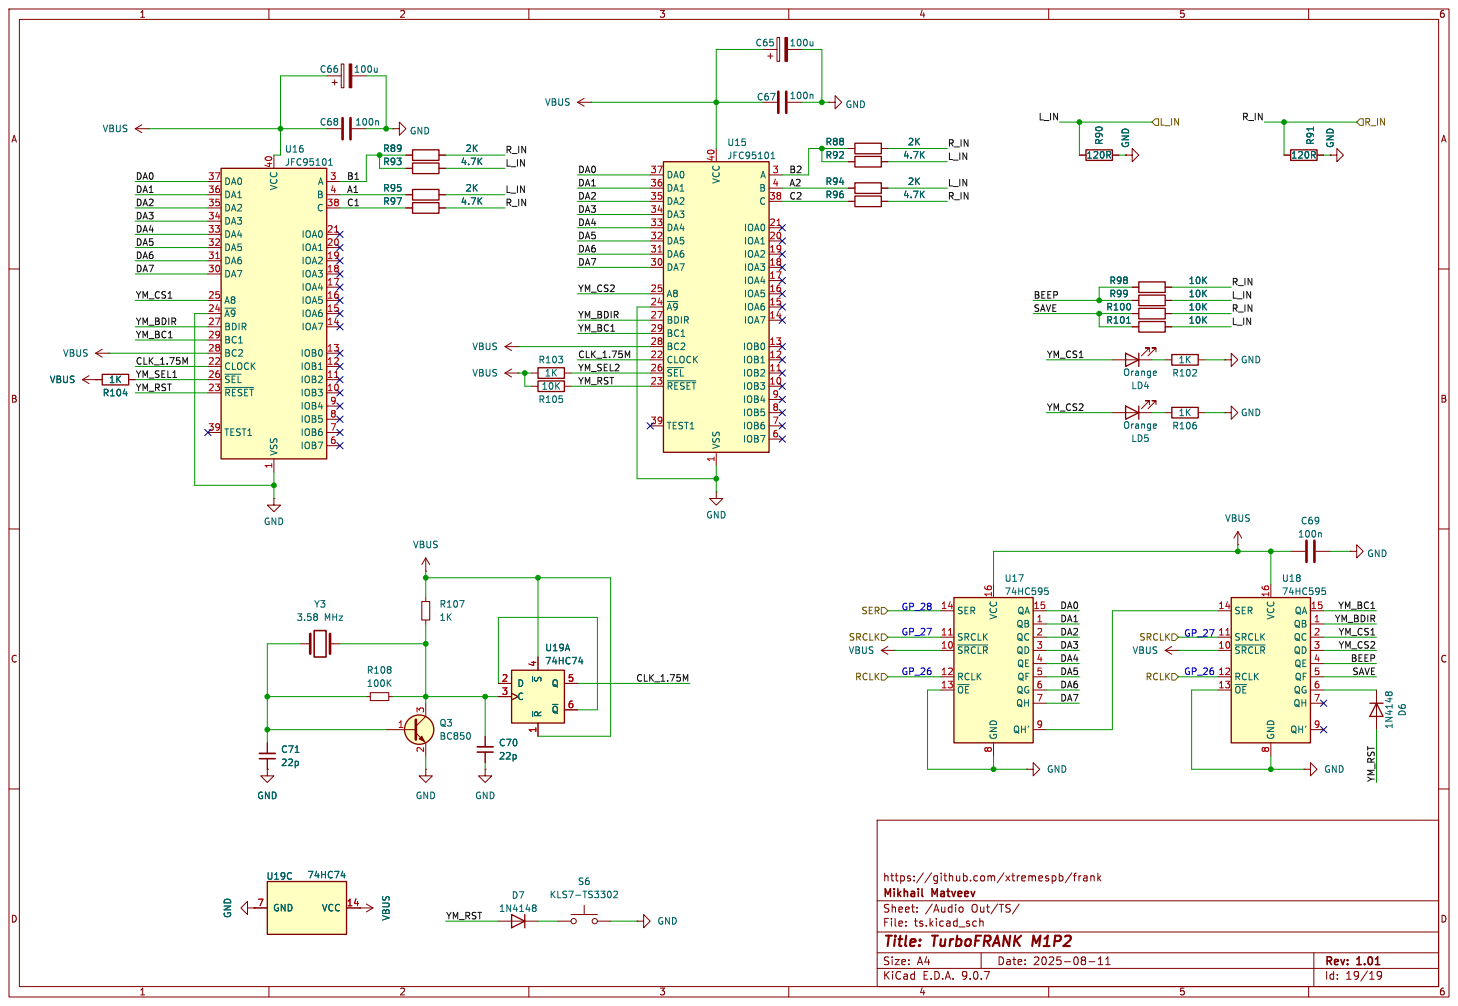
[picture p266: page 9]

https://github.com/xtremespb/frank


https://github.com/xtremespb/frank GND


https://github.com/xtremespb/frank GND



https://github.com/xtremespb/frank GND


https://github.com/xtremespb/frank


https://github.com/xtremespb/frank

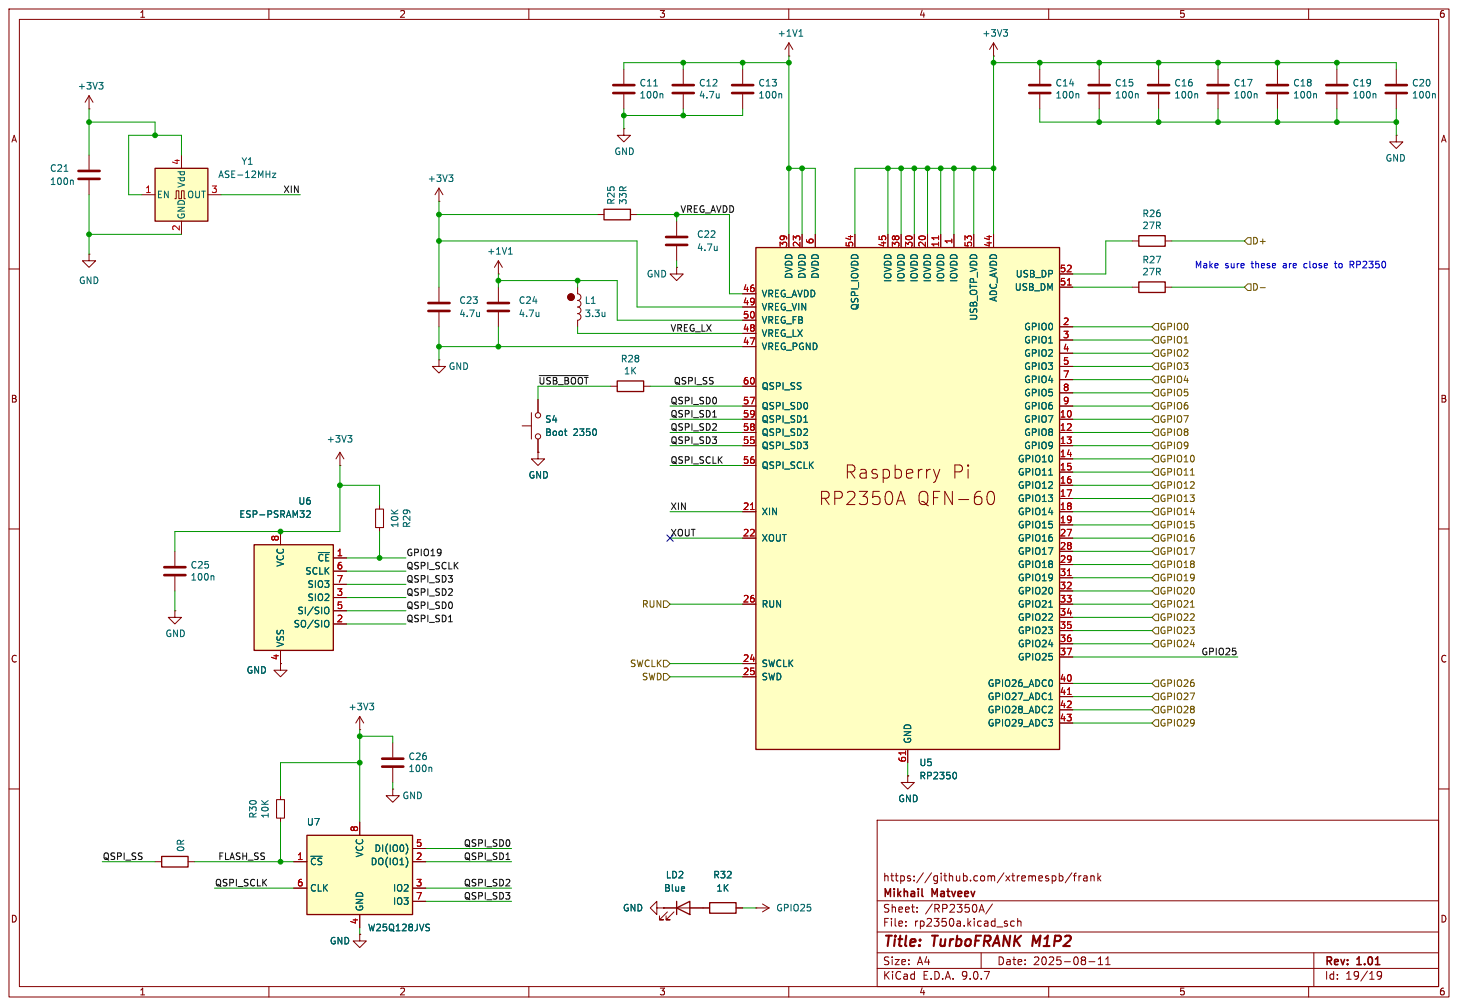
[picture p267: page 16]

https://github.com/xtremespb/frank R25 33R

6 QSPI_IOVDD 54 IOVDD 45 IOVDD 38 GND 61 IOVDD 30 IOVDD 20 IOVDD 11 IOVDD

Make sure these are close to RP2350 U6 ESP-PSRAM32 VCC

4 ~{CE}1 SCLK 6 SIO3 7 SIO2 3 SI/SIO 5 SO/SIO 2 U6 ESP-PSRAM32 GND GND

4 ~{CE}1 SCLK 6 SIO3 7 SIO2 3 SI/SIO 5 SO/SIO 2 GND

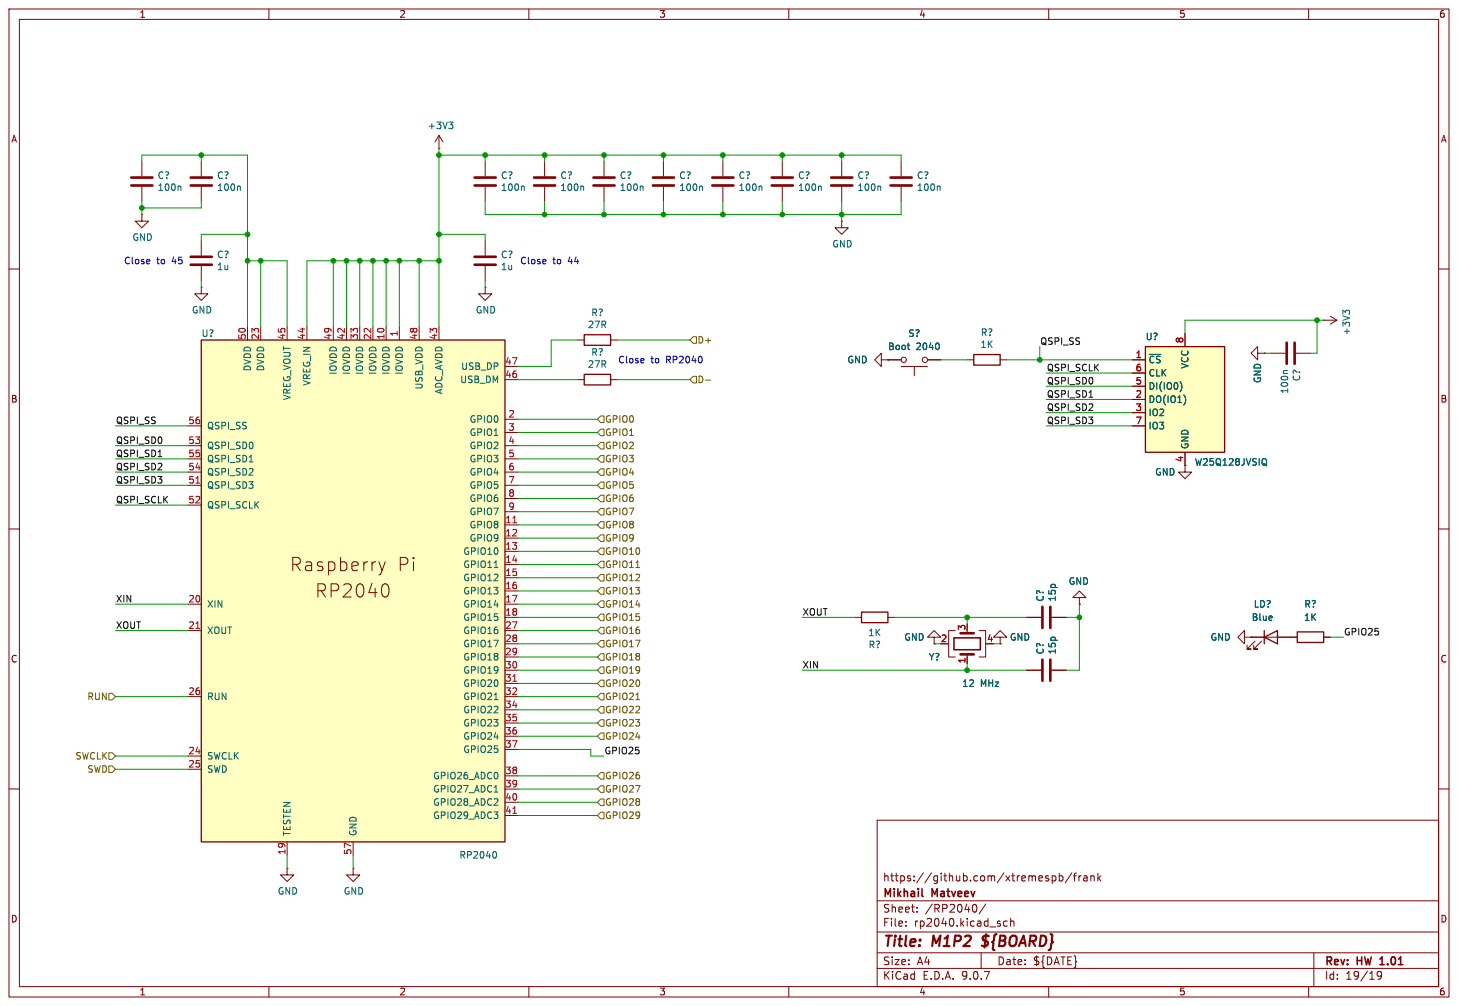
[picture p268: page 17]

https://github.com/xtremespb/frank GND



https://github.com/xtremespb/frank
