rh1tech/frank-archive/frank_m1/docs/2_06/frank_m1.pdf

https://github.com/xtremespb/frank


9 BST 8 SW 1 FB 4 U1 MP1584EN-LF-Z C5
100K GND

https://github.com/xtremespb/frank GND




https://github.com/xtremespb/frank


https://github.com/xtremespb/frank R33


https://github.com/xtremespb/frank



https://github.com/xtremespb/frank PWM_L PWM_R


https://github.com/xtremespb/frank R46




100n GND GND GND GND

https://github.com/xtremespb/frank


https://github.com/xtremespb/frank GND


https://github.com/xtremespb/frank GND





https://github.com/xtremespb/frank


4 ~{CE}1 SCLK 6 SIO3 7 SIO2 3 SI/SIO 5 SO/SIO 2 U11 ESP-PSRAM32 SISIO
100n GND

4 ~{CE}1 SCLK 6 SIO3 7 SIO2 3 SI/SIO 5 SO/SIO 2

https://github.com/xtremespb/frank
