rh1tech/frank-archive/frank_rm1p2/DOCS/1_01/frank_rm1p2.pdf

DAT0 DAT1 DAT2 DET POL SD Card D2P D2N

https://github.com/xtremespb/frank CDDAT3 CLK CMD


https://github.com/xtremespb/frank GND


https://github.com/xtremespb/frank



TDA
https://github.com/xtremespb/frank TDA_DATA
TDA_L TDA_LRCK


https://github.com/xtremespb/frank R49


https://github.com/xtremespb/frank R58



https://github.com/xtremespb/frank GND


https://github.com/xtremespb/frank GND



https://github.com/xtremespb/frank GND


+3V3 GND GND GND GND GND


https://github.com/xtremespb/frank


https://github.com/xtremespb/frank R28 33R

6 QSPI_IOVDD 54 IOVDD 45 IOVDD 38 GND 61 IOVDD 30 IOVDD 20 IOVDD 11 IOVDD

4 ~{CE}1 SCLK 6 SIO3 7 SIO2 3 SI/SIO 5 SO/SIO 2 U6 ESP-PSRAM32 GND GND

4 ~{CE}1 SCLK 6 SIO3 7 SIO2 3 SI/SIO 5 SO/SIO 2 GND


https://github.com/xtremespb/frank GND


https://github.com/xtremespb/frank
