rh1tech/frank-archive/microfrank_rm1p2u/DOCS/1_00/microfrank_rm1p2u.pdf

TFT Display USB C (Power) D2P D2N

https://github.com/xtremespb/frank


https://github.com/xtremespb/frank GND

1 VO 2 U1 NCP1117 3.3 GND GND GND GND 1 VBUS 2 SBU2 3 CC1 4 DN2 5 DP1 6 DN1 7 DP2 8 SBU1 9 CC2 10 VBUS 11 GND 12 SHIELD 13 USB4215-03-A



https://github.com/xtremespb/frank


https://github.com/xtremespb/frank GND


https://github.com/xtremespb/frank GND


+3V3 GND GND GND GND GND


https://github.com/xtremespb/frank R11 33R

6 QSPI_IOVDD 54 IOVDD 45 IOVDD 38 GND 61 IOVDD 30 IOVDD 20 IOVDD 11 IOVDD

4 ~{CE}1 SCLK 6 SIO3 7 SIO2 3 SI/SIO 5 SO/SIO 2 U5 ESP-PSRAM32 GND GND

4 ~{CE}1 SCLK 6 SIO3 7 SIO2 3 SI/SIO 5 SO/SIO 2 GND


https://github.com/xtremespb/frank


https://github.com/xtremespb/frank


https://github.com/xtremespb/frank R38
