rh1tech/frank-archive/minifrank_m1/DOCS/1_00/minifrank_m1.pdf

USB Hub CDDAT3 CLK CMD

H1 MountingHole H2 MountingHole H3 MountingHole H4 MountingHole

https://github.com/xtremespb/frank


https://github.com/xtremespb/frank



https://github.com/xtremespb/frank


https://github.com/xtremespb/frank GND


https://github.com/xtremespb/frank GND


https://github.com/xtremespb/frank R18 1K GND


https://github.com/xtremespb/frank



https://github.com/xtremespb/frank GND


+3V3 GND GND GND GND GND GND


4 ~{CE}1 SCLK 6 SIO3 7 SIO2 3 SI/SIO 5 SO/SIO 2 +3V3

8 VSS
https://github.com/xtremespb/frank VCC

4 ~{CE}1 SCLK 6 SIO3 7 SIO2 3 SI/SIO 5 SO/SIO 2 U6 ESP-PSRAM32 GND




https://github.com/xtremespb/frank R51
