rh1tech/frank-archive/minifrank_rm1/DOCS/2_05/minifrank_rm1.pdf

PSRAM
https://github.com/xtremespb/frank CE
SCLK
SISIO
SOSIO


https://github.com/xtremespb/frank


https://github.com/xtremespb/frank


https://github.com/xtremespb/frank GND



https://github.com/xtremespb/frank


https://github.com/xtremespb/frank GND


https://github.com/xtremespb/frank


4 ~{CE}1 SCLK 6 SIO3 7 SIO2 3 SI/SIO 5 SO/SIO 2 +3V3

4 ~{CE}1 SCLK 6 SIO3 7 SIO2 3 SI/SIO 5 SO/SIO 2 U4 ESP-PSRAM32 GND

https://github.com/xtremespb/frank


https://github.com/xtremespb/frank R22 1K GND


https://github.com/xtremespb/frank



https://github.com/xtremespb/frank


LM358 https://www.aliexpress.com/item/1005006785079218.html V+

https://www.aliexpress.com/item/1005006785079218.html +

https://github.com/xtremespb/frank


https://github.com/xtremespb/frank R49
