rh1tech/frank-archive/minifrank_rm1p2/DOCS/1_01/minifrank_rm1p2.pdf

DAT0 DAT1 DAT2 DET POL SD Card D2P D2N

Audio Multiplexer D+D- D1+ D1- D2+ D2- SUSB Multiplexer LOAD_IN

https://github.com/xtremespb/frank


https://github.com/xtremespb/frank GND


https://github.com/xtremespb/frank GND


https://github.com/xtremespb/frank GND


https://github.com/xtremespb/frank


https://github.com/xtremespb/frank GND


https://github.com/xtremespb/frank GND



https://github.com/xtremespb/frank



https://github.com/xtremespb/frank GND


+3V3 GND GND GND GND GND



4 ~{CE}1 SCLK 6 SIO3 7 SIO2 3 SI/SIO 5 SO/SIO 2 U7 ESP-PSRAM32 C23

6 QSPI_IOVDD 54 IOVDD 45 IOVDD 38 GND 61 IOVDD 30 IOVDD 20 IOVDD 11 IOVDD

4 ~{CE}1 SCLK 6 SIO3 7 SIO2 3 SI/SIO 5 SO/SIO 2 GND GND

https://github.com/xtremespb/frank



https://github.com/xtremespb/frank



https://github.com/xtremespb/frank R70
