rh1tech/frank-archive/minifrank_rm1p2h/DOCS/1_01/minifrank_rm1p2h.pdf

https://github.com/xtremespb/frank DATA


https://github.com/xtremespb/frank GND


https://github.com/xtremespb/frank GND GND


https://github.com/xtremespb/frank GND


TDA
https://github.com/xtremespb/frank TDA_DATA
TDA_L TDA_LRCK



https://github.com/xtremespb/frank R70



https://github.com/xtremespb/frank GND


https://github.com/xtremespb/frank GND



https://github.com/xtremespb/frank



+3V3 GND GND GND GND GND



6 QSPI_IOVDD 54 IOVDD 45 IOVDD 38 GND 61 IOVDD 30 IOVDD 20 IOVDD 11 IOVDD

Make sure these are close to RP2350 GND

4 ~{CE}1 SCLK 6 SIO3 7 SIO2 3 SI/SIO 5 SO/SIO 2 U7 ESP-PSRAM32 C26

4 ~{CE}1 SCLK 6 SIO3 7 SIO2 3 SI/SIO 5 SO/SIO 2 U8 W25Q128JVS

https://github.com/xtremespb/frank


5 DVDD33 11 DVDD33 24 DVDD33 36 DCCSCL 10 DDCSDA 9 HotPlugDetect 8 TMDS_CLK+ 15 TMDS_CLK- 14 TMDS-D0+ 18 TMDS_D0- 17 TMDS_D1+ 20 TMDS_D1- 19 TMDS_D2+ 23 TMDS_D2- 22 U9 AMS1117-3.3 VI 3 GND

5 DVDD33 11 DVDD33 24 DVDD33 36 DCCSCL 10 DDCSDA 9 HotPlugDetect 8 TMDS_CLK+ 15 TMDS_CLK- 14 TMDS-D0+ 18 TMDS_D0- 17 TMDS_D1+ 20 TMDS_D1- 19 TMDS_D2+ 23 TMDS_D2- 22 U11 MS9288A C51

6 GND 27 AVDD33 47 GND 40 AVDD33 12 GND 45 AVDD33 38 EP 49 AVDD33 43 DVDD33


https://github.com/xtremespb/frank
