rh1tech/frank-archive/tinyfrank_rm1p1/DOCS/1_00/tinyfrank_rm1p1.pdf

https://github.com/xtremespb/frank


https://github.com/xtremespb/frank



https://github.com/xtremespb/frank C5 10u GND


4 ~{CE}1 SCLK 6 SIO3 7 SIO2 3 SI/SIO 5 SO/SIO 2 +3V3

4 ~{CE}1 SCLK 6 SIO3 7 SIO2 3 SI/SIO 5 SO/SIO 2 U2 ESP-PSRAM32 GND

https://github.com/xtremespb/frank


https://github.com/xtremespb/frank


https://github.com/xtremespb/frank GND


https://github.com/xtremespb/frank GND
