rh1tech/frank-archive/frank_m2/docs/1/03/HR3FQ.pdf

ZERO_VBUS
DAT0 CLK DAT2 DET CDDAT3 POL DAT1 Micro SD

https://github.com/xtremespb/frank


1 VO 2 U1 GND NCP1117 3.3 1 VBUS 2 SBU2 3 CC1 4 DN2 5 DP1 6 DN1 7 DP2 8 SBU1 9 CC2 10 VBUS 11 GND 12 SHIELD 13 USB4215 GND

https://github.com/xtremespb/frank


https://github.com/xtremespb/frank GND



https://github.com/xtremespb/frank


https://github.com/xtremespb/frank



https://github.com/xtremespb/frank


https://github.com/xtremespb/frank SR
100R GND


https://github.com/xtremespb/frank


https://github.com/xtremespb/frank



https://github.com/xtremespb/frank
