rh1tech/frank-archive/frank_m2/docs/1/04/HR3FQ.pdf

ZERO_VBUS
DAT0 CLK DAT2 DET CDDAT3 POL DAT1 Micro SD

https://github.com/xtremespb/frank



https://github.com/xtremespb/frank GND


https://github.com/xtremespb/frank R52


https://github.com/xtremespb/frank


https://github.com/xtremespb/frank GND


https://github.com/xtremespb/frank GND




https://github.com/xtremespb/frank


https://github.com/xtremespb/frank GND


https://github.com/xtremespb/frank GND


https://github.com/xtremespb/frank GND



1 VO 2 U1 NCP1117 3.3 GND GND GND GND GND

https://github.com/xtremespb/frank
