rh1tech/frank-archive/hdmi2vga/docs/2_04/hdmi2vga.pdf

https://github.com/xtremespb/frank 61728394
