rh1tech/frank-archive/frank_m1/docs/archive/1_13/assembly.pdf

R2 SW1 C6 | C9 1 | 2 | 3 | 4 | 5 | 6 1 | 2 | 3 | 4 | 5 | 6 ABCD | ABCD Date: 2025-02-19 KiCad E.D.A. 8.0.7 Size: A4 | Rev: 1.13

# R46 AV8.4-5 D-SUB 9 Male GP1


MOUSEDATA RTS CTS GP2 MicroSD DC SC PWMR Gamepad1 RXTDAR GND PWML TapeIn
R58 D-SUB 9 Male GP2

https://github.com/xtremespb/frank Black And White TOP - Page 1/2

File: CMZJ2.kicad_pcb Sheet: Black And White TOP Mikhail Matveev

JP2 1 | 2 | 3 | 4 | 5 | 6

A

HW REV1.13 RH1.DEV; D Date: 2025-02-19 KiCad; E.D.A. 8.0.7 Size: A4; Rev: 1.13; File: CMZJ2.kicad_pcb Sheet: Black; And; White; BOT Mikhail; Matveev; https://github.com/xtremespb/frank Black; BOT -; Page 2/2; Jumper (Solder)

Id: 1/1 Title: FRANK M1
