rh1tech/frank-archive/frank_m1/docs/archive/1_16/assembly.pdf

J1 | R49 | R⁵¹ | C⁸ R52 U⁶ | R⁴² | R¹⁹ 1 | 2 | 3 | 4 | 5 | 6 1 | 2 | 3 | 4 | 5 | 6 ABCD | ABCD Date: 2025-03-26 KiCad E.D.A. 9.0.0 Size: A4 | Rev: 1.16

R3 100R


https://github.com/xtremespb/frank Black And White TOP - Page 1/4

File: CMZJ2.kicad_pcb Sheet: Black And White TOP Mikhail Matveev

1 | 2 | 3 | 4 | 5 | 6

A

D Date: 2025-03-26 KiCad; E.D.A. 9.0.0 Size: A4; Rev: 1.16; File: CMZJ2.kicad_pcb Sheet: Black; And; White; BOT Mikhail; Matveev; https://github.com/xtremespb/frank Black; BOT -; Page 2/4; Jumper; (Solder)

Id: /1 Title: FRANK M1

1 | 2 | 3 | 4 | 5 | 6

A

D Date: 2025-03-26 KiCad; E.D.A. 9.0.0 Size: A4; Rev: 1.16; File: CMZJ2.kicad_pcb Sheet: Colored; BOT Mikhail; Matveev; https://github.com/xtremespb/frank Colored; BOT -; Page 3/4; Jumper; (Solder)

Id: /1 Title: FRANK M1

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

R3 100R


https://github.com/xtremespb/frank Colored TOP - Page 4/4

File: CMZJ2.kicad_pcb Sheet: Colored TOP Mikhail Matveev
