rh1tech/frank-archive/frank_m1/docs/archive/1_17/assembly.pdf

# VGA RTS TDR


https://github.com/xtremespb/frank Black And White TOP - Page 1/4

File: CMZJ2.kicad_pcb Sheet: Black And White TOP Mikhail Matveev

D Date: 2025-04-09 KiCad; E.D.A. 9.0.0 Size: A4; Rev: 1.17; File: CMZJ2.kicad_pcb Sheet: Black; And; White; BOT Mikhail; Matveev; https://github.com/xtremespb/frank Black; BOT -; Page 2/4

Id: /1 Title: FRANK M1

# VGA RTS TDR


D Date: 2025-04-09 KiCad; E.D.A. 9.0.0 Size: A4; Rev: 1.17; File: CMZJ2.kicad_pcb Sheet: Colored; BOT Mikhail; Matveev; https://github.com/xtremespb/frank Colored; BOT -; Page 4/4; Jumper; (Solder)

Id: /1 Title: FRANK M1
