rh1tech/frank-archive/frank_m1/docs/archive/1_13/CMZJ2.pdf

Audio Out D2+ D1- D1+ D2- USB Stacked

GPIO29 GPIO28 GPIO23 GPIO22 GPIO26 GPIO21 GPIO27 GPIO20 RUN GPIO19 GPIO16 GPIO17 GPIO18 GPIO14 GPIO13 GPIO12 GPIO11 GPIO15 GPIO2 GPIO1 GPIO4 GPIO0 GPIO3 GPIO5 GPIO8 GPIO10 GPIO6 GPIO7 GPIO9 PicoRUN
+3V3 123 CON1 Pin Header 1x03 VBUS GND 1

DAT0 CLK DAT2 DET CDDAT3 POL DAT1 Micro SD

https://github.com/xtremespb/frank


1 VO 2 VI 3 U1 NCP1117 3.3 D- D+ D+D+D- D- The LED indicates +3V power availability.

https://github.com/xtremespb/frank


https://github.com/xtremespb/frank


https://github.com/xtremespb/frank


https://github.com/xtremespb/frank


https://github.com/xtremespb/frank


https://github.com/xtremespb/frank



if you are going to use it. GND

4 SI/SIO 5 SCLK 6 SIO3 7 VCC

https://github.com/xtremespb/frank


https://github.com/xtremespb/frank


https://github.com/xtremespb/frank


GND GND

https://github.com/xtremespb/frank


https://github.com/xtremespb/frank


https://github.com/xtremespb/frank


https://github.com/xtremespb/frank


https://github.com/xtremespb/frank


https://github.com/xtremespb/frank


https://github.com/xtremespb/frank R59 1K
