rh1tech/frank-archive/frank_m1/docs/archive/1_17/CMZJ2.pdf

DAT0 CLK DAT2 DET CDDAT3 POL DAT1 Micro SD

J2 Pin Header 1x03 VBUS H1 Hole 2.7mm

https://github.com/xtremespb/frank
