rh1tech/frank-archive/frank_m1/docs/archive/FRANK2/frank2.pdf

https://github.com/xtremespb/frank2


https://github.com/xtremespb/frank2



https://github.com/xtremespb/frank2


https://github.com/xtremespb/frank2


https://github.com/xtremespb/frank2


https://github.com/xtremespb/frank2


https://github.com/xtremespb/frank2 R34 1K


https://github.com/xtremespb/frank2


https://github.com/xtremespb/frank2


4 SI/SIO 5 SCLK 6 SIO3 7 VCC

https://github.com/xtremespb/frank2


https://github.com/xtremespb/frank2


https://github.com/xtremespb/frank2


https://github.com/xtremespb/frank2
