rh1tech/frank-archive/minifrank_rm1/minifrank_rm1.kicad_pcb

## KiCad design minifrank_rm1/minifrank_rm1.kicad_pcb (2026-05-06)

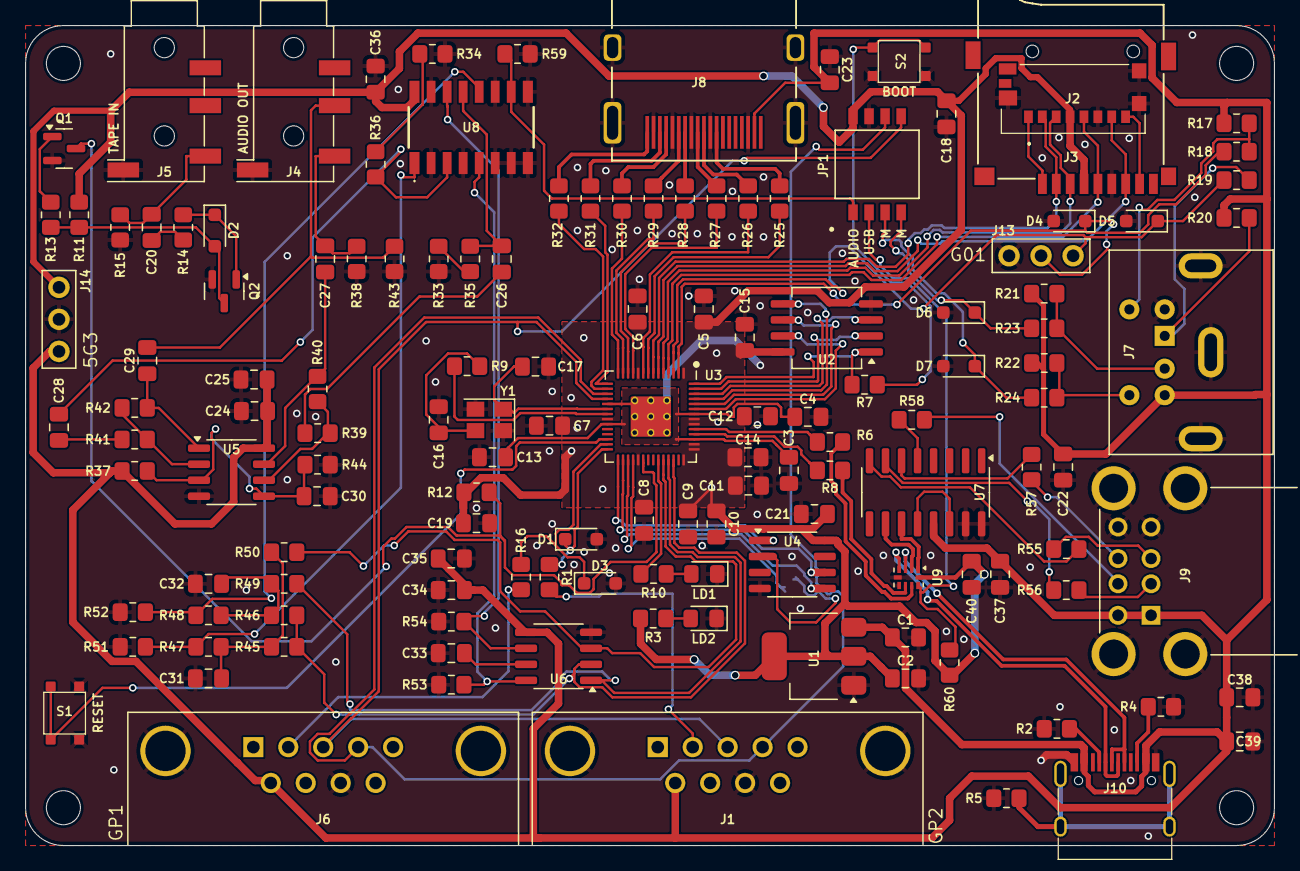
[picture p301: board minifrank_rm1.kicad_pcb from above]

Board: 2 copper layers, 99.0 x 65.0 mm, 141 parts (1 on the bottom side), 110 nets.

Parts:
C1, C2, C24, C26, C27, C28, C29, C30, C33, C34, C38, C39: 10u; Capacitor (0805)
C3, C4, C5, C6, C7, C8, C9, C10, C11, C12, C15, C18, C19, C20, C21, C22, C23, C25, C35, C36, C40: 100n; Capacitor (0805)
C13, C14: 1u; Capacitor (0805)
C16, C17: 15p; Capacitor (0805)
C31, C32: 47n; Capacitor (0805)
C37: 4.7u; Capacitor (0805)
D1, D3, D4, D5, D6, D7: 3V3; Diode (SOD-323)
D2: 1N4148; Diode (SOD-323)
H1, H2, H3, H4: MountingHole; Mounting Hole (2.7mm)
J1, J6: D-SUB 9 Male; D-SUB (9 pin, male, top mount)
J2: 0475710001; MicroSD (SMD, short)
J3: 104031-0811; MicroSD (SMD, long)
J4, J5: PJ-320D; Jack (3.5mm, PJ-320D)
J7: MDC-036; MiniDIN (6 Pin, female)
J8: DC3RX19JA2; HDMI (female)
J9: SS-52100-004; USB Type A (stacked)
J10: USB4215-03-A; USB Type C
J13: UART; Pin Header (1x03)
J14: PWR; Pin Header (1x03)
JP1: Main Jumpers; SW_DS05-127-2-04BK-SMT-TR
JP2: Jumper (Solder); Jumper (solder)
LD1: Blue; LED (0805)
LD2: Green; LED (0805)
Q1, Q2: BC850; SOT-23
R1, R3, R7, R9, R10, R12, R16, R17, R20, R21, R22, R49, R50: 1K; Resistor (0805)
R2, R4: 5.1K; Resistor (0805)
R5: 1M; Resistor (0805)
R6, R8: 27R; Resistor (0805)
R11, R13, R14, R35, R36, R37, R39, R41, R44, R47, R48, R59, R60: 10K; Resistor (0805)
R15, R18, R19, R23, R24: 100R; Resistor (0805)
R25, R26, R27, R28, R29, R30, R31, R32: 270R; Resistor (0805)
R33, R34, R45, R46, R51, R52: 2K; Resistor (0805)
R38, R43: 20K; Resistor (0805)
R40, R42: 47K; Resistor (0805)
R53, R54: 470R; Resistor (0805)
R55, R56, R57, R58: 22R; Resistor (0805)
S1: Reset; Button (SMD, 3x3mm, 1-1)
S2: Boot; Button (SMD, 3x3mm, 1-1)
U1: NCP1117 3.3; SOT-223
U2: W25Q128JVSIQ; SOIC-8
U3: RP2040; QFN 56
U4: ESP-PSRAM32; SO-8
U5: LM358; SO-8
U6: TDA1387T; SO-8
U7: MW7211A; SOP-16
U8: 74HC4052D; 74HC4052D653
U9: TS3USB221RSER; UQFN-10
Y1: 12 MHz; Crystal (3225)

Connections:
+3V3: C2.1, C5.1, C6.1, C7.1, C8.1, C9.1, C10.1, C11.1, C12.1, C14.1, C15.1, C18.2, C19.1, C21.1, C36.2, C40.2, J2.P4 (VDD), J3.4 (VDD), J14.1, JP1.8, R3.2, R11.1, R12.1, R60.1, U1.2 (VO), U2.8 (VCC), U3.1 (IOVDD), U3.10 (IOVDD), U3.22 (IOVDD), U3.33 (IOVDD), U3.42 (IOVDD), U3.43 (ADC_AVDD), U3.44 (VREG_IN), U3.48 (USB_VDD), U3.49 (IOVDD), U4.8 (VCC), U8.16 (VCC), U9.10 (VCC)
/AMP_IN_L: C26.1, R35.1, U8.13 (1Z)
/AMP_IN_R: C28.1, R36.1, U8.3 (2Z)
/AUDIOSW: JP1.1, R59.2, U8.10 (S0)
/Audio Out/AMP_OUTL: C27.2, J4.T, R38.2
/Audio Out/AMP_OUTR: C29.2, J4.R, R43.2
/D+: R6.1, U9.8 (D+)
/D-: R8.1, U9.7 (D-)
/GPIO0: D4.1 (K), J13.2, R18.2, U3.2 (GPIO0)
/GPIO1: D5.1 (K), J13.3, R19.2, U3.3 (GPIO1)
/GPIO2: J2.P5 (CLK), J3.5 (CLK), U3.4 (GPIO2)
/GPIO3: J2.P3 (CMD), J3.3 (CMD), U3.5 (GPIO3)
/GPIO4: J2.P7 (DAT0), J3.7 (DAT0), U3.6 (GPIO4)
/GPIO5: J2.P2 (CD/DAT3), J3.2 (DAT3/CD), U3.7 (GPIO5)
/GPIO6: R25.2, U3.8 (GPIO6)
/GPIO7: R26.2, U3.9 (GPIO7)
/GPIO8: R27.2, U3.11 (GPIO8)
/GPIO9: R28.2, U3.12 (GPIO9)
/GPIO10: R29.2, U3.13 (GPIO10)
/GPIO11: R30.2, U3.14 (GPIO11)
/GPIO12: R31.2, U3.15 (GPIO12)
/GPIO13: R32.2, U3.16 (GPIO13)
/GPIO14: J1.4, J6.4, JP1.6, U3.17 (GPIO14)
/GPIO15: J1.3, J6.3, JP1.5, U3.18 (GPIO15)
/GPIO16: D3.1 (K), R16.1, U3.27 (GPIO16)
/GPIO17: D1.1 (K), R1.1, U3.28 (GPIO17)
/GPIO18: U3.29 (GPIO18), U4.1 (~CE)
/GPIO19: U3.30 (GPIO19), U4.6 (SCLK)
/GPIO20: U3.31 (GPIO20), U4.5 (SI/SIO)
/GPIO21: JP2.2 (B), U3.32 (GPIO21)
/GPIO22: Q1.3 (C), R12.2, U3.34 (GPIO22)
/GPIO26: R50.2, U3.38 (GPIO26_ADC0), U6.3 (DATA)
/GPIO27: R49.2, U3.39 (GPIO27_ADC1), U6.1 (SCLK)
/GPIO28: R45.1, R46.1, U3.40 (GPIO28_ADC2), U6.2 (LRCK)
/HUB_D+: U7.11 (DPU), U9.1 (1D+)
/HUB_D-: U7.10 (DMU), U9.2 (1D-)
/KB_CLK: J7.5, R17.2, R18.1
/KB_DATA: J7.1, R19.1, R20.2
/MS_CLK: J7.6, R22.2, R24.1
/MS_CLK_3V: D7.1 (K), JP1.3, R24.2
/MS_DATA: J7.2, R21.2, R23.1
/MS_DATA_3V: D6.1 (K), JP1.4, R23.2
/PWM_OUT_L: R48.2, R52.1, U8.12 (1Y0)
/PWM_OUT_R: R47.2, R51.1, U8.1 (2Y0)
/RP2040/GPIO25: R10.2, U3.37 (GPIO25)
/RP2040/QSPI_SCLK: U2.6 (CLK), U3.52 (QSPI_SCLK)
/RP2040/QSPI_SD0: U2.5 (DI(IO0)), U3.53 (QSPI_SD0)
/RP2040/QSPI_SD1: U2.2 (DO(IO1)), U3.55 (QSPI_SD1)
/RP2040/QSPI_SD2: U2.3 (IO2), U3.54 (QSPI_SD2)
/RP2040/QSPI_SD3: U2.7 (IO3), U3.51 (QSPI_SD3)
/RP2040/QSPI_SS: R7.1, U2.1 (~CS), U3.56 (QSPI_SS)
/RP2040/XIN: C17.1, U3.20 (XIN), Y1.1
/RP2040/XOUT: R9.1, U3.21 (XOUT)
/RUN: S1.1, U3.26 (RUN)
/SD Card/DAT1: J2.P8 (DAT1), J3.8 (DAT1)
/SD Card/DAT2: J2.P1 (DAT2), J3.1 (DAT2)
/TDA_L: R54.2, U6.6 (A_LEFT), U8.14 (1Y1)
/TDA_R: R53.1, U6.8 (A_RIGHT), U8.5 (2Y1)
/USBMPXSW: JP1.2, R60.2, U9.9 (S)
/USB_D1+: R55.1, U7.8 (DP3)
/USB_D1-: R56.1, U7.7 (DM3)
/USB_D2+: R57.1, U7.6 (DP2)
/USB_D2-: R58.1, U7.5 (DM2)
/UTC_D+: J10.6 (DP1), J10.8 (DP2), U9.3 (2D+)
/UTC_D-: J10.5 (DN2), J10.7 (DN1), U9.4 (2D-)
GND: C1.2, C2.2, C3.2, C4.2, C5.2, C6.2, C7.2, C8.2, C9.2, C10.2, C11.2, C12.2, C13.2, C14.2, C15.2, C16.2, C17.2, C18.1, C19.2, C21.2, C22.2, C23.2, C24.1, C25.1, C30.1, C31.2, C32.2, C33.2, C34.2, C35.2, C36.1, C37.2, C38.2, C39.2, C40.1, D1.2 (A), D3.2 (A), D4.2 (A), D5.2 (A), D6.2 (A), D7.2 (A), J1.8, J2.G1 (GND_1), J2.G2 (GND_2), J2.G3 (GND_3), J2.P6 (VSS), J3.6 (VSS), J4.S, J5.S, J6.8, J7.3, J8.2 (G_D2), J8.5 (G_D1), J8.8 (G_D0), J8.11 (G_CLK), J8.17 (G_DDC/CEC), J8.20 (SHIELD1), J8.21 (SHIELD2), J8.22 (SHIELD3), J8.23 (SHIELD4), J9.4 (GND1), J9.8 (GND2), J9.9 (Shield), J10.1 (GND), J10.12 (GND), J13.1, J14.2, JP1.7, LD1.1 (K), LD2.1 (K), Q1.2 (E), Q2.2 (E), R2.1, R4.1, R5.2, R15.2, R33.2, R34.2, R38.1, R43.1, R44.1, R51.2, R52.2, R53.2, R54.1, R59.1, S1.2, S2.2, U1.1 (GND), U2.4 (GND), U3.19 (TESTEN), U3.57 (GND), U4.4 (VSS), U5.4 (V-), U6.4 (AGND), U7.15 (GND), U7.16 (GND), U8.2 (2Y2), U8.4 (2Y3), U8.6 (~E), U8.7 (VEE), U8.8 (GND), U8.9 (S1), U8.11 (1Y3), U8.15 (1Y2), U9.5 (GND), U9.6 (~OE), Y1.2, Y1.4
unnamed: C16.1, R9.2, Y1.3
unnamed: C20.1, J5.T, R15.1
unnamed: C20.2, R14.1
unnamed: C26.2, R39.2
unnamed: C27.1, R40.1, U5.7
unnamed: C28.2, R41.2
unnamed: C29.1, R42.1, U5.1
unnamed: C31.1, R45.2, R47.1, R50.1
unnamed: C32.1, R46.2, R48.1, R49.1
unnamed: D2.2 (A), Q2.3 (C), R11.2, R13.1
unnamed: D2.1 (K), Q2.1 (B), R14.2
unnamed: J1.2, R1.2
unnamed: J6.2, R16.2
unnamed: J8.12 (CLKN), R25.1
unnamed: J8.10 (CLKP), R26.1
unnamed: J8.9 (D0N), R27.1
unnamed: J8.7 (D0P), R28.1
unnamed: J8.6 (D1N), R29.1
unnamed: J8.4 (D1P), R30.1
unnamed: J8.3 (D2N), R31.1
unnamed: J8.1 (D2P), R32.1
unnamed: J9.3 (D1+), R55.2
unnamed: J9.2 (D1-), R56.2
unnamed: J9.7 (D2+), R57.2
unnamed: J9.6 (D2-), R58.2
unnamed: J10.4 (CC1), R2.2
unnamed: J10.10 (CC2), R4.2
unnamed: J10.13 (SHIELD), R5.1
unnamed: JP2.1 (A), U4.2 (SO/SIO)
unnamed: LD1.2 (A), R10.1
unnamed: LD2.2 (A), R3.1
unnamed: Q1.1 (B), R13.2
unnamed: R7.2, S2.1
unnamed: R33.1, R35.2
unnamed: R34.1, R36.2
unnamed: R8.2, U3.46 (USB_DM)
unnamed: R6.2, U3.47 (USB_DP)
unnamed: C3.1, C4.1, C13.1, U3.23 (DVDD), U3.45 (VREG_VOUT), U3.50 (DVDD)
unnamed: C30.2, R37.1, R44.2, U5.3 (+), U5.5 (+)
unnamed: R41.1, R42.2, U5.2 (-)
unnamed: R39.1, R40.2, U5.6 (-)
unnamed: C33.1, U6.7 (FLT)
unnamed: U7.12 (VD33), U7.14 (VD3)
VBUS: C1.1, C22.1, C23.1, C24.2, C25.2, C34.1, C35.1, C37.1, C38.1, C39.1, J1.6, J6.6, J7.4, J8.18 (+5V), J9.1 (VBUS1), J9.5 (VBUS2), J10.2 (VBUS), J10.11 (VBUS), J14.3, R17.1, R20.1, R21.1, R22.1, R37.2, U1.3 (VI), U5.8 (V+), U6.5 (VA), U7.13 (VDD5)
